ukama/ukama-nodes/products/units/amplifier/artworks/compliance_amplifier_node.pdf

# Scale 1: 1 Page 1/1:CMF Details

Antenna : Label F | Page size:A4 | Version:1.0

# 27-May-2021

# Date

SERIAL : 32019-08-12-2023-0225016

MAC ID : 07-45-B0-DC-06-40

## Model : FEMA-GSM900M-2W-GPS-V1.0-xx

Ukama Inc.

This device complies with part 15 of the FCC rules. Operation is subject to the following two conditions
1) This device may not cause harmful interference and 2) this device must accept any interference received, including that may cause undesired operation

### Made with in California

# logo

SERIAL : 32019-08-12-2023-0225016

MAC ID : 07-45-B0-DC-06-40

## Model : FEMA-GSM900M-2W-GPS-V1.0-xx

Ukama Inc.

This device complies with part 15 of the FCC rules. Operation is subject to the following two conditions
1) This device may not cause harmful interference and 2) this device must accept any interference received, including that may cause undesired operation

### Made with in California

# logo

34.43

18.03

# Background colour - White

# Text colour - Pantone Black C

# Colour - XXXX

# Graphics
