ukama/ukama-nodes/products/nodes/tower/artworks/compliance_tower_node.pdf

# Scale 1: 1 Page 1/1:CMF Details

Antenna : Label TN | Page size:A4 | Version:1.0

# 27-May-2021

# Date

# Background colour - White

# Text colour - Pantone Black C

# Colour - XXXX

80.00

11.00

This device complies with part 15 of the FCC rules. Operation is subject to the following two conditions 1) This device may not cause harmful interference and 2) this device must accept any interference received, including that may cause undesired operation

## Model : TowerNode-V1.0-xx

Ukama Inc.

### Made with in California

# logo

SERIAL : 12019-08-12-2023-0335007 | MAC ID : 07-45-B0-DC-06-41

This device complies with part 15 of the FCC rules. Operation is subject to the following two conditions 1) This device may not cause harmful interference and 2) this device must accept any interference received, including that may cause undesired operation

## Model : TowerNode-V1.0-xx

Ukama Inc.

### Made with in California

# logo

SERIAL : 12019-08-12-2023-0335007 | MAC ID : 07-45-B0-DC-06-41

# Graphics
