ukama/ukama-nodes/electronics/ctrl/bom/bom_controller.xlsx

Revised: Tuesday, September 01, 2020
FEMA-MP BOARD_V1_REV-B
Bill Of Materials September 18,2020 14:52:14
Item | Quantity | Reference | Part Number | Description | Manufacturer
1 | 2 | A9,A10 | SNT-100-BK-T-H | Open Top, Grip, Female Sockets, Shunts/Jumpers 2 POS | Samtec
2 | 1 | BT1 | CR-1220/HFN | BATTERY LITHIUM COIN 3V PC PINS | Panasonic - BSG
3 | 1 | CN1 | 112A-TAAR-R03 | MICROSD Connector | Attend Technology Inc
4 | 2 | C1,C2 | 101X43W474MV4E | CAP CER 0.47UF 100V X7R 1812 | Johanson Dielectrics Inc
6 | 17 | C4,C5,C15,C16,C17,C19,C39,C40,C44,C48,C49,C51,C53,C54,C55,C56,C3 | CC0402KRX7R8BB104 | CAP CER 0.1UF 25V 10% X7R 0402 | Yageo
7 | 2 | C6,C23 | NFM18PC225B1A3D | 2.2µF Feed Through Capacitor 10V 4A 10 mOhm 0603 (1608 Metric), 3 PC Pad | Murata Electronics North America
8 | 3 | C7,C22,C24 | 202R18W102KV4E | CAP CER 1000PF 2KV X7R 1206 | Johanson Dielectrics Inc.
9 | 1 | C8 | GRM155R72A102KA01D | CAP CER 1000PF 100V X7R 0402 | Murata Electronics
10 | 2 | C9,C31 | CL21B104KCFNNNE | CAP CER 0.1UF 100V X7R 0805 | Samsung Electro-Mechanics
11 | 2 | C10,C41 | CC1210KKX7R0BB105 | CAP CER 1UF 100V X7R 1210 | Yageo
12 | 1 | C11 | C0603C470K5RACAUTO | CAP CER 47PF 50V X7R 0603 | KEMET
13 | 1 | C12 | CC0603JRNPO9BN100 | CAP CER 10PF 50V C0G/NPO 0603 | Yageo
14 | 1 | C13 | C1206C224K4RAC7800 | CAP CER 0.22UF 16V X7R 1206 | KEMET
15 | 1 | C14 | UWX1C101MCL1GB | CAP ALUM 100UF 20% 16V SMD | Nichicon
16 | 4 | C18,C50,C52,C57 | GRM188R71A225KE15D | CAP CER 2.2UF 10V X7R 0603 | MURATA
17 | 14 | C20,C58,C59,C61,C62,C63,C64,C65,C66,C67,C68,C69,C70,C71 | GRM033C71C104KE14D | CAP CER 0.1UF 16V X7S 0201 | Murata Electronics North America
18 | 2 | C21,C60 | CL10B105MO8NNWC | CAP CER 1UF 16V X7R 0603 | Samsung Electro-Mechanics
19 | 1 | C25 | 885012206118 | CAP CER 0.047UF 100V X7R 0603 | Wurth Electronics Inc
20 | 4 | C26,C27,C28,C30 | CC0805KKX7RABB103 | CAP CER 10000PF 200V X7R 0805 | Yageo
21 | 2 | C29,C33 | EEE-2AA220UP | CAP ALUM 22UF 20% 100V SMD | Panasonic Electronic Components
22 | 1 | C32 | GCM188R72A103KA37D | CAP CER 10000PF 100V X7R 0603 | Murata Electronics North America
23 | 2 | C34,C45 | CL21B105KAFNNNE | CAP CER 1UF 25V X7R 0805 | Samsung Electro-Mechanics
24 | 2 | C35,C37 | CL10B104KB8NNNC | CAP CER 0.1UF 50V X7R 0603 | Samsung Electro-Mechanics
25 | 1 | C36 | EEE-FK1E220R | CAP ALUM 22UF 20% 25V SMD | Panasonic Electronic Components
26 | 1 | C38 | C0603C223K5RACTU | CAP CER 0.022UF 50V X7R 0603 | KEMET
27 | 1 | C42 | GCJ31CR72E473KXJ3L | CAP CER 0.047UF 250V X7R 1206 | Murata Electronics North America
28 | 1 | C43 | C4532X7R3D222K130KA | CAP CER 2200PF 2KV X7R 1812 | TDK Corporation
29 | 1 | C46 | CL10B153KB8NNNC | CAP CER 0.015UF 50V X7R 0603 | Samsung Electro-Mechanics
30 | 1 | C47 | 06035C101KAT2A | CAP CER 100PF 50V X7R 0603 | AVX Corporation
31 | 5 | D1,D2,D3,D4,D5 | PESD3V3X1BL,315 | TVS DIODE 3.3V SOD882 | Nexperia USA Inc.
32 | 3 | D6,D9,D23 | RB751S40T5G | DIODE SCHOTTKY 40V 30MA SOD523 | ON Semiconductor
33 | 2 | D7,D13 | SMAJ58A | TVS DIODE 58V 93.6V DO214AC | Littelfuse Inc.
34 | 5 | D8,D14,D15,D18,D20 | BAS16LT1G | DIODE GEN PURP 75V 200MA SOT23-3 | ON Semiconductor
35 | 1 | D10 | D5V0L2B3T-7 | TVS DIODE 5VWM 14VC SOT523 | Diodes Inc
36 | 1 | D11 | MMSZ5252BS-7-F | DIODE ZENER 24V 200MW SOD323 | Diodes Inc
37 | 1 | D12 | CD214A-B1100LF | DIODE SCHOTTKY 100V 1A SMA | Bourns Inc.
38 | 1 | D17 | TL431ACDBVR | IC VREF SHUNT ADJ SOT23-5 | Texas Instruments
39 | 1 | D19 | BAV99-TP | DIODE ARRAY GP 70V 200MA SOT23 | Micro Commercial Co
40 | 2 | D21,D22 | BZX84C12LT1G | DIODE ZENER 12V 250MW SOT23-3 | ON Semiconductor
41 | 2 | D10118,D10119 | RB751S40 | DIODE SCHOTTKY 40V 30MA SOD523F | ON Semiconductor
42 | 4 | FB1,FB2,FB3,FB4 | MI1206L501R-10 | FERRITE BEAD 500 OHM 1206 1LN | Laird-Signal Integrity Products
43 | 8 | F1,F2,F3,F4,F5,F6,F7,F8 | 1812L050/60MR | PTC RESETTBLE 60V 1.0A 2920 | Littelfuse Inc.
44 | 1 | JP1 | TSW-102-07-T-S | Header 1X2; TH | Samtec
45 | 1 | JP2 | 77315-118-02LF | CONN HEADER R/A 2POS 2.54MM | Amphenol ICC (FCI)
46 | 1 | J1 | FX23L-40-P-0.5SV10 | Connector | Hirose
47 | 1 | J2 | DX4R205JJAR1800 | USB - micro AB USB 2.0 Receptacle Connector 5 Position Surface Mount, Right Angle; Through Hole | JAE Electronics
48 | 1 | J3 | MRJ5384M1 | Jack Modular Connector 8p8c (RJ45, Ethernet) 90° Angle (Right) Unshielded | AMPHENOL
49 | 1 | J4 | 61300411121 | CONN HEADER 4 POS 2.54 | Wurth Electronics Inc.
50 | 1 | J5 | 67996-420HLF | CONN HEADER VERT 20POS 2.54MM | Amphenol FCI
51 | 4 | LED1 | 5977717507F | LED RGB DIFFUSED 0404 SMD | Dialight
52 | 2 | LED2,LED3 | LTST-C193TBKT-5A | LED BLUE CLEAR CHIP SMD | Lite-On Inc
53 | 1 | L1 | 744770122 | FIXED IND 22UH 4.1A 43 MOHM SMD | Wurth Electronics Inc.
54 | 1 | L2 | SRR0603-102KL | FIXED IND 1MH 100MA 14 OHM SMD | Bourns Inc.
55 | 1 | L3 | 744043003 | FIXED IND 3.3UH 2.15A 35 MOHM | Wurth Electronics Inc.
57 | 1 | M1 | SI4848ADY-T1-GE3 | MOSFET N-CH 150V 5.5A 8SOIC | Vishay Siliconix
58 | 1 | M2 | SI7852DP-T1-E3 | MOSFET N-CH 80V 7.6A PPAK SO-8 | Vishay Siliconix
59 | 1 | M3 | SI4850EY-T1-E3 | MOSFET N-CH 60V 6A 8-SOIC | Vishay Siliconix
60 | 2 | NR1,NR2 | EXB-28V104JX | RES ARRAY 4 RES 100K OHM 0804 | Panasonic Electronic Components
61 | 14 | Q1,Q2,Q3,Q4,Q7,Q10,Q12,Q13,Q14,Q16,Q18,Q21,Q54,Q55 | BSS138 | MOSFET N-CH 50V 220MA SOT-23 | ON Semiconductor
62 | 8 | Q5,Q6,Q8,Q9,Q15,Q17,Q19,Q20 | CSD18540Q5BT | MOSFET N-CH 60V 100A 8VSON | Texas Instruments
63 | 1 | Q11 | SI2325DS-T1-E3 | MOSFET P-CH 150V 0.53A SOT23-3 | Vishay Siliconix
64 | 2 | Q22,Q23 | MMBTA06LT1G | TRANS NPN 80V 0.5A SOT23 | ON Semiconductor
65 | 45 | R1,R6,R10,R12,R15,R16,R17,R18,R20,R24,R41,R42,R43,R44,R47,R54,R58,R59,R61,R62,R66,R68,R71,R75,R79,R85,R86,R87,R88,R92,R93,R94,R96,R98,R100,R102,R103,R105,R109,R124,R125,R133,R138,R139,R141 | RC0402JR-070RL | RES SMD 0 OHM JUMPER 1/16W 0402 | Yageo
66 | 4 | R2,R4,R5,R7 | RC1206FR-07487RL | RES SMD 487 OHM 1% 1/4W 1206 | Yageo
67 | 14 | R3,R8,R14,R19,R21,R26,R95,R97,R99,R101,R104,R107,R144,R145 | CRCW040210K0FKED | RES 10K OHM 1% 1/16W 0402 | VISHAY
68 | 2 | R9,R13 | RMCF0805JT120R | RES 120 OHM 1/8W 5% 0805 | Stackpole Electronics Inc
70 | 8 | R22,R25,R28,R30,R106,R108,R110,R111 | ERJ-P08J105V | RES SMD 1M OHM 5% 2/3W 1206 | Panasonic Electronic Components
71 | 1 | R23 | ERJ-2GEJ104X | RES 100K OHM 1/10W 5% 0402 SMD | Panasonic Electronic Components
72 | 4 | R27,R29,R31,R32 | RMCF0603JT75R0 | RES 75 OHM 5% 1/10W 0603 | Stackpole Electronics Inc
73 | 3 | R33,R114,R118 | RMCF0603ZT0R00 | RES 0 OHM JUMPER 1/10W 0603 | Stackpole Electronics Inc
74 | 1 | R34 | RMCF0805FT6K49 | RES 6.49K OHM 1% 1/8W 0805 | Stackpole Electronics Inc
75 | 1 | R35 | ESR03EZPF1001 | RES SMD 1K OHM 1% 1/4W 0603 | Rohm Semiconductor
76 | 1 | R36 | KRL1632E-M-R120-F-T5 | RES 0.12 OHM 1% 3/4W 1206 | Susumu
77 | 3 | R37,R38,R122 | RNCP0603FTD10K0 | RES 10K OHM 1% 1/8W 0603 | Stackpole Electronics Inc
78 | 1 | R39 | RMCF0603FT41K2 | RES 41.2K OHM 1% 1/10W 0603 | Stackpole Electronics Inc
79 | 1 | R40 | RC0603FR-0749R9L | RES SMD 49.9 OHM 1% 1/10W 0603 | Yageo
80 | 29 | R45,R46,R48,R50,R53,R55,R56,R57,R63,R64,R65,R73,R76,R77,R80,R82,R83,R84,R89,R130,R131,R134,R135,R136,R137,R10791,R10792,R10795,R11 | RC0402JR-0710KL | RES SMD 10K OHM 5% 1/16W 0402 | Yageo
81 | 4 | R49,R51,R52,R60 | CRCW0402100KFKED | RES SMD 100K OHM 1% 1/16W 0402 | Vishay Dale
82 | 1 | R67 | RC0402FR-0710KL | RES SMD 10K OHM 1% 1/16W 0402 | Yageo
83 | 2 | R69,R140 | RC0402FR-0722RL | RES SMD 22 OHM 1% 1/16W 0402 | Yageo
84 | 9 | R70,R72,R74,R78,R81,R90,R91,R10793,R10794 | RC0201FR-0710KL | RES SMD 10K OHM 1% 1/20W 0201 | Yageo
85 | 1 | R112 | RC0603FR-0769K8L | RES SMD 69.8K OHM 1% 1/10W 0603 | Yageo
86 | 1 | R113 | RC0603FR-0780K6L | RES SMD 80.6K OHM 1% 1/10W 0603 | Yageo
87 | 1 | R115 | RMCF0603FT63K4 | RES 63.4K OHM 1% 1/10W 0603 | Stackpole Electronics Inc
88 | 1 | R116 | RC0805FR-0763R4L | RES SMD 63.4 OHM 1% 1/8W 0805 | Yageo
89 | 1 | R117 | ERJ-3EKF2492V | RES SMD 24.9K OHM 1% 1/10W 0603 | Panasonic Electronic Components
90 | 1 | R119 | ESR03EZPF10R0 | RES SMD 10 OHM 1% 1/4W 0603 | Rohm Semiconductor
91 | 1 | R120 | RC0603FR-071K5L | RES SMD 1.5K OHM 1% 1/10W 0603 | Yageo
92 | 1 | R121 | RC0603FR-07348RL | RES SMD 348 OHM 1% 1/10W 0603 | Yageo
93 | 1 | R126 | ERJ-3EKF2491V | RES SMD 2.49K OHM 1% 1/10W 0603 | Panasonic Electronic Components
94 | 1 | R127 | MCT06030C1102FP500 | RES SMD 11K OHM 1% 1/8W 0603 | Vishay Beyschlag
95 | 2 | R128,R129 | ERJ-14YJ202U | RES SMD 2K OHM 5% 1/2W 1210 | Panasonic Electronic Components
96 | 1 | R132 | RC0805FR-072K87L | RES SMD 2.87K OHM 1% 1/8W 0805 | Yageo
97 | 2 | R142,R143 | RC0201JR-074K7L | RES SMD 4.7K OHM 5% 1/20W 0201 | Yageo
98 | 1 | S1 | TL1105JAF160Q | SWITCH TACTILE SPST-NO 0.05A 12V | E-Switch
99 | 1 | S2 | FSM4JSMATR | Tactile Switch SPST-NO Top Actuated Surface Mount | TE Connectivity ALCOSWITCH Switches
101 | 1 | T1 | ETH1-460LD | Transformers Audio & Signal ETH1 60W 4pairs PoE+ Magnetic Module | Coilcraft
102 | 1 | T2 | 750311320 | POWER OVER ETHERNET TRANSFORMER | Wurth Electronics Midcom
103 | 4 | U1,U2,U9,U10 | SEP0640Q38CB | SIDACTOR ETHERNET POE 64V 100A | Littelfuse Inc.
104 | 1 | U3 | SN74LVC1G97DBVR | IC CONFIG MULT-FUNC GATE SOT23-6 | Texas Instruments
105 | 1 | U4 | CAT24C256WI-GT3 | IC EEPROM 256KBIT 400KHZ 8SOIC | ON Semiconductor
106 | 1 | U5 | PRTR5V0U2X,215 | TVS DIODE 5.5VWM SOT143B | NXP Semiconductors
107 | 1 | U6 | PUSB3FR6Z | TVS DIODE 3.3V 3V 7XSON | Nexperia USA Inc
108 | 1 | U7 | EMMC08G-M325B53 | 8GB eMMC NAND Flash, 153 pin FBGA | Kingston
109 | 1 | U8 | LT4321IUF#PBF | IC OR CTRLR BRIDGE RECT 16QFN | Linear Technology
110 | 1 | U11 | TPS23754PWP | IC CTRLR POE PD IEEE 20-HTSSOP | Texas Instruments
111 | 2 | U12,U13 | TCLAMP2502N.TCT | TVS DIODE 2.5VWM 25VC 10SLP | Semtech Corporation
112 | 1 | U14 | FOD817AS | OPTOISOLATOR 5KV TRANSISTOR 4SMD | ON Semiconductor
113 | 1 | U15 | ATECC608A-SSHDA-T | IC AUTHENTICATION CHIP 8SOIC | ATMEL
114 | 1 | U16 | ADM6316DZ26ARJZ-R7 | IC SUPERVISOR WATCHDOG SOT23-5 | Analog Devices Inc
115 | 1 | U17 | ATSAMA5D27-SOM1 | SOM system on a module | MICROCHIP
116 | 1 | U18 | SE98ATP,547 | IC TEMP SENSOR DDR 8-HWSON | NXP Semiconductors
