ukama/ukama-nodes/electronics/trx/bom/trx_bom.xlsx

Item | Quantity | Reference | Part Number | Manufacturer | Description | Value
1 | 1 | CON1 | RECE.20279.001E.01 | Taoglas Limited | CONN UMC RCPT STR 50 OHM SMD | RECE.20279.001E.01
2 | 4 | C1,C2,C5,C19 | 202R18W102KV4E | Johanson Dielectrics Inc. | CAP CER 1000PF 2KV X7R 1206 | 1000PF
3 | 2 | C3,C4 | 101X43W474MV4E | Johanson Dielectrics Inc | CAP CER 0.47UF 100V X7R 1812 | 0.47UF
4 | 250 | C6,C8,C9,C21,C23,C25,C31,C32,C33,C34,C41,C57,C58,C59,C60,C61,C63,C64,C65,C66,C67,C68,C69,C70,C71,C72,C73,C74,C75,C81,C82,C83,C84,C85,C86,C87,C88,C89,C90,C92,C97,C98,C99,C100,C101,C102,C103,C104,C105,C107,C108,C109,C110,C112,C113,C114,C115,C116,C117,C118,C119,C120,C121,C122,C123,C124,C125,C126,C127,C128,C129,C130,C135,C136,C137,C138,C139,C142,C143,C148,C151,C153,C154,C157,C158,C163,C164,C165,C176,C181,C182,C183,C193,C194,C195,C196,C202,C204,C210,C214,C237,C240,C243,C244,C247,C248,C251,C254,C255,C256,C258,C259,C263,C264,C269,C271,C272,C274,C275,C277,C278,C279,C280,C281,C282,C283,C286,C287,C288,C289,C290,C291,C292,C294,C296,C297,C298,C299,C302,C303,C304,C305,C306,C307,C308,C309,C310,C311,C312,C313,C314,C315,C316,C317,C318,C324,C325,C326,C327,C328,C329,C330,C332,C333,C334,C335,C336,C337,C338,C339,C340,C341,C342,C343,C344,C346,C347,C348,C349,C350,C351,C352,C353,C354,C355,C356,C357,C358,C359,C360,C361,C362,C363,C364,C365,C366,C369,C373,C378,C388,C389,C390,C391,C392,C401,C402,C403,C404,C405,C406,C407,C408,C413,C415,C418,C420,C423,C424,C428,C429,C431,C432,C433,C434,C435,C438,C439,C441,C459,C462,C604,C605,C606,C619,C621,C622,C623,C625,C626,C627,C629,C631,C632,C633,C634,C638,C640,C641,C643,C644 | C1005X7R1E104K050BB | TDK Corporation | CAP CER 0.1UF 25V 10% X7R 0402 | 0.1uF
5 | 1 | C7 | 12065C105JAZ2A | AVX Corporation | CAP CER 1UF 50V X7R 1206 | 1uF
6 | 2 | C11,C190 | C1608X7S2A473K080AB | TDK Corporation | CAP CER 0.047UF 100V X7S 0603 | 0.047uF
7 | 2 | C12,C191 | CGA6N3X7R2A225K230AB | TDK Corporation | CAP CER 2.2UF 100V X7R 1210 | 2.2uF
8 | 4 | C13,C15,C16,C18 | CC0805KKX7RABB103 | Yageo | CAP CER 10000PF 200V X7R 0805 | 0.01uF
9 | 4 | C14,C51,C197,C198 | GRM1555C1H101JA01D | Murata Electronics North America | CAP CER 100PF 50V C0G/NP0 0402 | 100pf
10 | 2 | C17,C20 | 1812N222K202NX080T | Knowles Novacap | CAP CER 2200PF 2KV C0G/NP0 1812 | 2.2nF
11 | 5 | C2B1,C56,C186,C236,C242 | C3216X7R1E106K160AB | TDK | CAP CER 10UF 25V X7R 1206 | 10UF
12 | 1 | C22 | GRM1885C1H682JA01D | Murata Electronics | CAP CER 6800PF 50V C0G/NP0 0603 | 6.8nF
13 | 1 | C24 | 06033A681KAT2A | AVX | Multilayer Ceramic Capacitors MLCC - SMD/SMT 25V 330pF X7R 0603 10% | 330pF
14 | 71 | C26,C43,C76,C95,C96,C106,C111,C134,C141,C156,C159,C160,C166,C167,C168,C170,C177,C178,C179,C200,C238,C239,C241,C249,C252,C257,C260,C261,C262,C268,C270,C273,C293,C319,C320,C321,C322,C323,C331,C345,C367,C371,C380,C383,C393,C394,C396,C398,C410,C412,C414,C421,C430,C437,C440,C445,C446,C448,C449,C450,C461,C464,C601,C602,C603,C620,C624,C630,C635,C636,C639 | GRM188C81C106MA73D | Murata | CAP CER 10UF 16V X6S 0603 | 10uF
15 | 6 | C28,C52,C53,C54,C55,C400 | GRM31CR60J107ME39L | Murata Electronics | CAP CER 100UF 6.3V 20% X5R 1206 | 100uF/6.3V
16 | 7 | C29,C77,C203,C225,C226,C411,C417 | GRM188R61A226ME15D | Murata Electronics | CAP CER 22UF 10V 20% X5R 0603 | 22uF/10V
17 | 4 | C30,C94,C188,C436 | CC0402KRX7R7BB103 | Yageo | CAP CER 10000PF 16V 10% X7R 0402 | 10nF
18 | 12 | C35,C131,C132,C140,C144,C145,C171,C399,C409,C416,C456,C654 | CC0402KRX7R8BB102 | Yageo | CAP CER 1000PF 25V X7R 0402 | 1000pF
19 | 15 | C37,C152,C169,C172,C211,C276,C395,C397,C607,C618,C628,C642,C645,C646,C647 | CC0402KRX5R8BB105 | Yageo | CAP CER 1UF 25V X5R 0402 | 1uF
20 | 1 | C38 | EMLE160ADA101MF90G | United Chemi-Con | CAP ALUM 100UF 20% 16V SMD | 100uF
21 | 2 | C40,C222 | GRT155R61E474ME01D | Murata Electronics | CAP CER 0.47UF 25V X5R 0402 | 0.47uF
22 | 1 | C48 | TMK325ABJ476MM-P | Taiyo Yuden | CAP CER 47UF 25V X5R 1210 | 47uF/25V
23 | 1 | C49 | TPSE687K006R0045 | AVX Corporation | CAP TANT 680UF 10% 6.3V 2917 | 680uF
24 | 1 | C50 | GRM1555C1H821JA01J | Murata Electronics | CAP CER 820PF 50V C0G/NP0 0402 | 820pF
25 | 2 | C62,C79 | C0402C220J3GACTU | KEMET | CAP CER 22PF 25V C0G/NP0 0402 | 22pF
26 | 6 | C80,C91,C284,C455,C600,C637 | GRM1555C1H200JA01D | MURATA | CAP CER 20PF 50V 5% NPO 0402 | 20pF
27 | 1 | C93 | C0402C102K3RAC7867 | KEMET | CAP 1000PF 25V CERAMIC 0402 SMD | 1000pF
28 | 14 | C146,C147,C149,C150,C161,C162,C173,C174,C422,C425,C426,C427,C465,C466 | C0402C330J4RACAUTO | KEMET | CAP CER 0402 33PF 16V X7R 5% AUT | 33pF
29 | 1 | C155 | GRM0335C1H180JA01D | Murata Electronics North America | CAP CER 18PF 50V C0G/NP0 0201 | 18pF
30 | 1 | C175 | GRM0335C1H470JA01D | Yageo | CAP CER 47PF 50V C0G/NP0 0201 | 47pF
31 | 1 | C180 | GRM0335C1H220JA01D | Murata Electronics North America | CAP CER 22PF 50V NP0 0201 | 22pF
32 | 1 | C184 | CC0805KKX7R0BB224 | Yageo | CAP CER 0.22UF 100V X7R 0805 | 0.22uF
33 | 1 | C185 | 12061A332JAT2A | Yageo | CAP CER 3300PF 100V NPO 1206 | 33nF
34 | 1 | C189 | UUX2A220MNL6GS | Nichicon | CAP ALUM 22UF 20% 100V SMD | 22uF
35 | 1 | C201 | C0402C182J3GAC7867 | KEMET | CAP CER 1800PF 25V NP0 0402 | 1.8nF
36 | 3 | C206,C295,C652 | GRM033R61C104KE84D | Murata Electronics | CAP CER 0.1UF 16V X5R 0201 | 0.1uF
37 | 2 | C212,C213 | GRM32ER71E226ME15L | Murata Electronics | CAP CER 22UF 25V X7R 1210 | 22uF
38 | 1 | C215 | CC0402KRX7R7BB222 | Yageo | CAP CER 2200PF 16V X7R 0402 | 2.2nF
39 | 1 | C220 | GRM155R61E225ME15D | Murata Electronics | CAP CER 2.2UF 25V X5R 0402 | 2.2uF
40 | 1 | C231 | EEE-FK1A221XP | Panasonic | CAP TANT 680UF 4V 10% LOESR SMD | 220uF/10V
41 | 4 | C245,C246,C250,C253 | ECJ-0EB1C103K | Panasonic | CAP 10000PF 16V CERAMIC 0402 SMD | 10nF
42 | 1 | C266 | CC0402KRX7R8BB332 | YAGEO | CAP CER 3300PF 25V X7R 0402 | 3.3nF
43 | 1 | C368 | GRM155C81E105KE11D | Murata | CAP CER 1UF 25V X6S 0402 | 1UFX_16V
44 | 15 | C370,C372,C374,C375,C376,C377,C379,C381,C382,C384,C385,C386,C387,C650,C651 | GRM033R61E104ME14D | Murata Electronics North America | CAP CER 0.1UF 25V X5R 0201 | 0.1uF
45 | 1 | C419 | 04023A3R3CAT2A | AVX Corporation | CAP CER 3.3PF 25V NP0 0402 | 3.3pF
46 | 4 | C442,C443,C458,C463 | C0402C101K3RAC7867 | KEMET | CAP CER 100PF 25V X7R 0402 | 100pF
47 | 2 | C453,C454 | C0402C330J4RACAUTO | KEMET | CAP CER 0402 33PF 16V X7R 5% AUT | 33pF
48 | 8 | C608,C609,C610,C611,C612,C613,C614,C615 | GRM033R61E104ME14D | Murata Electronics North America | CAP CER 0.1UF 25V X5R 0201 | 100nF
49 | 2 | C616,C617 | GRM1555C1H270JA01D | Murata Electronics | CAP CER 27PF 50V C0G/NP0 0402 | 27pF
50 | 1 | C648 | CC0201KRX5R8BB103 | Yageo | CAP CER 10000PF 25V X5R 0201 | 0.01uF
51 | 1 | C649 | EMVE250ADA470MF55G | United Chemi-Con | CAP ALUM 47UF 20% 25V SMD | 47uF
52 | 5 | D1,D2,D3,D4,D5 | PESD3V3X1BL,315 | Nexperia USA Inc. | TVS DIODE 3.3V SOD882 | PESD3V3X1BL,315
53 | 1 | D6 | RB751S40T5G | ON Semiconductor | DIODE SCHOTTKY 40V 30MA SOD523 | RB751S40T5G
54 | 2 | D7,D19 | PTVS58VS1UR,115 | Nexperia USA Inc. | TVS DIODE 58V 93.6V CFP3 | PTVS58VS1UR
55 | 1 | D8 | ZR431F01TA | Diodes Incorporated | IC VREF SHUNT 20V 1% SOT23 | ZR431F01TA
56 | 1 | D9 | CMHZ4700 TR | Central Semiconductor | Zener Diodes 500mW 5% Tolerance | CMHZ4700
57 | 1 | D12 | PMEG6010ER,115 | Nexperia USA Inc. | DIODE SCHOTTKY 60V 1A SOD123W | PMEG6010ER
58 | 2 | D13,D21 | CMMSH1-100G TR PBFREE | Central Semiconductor Corp | DIODE SCHOTTKY 100V 1A SOD123F | CMMSH1-100
59 | 1 | D14 | RB751S40 | ON Semiconductor | DIODE SCHOTTKY 40V 30MA SOD523F | RB751S40
60 | 1 | D15 | ESD101B102ELSE6327XTSA1 | Infineon Technologies | TVS DIODE 5.5VWM 30VC TSSLP2-4 | ESD101B102ELSE6327XTSA1
61 | 1 | D16 | CMMSH1-40L | Central Semiconductor Corp | DIODE SCHOTTKY 40V 1A SOD123F | CMMSH1-40L
62 | 1 | D17 | BAV19WS-7-F | Diodes Incorporated | DIODE GEN PURP 100V 200MA SOD323 | BAV19WS
63 | 1 | D18 | BAT54WS-7-F | Diodes Incorporated | DIODE SCHOTTKY 30V 100MA SOD323 | BAT54WS
64 | 1 | D20 | MMSZ5252BS-7-F | Diodes Inc | DIODE ZENER 24V 200MW SOD323 | MMSZ5252BS-7-F
65 | 2 | D22,D26 | CMHZ5236B TR PBFREE | Central Semiconductor Corp | DIODE ZENER 7.5V 500MW SOD123 | CMHZ5236B
66 | 2 | D27,D29 | B530C-13-F | Diodes Incorporated | DIODE SCHOTTKY 30V 5A SMC | B530C-13-F
67 | 1 | D28 | SMBJ16CA | Littelfuse Inc | TVS DIODE 16VWM 26VC SMB | SMBJ16CA
68 | 2 | FB1,FB4 | BLM18PG121SN1D | Murata Electronics North America | FERRITE CHIP 120 OHM 2000MA 0603 | 120E / 2A
69 | 3 | FB18,FB19,FB20 | BLM18PG330SN1D | Murata Electronics North America | FERRITE BEAD 33 OHM 0603 1LN | 33E
70 | 8 | F1,F2,F3,F4,F6,F7,F8,F9 | 0ZCF0100AF2A | Bel Fuse Inc | PTC RESETTBLE 60V 1.0A 2920 | 0ZCF0100AF2A
71 | 1 | F5 | 0ZCM0010FF2G | Bel Fuse Inc. | PTC RESTTBLE 0.10A 15V CHIP 0603 | 0ZCM0010FF2G
72 | 1 | J1 | 2078430004 | Molex | HDR ASSBY FOR L1NK 250 - 1X4 CKT | HEADER 4
73 | 1 | J4 | FX23-120P-0.5SV15 | Hirose | CONN HDR 120POS SMD GOLD | FX23-120P_COM
74 | 1 | J5 | 77313-818-14LF | Amphenol ICC (FCI) | CONN HEADER VERT 14POS 2.54MM | HEADER 7X2
75 | 1 | J6 | 68002-102HLF | Amphenol ICC (FCI) | CONN HEADER VERT 2POS 2.54MM | HEADER 2X1-2.54MM
76 | 1 | J7 | 5000751517 | Molex | CONN RCPT USB2.0 MINI B VERT | MINI-USB TYPE A/B CON
77 | 7 | J9,J10,J11,J17,J18,J19,J20 | U.FL-R-SMT-1(10) | Hirose Electric Co Ltd | CONN U.FL RCPT STR 50 OHM SMD | U.FL
78 | 1 | J12 | MRJ5384M1 | AMPHENOL | Jack Modular Connector 8p8c (RJ45, Ethernet) 90° Angle (Right) Unshielded | RJ45_CONN
79 | 1 | J13 | FX23-60P-0.5SV15 | Hirose | CONN HDR 60POS SMD GOLD | FX23-60P_DEBUG
80 | 1 | J16 | FX23-40P-0.5SV15 | Hirose Connector | Board to Board & Mezzanine Connectors 0.5mm Pitch Header Strt 40P 15mm Hght | FX23L-40-P-0.5SV10
81 | 1 | J21 | 395011002 | Molex | TERM BLOCK HDR 2POS VERT 3.5MM | 395011002
82 | 4 | LED3,LED7,LED8,LED9 | LTST-C190TBKT | LITEON | LED Blue Clear 0603 | Blue
83 | 1 | LED4 | LTST-C190KRKT | LITEON | LED Red Clear 0603 | Red
84 | 7 | LED5,LED6,LED10,LED19,LED20,LED21,LED22 | LTST-C190KGKT | LITEON | LED Green Clear 2.1V 0603 | GREEN
85 | 1 | LED11 | 5977717507F | Dialight | LED RGB DIFFUSED 0404 SMD | 5977717507F
86 | 1 | L1 | B82464G4472M000 | EPCOS (TDK) | FIXED IND 4.7UH 4.9A 15 MOHM SMD | 4.7uH
87 | 1 | L2 | ACM1211-102-2PL-TL01 | TDK Corporation | CHOKE COMM MODE 1000 OHM 6A SMD | ACM1211-102-2PL-TL01
88 | 1 | L3 | SRP5030TA-1R5M | Bourns Inc. | FIXED IND 1.5UH 6A 25 MOHM SMD | 1.5uH/5A
89 | 1 | L7 | SPM6550T-2R2M-HZ | TDK Corporation | FIX IND 2.2UH 14.2A 10.67MOHM SM | 2.2uH
90 | 1 | L8 | MLC1260-401MLC | Coilcraft | Fixed Inductors Power Inductor 0.4 uH 20 % | 0.44uH
91 | 11 | L9,L11,L12,L13,L20,L21,L22,L23,L24,L25,L26 | FBMH1608HM600-T | Taiyo Yuden | BEAD FERRITE 60 OHM 3A 1608 SMD | 60OHM@100MHZ
92 | 1 | L10 | MDMK4040T1R5MF | Taiyo Yuden | FIXED IND 1.5UH 3.3A 65 MOHM SMD | 1.5uH/3A
93 | 15 | L14,L15,L28,L29,L30,L31,L32,L33,L38,L39,L41,L42,L43,L44,L46 | MPZ1005S121CT000 | TDK Corporation | FERRITE BEAD 120 OHM 0402 1LN | MPZ1005S121C
94 | 1 | L16 | LQW15AN8N7G00D | Murata Electronics North America | FIXED IND 8.7NH 540MA 140 MOHM | 8.7nH
95 | 1 | L17 | DO1608C-104MLB | Coilcraft | Fixed Inductors DO1608C Pwr Inductor 100 uH 20 % 0.5 A | 100uH
96 | 1 | L18 | XAL1010-822MED | Coilcraft | Fixed Inductors 8.2uH 20% 17.1A 12.9mOhms AEC-Q200 | 8.2uH
97 | 2 | L27,L40 | ECS-MPI2520R0-4R7-R | ECS Inc. | FIXED IND 4.7UH 1.4A 288MOHM SMD | 4.7uH/1.4A
98 | 4 | L34,L35,L36,L37 | MLK1005SR10JT000 | TDK | FIXED IND 100NH 100MA 2.2 OHM | 100nH
99 | 2 | L45,L47 | CZP2BFTTE800P | KOA Speer | Ferrite Beads 1206 80ohm 25% | 3.3nH
100 | 1 | L48 | LQH32PN100MN0L | Murata Electronics | FIXED IND 10UH 700MA 380 MOHM | 10uH/0.7A
101 | 1 | L50 | LQH2HPZ6R8MJRL | Murata Electronics | FIXED IND 6.8UH 1A 312 MOHM | 6.8uH/1A
102 | 2 | NR1,NR2 | EXB-38V104JV | Panasonic Electronic Components | RES ARRAY 4 RES 100K OHM 1206 | 100K
103 | 1 | Q1 | CSD17556Q5B | Texas Instruments | MOSFET N-CH 30V 8-VSON | CSD17556Q5B
104 | 1 | Q6 | TPN3300ANH,LQ | Toshiba Semiconductor and Storage | MOSFET N-CH 100V 9.4A 8TSON | TPN3300ANH,LQ
105 | 2 | Q11,Q30 | BSC123N08NS3GATMA1 | Infineon Technologies | MOSFET N-CH 80V 55A TDSON-8 | BSC123N08NS3 G
106 | 2 | Q12,Q29 | FMMT624TA | Diodes Incorporated | TRANS NPN 125V 1A SOT23-3 | FMMT624
107 | 1 | Q14 | FDMC2523P | ON Semiconductor | MOSFET P-CH 150V 3A MLP 3.3SQ | TPN3300ANH,LQ
108 | 1 | Q16 | BSC109N10NS3 G | Infineon Technologies | MOSFET N-CH 150V 50A TDSON-8 | BSC190N15NS3
109 | 8 | Q18,Q19,Q21,Q22,Q24,Q25,Q26,Q27 | CSD18540Q5BT | Texas Instruments | MOSFET N-CH 60V 100A 8VSON | CSD18540Q5BT
110 | 1 | Q23 | FMMT723TA | Diodes Incorporated | TRANS PNP 100V 1A SOT23-3 | FMMT723
111 | 3 | Q28,Q31,Q32 | MMBT3904LT1G | ON SEMICONDUCTOR | TRANS NPN 40V 0.2A SOT-23 | MMBT3904
112 | 1 | Q34 | CMPT3904 | Central Semiconductor | NPN, 0.2A, 40V | -
113 | 76 | R1,R11,R18,R43,R45,R51,R64,R76,R102,R110,R113,R115,R116,R127,R128,R129,R130,R134,R139,R141,R142,R145,R146,R147,R154,R159,R161,R162,R164,R167,R168,R170,R174,R178,R181,R182,R230,R245,R279,R292,R303,R316,R318,R319,R330,R340,R347,R350,R351,R367,R381,R382,R391,R426,R427,R433,R435,R437,R447,R450,R474,R475,R620,R624,R637,R652,R656,R658,R659,R679,R680,R681,R691,R692,R693,R707 | RC0402JR-0710KL | Yageo | RES SMD 10K OHM 5% 1/16W 0402 | 10K
114 | 18 | R2,R3,R205,R206,R207,R208,R209,R212,R304,R305,R306,R307,R308,R481,R483,R484,R485,R486 | RC0402JR-070RL | Yageo | RES SMD 0 OHM JUMPER 1/16W 0402 | 0Ohm
115 | 6 | R4,R22,R41,R632,R633,R683 | RC0402JR-070RL | Yageo | RES SMD 0 OHM JUMPER 1/16W 0402 | 0 OHM
116 | 75 | R7,R9,R10,R2N1,R2N2,R58,R108,R120,R121,R160,R166,R180,R184,R199,R201,R229,R233,R234,R239,R241,R250,R256,R259,R262,R263,R267,R288,R300,R370,R372,R378,R384,R385,R395,R396,R398,R399,R401,R409,R410,R413,R414,R439,R444,R445,R465,R466,R468,R469,R470,R471,R472,R473,R482,R616,R622,R623,R627,R628,R629,R630,R631,R638,R661,R675,R677,R682,R711,R712,R714,R715,R720,R721,R733,R735 | RC0402JR-070RL | Yageo | RES SMD 0 OHM JUMPER 1/16W 0402 | 0
117 | 1 | R27 | RC0805FR-0752R3L | Yageo | RES SMD 52.3 OHM 1% 1/8W 0805 | 52.3
118 | 1 | R29 | ERJ-2RKF1180X | Panasonic Electronic Components | RES SMD 118 OHM 1% 1/10W 0402 | 118
119 | 1 | R33 | ESR10EZPF20R0 | Rohm Semiconductor | RES SMD 20 OHM 1% 0.4W 0805 | 20
120 | 1 | R35 | ERJ-6GEYJ8R2V | Panasonic Electronic Components | RES SMD 8.2 OHM 5% 1/8W 0805 | 8.2
121 | 8 | R38,R42,R47,R49,R269,R272,R274,R276 | ERJ-P08J105V | Panasonic Electronic Components | RES SMD 1M OHM 5% 2/3W 1206 | 1M
122 | 2 | R40,R689 | CRCW0402100KFKED | Vishay Dale | RES SMD 100K OHM 1% 1/16W 0402 | 100K
123 | 1 | R44 | WK73R1JTTD7500F | KOA Speer Electronics, Inc. | RES 750 OHM 1% 1/2W 0603 | 750
124 | 1 | R52 | RC0402FR-07820RL | Yageo | RES SMD 820 OHM 1% 1/16W 0402 | 820
125 | 1 | R53 | WK73R2ATTD10R0F | KOA Speer Electronics, Inc. | RES 10 OHM 1% 1W 0805 | 10
126 | 1 | R54 | RC0402FR-0713KL | Yageo | RES SMD 13K OHM 1% 1/16W 0402 | 13K
127 | 1 | R55 | RC0402FR-0738K3L | Yageo | RES SMD 38.3K OHM 1% 1/16W 0402 | 38.3K
128 | 1 | R56 | RC0402JR-0710KL | Yageo | RES SMD 10K OHM 5% 1/16W 0402 | 10.0K
129 | 15 | R57,R60,R66,R169,R171,R173,R176,R283,R285,R357,R364,R688,R690,R722,R723 | RC0402JR-070RL | Yageo | RES SMD 0 OHM JUMPER 1/16W 0402 | 0E
130 | 1 | R61 | RC0402FR-0768KL | Yageo | RES 68K OHM 1/16W 1% 0402 SMD | 68K/1%
131 | 3 | R62,R293,R388 | PFR05S-153-FNH | Delta Electronics/Cyntec | RES SMD 15 KOHM 1% 1/16W 0402 | 15K/1%
132 | 2 | R63,R138 | CRGCQ0402F180K | TE Connectivity Passive Product | CRGCQ 0402 180K 1% | 180K/1%
133 | 1 | R65 | RCL12250000Z0EG | Yageo | RES SMD 0 OHM 2W 2512 WIDE | 0 E
134 | 5 | R67,R71,R112,R149,R231 | RC2512JK-070RL | Yageo | RES SMD 0 OHM JUMPER 1W 2512 | 0 E
135 | 1 | R68 | RMCF0402FT3K01 | Stackpole Electronics Inc | RES 3.01K OHM 1% 1/16W 0402 | 3.01K/1%
136 | 1 | R69 | RMCF0402FT8K45 | Stackpole Electronics Inc | RES 8.45K OHM 1% 1/16W 0402 | 8.45K/1%
137 | 6 | R70,R136,R232,R238,R375,R476 | RC0402FR-0710KL | Yageo | RES 10.0K OHM 1/16W 1% 0402 SMD | 10K/1%
138 | 1 | R72 | RCL12250000Z0EG | Vishay Dale | RES SMD 0 OHM 2W 2512 WIDE | 0 E
139 | 1 | R73 | RC0402FR-07187KL | Yageo | RES 187K OHM 1/16W 1% 0402 SMD | 187K/1%
140 | 1 | R74 | RC0402FR-0724K9L | Yageo | RES SMD 24.9K OHM 1% 1/16W 0402 | 24.9K/1%
141 | 1 | R75 | RC0402FR-07100KL | Yageo | RES SMD 100K OHM 1% 1/16W 0402 | 100K/1%
142 | 1 | R78 | RC0402JR-07100KL | Yageo | RES 100K OHM 1/16W 5% 0402 SMD | 100K
143 | 1 | R87 | RC0402JR-07200KL | Yageo | RES 200K OHM 1/16W 5% 0402 SMD | 200K
144 | 1 | R90 | ERJ-P6WF2201V | Panasonic Electronic Components | RES SMD 2.2K OHM 1% 1/2W 0805 | 2.2K
145 | 27 | R95,R97,R101,R106,R152,R153,R185,R194,R196,R197,R198,R236,R325,R329,R333,R335,R337,R346,R353,R355,R387,R389,R392,R393,R415,R724,R725 | RC0402JR-071KL | Yageo | RES 1.0K OHM 1/16W 5% 0402 SMD | 1K
146 | 2 | R99,R282 | ERJ-2RKF5101X | Panasonic Electronic Components | RES SMD 5.1K OHM 1% 1/10W 0402 | 5.1K
147 | 6 | R103,R107,R109,R111,R114,R203 | RC0402JR-07330RL | Yageo | RES 330 OHM 1/16W 5% 0402 SMD | 330
148 | 1 | R104 | ERJ-8BQF7R5V | Panasonic Electronic Components | RES SMD 7.5 OHM 1% 1/2W 1206 | 7.5
149 | 1 | R117 | RC0402FR-07475RL | Yageo | RES 475 OHM 1/16W 1% 0402 SMD | 475/1%
150 | 9 | R124,R175,R183,R296,R298,R328,R331,R336,R338 | RC0402JR-0733RL | Yageo | RES 33 OHM 1/16W 5% 0402 SMD | 33
151 | 7 | R126,R151,R163,R189,R190,R200,R214 | RC0402FR-07240RL | Yageo | RES SMD 240 OHM 1% 1/16W 0402SMD | 240/1%
152 | 1 | R135 | ERJ-2RKF6341X | Panasonic | RES 6.34K OHM 1/16W 1% 0402 SMD | 6.34K/1%
153 | 1 | R137 | ERJ-2RKF7681X | Panasonic | RES 7.68K OHM 1/16W 1% 0402 SMD | 7.68K/1%
154 | 6 | R172,R177,R422,R423,R451,R467 | ERJ-2GE0R00X | Panasonic Electronic Components | RES SMD 0 OHM JUMPER 1/10W 0402 | 0E
155 | 17 | R179,R188,R191,R192,R193,R195,R295,R380,R390,R431,R432,R436,R464,R700,R702,R703,R706 | RC0402JR-074K7L | Yageo | RES 4.7K OHM 1/16W 5% 0402 SMD | 4.7K
156 | 1 | R211 | RC0402JR-07300RL | Yageo | RES SMD 300 OHM 5% 1/16W 0402 | 300
157 | 27 | R216,R217,R218,R219,R220,R221,R222,R223,R224,R225,R226,R227,R228,R441,R442,R452,R453,R454,R455,R456,R457,R458,R459,R460,R461,R462,R463 | RC0402FR-0736RL | Yageo | RES 36.0 OHM 1/16W 1% 0402 SMD | 36/1%
158 | 1 | R235 | RC0402FR-0714K3L | Yageo | RES SMD 14.3K OHM 1% 1/16W 0402 | 14.3K/1%
159 | 2 | R237,R438 | RC0402FR-071RL | Yageo | RES SMD 1 OHM 1% 1/16W 0402 | 1/1%
160 | 7 | R240,R327,R332,R334,R342,R344,R354 | RC0402FR-0749R9L | Yageo | RES 49.9 OHM 1/16W 1% 0402 SMD | 49.9/1%
161 | 1 | R248 | WFMA2010R0150FEA | Vishay Dale | RES 0.015 OHM 2.0 W 1% 2010 SMD | 15m
162 | 1 | R251 | RC0402FR-0729K4L | Yageo | RES SMD 29.4K OHM 1% 1/16W 0402 | 29.4K
163 | 1 | R252 | RC0402FR-07107KL | Yageo | RES SMD 107K OHM 1% 1/16W 0402 | 107K
164 | 1 | R255 | RC0402FR-07100RL | Yageo | RES SMD 100 OHM 1% 1/16W 0402 | 100
165 | 1 | R258 | AC0603FR-073K3L | Yageo | RES SMD 3.3K OHM 1% 1/10W 0603 | 3.3K
166 | 4 | R268,R273,R275,R277 | CRCW060375R0JNEA | Vishay Dale | RES SMD 75 OHM 5% 1/10W 0603 | 75E
167 | 1 | R271 | ERJ-3EKF4701V | Panasonic Electronic Components | RES SMD 4.7K OHM 1% 1/10W 0603 | 4.7k
168 | 1 | R278 | ERJ-2GE0R00X | Panasonic Electronic Components | RES 0.0 OHM 1/10W JUMP 0402 SMD | 0
169 | 2 | R280,R729 | RC0402FR-0720KL | Yageo | RES SMD 20K OHM 1% 1/16W 0402 | 20K
170 | 1 | R284 | RC0402FR-071KP | Yageo | RES SMD 1K OHM 5% 1/16W 0402 | 1K
171 | 1 | R286 | RC0402FR-0714KL | Yageo | RES 14.0K OHM 1/16W 1% 0402 SMD | 14K/1%
172 | 2 | R289,R291 | RC0805FR-072R05L | Yageo | RES 2.05 OHM 1/8W 1% 0805 SMD | 2.05/1%
173 | 1 | R294 | RC0402FR-0717K4L | Yageo | RES SMD 17.4K OHM 1% 1/16W 0402 | 17.4K/1%
174 | 2 | R313,R424 | RC0402FR-07100RL | Yageo | RES 100 OHM 1/16W 1% 0402 SMD | 100/1%
175 | 12 | R317,R324,R356,R366,R405,R408,R417,R418,R421,R440,R443,R660 | RC0402JR-0722RL | Yageo | RES 22 OHM 1/16W 5% 0402 SMD | 22
176 | 2 | R339,R343 | RC0402FR-072K37L | Yageo | RES 2.37K OHM 1/16W 1% 0402 SMD | 2.37K/1%
177 | 1 | R345 | RC0402FR-0737R4L | Yageo | RES 37.4 OHM 1/16W 1% 0402 SMD | 37.4/1%
178 | 2 | R406,R407 | RC0402FR-071KL | Yageo | RES 1.00K OHM 1/16W 1% 0402 SMD | 1K/1%
179 | 2 | R419,R420 | RC0201JR-074K7L | Yageo | RES SMD 4.7K OHM 5% 1/20W 0201 | 4.7K
180 | 1 | R446 | ERJ-2GE0R00X | Panasonic Electronic Components | RES 0.0 OHM 1/10W JUMP 0402 SMD | 0Ohm
181 | 1 | R448 | RC0402FR-0743KL | Yageo | RES SMD 43K OHM 1% 1/16W 0402 | 43K/1%
182 | 1 | R449 | AC0402FR-0727KL | Yageo | RES SMD 27K OHM 1% 1/16W 0402 | 27K/1%
183 | 1 | R477 | RC0402FR-0720KL | Yageo | RES 20K OHM 1/16W 1% 0402 SMD | 20K/1%
184 | 1 | R545 | ERA-2AEB4532X | Panasonic Electronic Components | RES SMD 45.3KOHM 0.1% 1/16W 0402 | 45K/1%
185 | 1 | R546 | CRT0402-FZ-3002GLF | Bourns | Thin Film Resistors ResThinFilm 0402 30k 1% 63mW TC50 | 30K/1%
186 | 2 | R621,R716 | RC0402JR-0710KL | Yageo | RES SMD 10K OHM 5% 1/16W 0402 | 1K
187 | 4 | R634,R635,R636,R655 | ERJ-2GE0R00X | Panasonic Electronic Components | RES SMD 0 OHM JUMPER 1/10W 0402 | 0ohm
188 | 1 | R639 | RC0402FR-074K99L | Yageo | RES SMD 4.99K OHM 1% 1/16W 0402 | 4.99K 1%
189 | 1 | R640 | RT0402FRE0736KL | YAGEO | RES SMD 36K OHM 1% 1/16W 0402 | 36K/1%
190 | 1 | R641 | RC0402FR-0739K2L | Yageo | RES 39.2K OHM 1% 1/16W 0402 | 39.2K/1%
191 | 1 | R642 | AC0201FR-0747KL | Yageo | RES SMD 47K OHM 1% 1/20W 0201 | 47K
192 | 2 | R643,R645 | ERJ-1GNF4322C | Panasonic Electronic Components | RES SMD 43.2K OHM 1% 1/20W 0201 | 43.2K
193 | 1 | R644 | ERJ-1GNF6491C | Panasonic Electronic Components | RES SMD 6.49K OHM 1% 1/20W 0201 | 6.49K
194 | 1 | R646 | ERJ-1GNF3651C | Panasonic Electronic Components | RES SMD 3.65K OHM 1% 1/20W 0201 | 3.65K
195 | 2 | R647,R648 | RMCF0201FT10K0 | Stackpole Electronics Inc | RES 10K OHM 1% 1/20W 0201 | 10K
196 | 1 | R649 | ERJ-1GNF1501C | Panasonic Electronic Components | RES SMD 1.5K OHM 1% 1/20W 0201 | 1.5K
197 | 1 | R650 | WSL12064L000FEA | Vishay Dale | RES 0.004 OHM 1% 1/4W 1206 | 0.004
198 | 3 | R651,R653,R654 | RC0402JR-070RL | Yageo | RES SMD 0.0OHM JUMPER 1/16W 0402 | 0E
199 | 8 | R662,R663,R665,R667,R668,R670,R671,R672 | ERA-2AEB361X | Panasonic Electronic Components | RES SMD 360 OHM 0.1% 1/16W 0402 | 360E
200 | 4 | R664,R666,R669,R673 | RC0402JR-07560RL | Yageo | RES SMD 560 OHM 5% 1/16W 0402 | 560E
201 | 2 | R708,R709 | RK73H1ETTP1500F | KOA Speer Electronics, Inc. | RES 150 OHM 1% 1/10W 0402 | 150E
202 | 1 | R730 | RC0402FR-075KL | Yageo | RES SMD 5K OHM 1% 1/10W 0603 | 5K
203 | 1 | R731 | RC0402FR-0718KL | Yageo | RES 18K OHM 1% 1/16W 0402 | 18K
204 | 1 | SW1 | TL3305BF160QG | TE Connectivity ALCOSWITCH Switches | SWITCH TACTILE SPST-NO 0.05A 24V | Tact Switch
205 | 1 | SW10 | CL-SB-12A-01T | Copal Electronics Inc. | Slide Switch SPDT Surface Mount | CL-SB-12A-01
206 | 1 | S1 | TL1105JAF160Q | E-Switch | SWITCH TACTILE SPST-NO 0.05A 12V | TL1105JAF160Q
207 | 1 | T1 | EPC3577G-LF | PCA Electronics | Transformer | EPC3577G-LF
208 | 1 | T2 | ETH1-460LD | Coilcraft | Transformers Audio & Signal ETH1 60W 4pairs PoE+ Magnetic Module | ETH1-460LD
209 | 1 | U1 | CNF7130-1000BG772-G | Cavium | Cavium OCTEON Fusion CNF7130 | CNF7130-1000BG772-G
210 | 1 | U3 | AD9363BBCZ | Analog Device | RF Transceiver | AD9363ABCZ
211 | 1 | U4 | TPS54519RTET | Texas Instruments | IC REG BUCK ADJUSTABLE 5A 16WQFN | TPS54519
212 | 1 | U5 | SN74LVC1G08DCKR | Texas Instruments | IC GATE AND 1CH 2-INP SC-70-5 | SN74LVC1G08DCKR
213 | 5 | U6,U18,U32,U33,U57 | SN74LVC1G17QDCKRQ1 | Texas Instruments | IC BUF NON-INVERT 5.5V SC70-5 | 74LVC1G17SE-7
214 | 1 | U7 | TPS53353DQPT | Texas Instruments | IC REG BUCK ADJUSTABLE 20A 22SON | TPS53353DQPT
215 | 1 | U8 | LM73606RNPR | Texas Instruments | IC REG BUCK ADJUSTABLE 6A 30WQFN | LM73606RNPR
216 | 4 | U9,U36,U47,U48 | SEP0640Q38CB | Littelfuse Inc. | SIDACTOR ETHERNET POE 64V 100A | SEP0640Q38CB
217 | 1 | U10 | MCP1316MT-29KE/OT | Microchip Technology | IC SUPERVISOR 2.9V SOT23-5 | MCP1316
218 | 5 | U11,U15,U23,U30,U35 | IS43TR16256AL-15HBLI | ISSI | DRAM 4G, 1.35V, 1333Mhz DDR3L SDAM | DDR3_128/256Mb*16
219 | 1 | U12 | 625L3C050M00000 | CTS-Frequency Controls | XTAL OSC XO 50.0000MHZ CMOS SMD | Oscillator 50Mhz
220 | 1 | U13 | PI6C557-03BLE | Diodes Incorporated | IC CLOCK GENERATOR 16TSSOP | PI6C557-03BLE/5V41235PGGI8
221 | 1 | U14 | TPS54319RTET | Texas Instruments | IC REG BUCK ADJUSTABLE 3A 16WQFN | TPS54319
222 | 3 | U16,U17,U34 | 74LVC1G08SE-7 | Diodes Incorporated | IC GATE AND 1CH 2-INP SOT353 | 74LVC1G08SE-7
223 | 1 | U19 | AT24C64D-XHM-B | Microchip Technology | IC EEPROM 64KBIT 1MHZ 8TSSOP | AT24C64D-XHM-B
224 | 1 | U21 | SX1509BIULTRT | Semtech | IC GPIO EXPANDER I2C 16CH 28QFN | SX1509B
225 | 1 | U22 | 74ALVT16373DGG,118 | Nexperia USA Inc. | IC TRANSP LATCH 16BIT D 48TSSOP | 74ALVT16373DGG
226 | 1 | U24 | DMC2038LVT-7 | Diodes Incorporated | MOSFET N/P-CH 20V TSOT26 | DMC2038LVT-7
227 | 1 | U25 | TXB0101DBVR | TI | 1 bit bidirectional voltage level translator,SOT23-6 | TXB0101DBVR
228 | 1 | U26 | FT230XQ-R | FTDI, Future Technology Devices International Ltd | IC USB SERIAL BASIC UART 16QFN | FT230XQ
229 | 1 | U27 | SN74CBTD3861PWR | TI | IC 10-BIT FET BUS SW 24-TSSOP | SN74CBTD3861PWR
230 | 1 | U28 | TMP464AIRGTR | Texas Instruments | Temperature Sensor | TMP464AIRGTR
231 | 1 | U29 | EMMC16G-M525-B53 | Kingston | 16GB eMMC NAND with JEDEC/MMC standard version 4.51-compliant | EMMC16G-M525-B53
232 | 1 | U31 | ADUM1201ARZ-RL7 | Analog Devices Inc. | DGTL ISO 2.5KV GEN PURP 8SOIC | ADUM1201ARZ/ISO7221
233 | 1 | U37 | NEO-M8N | uBLOX | GPS Module | NEO-M8
234 | 1 | U38 | U7769LF | Rakon | IC OCXO mercury ultra low noise 30.72MHZ | OCXO-30.72Mhz/U7769LF
235 | 5 | U39,U40,U43,U66,U67 | TCM1-63AX+ | Mini Circuits | Surface mount RF Transdormer 50ohm 10~6 GHZ | TCM1-63AX+
236 | 1 | U41 | NJG1143UA2-TE1 | NJR | RF Amplifier Low Noise Amp GaAs MMIC 1.5V to 3.6V | NJG1143UA2
237 | 1 | U42 | TPS51200DRCR | Texas Instruments | IC REG CONV DDR 1OUT 10VSON | TPS51200DRCT
238 | 1 | U44 | DAC8571IDGKR | TI | IC DAC 16BIT I2C V-OUT LP 8VSSOP | DAC8571IDGKR
239 | 1 | U45 | LT4295IUFD#PBF | Linear Technology | IEEE 802.3bt PD Interface with Forward/Flyback Controller | LT4295IUFD
240 | 1 | U46 | LT4321IUF | Linear Technology | IC OR CTRLR BRIDGE RECT 16QFN | LT4321IUF
241 | 3 | U49,U50,U51 | MOC207M | ON Semiconductor | OPTOISO 2.5KV TRANS W/BASE 8SOIC | MOC207M
242 | 4 | U52,U53,U54,U55 | TCLAMP2502N.TCT | Semtech Corporation | TVS DIODE 2.5VWM 25VC 10SLP | TCLAMP2502NTCT
243 | 2 | U58,U59 | NVT2002DP,118 | NXP Semiconductors | IC TRANSLATOR DUAL 8TSSOP | NVT2002DP
244 | 1 | U62 | CAT24C256WI-GT3 | ON Semiconductor | IC EEPROM 256KBIT 400KHZ 8SOIC | CAT24C256WI-GT3
245 | 4 | U63,U69,U83,U245 | AP3418KTR-G1 | Diodes Incorporated | IC REG BUCK ADJ 1.5A SOT23-5 | AP3418KTR-G1
246 | 1 | U64 | MT28EW01GABA1HJS-0SIT TR | Micron Technology Inc. | IC FLASH 1G PARALLEL 56TSOP | JS28F512M29EWH
247 | 1 | U65 | ADP1755ACPZ-R7 | Analog Device | IC REG LIN POS ADJ 1.2A 16LFCSP | ADP1755ACPZ-R7
248 | 1 | U68 | 74FST3257DTR2G | ON Semiconductor | IC MUX/DEMUX QUAD 2:1 16TSSOP | 74FST3257DTR2G
249 | 2 | U70,U71 | PGA102 | MINI CIRCUITS | SMT Low Noise Amplifier, 50 - 6000 MHz, 50? | PGA102
250 | 1 | U87 | TCA9543APWR | Texas Instruments | IC I2C SW 2CH W/RESET 14TSSOP | TCA9543A
251 | 1 | U90 | IP4252CZ8-4-TTL,13 | NXP Semiconductors | FILTER RC(PI) 40 OHM/12PF SMD | IP4252CZ8-4-TTL,13
252 | 1 | U242 | LP3943ISQ/NOPB | Texas Instruments | IC LED DRIVER PS DIM 25MA 24WQFN | LP3943
253 | 1 | U243 | 88E6341_QFN88 | Marvell | ETHERNET SWITCH | 88E6341_QFN88
254 | 1 | U246 | LM25066APSQE/NOPB | Texas Instruments | IC CTLR PM HOTSWAP 24WQFN | LM25066
255 | 1 | U248 | SN74AVC1T45DRLR | Texas Instruments | IC TRNSLTR BIDIRECTIONAL 6SOT | SN74AVC1T45DRLR
256 | 1 | U250 | CAT24C64WI-GT3 | ON Semiconductor | IC EEPROM 64KBIT 400KHZ 8SOIC | CAT24C64WI-GT3
257 | 1 | Y2 | 8Z-12.000MAHQ-T | TXC CORPORATION | CRYSTAL 12.0000MHZ 10PF SMD | 12MHZ
258 | 2 | Y3,Y4 | ABM10AIG-25.000MHZ-4Z-T3 | Abracon LLC | CRYSTAL 25MHZ 10PF SMD | 25MHz
259 | 1 | Z1 | 5.0SMDJ15A | Littelfuse Inc. | TVS DIODE 15V 24.4V DO214AB | 5.0SMDJ15A
