ukama/ukama-nodes/electronics/fe/30dBm/B40/bom/FEMA_B40_BOM.xlsm

Item | Manufacturer | Part Number | Description | Reference | Quantity | Value
1 | Taoglas Limited | RECE.20279.001E.01 | CONN UMC RCPT STR 50 OHM SMD | CON2,CON4 | 2 | RECE.20279.001E.01
2 | Taoglas Limited | RECE.20279.001E.01 | CONN UMC RCPT STR 50 OHM SMD | CON3 | 1 | RECE.20279.001E.01
3 | Samsung Electro-Mechanics | CL31X226KAHN3NE | CAP CER 22UF 25V X6S 1206 | C11,C15,C16,C23,C26 | 5 | 22uF
4 | Murata Electronics | GRM188R71H104KA93D | CAP CER 0.1UF 50V X7R 0603 | C13,C21,C22,C27 | 4 | 0.1uF
5 | Murata Electronics | GRM155R71C104KA88D | CAP CER 0.1UF 16V X7R 0402 | C14,C17,C53,C60,C68,C128,C151 | 7 | 0.1uF
6 | Murata Electronics | GRM188C81E475KE11D | CAP CER 4.7UF 25V X6S 0603 | C18,C41,C42 | 3 | 4.7uF
7 | Murata Electronics | GRM188R71H153KA01D | CAP CER 0.015UF 50V X7R 0603 | C19,C52 | 2 | 15000pF
8 | Murata Electronics | GRM1555C1H101GA01D | CAP CER 100PF 50V C0G/NP0 0402 | C20,C54,C55,C63,C64,C122,C123 | 7 | 100pF
9 | Murata Electronics | GRM155R71H152KA01D | CAP CER 1500PF 50V X7R 0402 | C28 | 1 | 1500pF
10 | Murata Electronics | GRM32ER71H106KA12L | CAP CER 10UF 50V X7R 1210 | C29,C30,C31,C32,C33,C34,C35,C36,C37,C38,C39,C40,C45,C46,C47,C48,C160,C161,C162 | 19 | 10UF
11 | Murata | CGA3E3X7R1H224K080AE | CAP CER 0.22UF 50V X7R 0603 | C43 | 1 | 0.22uF
12 | Murata Electronics | GRM155R71C104KA88D | CAP CER 0.1UF 16V X7R 0402 | C44,C49,C89,C91,C166,C167,C168,C169,C178,C179,C249,C250,C257 | 13 | 0.1uF
13 | Murata Electronics | GRM1555C1H221GA01D | CAP CER 220PF 50V C0G/NP0 0402 | C50 | 1 | 220pF
14 | Murata Electronics | GRM155R71E473KA88D | CAP CER 0.047UF 25V X7R 0402 | C51 | 1 | 47000pF
15 | Murata | GRM155C81E105KE11 | Multilayer Ceramic Capacitors MLCC - SMD/SMT 25V 100pF X7R 0402 5% Tol | C56,C62,C90,C101,C121,C131 | 6 | 1uF
16 | Murata Electronics | GCM1885C2A101FA16D | Multilayer Ceramic Capacitors MLCC - SMD/SMT 0603 100pF 100volts X8G 1% | C57,C58,C59,C61,C65,C66,C67,C69,C77,C78,C80,C81,C104,C109,C124,C125,C126,C127,C278 | 19 | 100pF
17 | TDK Corporation | C2012X5R1V106K085AC | CAP CER 10UF 35V X5R 0805 | C70,C72,C86,C87 | 4 | 10UF
18 | Murata Electronics | GQM1875C2E9R1CB12D | CAP CER 9.1PF 250V NP0 0603 | C71,C88 | 2 | 9.1pF
19 | AVX Corporation | 06033D105KAT2A | CAP CER 1UF 25V X5R 0603 | C73,C74,C83,C85 | 4 | 1UF
20 | Murata Electronics | GQM1875C2E1R8CB12D | CAP CER 1.8PF 250V NP0 0603 | C75,C84 | 2 | 1.8pF
21 | Murata Electronics | GQM1875C2E1R6BB12D | CAP CER 1.6PF 250V C0G/NP0 0603 | C76 | 1 | 1.6pF
22 | KEMET | CBR06C508B5GAC | Multilayer Ceramic Capacitors MLCC - SMD/SMT 50V 0.5pF C0G 0603 0.1pF | C82 | 1 | 0.5pF
23 | Murata Electronics | GRM155R71H102KA01D | CAP CER 1000PF 50V X7R 0402 | C129,C130,C132,C135,C145,C146,C147,C149,C150,C152,C153,C154,C156,C158,C159 | 15 | 1000pF
24 | Murata Electronics | GJM1555C1HR50BB01D | CAP CER 0.5PF 50V C0G/NP0 0402 | C133 | 1 | 0.5pF
25 | Murata Electronics | GJM1555C1HR50BB01D | CAP CER 0.5PF 50V C0G/NP0 0402 | C134,C136,C142 | 3 | 0.5pF
26 | Murata Electronics | GJM1555C1HR20BB01D | CAP CER 0.2PF 50V C0G/NP0 0402 | C137 | 1 | 0.2pF
27 | Murata Electronics | GJM1555C1H150GB01D | CAP CER 15PF 50V C0G/NP0 0402 | C138,C139,C143 | 3 | 15pF
28 | Murata Electronics | GJM1555C1H8R2BB01D | CAP CER 8.2PF 50V C0G/NP0 0402 | C140 | 1
29 | Murata Electronics | GJM1555C1HR90BB01D | CAP CER 0.9PF 50V C0G/NP0 0402 | C141 | 1 | 0.9pF
30 | Murata Electronics | GJM1555C1H8R2BB01D | CAP CER 8.2PF 50V C0G/NP0 0402 | C144 | 1 | 8.2pF
31 | Murata Electronics | GRM188C81E475KE11D | CAP CER 4.7UF 25V X6S 0603 | C148,C155,C157 | 3 | 4..7uF
32 | American Technical Ceramics | 600S2R2BT250XT | CAP CER 2.2PF 250V C0G/NP0 0603 | C180 | 1 | 2.2pF
33 | Murata Electronics | GRM31CR71E475KA88L | Multilayer Ceramic Capacitors MLCC - SMD/SMT 4.7UF 25V 10% 1206 | C222,C223 | 2 | 4.7uF
34 | KEMET | C0603C104Z3VACTU | Multilayer Ceramic Capacitors MLCC - SMD/SMT 25V 0.1uF 0603 Y5V -20/+80% | C224,C225,C226 | 3 | 0.1uF
35 | Murata Electronics | GRM32ER61C476KE15L | Multilayer Ceramic Capacitors MLCC - SMD/SMT SUGGESTD REPLACEMENT 81-GRM31CR61C476ME4L | C227 | 1 | 47uF
36 | Murata | GRM155R71C822KA01D | 8200pF ±10% 16V Ceramic Capacitor X7R 0402 (1005 Metric) | C228 | 1 | 8.2nF
37 | Samsung Electro-Mechanics | CL21C180JBANNNC | Multilayer Ceramic Capacitors MLCC - SMD/SMT SAMSUNG | C229 | 1 | 18pF
38 | TDK Corporation | CGA4J2C0G1H333J125AA | 0.033µF ±5% 50V Ceramic Capacitor C0G, NP0 0805 (2012 Metric) | C230 | 1 | 33nF
39 | Murata Electronics North America | GRM188C81C106MA73D | 10uF 16V Ceramic Capacitor X6S 0603 (1608 Metric) 0.063" L x 0.031" W (1.60mm x 0.80mm) | C231 | 1 | 10uF
40 | Yageo | CC0402KRX7R8BB104 | CAP CER 0.1UF 25V X7R 0402 | C232,C233,C234,C236,C237,C238 | 6 | 0.1uF
41 | Taiyo Yuden | EMK107SD103KA-T | CAP CER 10000PF 16V 0603 | C235,C240 | 2 | 10000pF
42 | Samsung Electro-Mechanics America, Inc | C3216X6S1C226M160AC | CAP CER 22UF 16V X6S 1206 | C239 | 1 | 22uF
43 | Murata Electronics North America | GRM188C81C106MA73D | 10uF 16V Ceramic Capacitor X6S 0603 (1608 Metric) 0.063" L x 0.031" W (1.60mm x 0.80mm) | C241 | 1 | 10uF
44 | Yageo | CC0402KRX7R8BB104 | CAP CER 0.1UF 25V X7R 0402 | C242,C248 | 2 | 0.1uF
45 | Taiyo Yuden | EMK212BB7106MG-T | CAP CER 10UF 16V X7R 0805 | C243,C247 | 2 | 10uF
46 | KEMET | C0603C225K4PACTU | CAP CER 2.2UF 16V X5R 0603 | C244 | 1 | 2.2uF
47 | KEMET | CBR04C100J1GAC | CAP CER 10PF 100V C0G/NP0 0402 | C245 | 1 | 10pF
48 | Murata Electronics North America | GCM155R71H103KA55D | CAP CER 10000PF 50V X7R 0402 | C246 | 1 | 10nF
49 | Kemet | T521X107M025ATE030 | CAP TANT POLY 100UF 25V 2917 | C255,C256 | 2 | 100uF
50 | AVX | 0402YC104KAT2A | CAP CER 0.1UF 16V X7R 0402 | C258,C260,C262 | 3 | 0.1uF
51 | AVX | 0402YC104KAT2A | CAP CER 0.1UF 16V X7R 0402 | C259 | 1 | 0.1uF
52 | AVX | 04023C101JAT2A | CAP CER 100PF 25V X7R 0402 | C261 | 1 | 100pF
53 | KEMET | C0402C561J5GACAUTO | CAP CER 560pF 5% 50V X7R 0402 | C277 | 1 | 560pF
54 | STMicroelectronics | STPS1045B | Schottky Diodes & Rectifiers 10 Amp 45 Volt | D1 | 1 | STPS1045B
55 | Infineon Technologies | BAS140WE6327HTSA1 | DIODE SCHOTTKY 40V 120MA SOD323 | D2,D3 | 2 | BAS140WE6327
56 | Littelfuse Inc. | PGB1010603MR | TVS DIODE 24V 150V 0603 | D4 | 1 | PGB1010603MR
57 | Skyworks | CLA4606-085LF | Surface-Mount Limiter Diode | D5 | 1 | CLA4606-085LF
58 | Diodes Incorporated | B530C-13-F | DIODE SCHOTTKY 30V 5A SMC | D6 | 1 | B530C-13-F
59 | Littelfuse Inc. | SMDJ16CA | TVS DIODE 16VWM 26VC SMD | D11 | 1 | SMDJ16CA
60 | Nexperia USA Inc. | PESD3V3X1BL,315 | TVS DIODE 3.3V SOD882 | D12,D13,D14,D15 | 4 | PESD3V3X1BL,315
61 | MEC MARCOM | MFB-321611-0120PW | Ferrite Bead, 1206 [3216 Metric], 120 ohm, 6 A, MFB Series, 0.015 ohm, ± 25% | FB4,FB5 | 2 | 120E
62 | Murata Electronics | BLM15PX330SN1D | FERRITE BEAD 33 OHM 0402 1LN | FB6,FB7,FB8,FB9,FB10,FB14,FB15 | 7 | 33E
63 | Murata Electronics | BLM18PG121SN1B | FERRITE BEAD 120 OHM 0603 1LN | FB11,FB12 | 2 | 120E
64 | CTS Corp | USB040C | Band 40 USB Series TDD Bandpass Filter | FL1 | 1 | USB040C
65 | Littelfuse | MINISMDC260F/16-2 | Resettable Fuses - PPTC 16Vdc 100A MINI-SMD | F1,F2 | 2 | MINISMDC260F/16-2
66 | Hirose | FX23L-40-S-0.5SV10 | Connector | J1 | 1 | FX23L-40-S-0.5SV10
67 | Molex | 105309-1102 | Headers & Wire Housings NANOFIT HDR VT SGL KNK 2CKT TIN BLK | J2 | 1 | 1053091102
68 | Amphenol ICC (FCI) | 10056844-114LF | CONN HEADER VERT 14POS 2.54MM | J3 | 1 | 10056844-114LF
69 | TE Connectivity AMP Connectors | 87224-4 | CONN HEADER VERT 4POS 2.54MM | J4 | 1 | 87224-4
70 | Coilcraft | XAL5030-332MEC | Fixed Inductors 3.3uH 20% 8.1A 23.3mOhms AEC-Q200 | L2 | 1 | 3.3UH
71 | Coilcraft | XAL5050-562MEC | Fixed Inductors 5.6uH 20% 7.2A 25.8mOhms AEC-Q200 | L4 | 1 | 5.6UH
72 | Murata Electronics | LQG15HS18NJ02D | FIXED IND 18NH 400MA 360 MOHM | L5,L6,L11 | 3 | 18nH
73 | Murata Electronics | LQG15HS22NJ02D | FIXED IND 22NH 350MA 420 MOHM | L7 | 1 | 22nH
74 | Murata Electronics | LQG15HS2N2S02D | FIXED IND 2.2NH 900MA 120 MOHM | L8,L12 | 2 | 2.2nH
75 | Murata Electronics | LQG15HS5N6S02D | FIXED IND 5.6NH 650MA 200 MOHM | L9,L13 | 2 | 5.6nH
76 | Murata Electronics | LQG15HS8N2J02D | FIXED IND 8.2NH 550MA 240 MOHM | L10 | 1 | 8.2nH
77 | Murata Electronics | LQG15HS1N2S02D | FIXED IND 1.2NH 1A 90 MOHM | L14,L16 | 2 | 1.2nH
78 | Coilcraft | XAL5050-562MEB | Fixed Inductors 5.6uH Shld 20% 7.2A 25.8mOhms AECQ2 | L15 | 1 | 5.6UH
79 | TDK | ACM70V-701-2PL-TL00 | Common Mode Chokes / Filters 80V 4.0A 15mOhms AEC-Q200 | L22 | 1 | ACM70V-701-2PL-TL00
80 | Murata Electronics | LQG15HS3N3S02D | FIXED IND 3.3NH 800MA 170 MOHM | L30 | 1 | 3.3nH
81 | Fairchild Semiconductor | FDMC8030 | Dual N-Channel Power Trench MOSFET | Q1 | 1 | FDMC8030
82 | Rohm Semiconductor | RYM002N05T2CL | MOSFET N-CH 50V 0.2A VMT3 | Q2,Q3,Q5,Q6 | 4 | RYM002N05T2CL
83 | Vishay Siliconix | SI2333DS-T1-E3 | MOSFET P-CH 12V 4.1A SOT23-3 | Q4 | 1 | SI2333DS-T1-E3
84 | Rohm Semiconductor | MCR01MZPJ000 | RES SMD 0.0OHM JUMPER 1/16W 0402 | R10,R19,R25,R27,R133,R242,R255,R257,R258,R259,R260,R261,R262,R263,R302,R353,R357,R358,R359 | 19 | 0E
85 | Rohm Semiconductor | MCR01MZPJ000 | RES SMD 0.0OHM JUMPER 1/16W 0402 | R12,R16,R18,R24,R26,R39,R40,R74,R76,R77,R78,R79,R80,R96,R103,R110,R111,R112,R113,R114,R115,R120,R121,R122,R130,R156,R185,R186,R187,R188,R189,R190,R191,R238,R239,R240,R241,R246,R247,R248,R249,R254,R270,R275,R276,R277,R278,R304,R305,R354,R355,R356,R360,R361,R362,R363 | 56 | 0E
86 | Vishay Dale | CRCW0402115KFKED | RES SMD 115K OHM 1% 1/16W 0402 | R13 | 1 | 115K
87 | Vishay Dale | CRCW040256K0FKED | RES SMD 56K OHM 1% 1/16W 0402 | R14 | 1 | 56K
88 | Vishay Dale | CRCW0402634KFKED | RES SMD 634K OHM 1% 1/16W 0402 | R15 | 1 | 634K
89 | Rohm Semiconductor | MCR01MZPF5101 | RES SMD 5.1K OHM 1% 1/16W 0402 | R17,R42,R159 | 3 | 5.1K
90 | Rohm Semiconductor | MCR01MZPF1002 | RES SMD 10K OHM 1% 1/16W 0402 | R20,R41,R63,R65,R66,R67,R68,R69,R72,R73,R95,R104,R108,R131,R139,R264,R272,R274,R352 | 19 | 10K
91 | Rohm Semiconductor | MCR01MZPF1003 | RES SMD 100K OHM 1% 1/16W 0402 | R21,R22,R23,R123,R124 | 5 | 100K
92 | Rohm Semiconductor | MCR01MZPF8201 | RES SMD 8.2K OHM 1% 1/16W 0402 | R28,R30,R33 | 3 | 8.2K
93 | Rohm Semiconductor | MCR01MZPF1004 | RES SMD 1M OHM 1% 1/16W 0402 | R29 | 1 | 1M Ohm
94 | Vishay Dale | CRCW0402200KFKEDC | RES SMD 200K OHM 1% 1/16W 0402 | R31 | 1 | 200K
95 | Vishay / Dale | CRCW040212K7FKED | Thick Film Resistors - SMD 1/16watt 12.7Kohms 1% | R32 | 1 | 12.7K
96 | Vishay Dale | CRCW06030000Z0EB | RES SMD 0 OHM JUMPER 1/10W 0603 | R34,R46,R47,R48,R85,R99,R116 | 7 | 0E
97 | Rohm Semiconductor | MCR01MZPF49R9 | RES SMD 49.9 OHM 1% 1/16W 0402 | R35,R53 | 2 | 49.9E
98 | Vishay Dale | CRCW06030000Z0EB | RES SMD 0 OHM JUMPER 1/10W 0603 | R36,R37,R43,R44,R49,R50,R86,R88,R101,R102,R117,R118,R364,R365 | 14 | 0E
99 | Rohm Semiconductor | MCR01MZPF1101 | RES SMD 1.1K OHM 1% 1/16W 0402 | R38,R100,R119,R350,R351 | 5 | 1.1K
100 | Vishay Dale | CRCW0603120RFKEAC | Thick Film Resistors - SMD 1/10Watt 120ohms 1% | R45 | 1 | 120E
101 | Vishay Dale | CRCW060375R0FKEA | Thick Film Resistors - SMD 1/10watt 75ohms 1% | R51,R52 | 2 | 75E
102 | YAGEO | RC0603JR-070RL. | RES, THICK FILM, 0R, 0.1W, 0603, REEL | R54 | 1 | 0E
103 | YAGEO | RC0603JR-07820RL | SMD Chip Resistor, 820 ohm, ± 5%, 100 mW, 0603 [1608 Metric], Thick Film, General Purpose | R55 | 1 | 820E
104 | VISHAY | CRCW06035R10FKEA | SMD Chip Resistor, 5.1 ohm, ± 1%, 100 mW, 0603 [1608 Metric], Thick Film, General Purpose | R56,R57 | 2 | 5.1E
105 | Rohm Semiconductor | MCR03EZPFX1000 | RES SMD 100 OHM 1% 1/10W 0603 | R58,R59 | 2 | 100E
106 | Yageo Co.Ltd. | RC0402FR-070RL | RES SMD 0 OHM JUMPER 1/16W 0402 | R60,R279,R281 | 3 | 0E
107 | YAGEO | RC0603FR-0710RL | SMD Chip Resistor, 10 ohm, ± 1%, 100 mW, 0603 [1608 Metric], Thick Film, General Purpose | R62 | 1 | 10E
108 | Rohm Semiconductor | MCR01MZPF1002 | RES SMD 10K OHM 1% 1/16W 0402 | R64,R98,R256,R266,R267,R268,R269,R295,R297 | 9 | 10K
109 | Vishay Dale | CRCW04024K70FKEDC | RES 4.7K OHM 1% 1/16W 0402 | R70,R71 | 2 | 4.7K
110 | Yageo | RC0402JR-070RL | RES SMD 0.0OHM JUMPER 1/16W 0402 | R84,R284 | 2 | 0E
111 | Rohm Semiconductor | MCR01MZPF1003 | RES SMD 100K OHM 1% 1/16W 0402 | R97 | 1 | 100K
112 | Vishay Dale | CRCW0603200RFKEA | Thick Film Resistors - SMD 1/10watt 200ohms 1% | R105 | 1 | 200E
113 | Vishay Dale | CRCW060368R0FKEA | Thick Film Resistors - SMD 1/10watt 68ohms 1% | R106,R107 | 2 | 68E
114 | Rohm | MCR01MZPF1242 | RES SMD 12.4K OHM 1% 1/16W 0402 | R109 | 1 | 12.4K
115 | Ohmite | LVK12R050DER | RES 0.05 OHM 0.5% 1/2W 1206 | R125 | 1 | 50mE
116 | Rohm Semiconductor | MCR01MZPF30R1 | RES SMD 30.1 OHM 1% 1/16W 0402 | R126,R127 | 2 | 30.1E
117 | Rohm Semiconductor | MCR01MZPF2703 | RES SMD 270K OHM 1% 1/16W 0402 | R128 | 1 | 270K
118 | Rohm Semiconductor | MCR01MZPF4700 | RES SMD 470 OHM 1% 1/16W 0402 | R129 | 1 | 470E
119 | Vishay Dale | CRCW0402910RFKED | RES SMD 910 OHM 1% 1/16W 0402 | R132 | 1 | 910E
120 | Vishay Dale | CRCW040284K5FKED | 84.5 kOhms ±1% 0.063W, 1/16W Chip Resistor 0402 (1005 Metric) Automotive AEC-Q200 Thick Film | R208 | 1 | 84.5K
121 | Vishay Dale | CRCW040249K9FKEDC | 49.9 kOhms ±1% 0.063W, 1/16W Chip Resistor 0402 (1005 Metric) Thick Film | R209 | 1 | 49.9K
122 | Yageo | RC0402FR-07100KL | RES SMD 100K OHM 1% 1/16W 0402 | R210,R219 | 2 | 100K
123 | Vishay Dale | CRCW040211K0FKED | 11 kOhms ±1% 0.063W, 1/16W Chip Resistor 0402 (1005 Metric) Automotive AEC-Q200 Thick Film | R211 | 1 | 11K
124 | Vishay Dale | CRCW040290K9FKEDC | 90.9 kOhms ±1% 0.063W, 1/16W Chip Resistor 0402 (1005 Metric) Thick Film | R212 | 1 | 90.0K
125 | Vishay Dale | CRCW04026K04FKEDC | 6.04 kOhms ±1% 0.063W, 1/16W Chip Resistor 0402 (1005 Metric) Thick Film | R213 | 1 | 6.04K
126 | Vishay Dale | CRCW04022K67FKED | 2.67 kOhms ±1% 0.063W, 1/16W Chip Resistor 0402 (1005 Metric) Automotive AEC-Q200 Thick Film | R214 | 1 | 2.67K
127 | Stackpole Electronics Inc. | RMCF0402FT29K4 | RES SMD 29.4K OHM 1% 1/16W 0402 | R215 | 1 | 29.4K
128 | Stackpole Electronics Inc. | RMCF0402FT105K | RES SMD 105K OHM 1% 1/16W 0402 | R216 | 1 | 105K
129 | Panasonic Electronic Components | ERJ-2GEJ103X | RES 10K OHM 1/10W 5% 0402 SMD | R217 | 1 | 10K
130 | Panasonic Electronic Components | ERJ-2RKF2002X | RES SMD 20K OHM 1% 1/16W 0402 | R218 | 1 | 20K
131 | Panasonic Electronic Components | ERJ-2GE0R00X | RES SMD 0.0OHM JUMPER 1/10W 0402 | R220 | 1 | 0E
132 | Vishay Dale | CRCW04025K10FKEDC | RES 5.1K OHM 1% 1/16W 0402 | R271 | 1 | 5.1K
133 | Vishay Dale | CRCW04029K10FKED | RES SMD 10K OHM 1% 1/16W 0402 | R273 | 1 | 9.1K
134 | Panasonic Electronic Components | ERA-2AEB3571X | RES SMD 3.57KOHM 0.1% 1/16W 0402 | R280 | 1 | 3.57k
135 | Panasonic Electronic Components | ERA-2ARB1151X | RES SMD 1.15KOHM 0.1% 1/16W 0402 | R282 | 1 | 1.15k
136 | Samsung Electro-Mechanics | RC1005J203CS | RES SMD 20K OHM 5% 1/16W 0402 | R283 | 1 | 20K
137 | Rohm Semiconductor | MCR01MZPF10R0 | RES SMD 10 OHM 1% 1/16W 0402 | R296,R298 | 2 | 10E
138 | Yageo | RC0402FR-07100RL | RES SMD 100 OHM 1% 1/16W 0402 | R306 | 1 | 100E
139 | Yageo | RC0402FR-07100KL | RES SMD 100 KOHM 1% 1/16W 0402 | R307,R308 | 2 | 100K
140 | Yageo | RC0402JR-074R3L | RES SMD 4.3 OHM 5% 1/16W 0402 | R309 | 1 | 4000
141 | Anaren | BD2040J50100A00 | 'Anaren 2000 - 4000 MHz 50Ohm UnBal - 100 Dif Balun | T1,T2,T3 | 3 | BD2040J50100A00
142 | Analog Devices | LTC3786EUD#PBF | Low Iq Synchronous Boost Controller | U1 | 1 | LTC3786EUD#PBF
143 | SKYWORKS | SKYFR-001390 | 2300-2400 MHz Single Junction Robust Lead | U3 | 1 | SKYFR-001390
144 | Anaren | X3C19P2-30S | 30dB Directional Coupler | U4 | 1 | X3C19P2-30S
145 | Texas Instruments | TPS7A9101DSKR | IC REG LIN POS ADJ 1.05A 10SON | U10 | 1 | TPS7A9101DSKR
146 | Analog Devices | LTC3626IUDC#PBF | 20V, 2.5A Synchronous Monolithic Step-Down Regulator with Current and Temperature Monitoring | U13 | 1 | LTC3626IUDC#PBF
147 | Scintera | SC1894A-00C13 | Adaptive RF Power Amplifier Linearizer & Dual RMS Power Measurement Unit (PMU) | U19 | 1 | SC1894A-00C13
148 | Qorvo | TQL9092 | Ultra Low Noise and Flat Gain LNA | U21,U28,U60 | 3 | TQL9092
149 | Murata Power Solutions | PE42823 | RF Switch ICs SPDT, High Power, Absorptive, 50 RF Switc | U22 | 1 | PE42823
150 | NDK America, Inc. | NX3225SA-20.000M-STD-CRS-2 | CRYSTAL 20.0000MHZ 8PF SMD | U27 | 1 | NX3225SA-20.000M-STD-CRS-2
151 | Anaren | DC2337J5010AHF | 'Anaren 2300 - 3700 MHz 0805 10dB Coupler | U29 | 1 | DC2337J5010AHF
152 | Anaren | XDL15-3-030S | RF Delay Line 3ns | U30 | 1 | XDL15-3-030S
153 | Mini-Circuits | BDCN-7-25+ | High Power Bi-Directional Coupler | U32 | 1 | BDCN-7-25+
154 | Texas Instruments | TPS54424RNVR | Buck Switching Regulator IC Positive Adjustable 0.6V 1 Output 4A 18-VFQFN | U47 | 1 | TPS54424RNVR
155 | Texas Instruments | TPS7A8300RGWT | IC REG LDO ADJ/PROG 2A 20VQFN | U48 | 1 | TPS7A8300
156 | Ampleon USA Inc. | BLM9D2327-26B | RF Mosfet LDMOS 2.3GHz ~ 2.7GHz 25W 20-PQFN (8x8) | U70 | 1 | BLM9D2327-26B
157 | Fairchild | FPF2702MPX | AccuPower 0.4 ~ 2 A Adjustable Over-Current Protection Load Switch | U71 | 1 | FPF2702MPX
158 | Analog Devices | LTC6102IMS8#PBF | Precision Zero Drift Current Sense Amplifier | U72 | 1 | LTC6102IMS8PBF
159 | Texas Instruments | OPA320AIDBVT | IC OPAMP GP 1 CIRCUIT SOT23-5 | U73 | 1 | OPA320AIDBVT
160 | Analog Devices Inc. | AD5663RBRMZ-5 | IC DAC 16BIT V-OUT 10MSOP | U74 | 1 | AD5663RBRMZ-5
161 | Texas Instruments | ADS1015IDGST | IC ADC 12BIT SIGMA-DELTA 10VSSOP | U78 | 1 | ADS1015IDGST
162 | STMicroelectronics | M24128-DRMF3TG/K | IC EEPROM 128K I2C 1MHZ 8MLP | U79 | 1 | M24128-DRMF3TG/K
163 | Texas Instruments | SN74LVC1G11DCKR | Single 3-Input Positive-AND Gate | U80 | 1 | SN74LVC1G11DCK
164 | Texas Instruments | LM75AIMM/NOPB | SENSOR DIGITAL -55C-125C 8VSSOP | U82 | 1 | LM75AIMM/NOPB
165 | Maxim Integrated | MAX3379EEUD+ | IC TRNSLTR UNIDIR 14TSSOP | U84 | 1 | MAX3379EEUD+
166 | Texas Instruments | TS5A3166DBVR | IC SWITCH SPST SOT23-5 | U85,U86 | 2 | TS5A3166DBVR
167 | ON Semiconductor | NC7WZ04P6X | Inverter IC 2 Channel SC-88 (SC-70-6) | U87 | 1 | NC7WZ04P6X
168 | Analog devices | ADL5903ACPZN-R7 | 200 MHz to 6 GHz 35 dB TruPwr™ Detector | U88 | 1 | ADL5903
169 | Mini- CIrcuits | BFCN-2360+ | Bandpass Filter B40 50OHM | U89 | 1 | BFCN-2360+
170 | Littelfuse | SMBJ18A | ESD Suppressors / TVS Diodes 600W 18V 5% Uni-Directional | ZD1 | 1 | SMBJ18A
