ukama/ukama-nodes/electronics/mask/stencil/mask_stencil_pmt.dxf

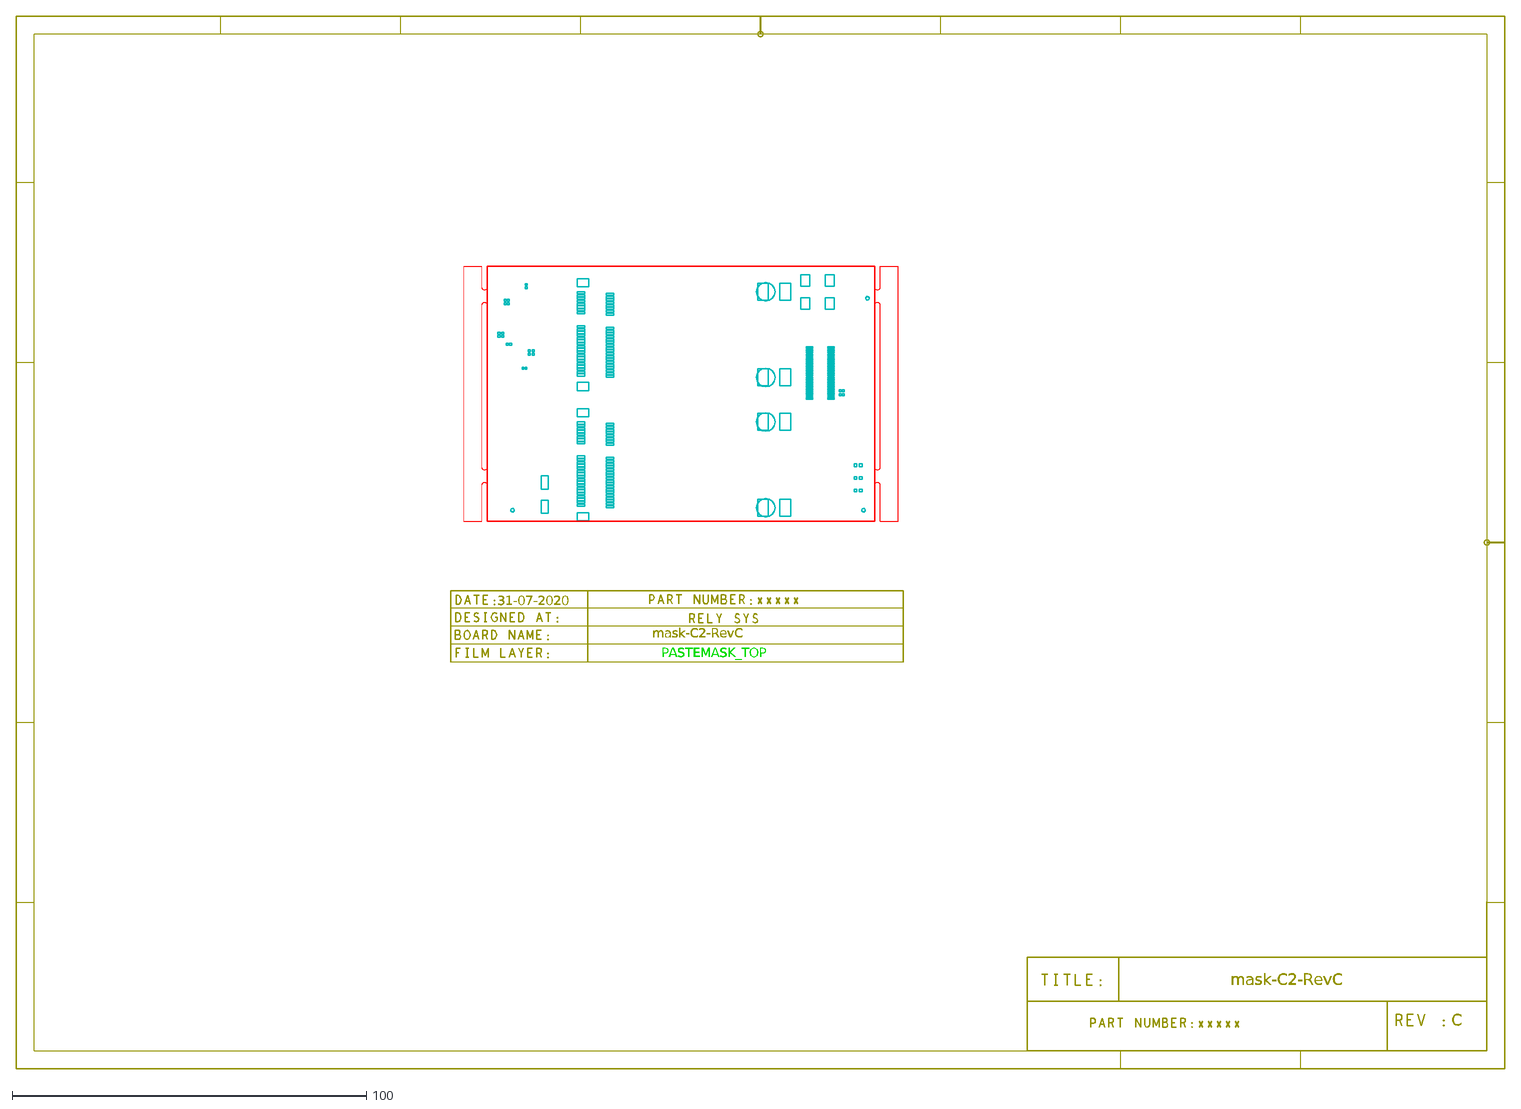
[picture p13: CAD file, 2022-07-07]
electronics/mask/stencil/mask_stencil_pmt.dxf
C
31-07-2020
mask-C2-RevC
PASTEMASK_TOP
