ukama/ukama-nodes/electronics/mini_trx/stencil/mini_trx_pmt.dxf

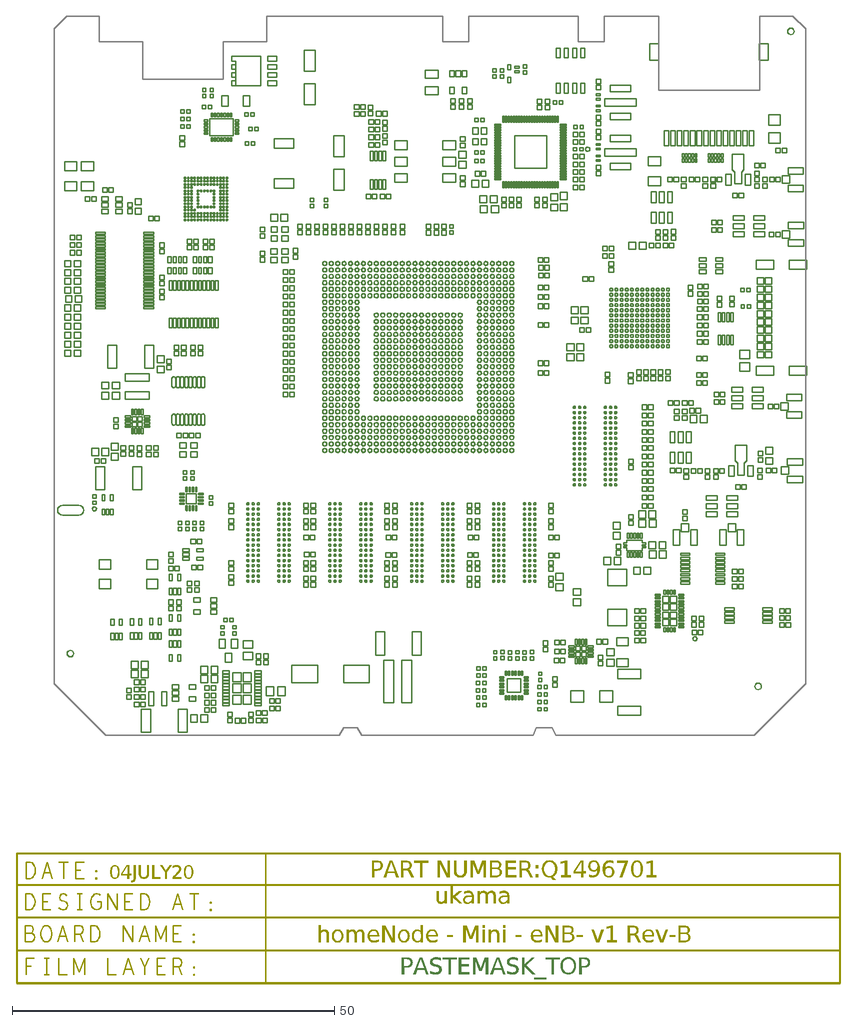
[picture p14: CAD file, 2022-10-14]
electronics/mini_trx/stencil/mini_trx_pmt.dxf
PART NUMBER:Q1496701
ukama
04JULY20
homeNode - Mini - eNB- v1 Rev-B
PASTEMASK_TOP
