ukama/ukama-nodes/electronics/trx/stencil/trx_pmb.dxf

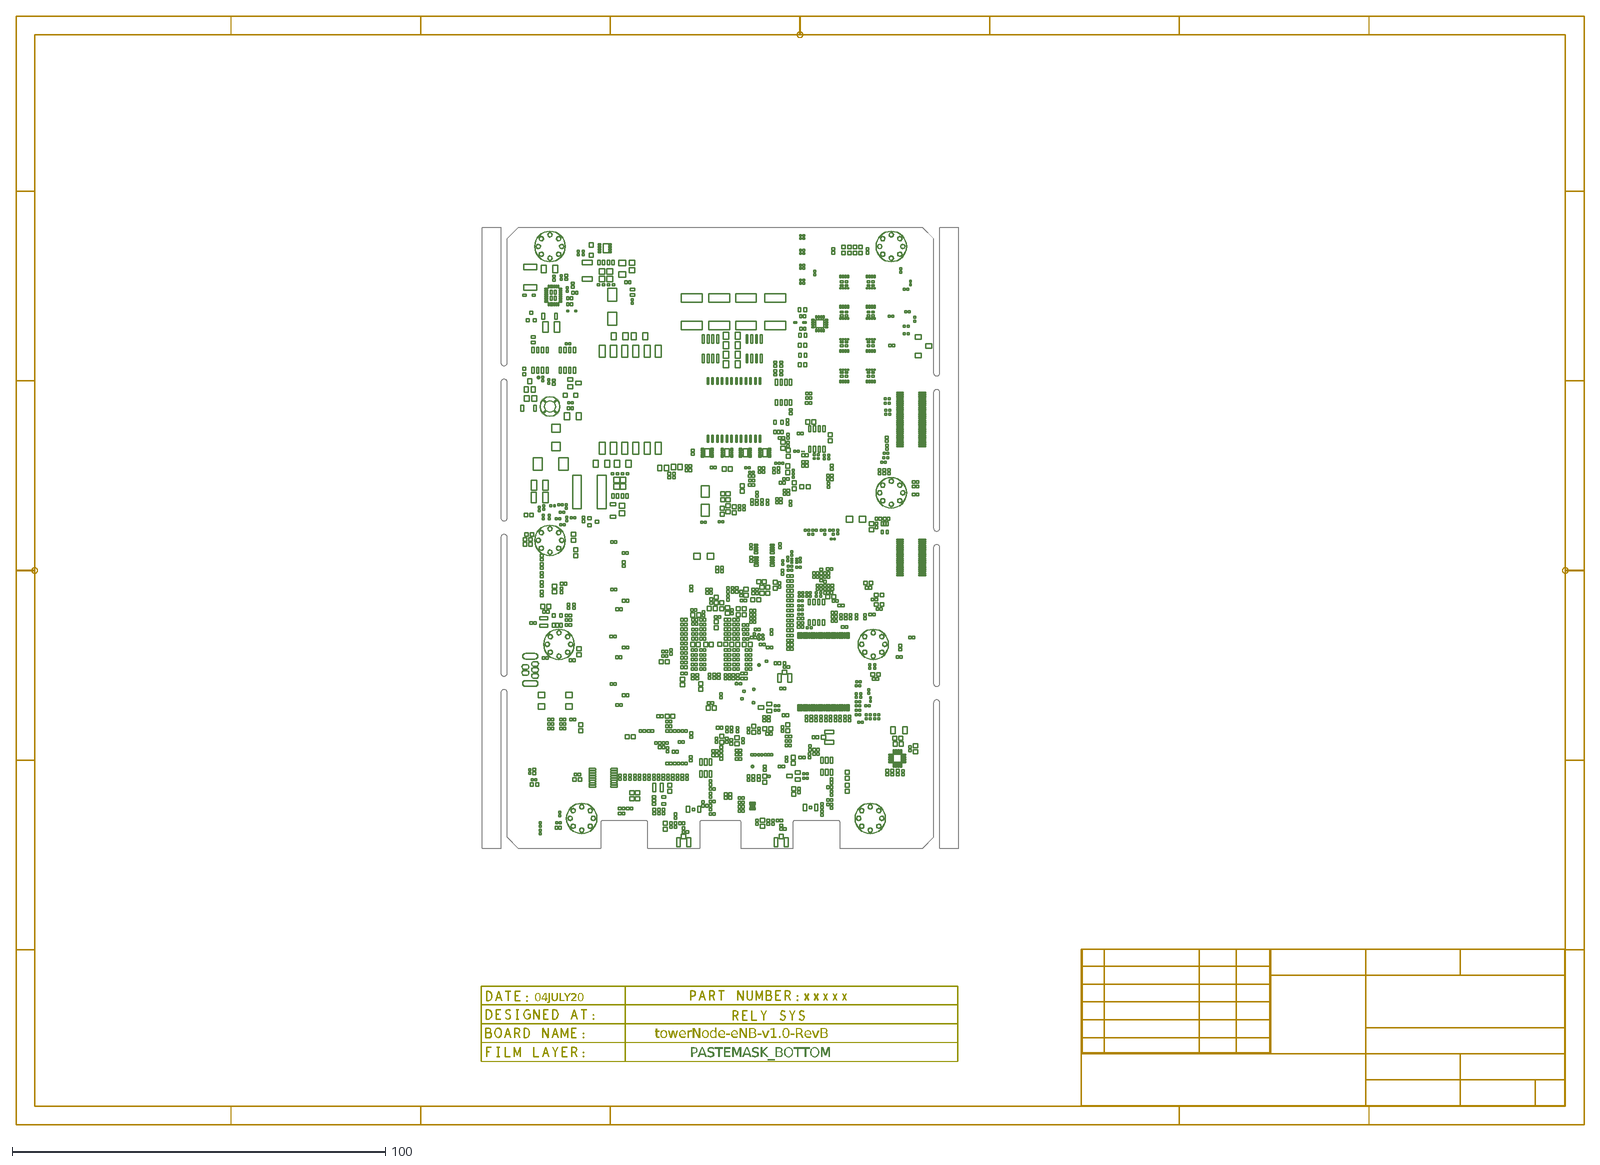
[picture p15: CAD file, 2022-07-07]
electronics/trx/stencil/trx_pmb.dxf
04JULY20
towerNode-eNB-v1.0-RevB
PASTEMASK_BOTTOM
