ukama/ukama-nodes/mechanics/nodes/tower/cad/cup_tower_node.stp

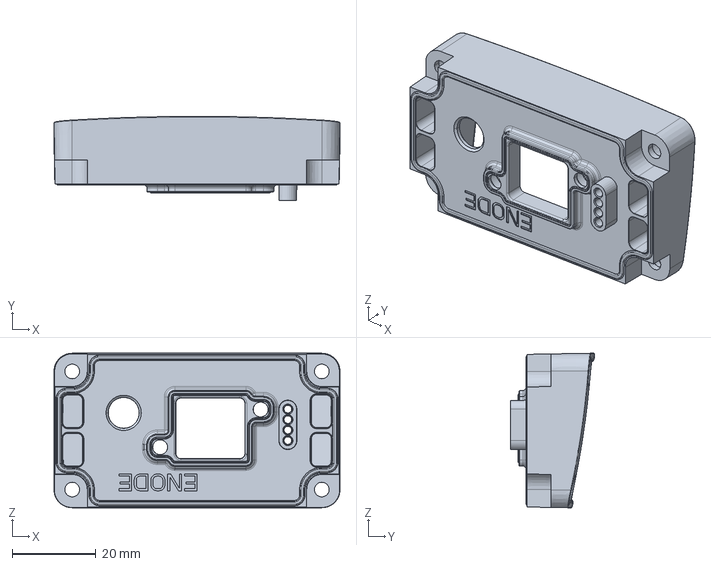
[picture p16: CAD file, 2022-07-19]
mechanics/nodes/tower/cad/cup_tower_node.stp
68.3 x 20.1 x 36.9 mm
