ukama/ukama-nodes/mechanics/nodes/tower/heatsinks/spreader_3.stp

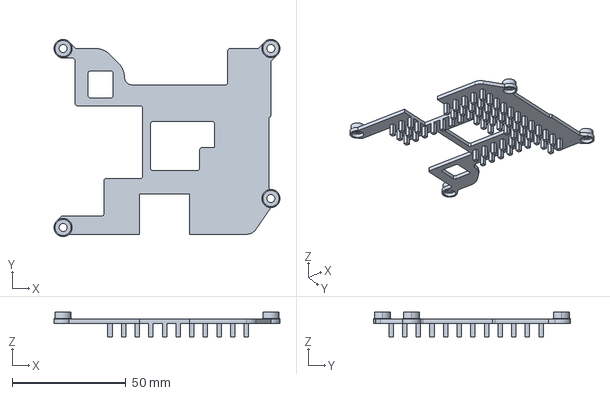
[picture p17: CAD file, 2022-07-19]
mechanics/nodes/tower/heatsinks/spreader_3.stp
99.4 x 86.7 x 10.9 mm
