ukama/ukama-nodes/mechanics/units/amplifier/cad/cup_amplifier_unit.stp

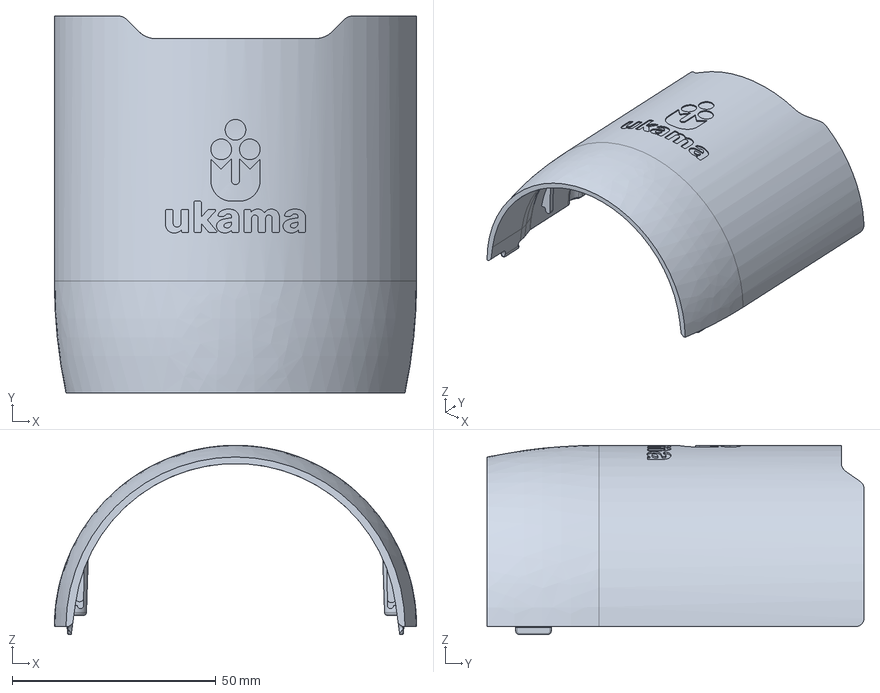
[picture p18: CAD file, 2022-07-20]
mechanics/units/amplifier/cad/cup_amplifier_unit.stp
88.9 x 92.5 x 46.5 mm
