ukama/ukama-nodes/mechanics/nodes/tower/heatsinks/spreader_2.stp

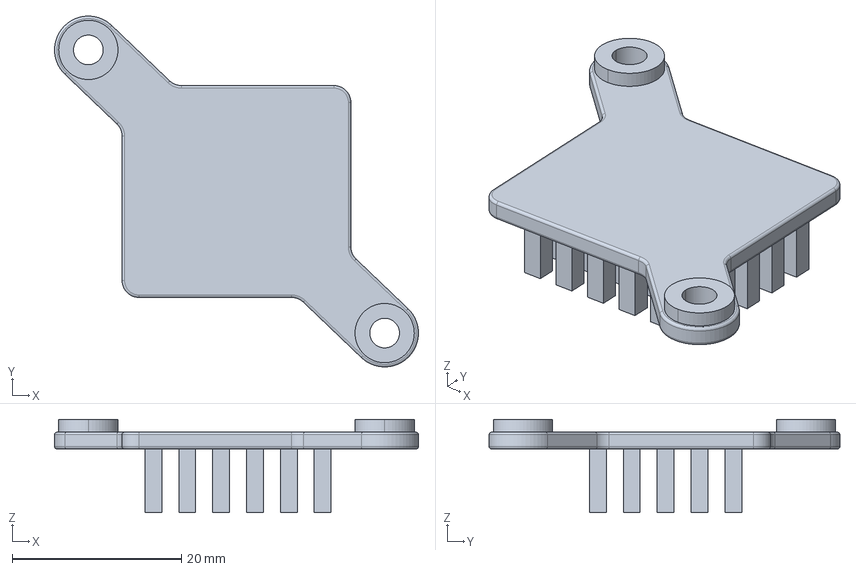
[picture p19: CAD file, 2022-07-19]
mechanics/nodes/tower/heatsinks/spreader_2.stp
43.0 x 41.4 x 11.0 mm
