ukama/ukama-nodes/mechanics/units/amplifier/cad/mounting_cap_amplifier_unit.stp

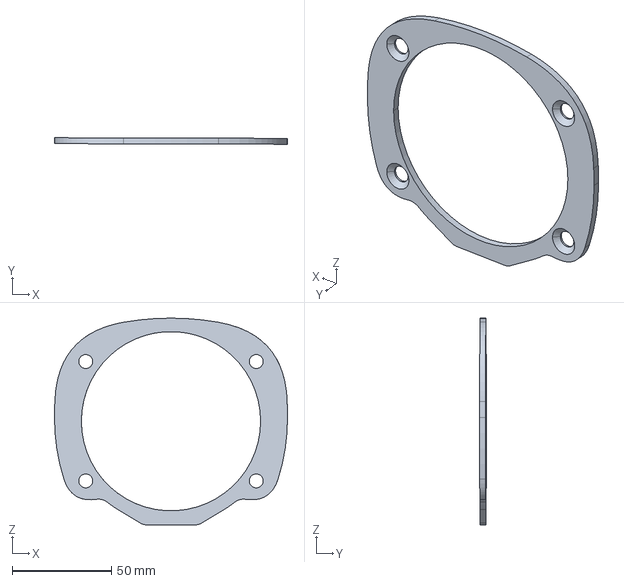
[picture p20: CAD file, 2022-07-20]
mechanics/units/amplifier/cad/mounting_cap_amplifier_unit.stp
117.5 x 3.32 x 104.3 mm
