ukama/ukama-nodes/mechanics/mounting/drawings/mounting_bracket_v2.pdf

E

F

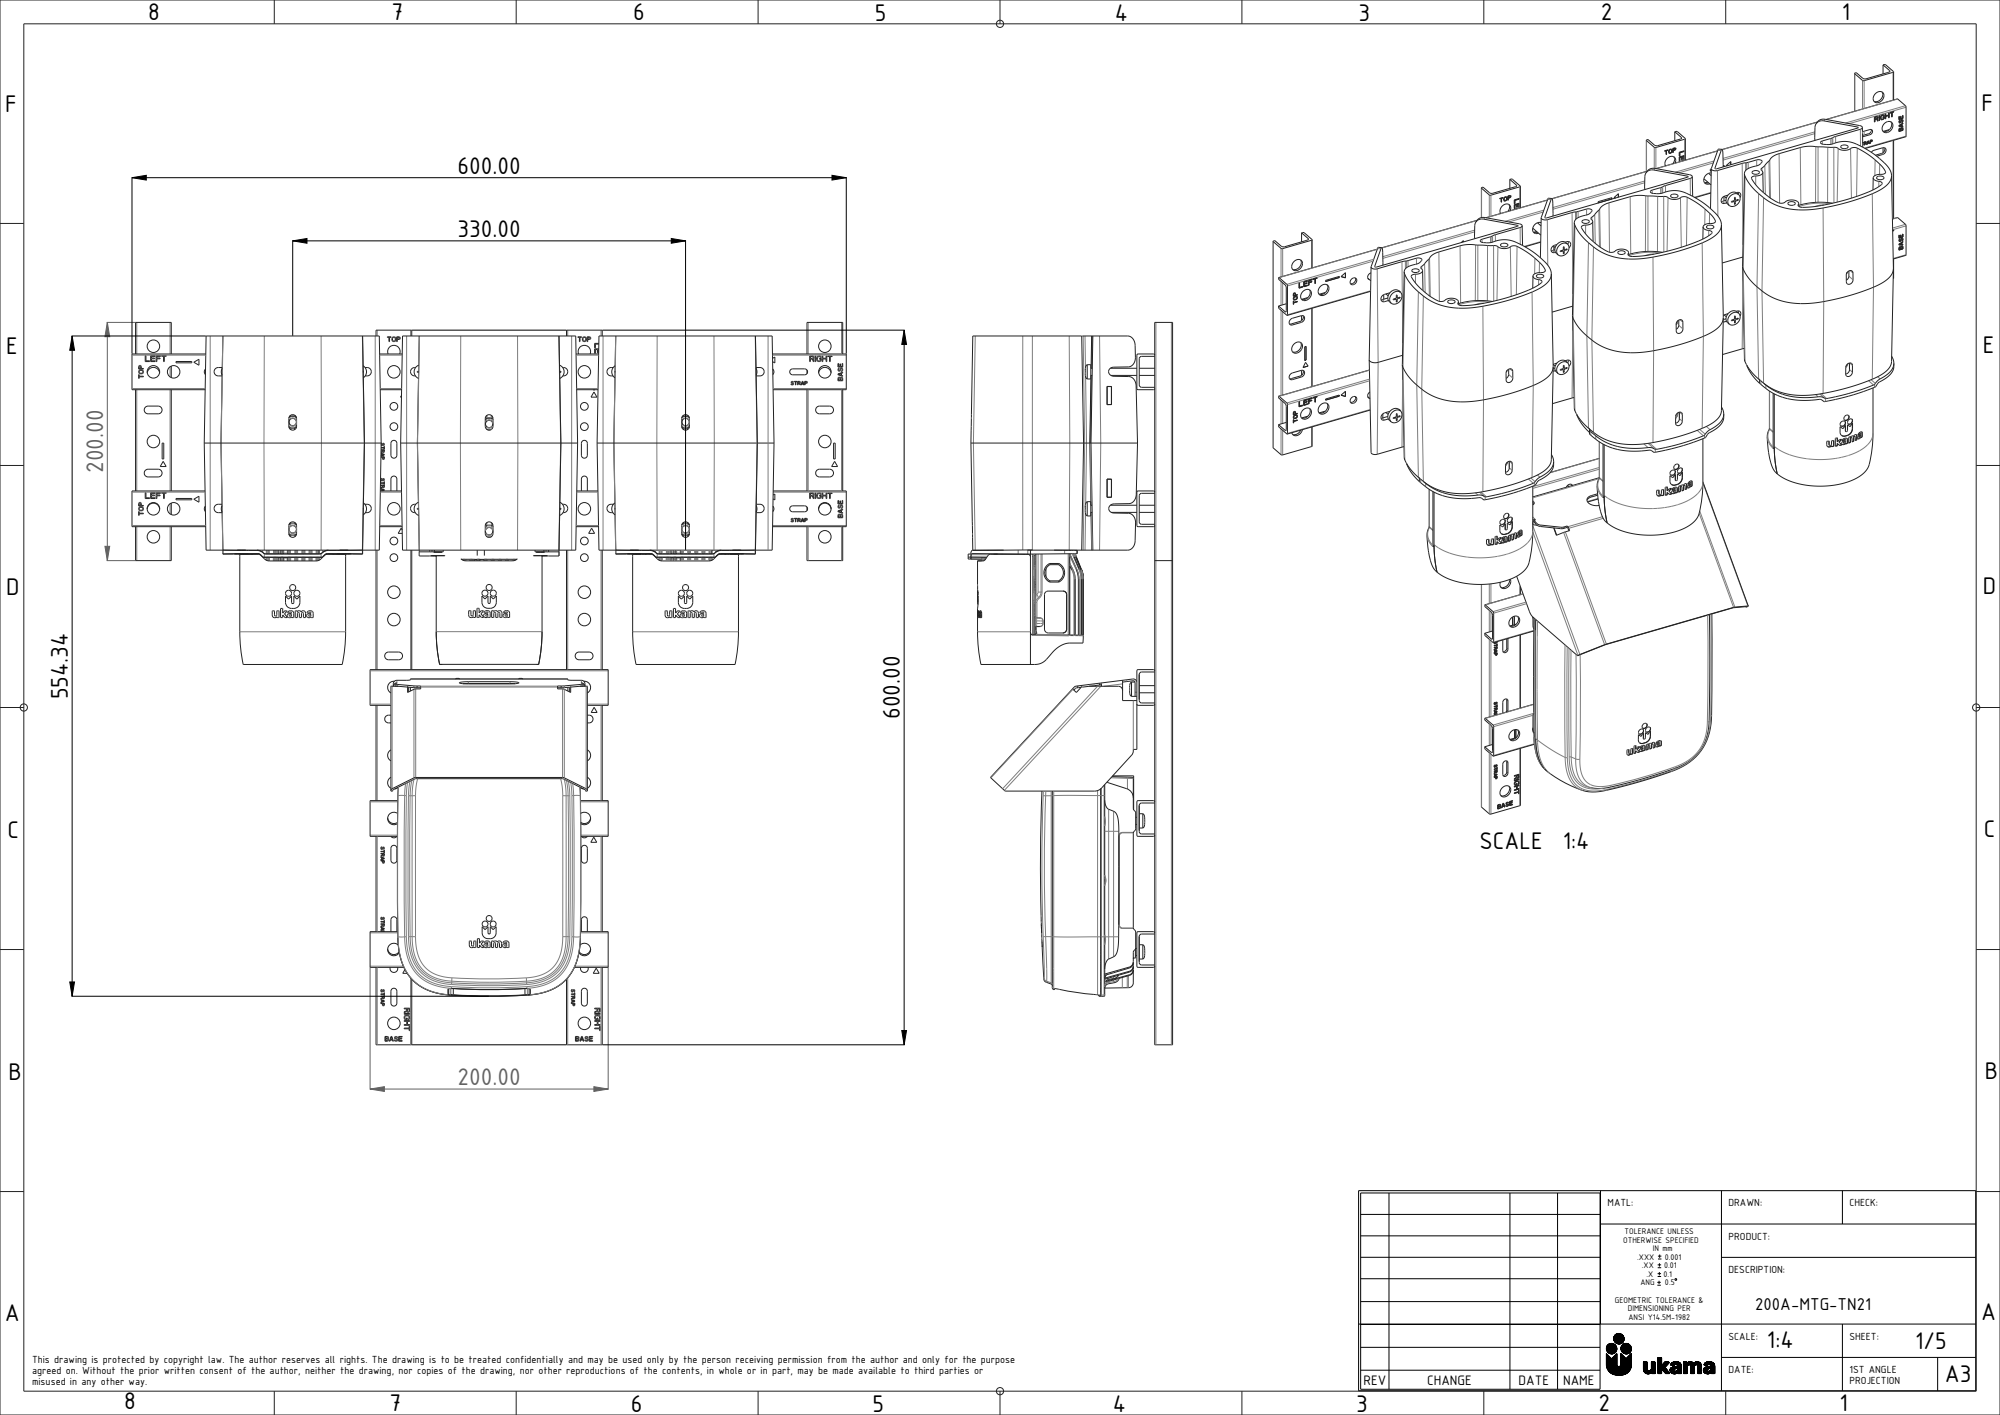
[picture p25: page 1]
200A-MTG-TN21; MATL:; DRAWN:; CHECK:; .XX 0.01 .X 0.1 ANG 0.5; GEOMETRIC TOLERANCE & DIMENSIONING PER; ANSI Y14.5M-1982; PRODUCT:; DESCRIPTION:; SCALE:; SHEET:; DATE:; 1ST ANGLE; REV; CHANGE; DATE NAME; PROJECTION; SCALE 1:4

TOLERANCE UNLESS
OTHERWISE SPECIFIED IN mm .XXX 0.001

This drawing is protected by copyright law. The author reserves all rights. The drawing is to be treated confidentially and may be used only by the person receiving permission from the author and only for the purpose
agreed on. Without the prior written consent of the author, neither the drawing, nor copies of the drawing, nor other reproductions of the contents, in whole or in part, may be made available to third parties or
misused in any other way.

E
E

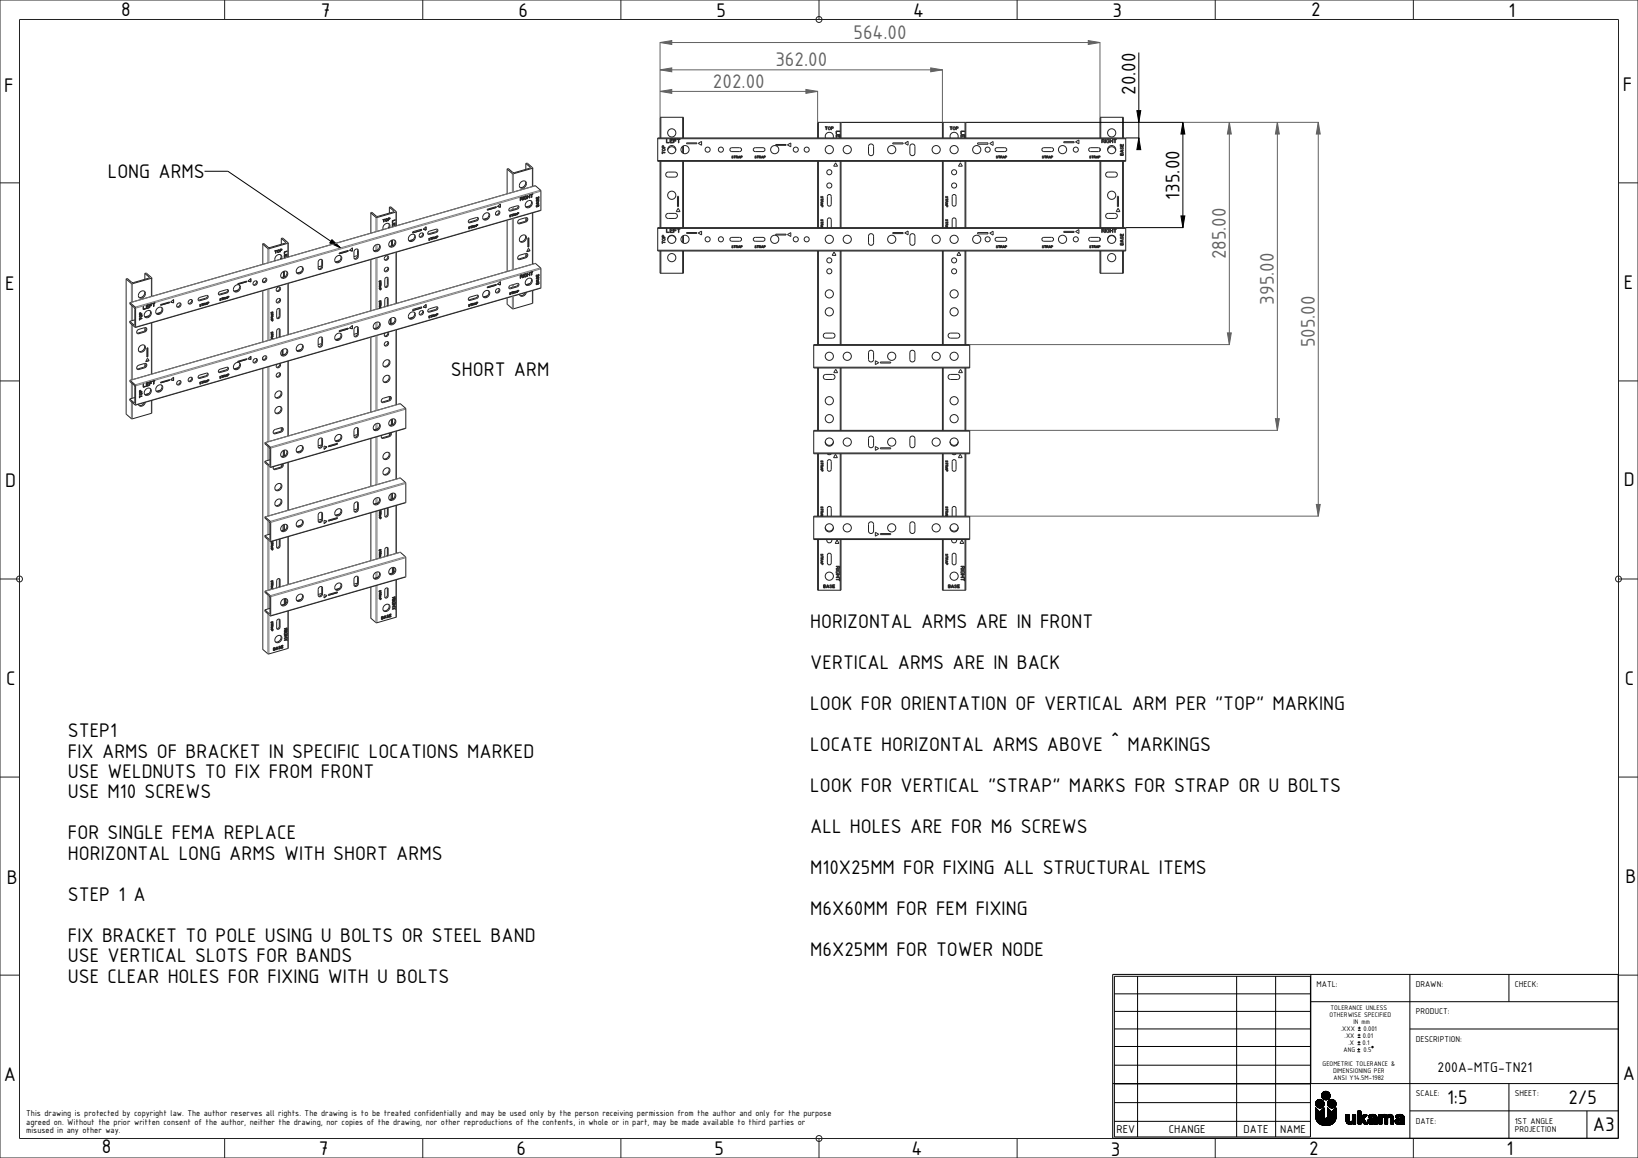
[picture p26: page 2]
MATL:; DRAWN:; CHECK:; .XX 0.01 .X 0.1 ANG 0.5; PRODUCT:; DESCRIPTION:; LONG ARMS; SHORT ARM

HORIZONTAL ARMS ARE IN FRONT
VERTICAL ARMS ARE IN BACK
LOOK FOR ORIENTATION OF VERTICAL ARM PER "TOP" MARKING
LOCATE HORIZONTAL ARMS ABOVE ^ MARKINGS
LOOK FOR VERTICAL "STRAP" MARKS FOR STRAP OR U BOLTS
ALL HOLES ARE FOR M6 SCREWS
M10X25MM FOR FIXING ALL STRUCTURAL ITEMS
M6X60MM FOR FEM FIXING
M6X25MM FOR TOWER NODE

STEP1
FIX ARMS OF BRACKET IN SPECIFIC LOCATIONS MARKED
USE WELDNUTS TO FIX FROM FRONT
USE M10 SCREWS
FOR SINGLE FEMA REPLACE
HORIZONTAL LONG ARMS WITH SHORT ARMS
STEP 1 A
FIX BRACKET TO POLE USING U BOLTS OR STEEL BAND
USE VERTICAL SLOTS FOR BANDS
USE CLEAR HOLES FOR FIXING WITH U BOLTS

TOLERANCE UNLESS
OTHERWISE SPECIFIED IN mm .XXX 0.001

E
E

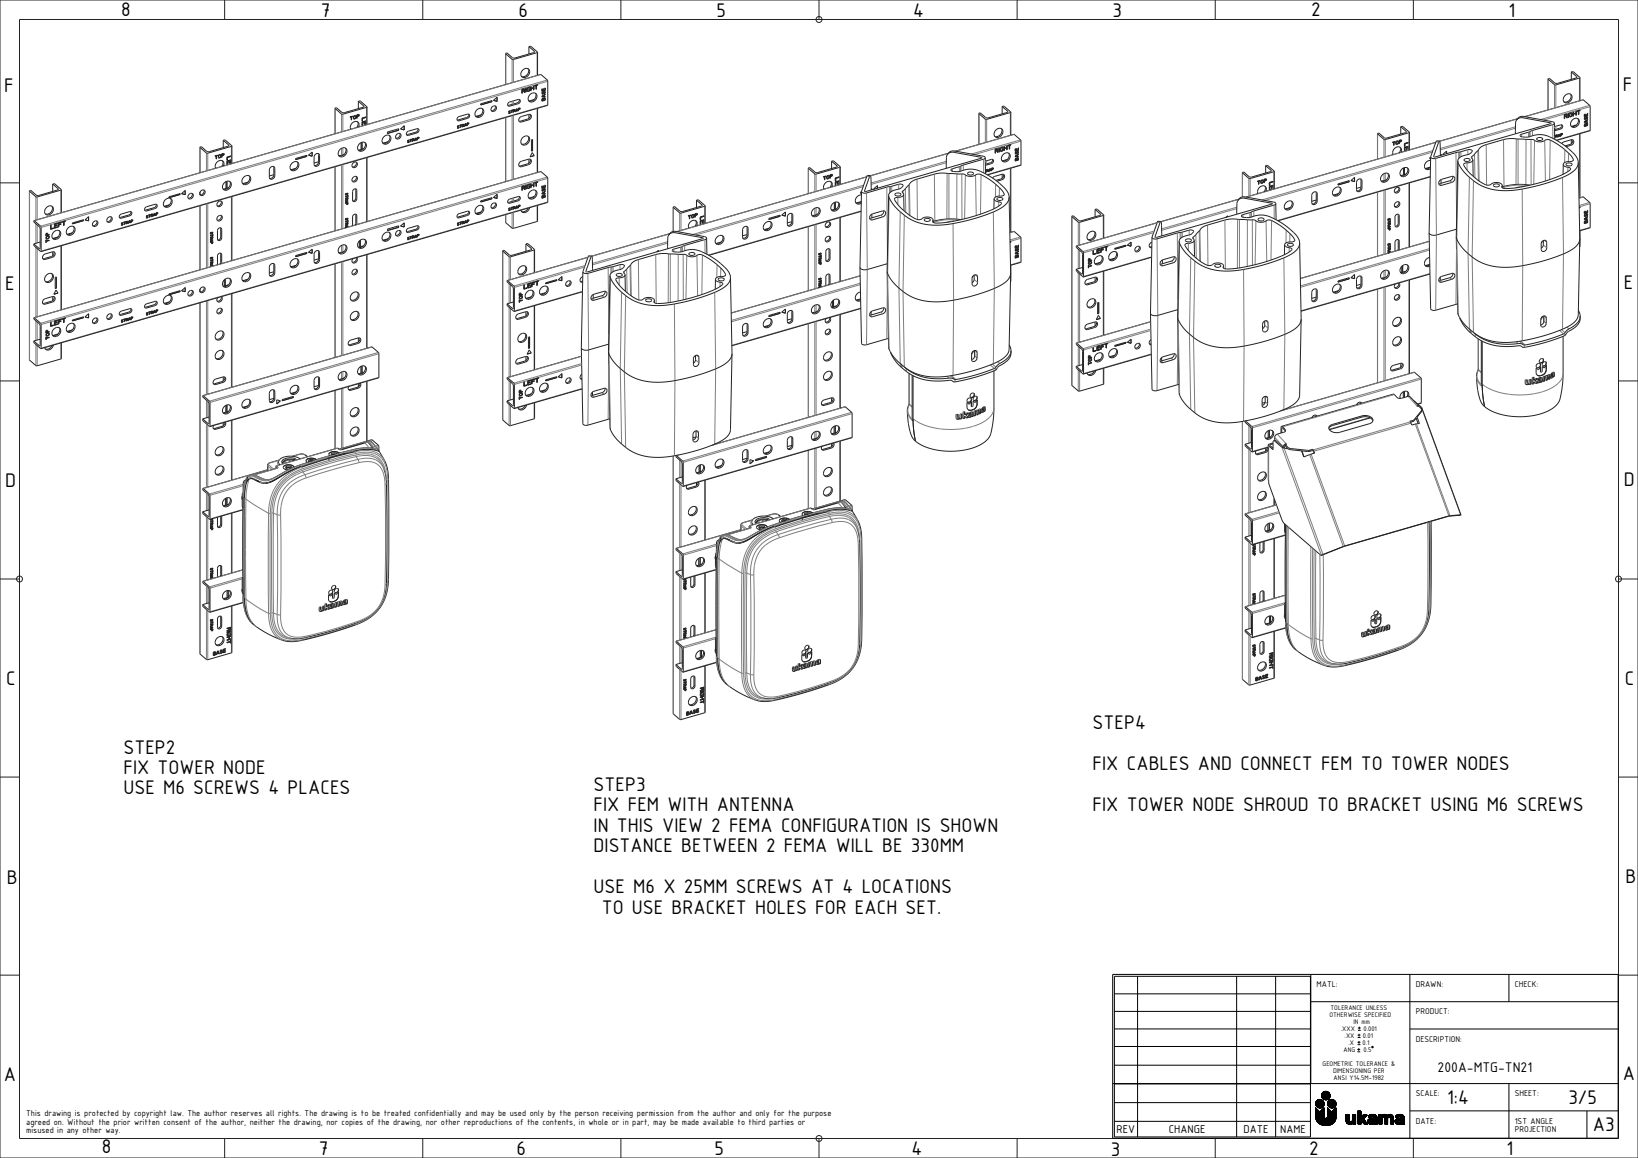
[picture p27: page 3]
MATL:; DRAWN:; CHECK:; .XX 0.01 .X 0.1 ANG 0.5; PRODUCT:; DESCRIPTION:; USE M6 SCREWS 4 PLACES; STEP3

STEP4
FIX CABLES AND CONNECT FEM TO TOWER NODES
FIX TOWER NODE SHROUD TO BRACKET USING M6 SCREWS

STEP2
FIX TOWER NODE

FIX FEM WITH ANTENNA
IN THIS VIEW 2 FEMA CONFIGURATION IS SHOWN
DISTANCE BETWEEN 2 FEMA WILL BE 330MM
USE M6 X 25MM SCREWS AT 4 LOCATIONS
TO USE BRACKET HOLES FOR EACH SET.

TOLERANCE UNLESS
OTHERWISE SPECIFIED IN mm .XXX 0.001

E
E

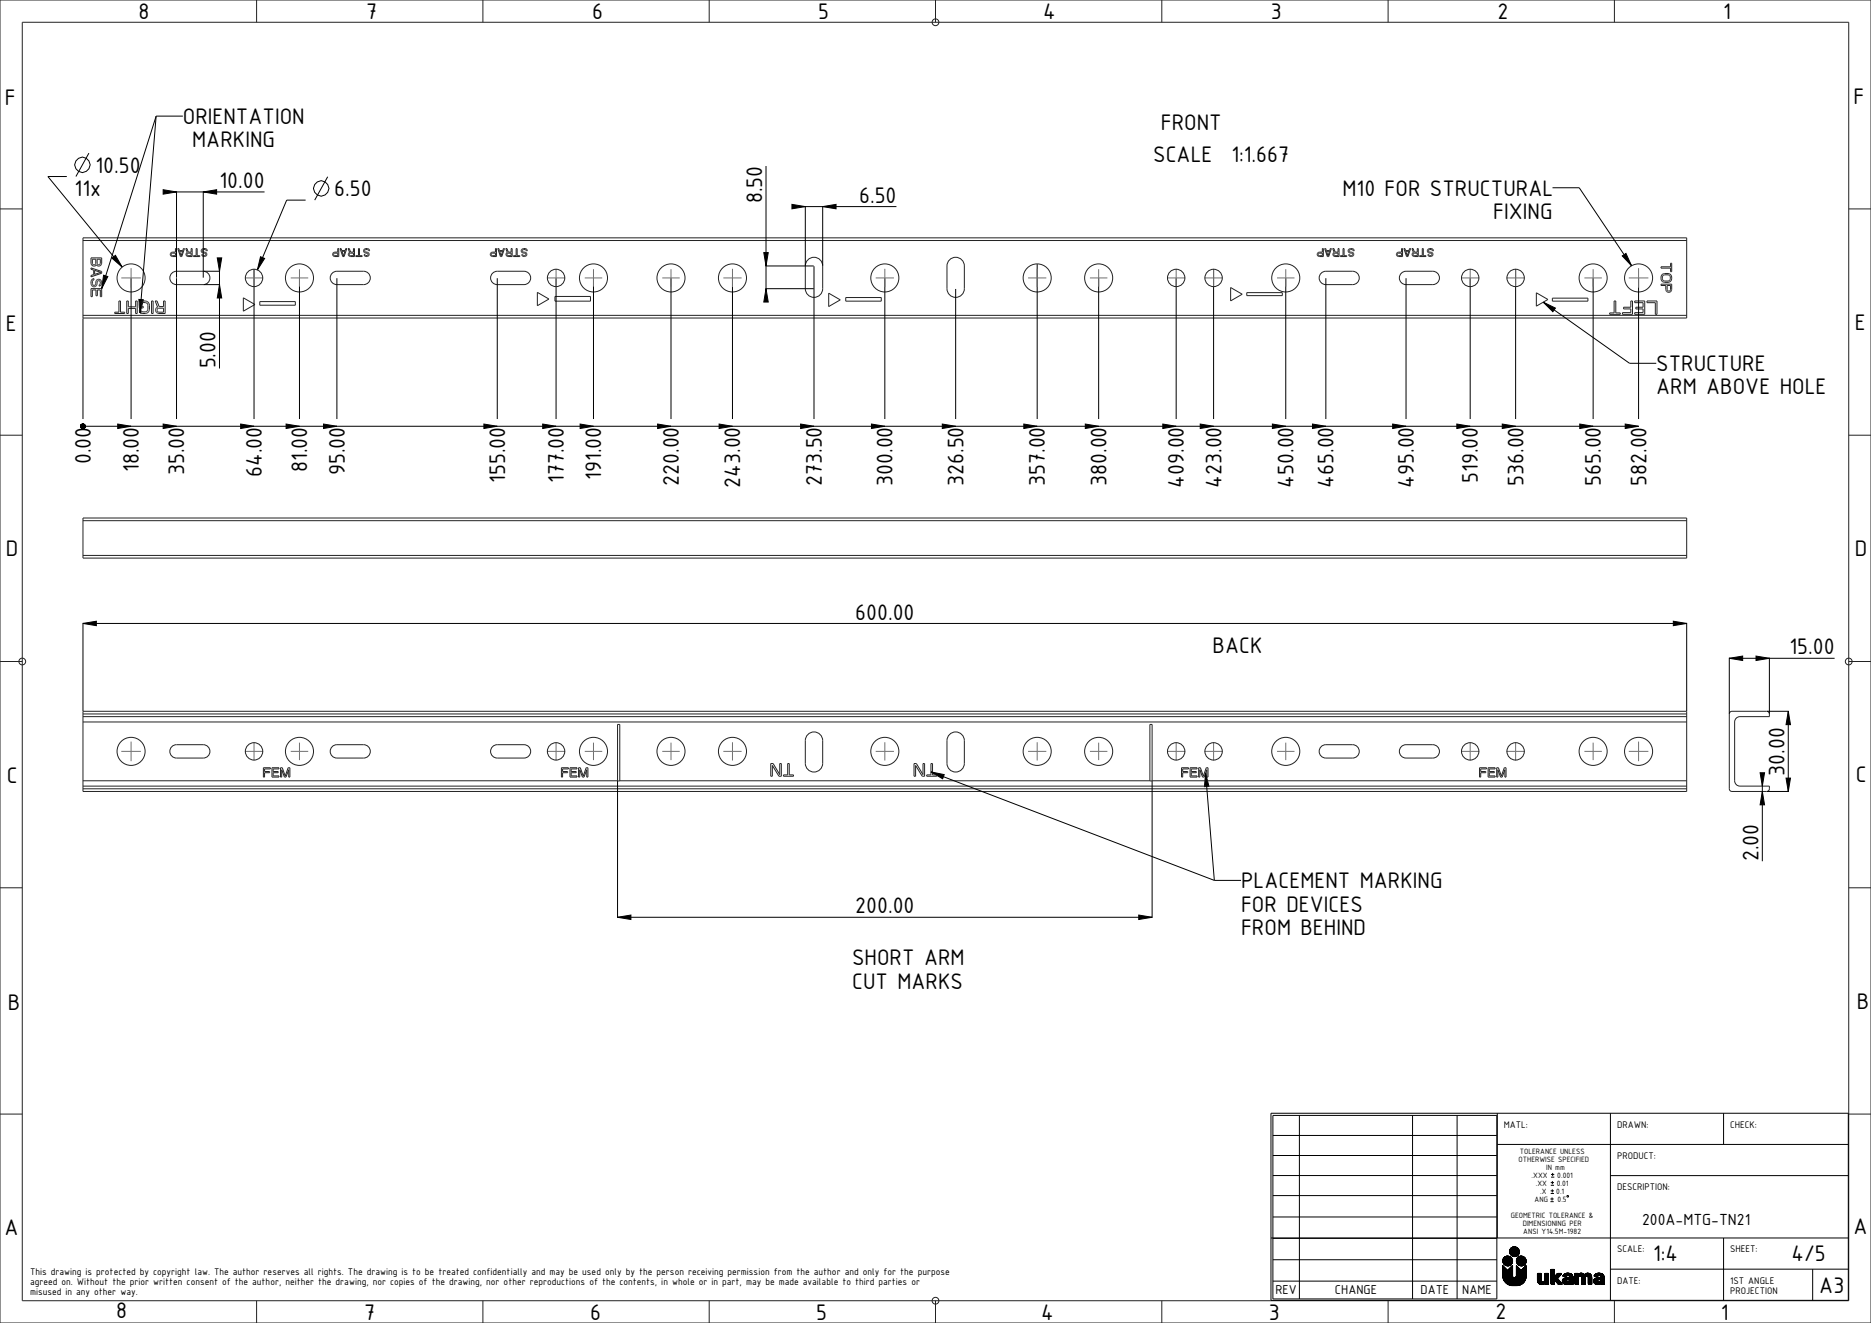
[picture p28: page 4]
MATL:; DRAWN:; CHECK:; .XX 0.01 .X 0.1 ANG 0.5; PRODUCT:; DESCRIPTION:; FRONT; BACK; SHORT ARM CUT MARKS; SCALE 1:1.667; ORIENTATION MARKING; M10 FOR STRUCTURAL FIXING; PLACEMENT MARKING FOR DEVICES FROM BEHIND

STRUCTURE
ARM ABOVE HOLE

TOLERANCE UNLESS
OTHERWISE SPECIFIED IN mm .XXX 0.001

E
E

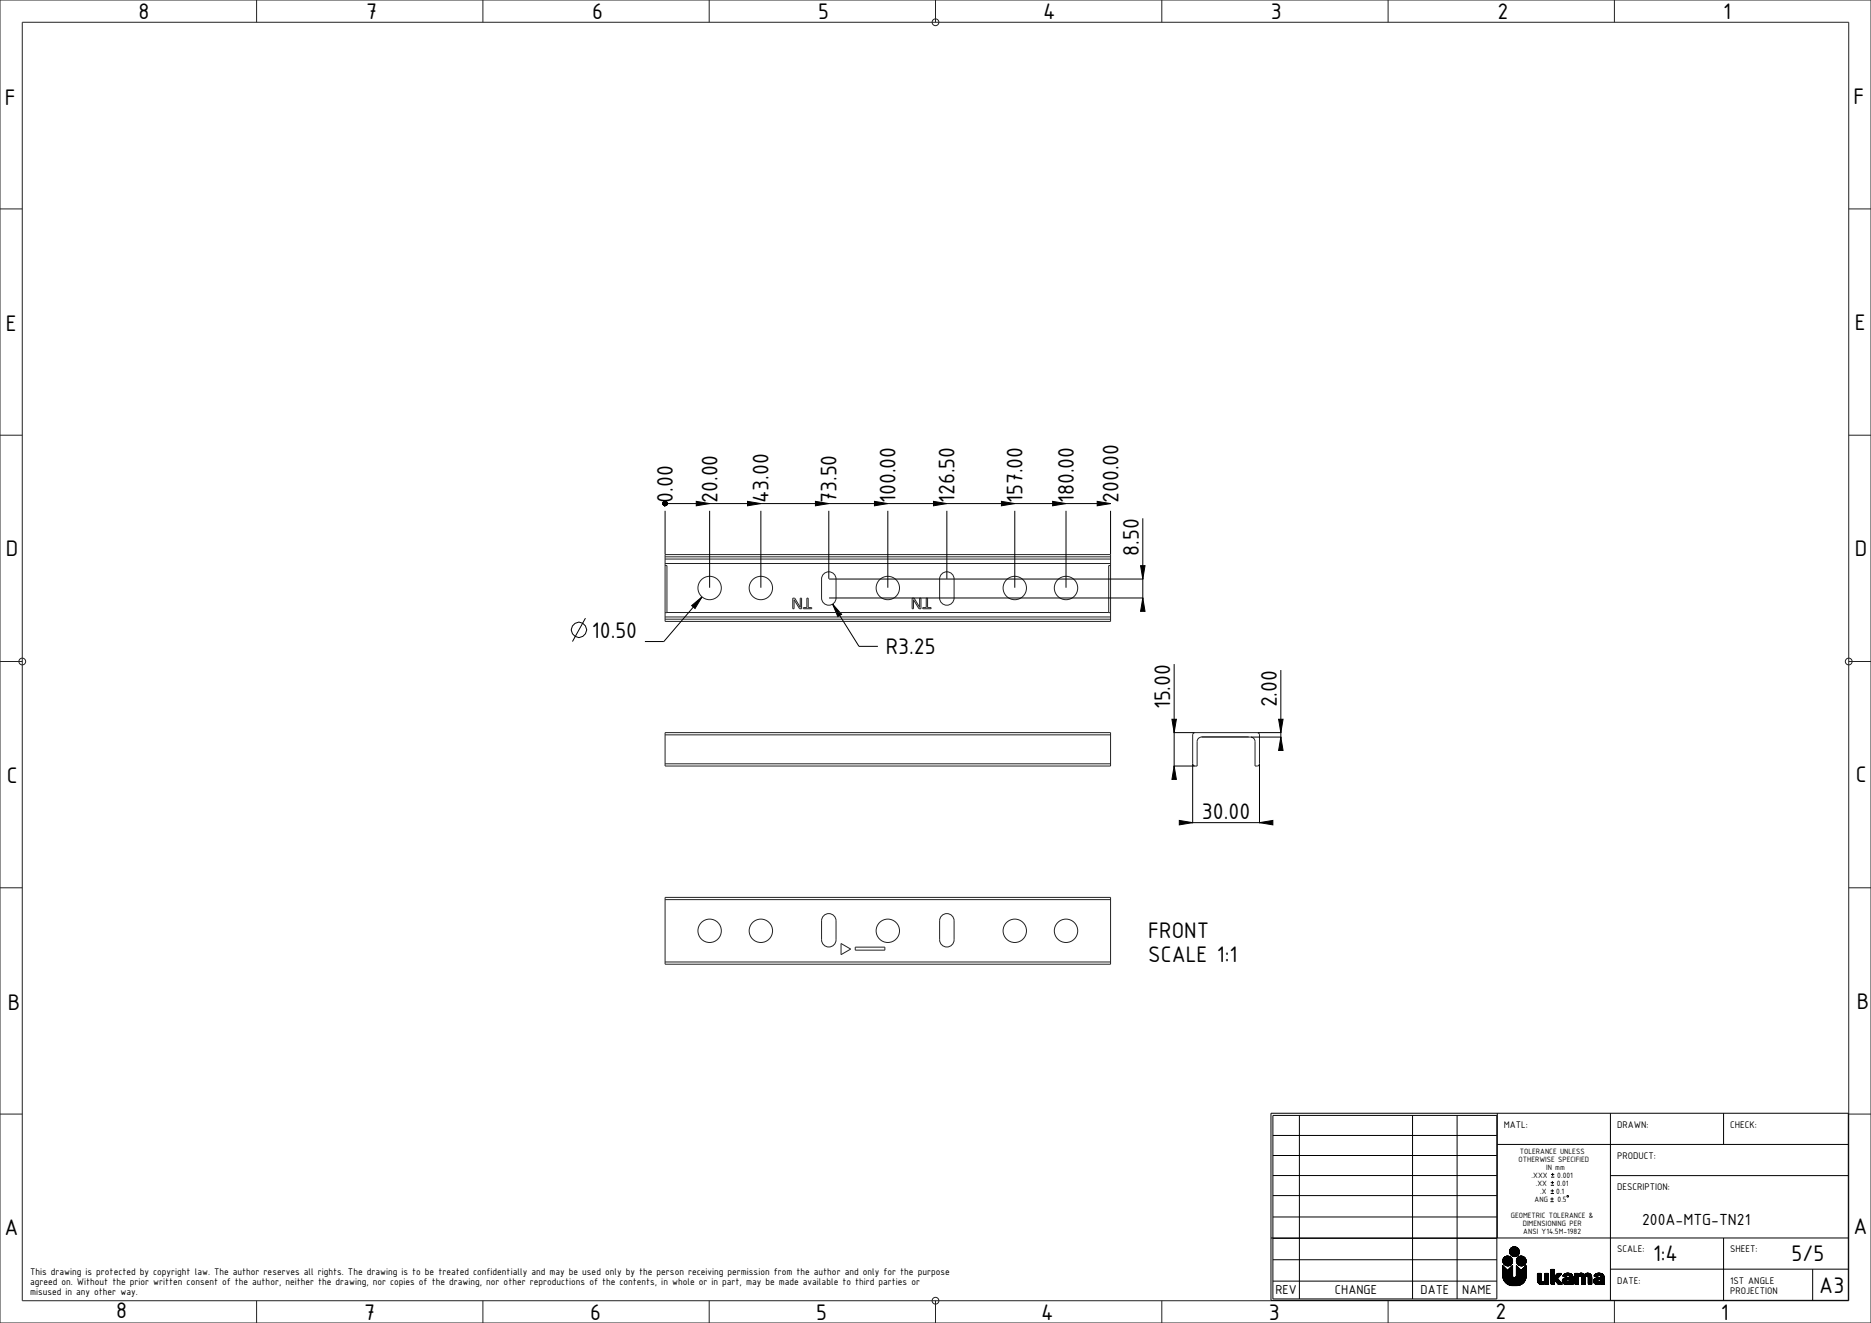
[picture p29: page 5]
MATL:; DRAWN:; CHECK:; .XX 0.01 .X 0.1 ANG 0.5; PRODUCT:; DESCRIPTION:; FRONT SCALE 1:1

TOLERANCE UNLESS
OTHERWISE SPECIFIED IN mm .XXX 0.001
