ukama/ukama-nodes/mechanics/solarcap/drawings/solar_cap.pdf

8 | 7 | 6 | 5 | 4 | 3 | 2 | 1

E

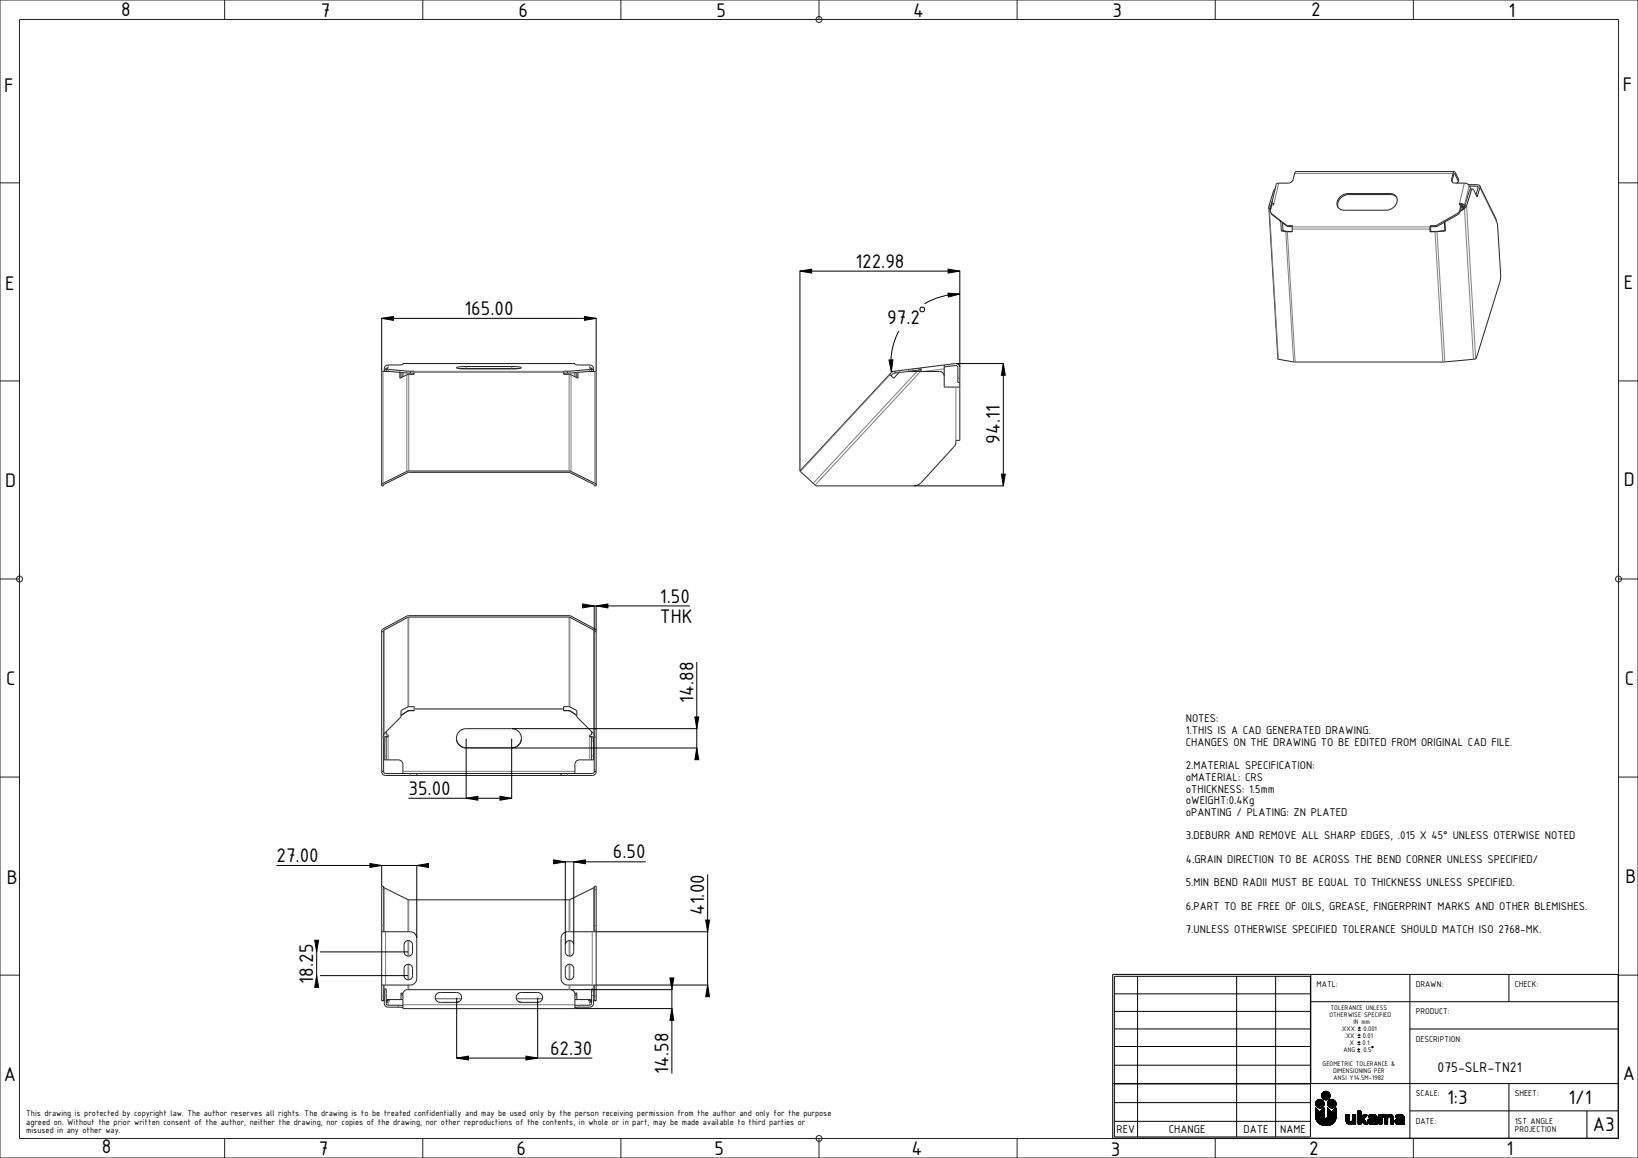
[picture p30: page 1]
075-SLR-TN21; 1.50 THK; MATL:; DRAWN:; CHECK:; .XX 0.01 .X 0.1 ANG 0.5; GEOMETRIC TOLERANCE & DIMENSIONING PER; ANSI Y14.5M-1982; PRODUCT:; DESCRIPTION:; SCALE:; SHEET:; DATE:; 1ST ANGLE; REV; CHANGE; DATE NAME; PROJECTION

NOTES:
1.THIS IS A CAD GENERATED DRAWING.
CHANGES ON THE DRAWING TO BE EDITED FROM ORIGINAL CAD FILE.
2.MATERIAL SPECIFICATION:
oMATERIAL: CRS
oTHICKNESS: 1.5mm
oWEIGHT:0.4Kg
oPANTING / PLATING: ZN PLATED
3.DEBURR AND REMOVE ALL SHARP EDGES, .015 X 45° UNLESS OTERWISE NOTED
4.GRAIN DIRECTION TO BE ACROSS THE BEND CORNER UNLESS SPECIFIED/
5.MIN BEND RADII MUST BE EQUAL TO THICKNESS UNLESS SPECIFIED.
6.PART TO BE FREE OF OILS, GREASE, FINGERPRINT MARKS AND OTHER BLEMISHES.
7.UNLESS OTHERWISE SPECIFIED TOLERANCE SHOULD MATCH ISO 2768-MK.

TOLERANCE UNLESS
OTHERWISE SPECIFIED IN mm .XXX 0.001

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
