ukama/ukama-nodes/electronics/mask/assembly/mask_ast.pdf

# JTB1

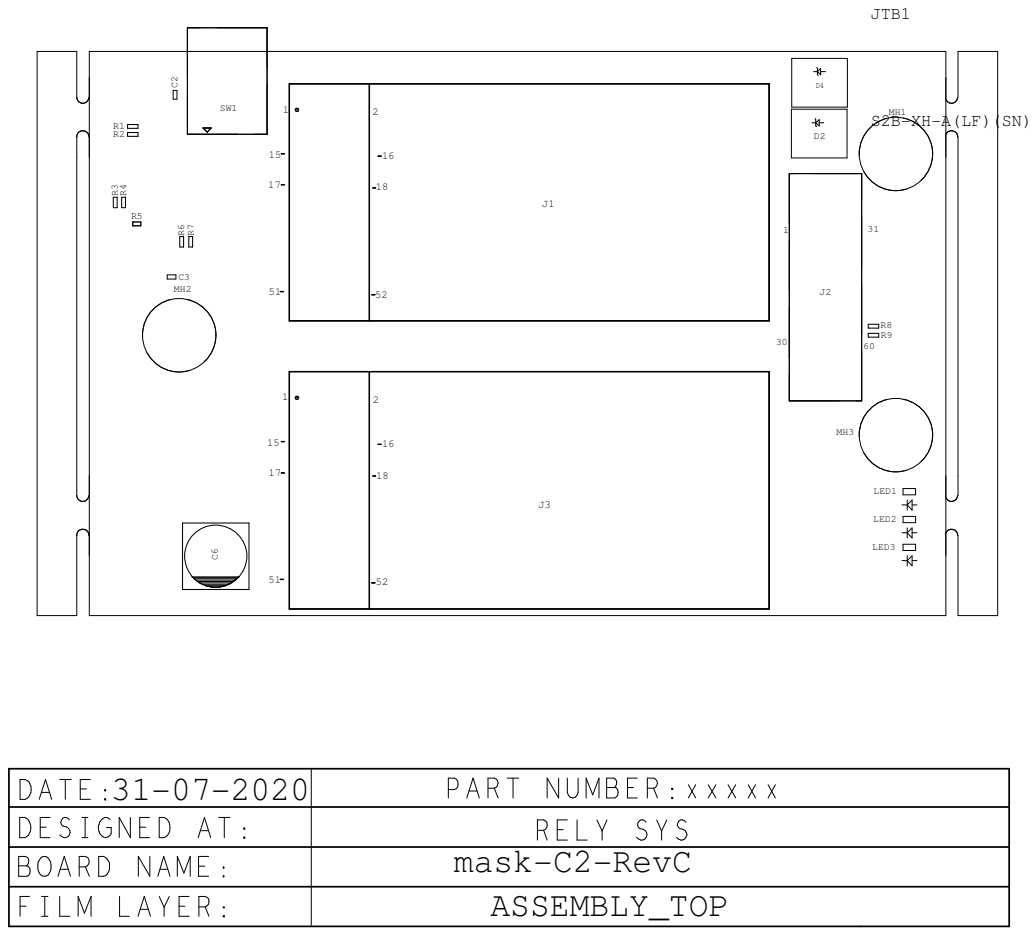
[picture p31: page 1]

mask-C2-RevC
ASSEMBLY_TOP
