ukama/ukama-nodes/electronics/mask/gerbers/mask-C2-RevC_FAB_NOTES.pdf

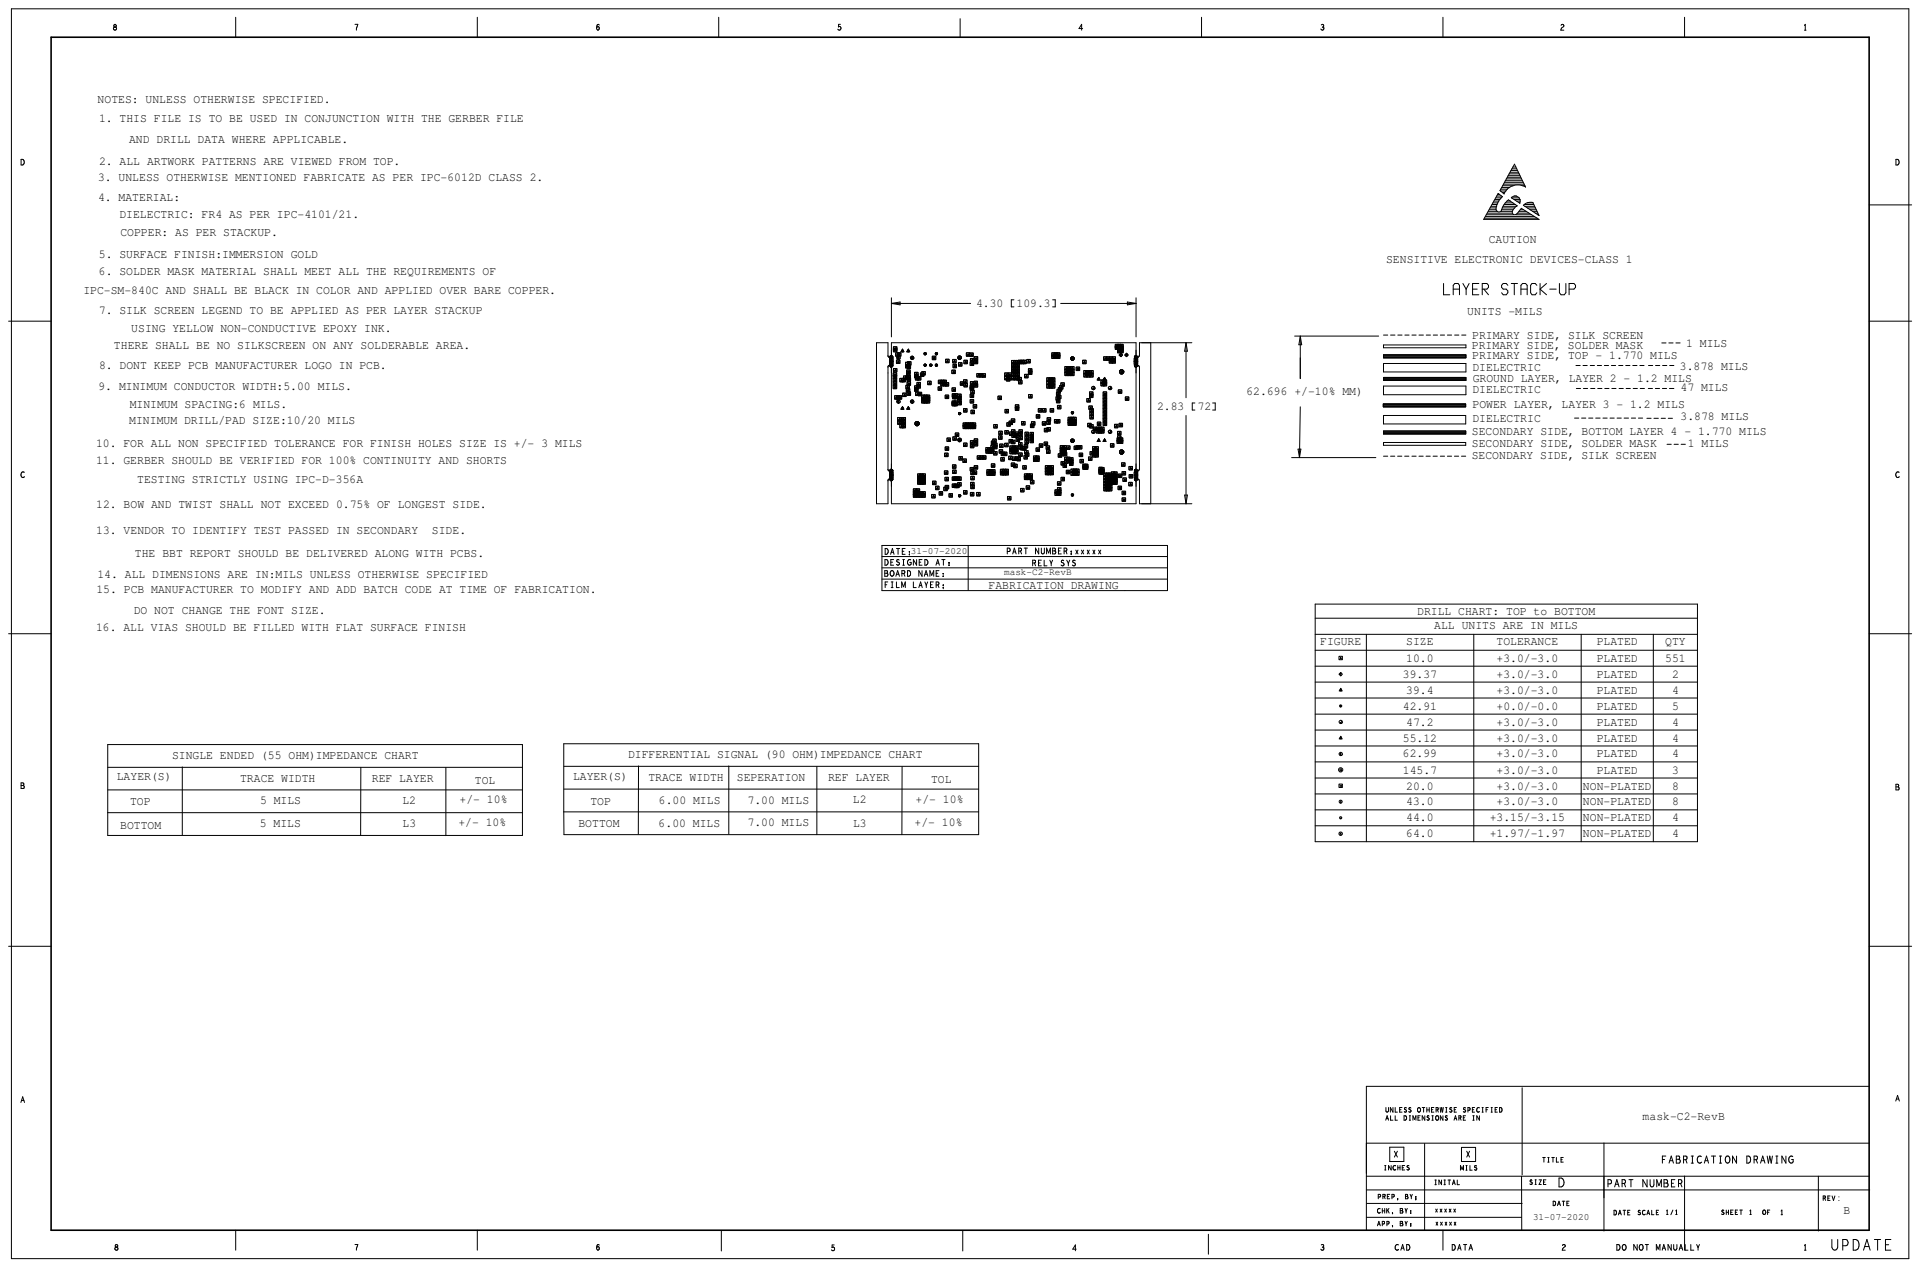
[picture p32: page 1]
mask-C2-RevB; BOTTOM; LAYER(S); TOP; TRACE WIDTH; 5 MILS; REF LAYER; TOL; 6.00 MILS; SEPERATION; 7.00 MILS; NON-PLATED; PLATED; 13. VENDOR TO IDENTIFY TEST PASSED IN SECONDARY; SIDE.; UNITS -MILS; CAUTION; 3.878 MILS; 47 MILS; 1 MILS

NOTES: UNLESS OTHERWISE SPECIFIED.
1. THIS FILE IS TO BE USED IN CONJUNCTION WITH THE GERBER FILE

AND DRILL DATA WHERE APPLICABLE.

2. ALL ARTWORK PATTERNS ARE VIEWED FROM TOP.
3. UNLESS OTHERWISE MENTIONED FABRICATE AS PER IPC-6012D CLASS 2.

4. MATERIAL:
DIELECTRIC: FR4 AS PER IPC-4101/21.
COPPER: AS PER STACKUP.

5. SURFACE FINISH:IMMERSION GOLD
6. SOLDER MASK MATERIAL SHALL MEET ALL THE REQUIREMENTS OF

SENSITIVE ELECTRONIC DEVICES-CLASS 1

IPC-SM-840C AND SHALL BE BLACK IN COLOR AND APPLIED OVER BARE COPPER.

7. SILK SCREEN LEGEND TO BE APPLIED AS PER LAYER STACKUP

USING YELLOW NON-CONDUCTIVE EPOXY INK.
THERE SHALL BE NO SILKSCREEN ON ANY SOLDERABLE AREA.

PRIMARY SIDE, SILK SCREEN
PRIMARY SIDE, SOLDER MASK
PRIMARY SIDE, TOP - 1.770 MILS
DIELECTRIC
GROUND LAYER, LAYER 2 - 1.2 MILS
POWER LAYER, LAYER 3 - 1.2 MILS
SECONDARY SIDE, BOTTOM LAYER 4 - 1.770 MILS
SECONDARY SIDE, SOLDER MASK
SECONDARY SIDE, SILK SCREEN

8. DONT KEEP PCB MANUFACTURER LOGO IN PCB.

9. MINIMUM CONDUCTOR WIDTH:5.00 MILS.

MINIMUM SPACING:6 MILS.
MINIMUM DRILL/PAD SIZE:10/20 MILS

10. FOR ALL NON SPECIFIED TOLERANCE FOR FINISH HOLES SIZE IS +/- 3 MILS
11. GERBER SHOULD BE VERIFIED FOR 100% CONTINUITY AND SHORTS

TESTING STRICTLY USING IPC-D-356A

12. BOW AND TWIST SHALL NOT EXCEED 0.75% OF LONGEST SIDE.

THE BBT REPORT SHOULD BE DELIVERED ALONG WITH PCBS.

14. ALL DIMENSIONS ARE IN:MILS UNLESS OTHERWISE SPECIFIED
15. PCB MANUFACTURER TO MODIFY AND ADD BATCH CODE AT TIME OF FABRICATION.

mask-C2-RevB
FABRICATION DRAWING

DO NOT CHANGE THE FONT SIZE.

DRILL CHART: TOP to BOTTOM
ALL UNITS ARE IN MILS

16. ALL VIAS SHOULD BE FILLED WITH FLAT SURFACE FINISH

FIGURE | SIZE | TOLERANCE | PLATED | QTY

10.0 | +3.0/-3.0 | PLATED | 551
39.37 | +3.0/-3.0 | PLATED | 2
39.4 | +3.0/-3.0 | PLATED | 4
42.91 | +0.0/-0.0 | PLATED | 5
47.2 | +3.0/-3.0 | PLATED | 4
55.12 | +3.0/-3.0 | PLATED | 4

SINGLE ENDED (55 OHM)IMPEDANCE CHART

DIFFERENTIAL SIGNAL (90 OHM)IMPEDANCE CHART

145.7 | +3.0/-3.0 | PLATED | 3
20.0 | +3.0/-3.0 | NON-PLATED | 8
