ukama/ukama-nodes/electronics/mask/placement/mask_placement_top.pdf

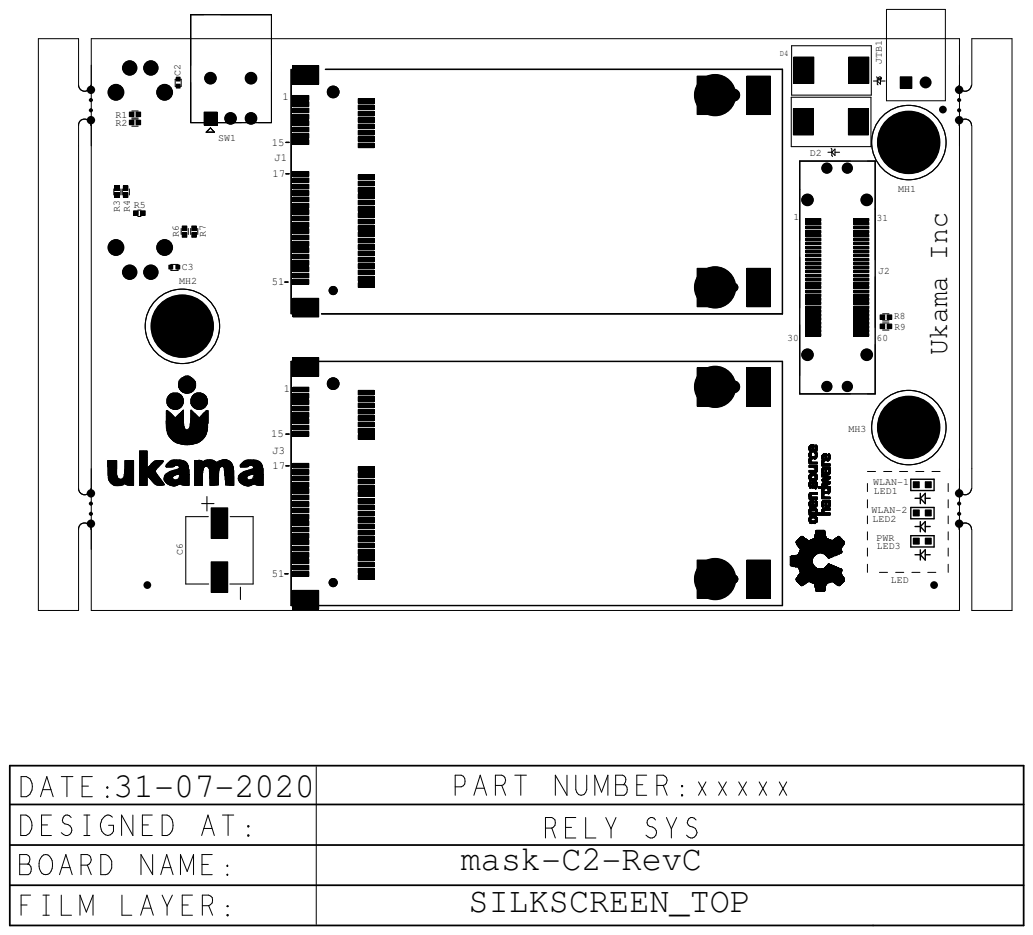
[picture p33: page 1]

mask-C2-RevC
SILKSCREEN_TOP
