ukama/ukama-nodes/electronics/mask/schematics/mask_schematic.pdf

# R E V I S I O N C

# Product name: TowerNode

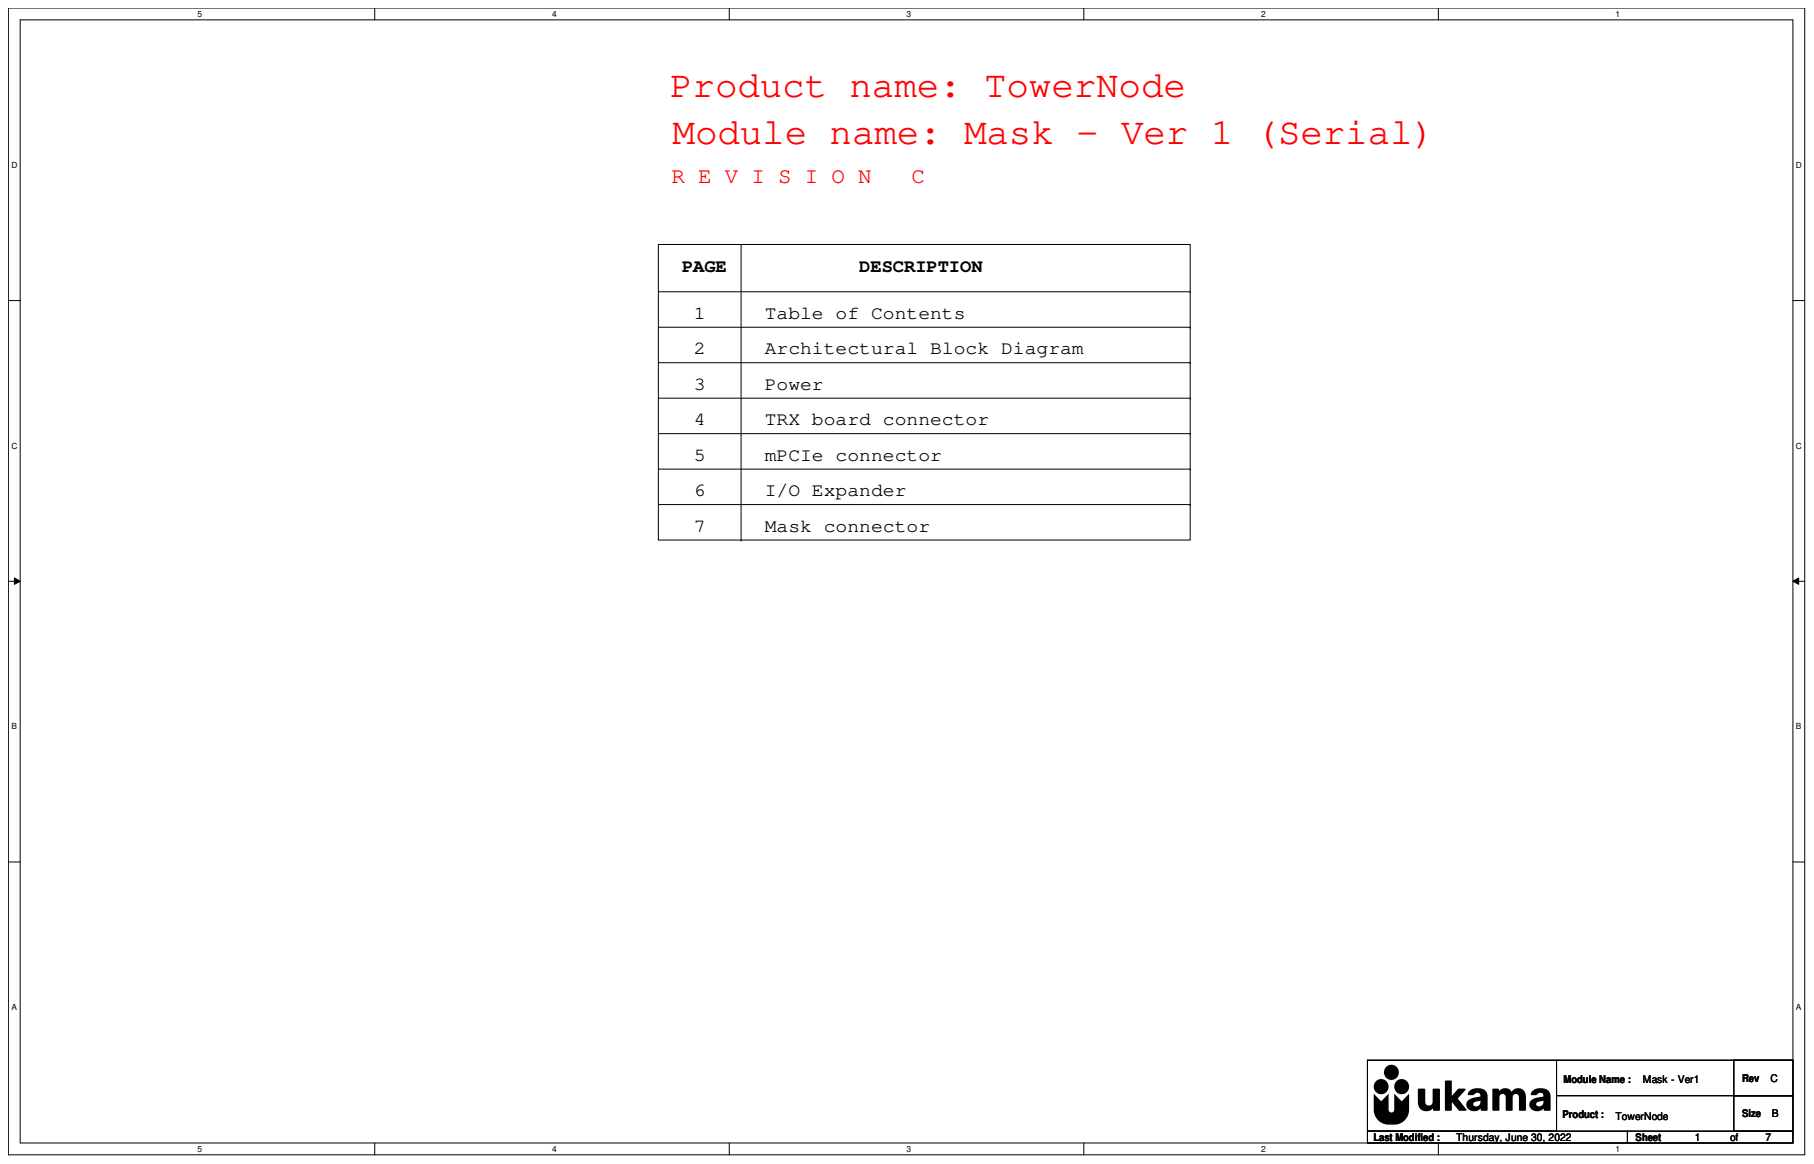
[picture p34: page 1]
PAGE; DESCRIPTION; Power; I/O Expander; Mask connector; mPCIe connector; Product :; Size; Rev; Last Modified :; Sheet; Module Name :; 1 7Thursday, June 30, 2022; TowerNode; Mask - Ver1

Module name: Mask - Ver 1 (Serial)

Table of Contents

Architectural Block Diagram

TRX board connector

# Architectural block diagram

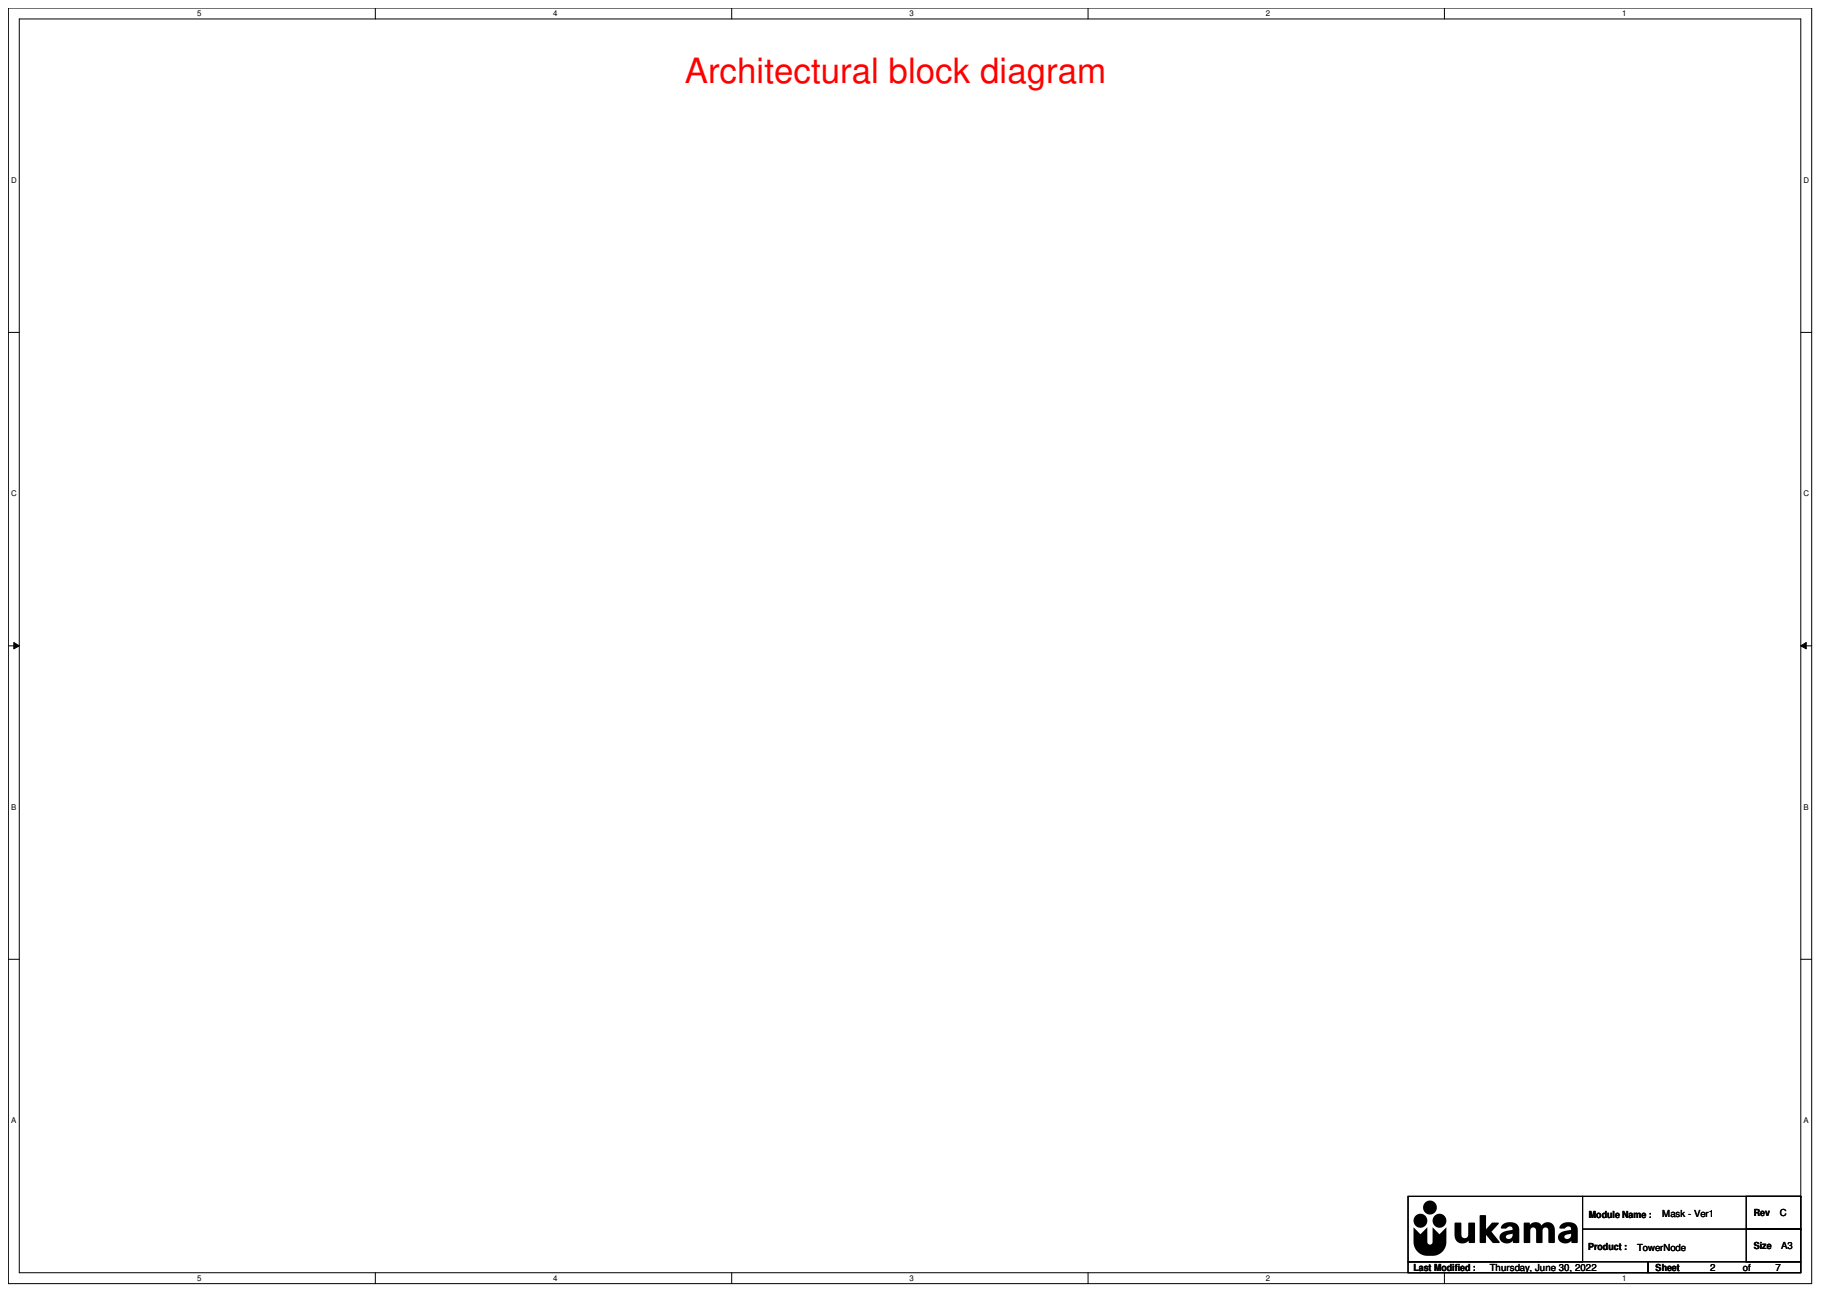
[picture p35: page 2]
Product :; Size; Rev; Last Modified :; Sheet; Module Name :; 2 7Thursday, June 30, 2022; TowerNode; Mask - Ver1

# 3V3 Converter

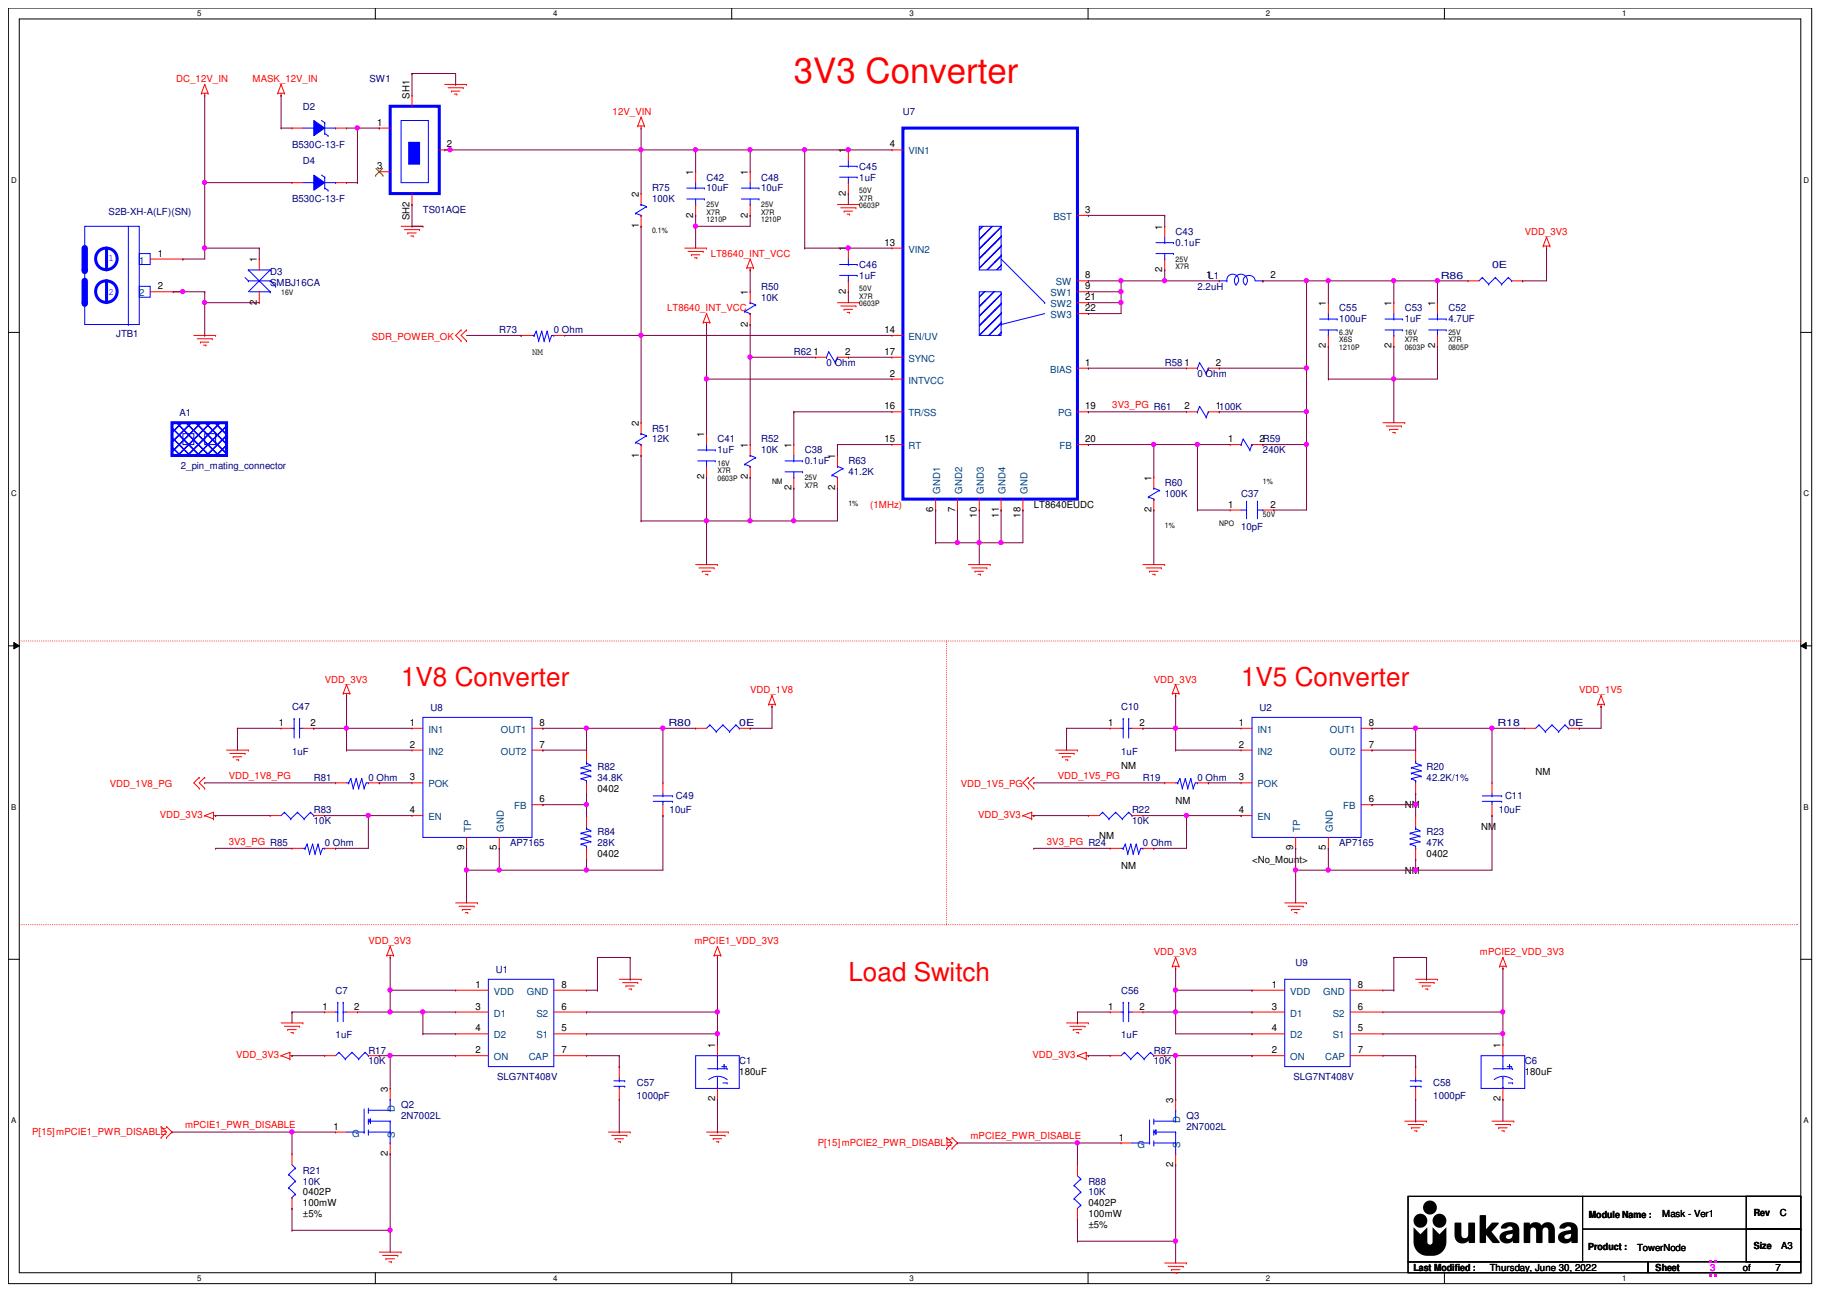
[picture p36: page 3]

TRX Board connector | Mounting holes

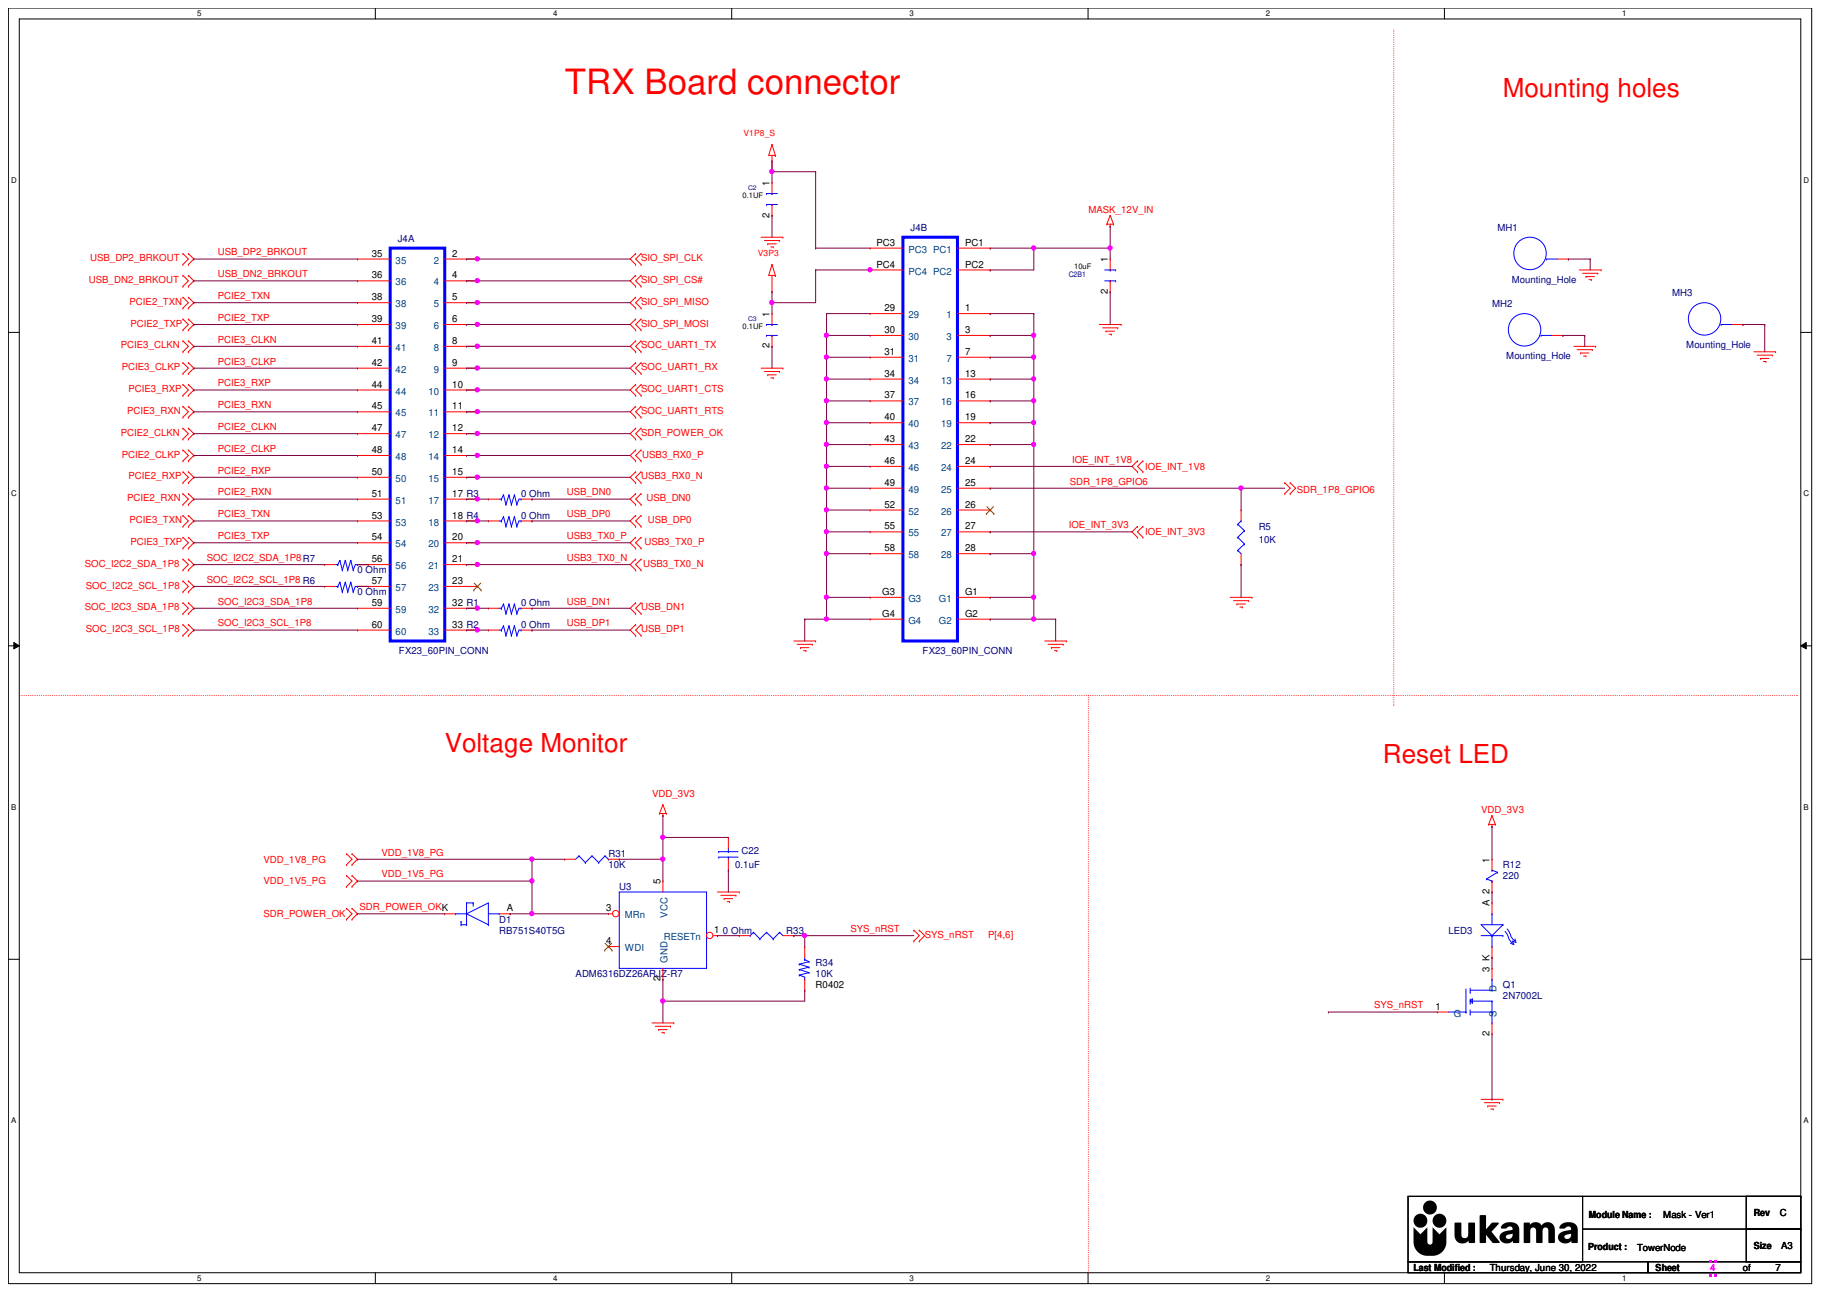
[picture p37: page 4]

# mPCIe connector - 1

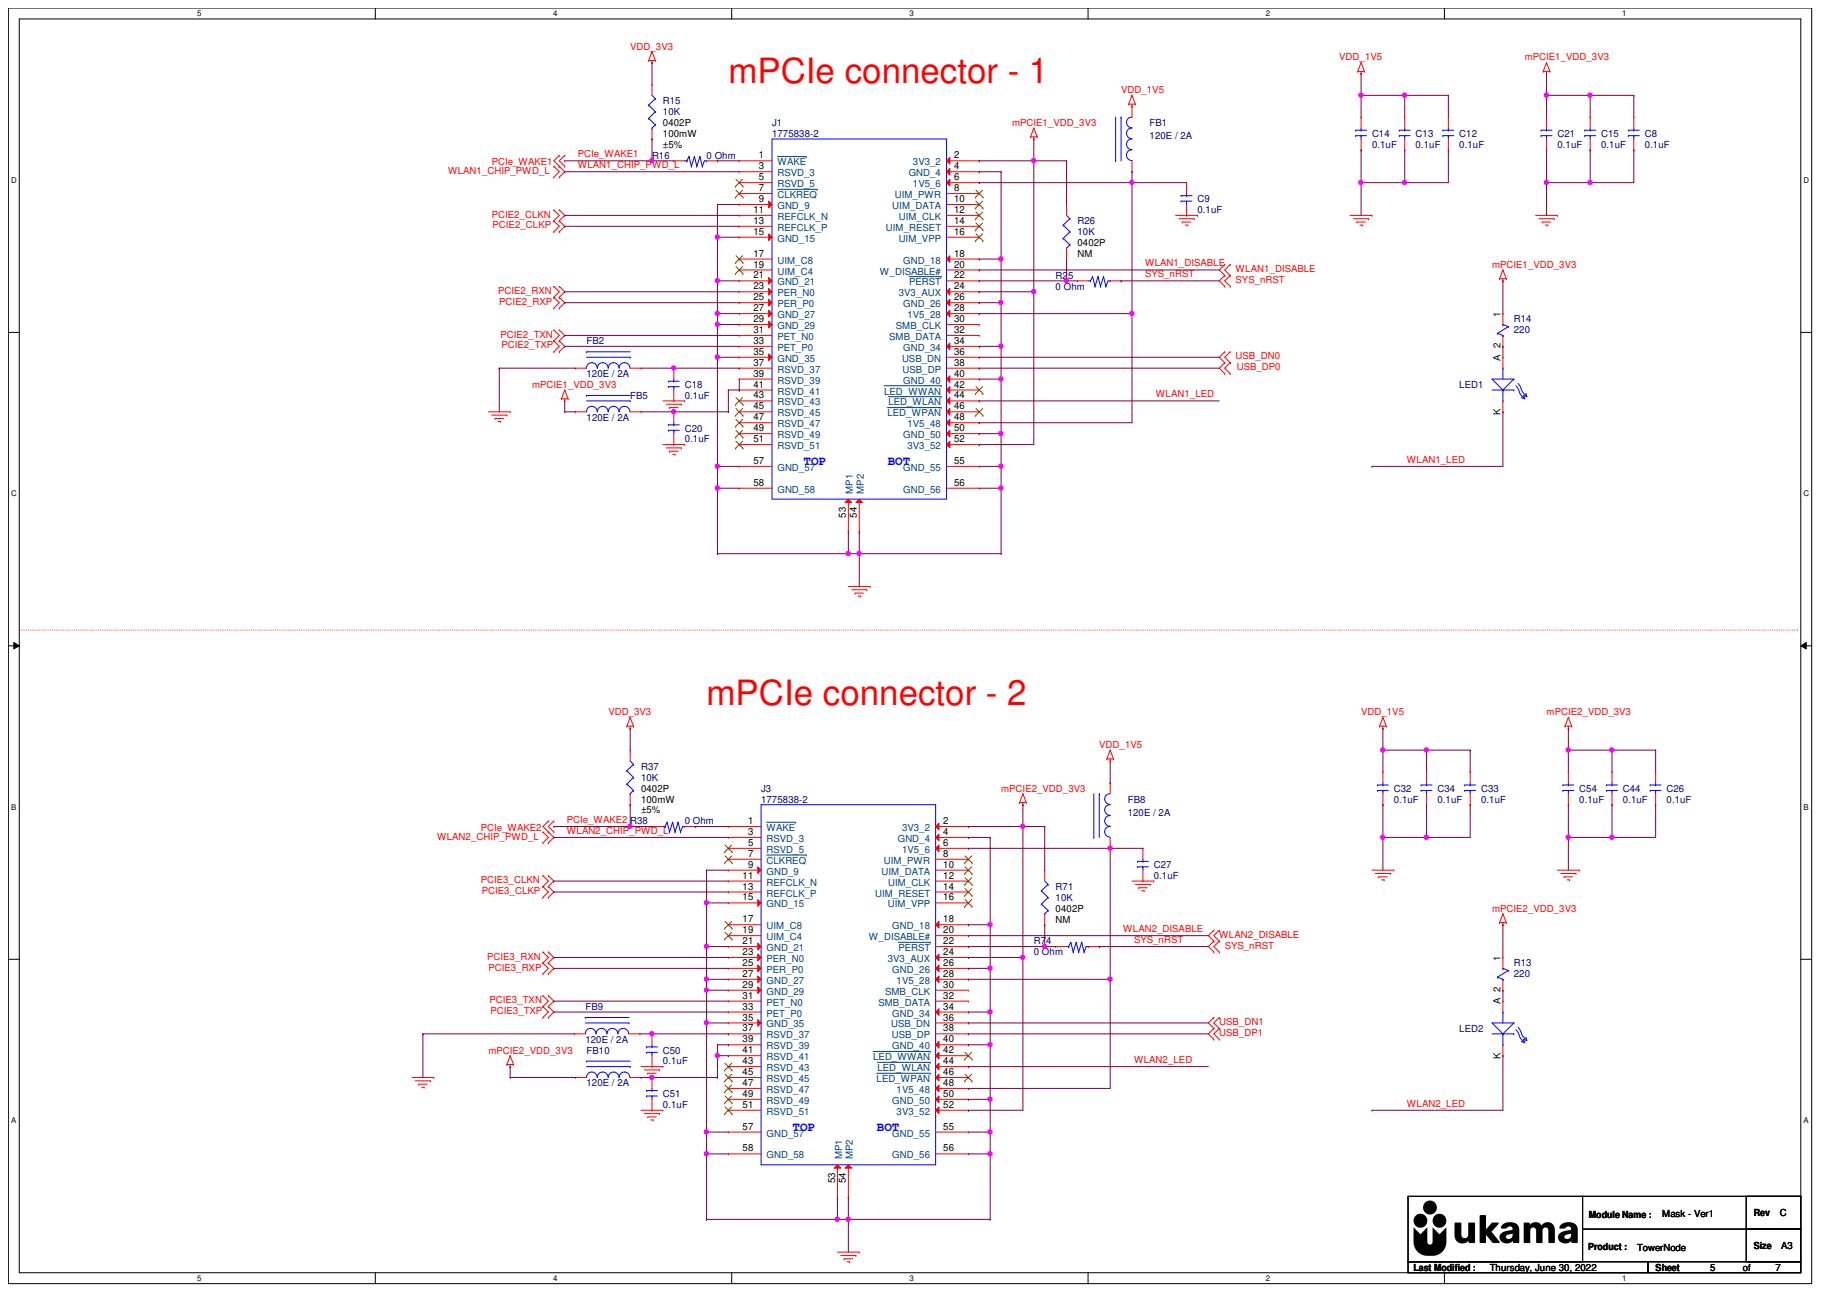
[picture p38: page 5]

# I/O Expander

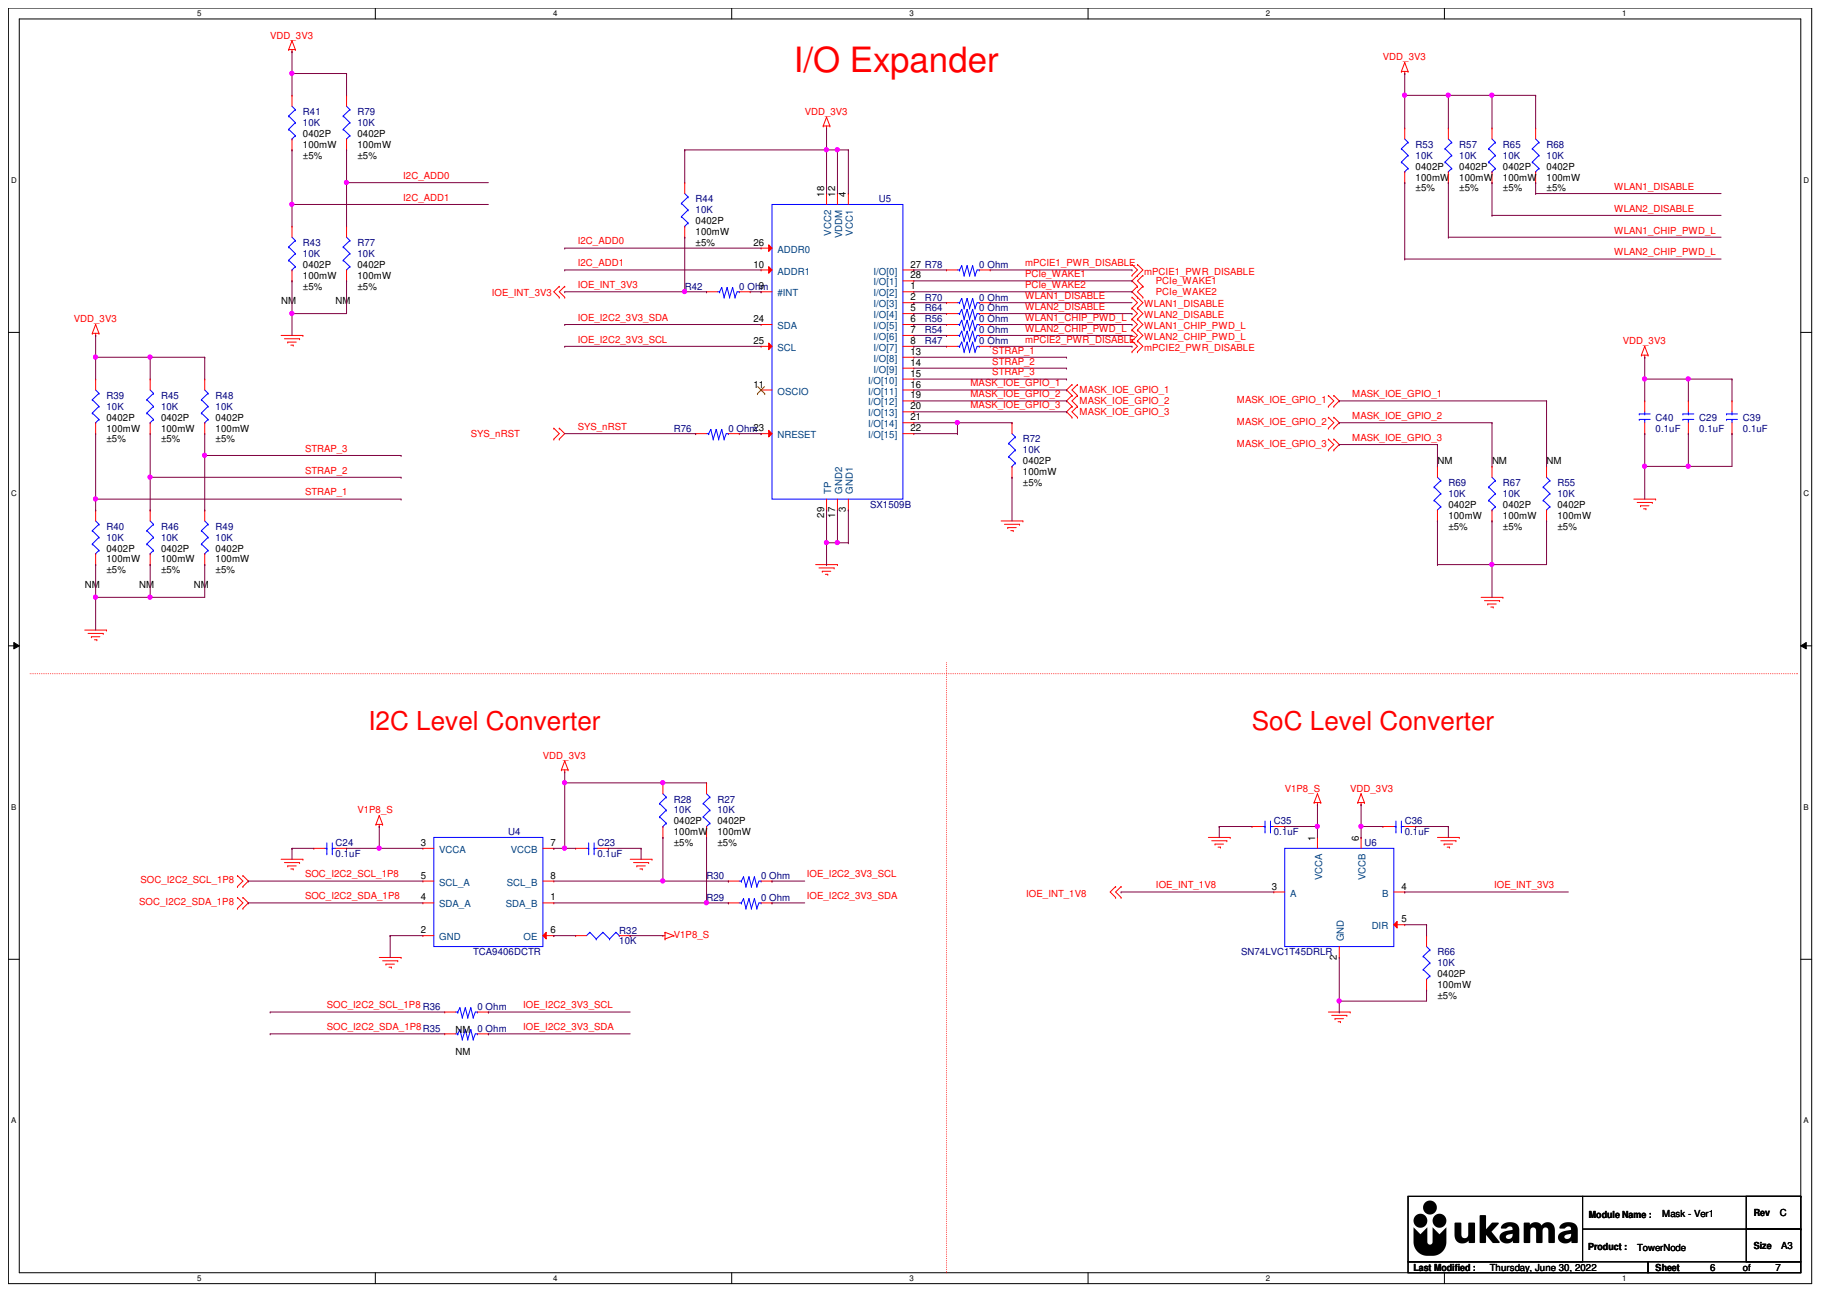
[picture p39: page 6]

# Mask connector

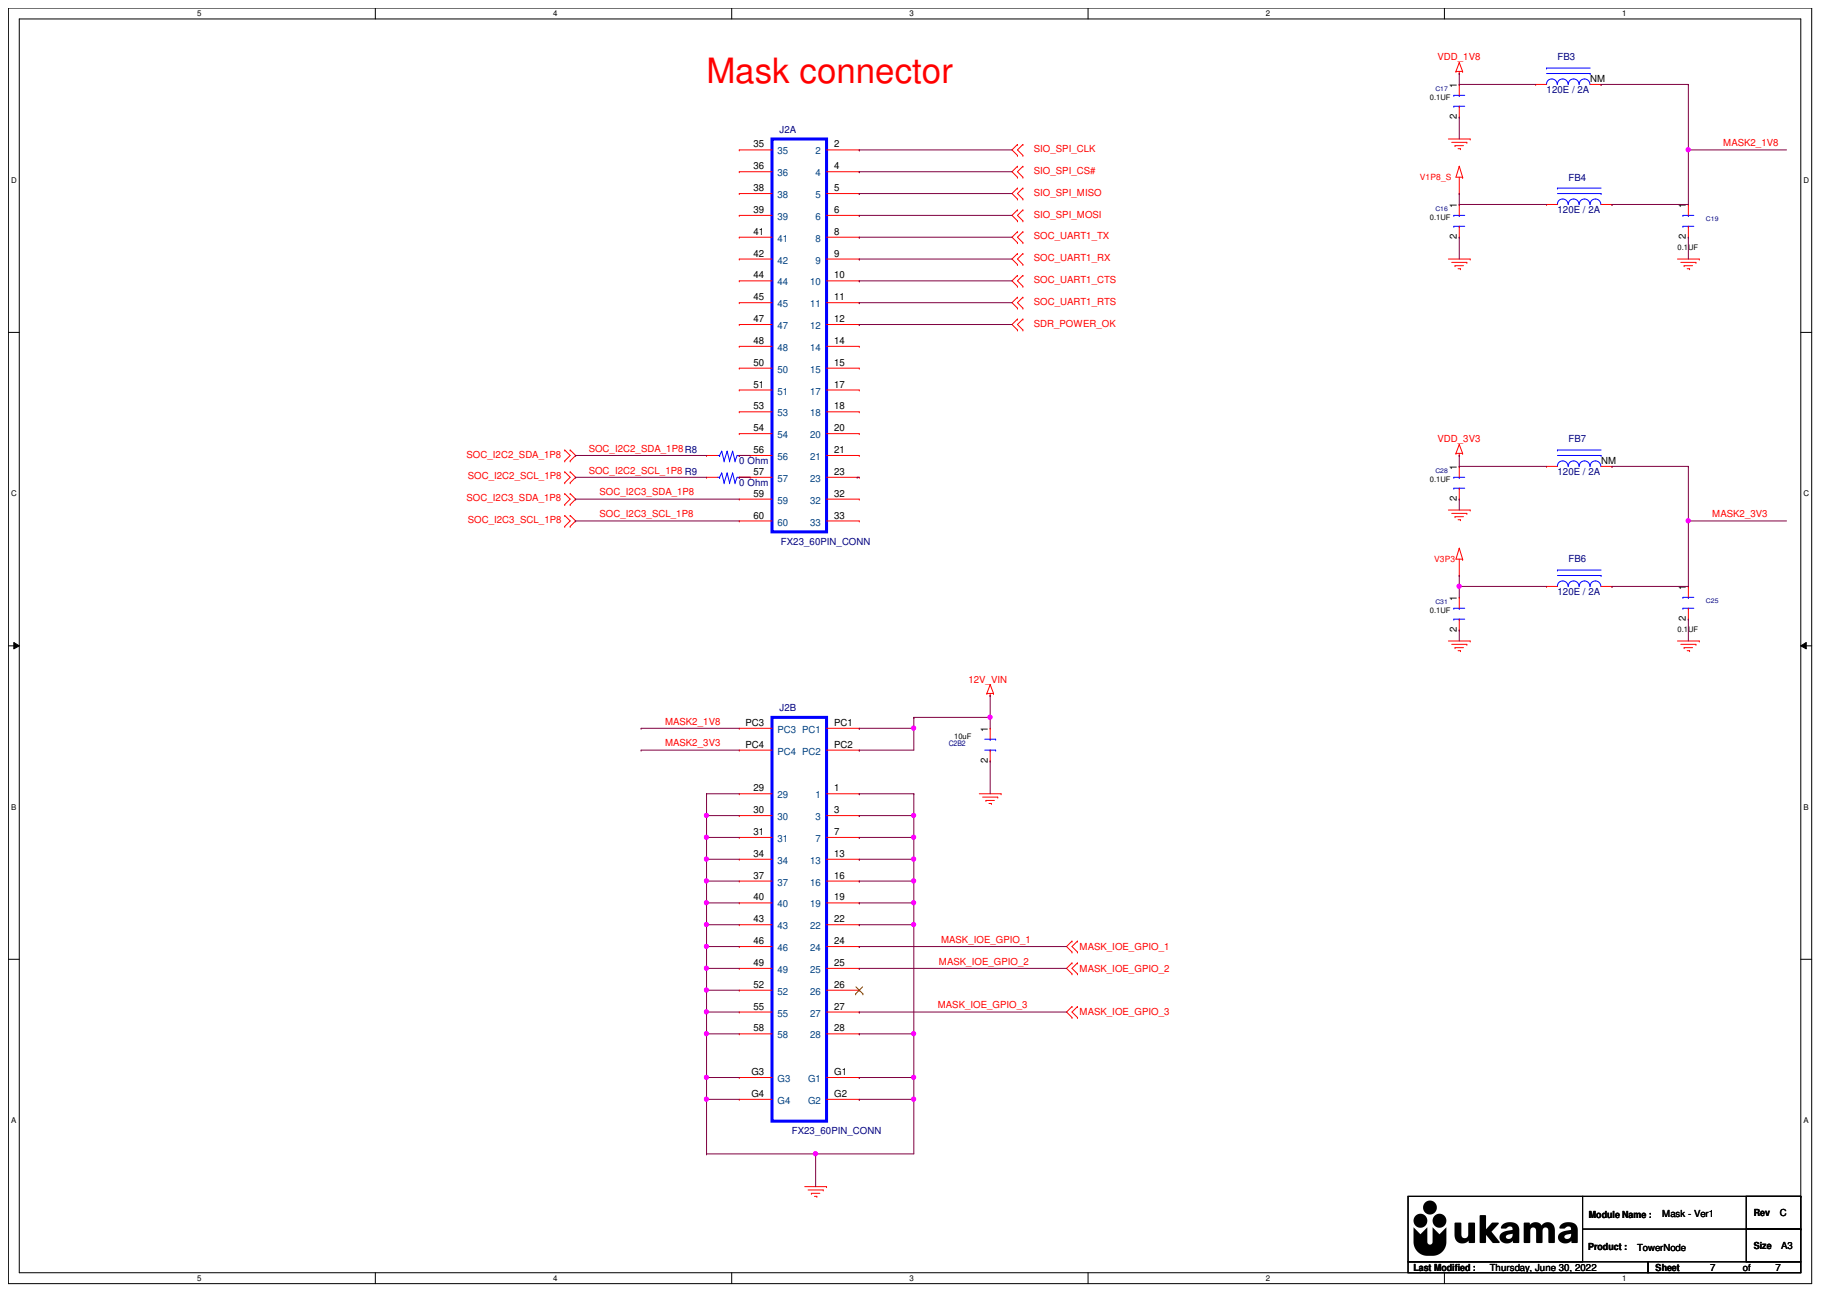
[picture p40: page 7]
