ukama/ukama-nodes/electronics/com/placement/com_placement_top.pdf

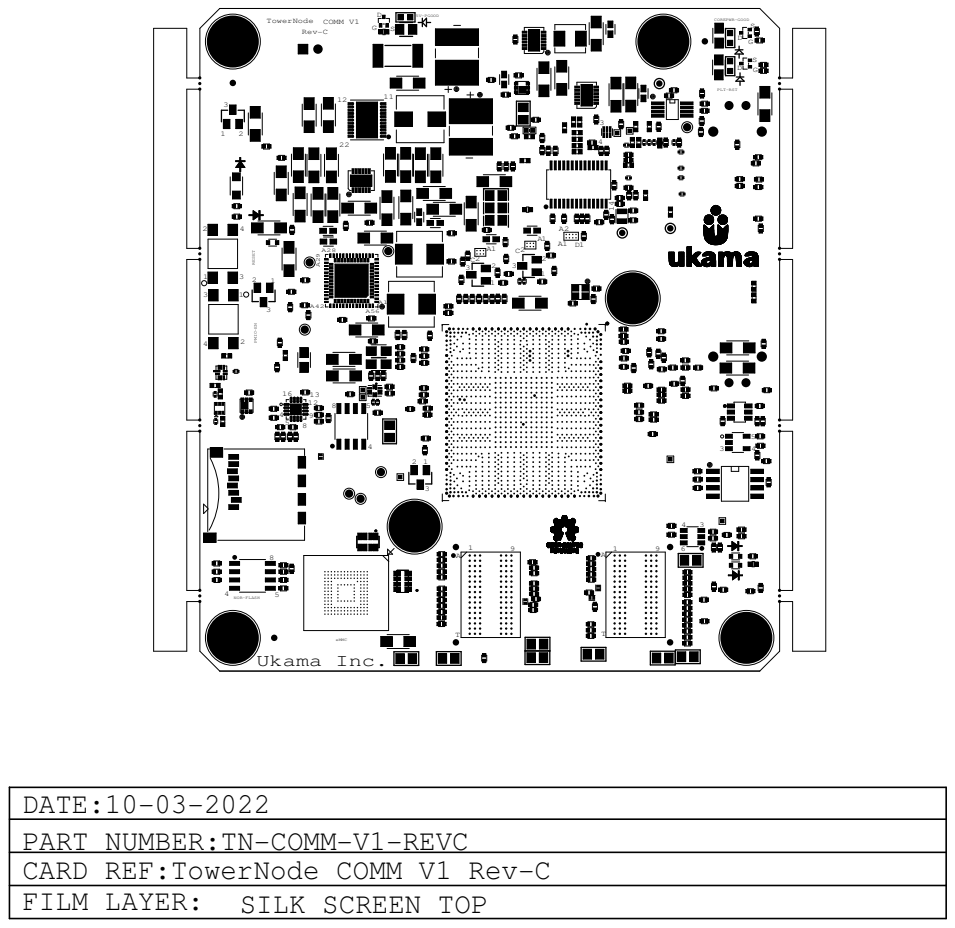
[picture p41: page 1]
DATE:10-03-2022; PLT-RST; COREPWR-GOOD; 5V-PGOOD; TowerNode; COMM V1; Rev-C; eMMC; Ukama Inc.; NOR-FLASH; PMIC-EN; RESET

PART NUMBER:TN-COMM-V1-REVC
CARD REF:TowerNode COMM V1 Rev-C
FILM LAYER:

SILK SCREEN TOP
