ukama/ukama-nodes/electronics/trx/assembly/trx_ast.pdf

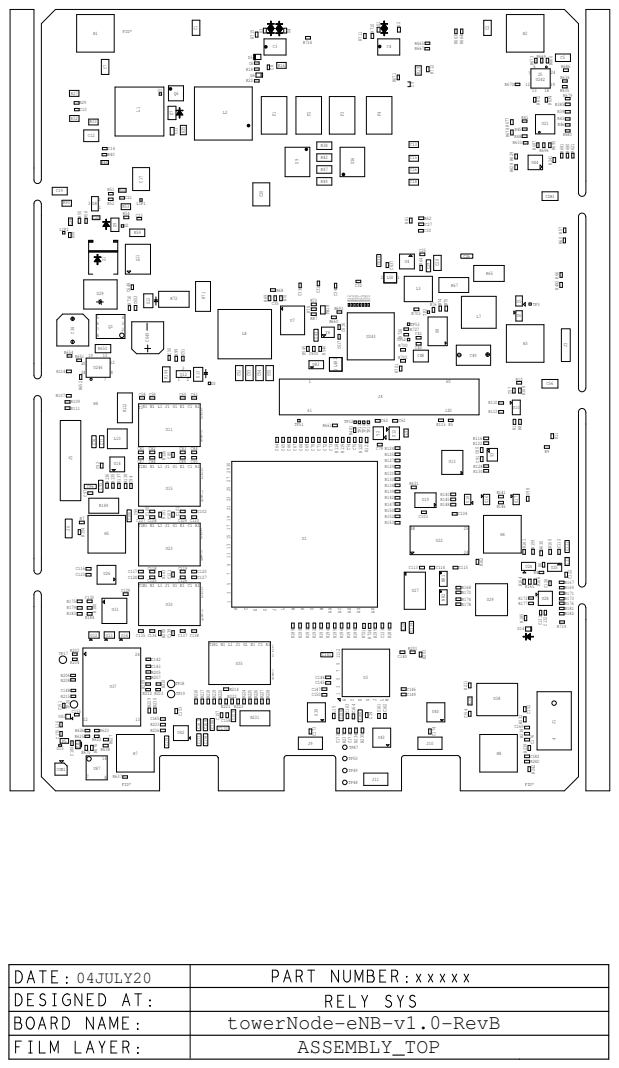
[picture p42: page 1]

towerNode-eNB-v1.0-RevB

ASSEMBLY_TOP
