ukama/ukama-nodes/electronics/trx/placement/trx_placement_bot.pdf

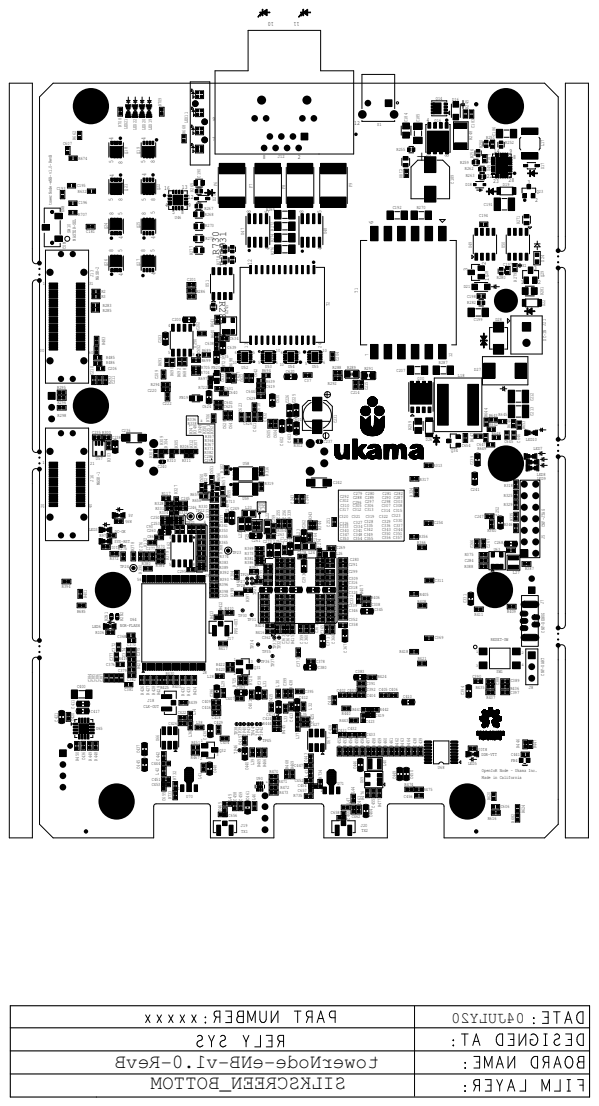
[picture p43: page 1]

DC-IN CNF-DEBUG

CNF-UART CNF-JTAG

OpenIoR Node - Ukama Inc.
Made in California
