ukama/ukama-nodes/electronics/trx/placement/trx_placement_top.pdf

2

3

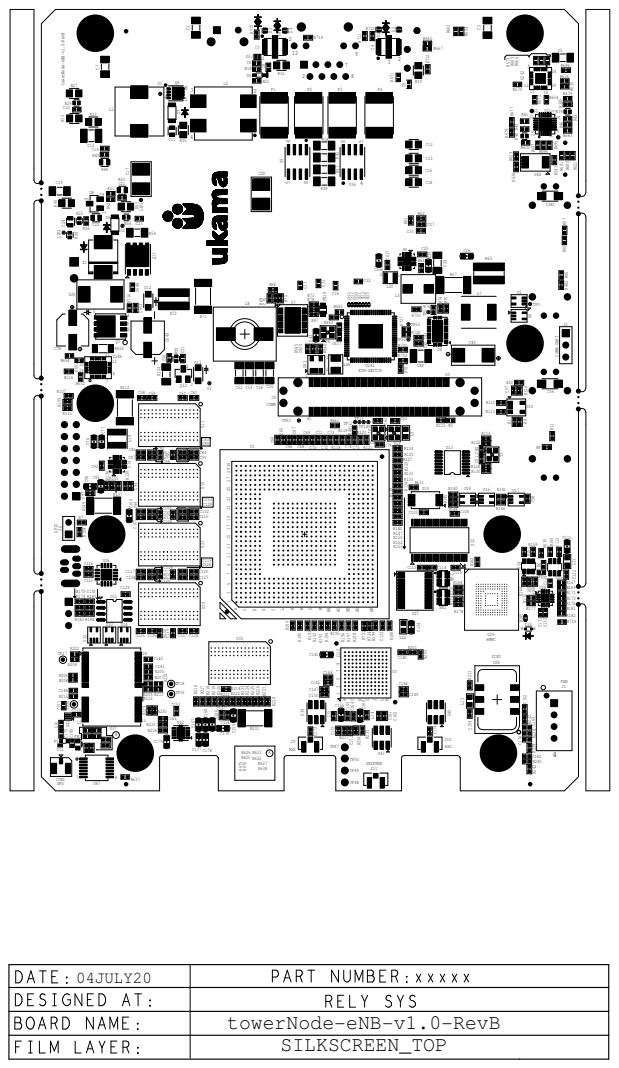
[picture p44: page 1]

towerNode-eNB-v1.0-RevB

SILKSCREEN_TOP
