ukama/ukama-nodes/electronics/ctrl/schematics/controller_schematic.pdf

# Module name: CTRL

# Product name: AmplifierNode

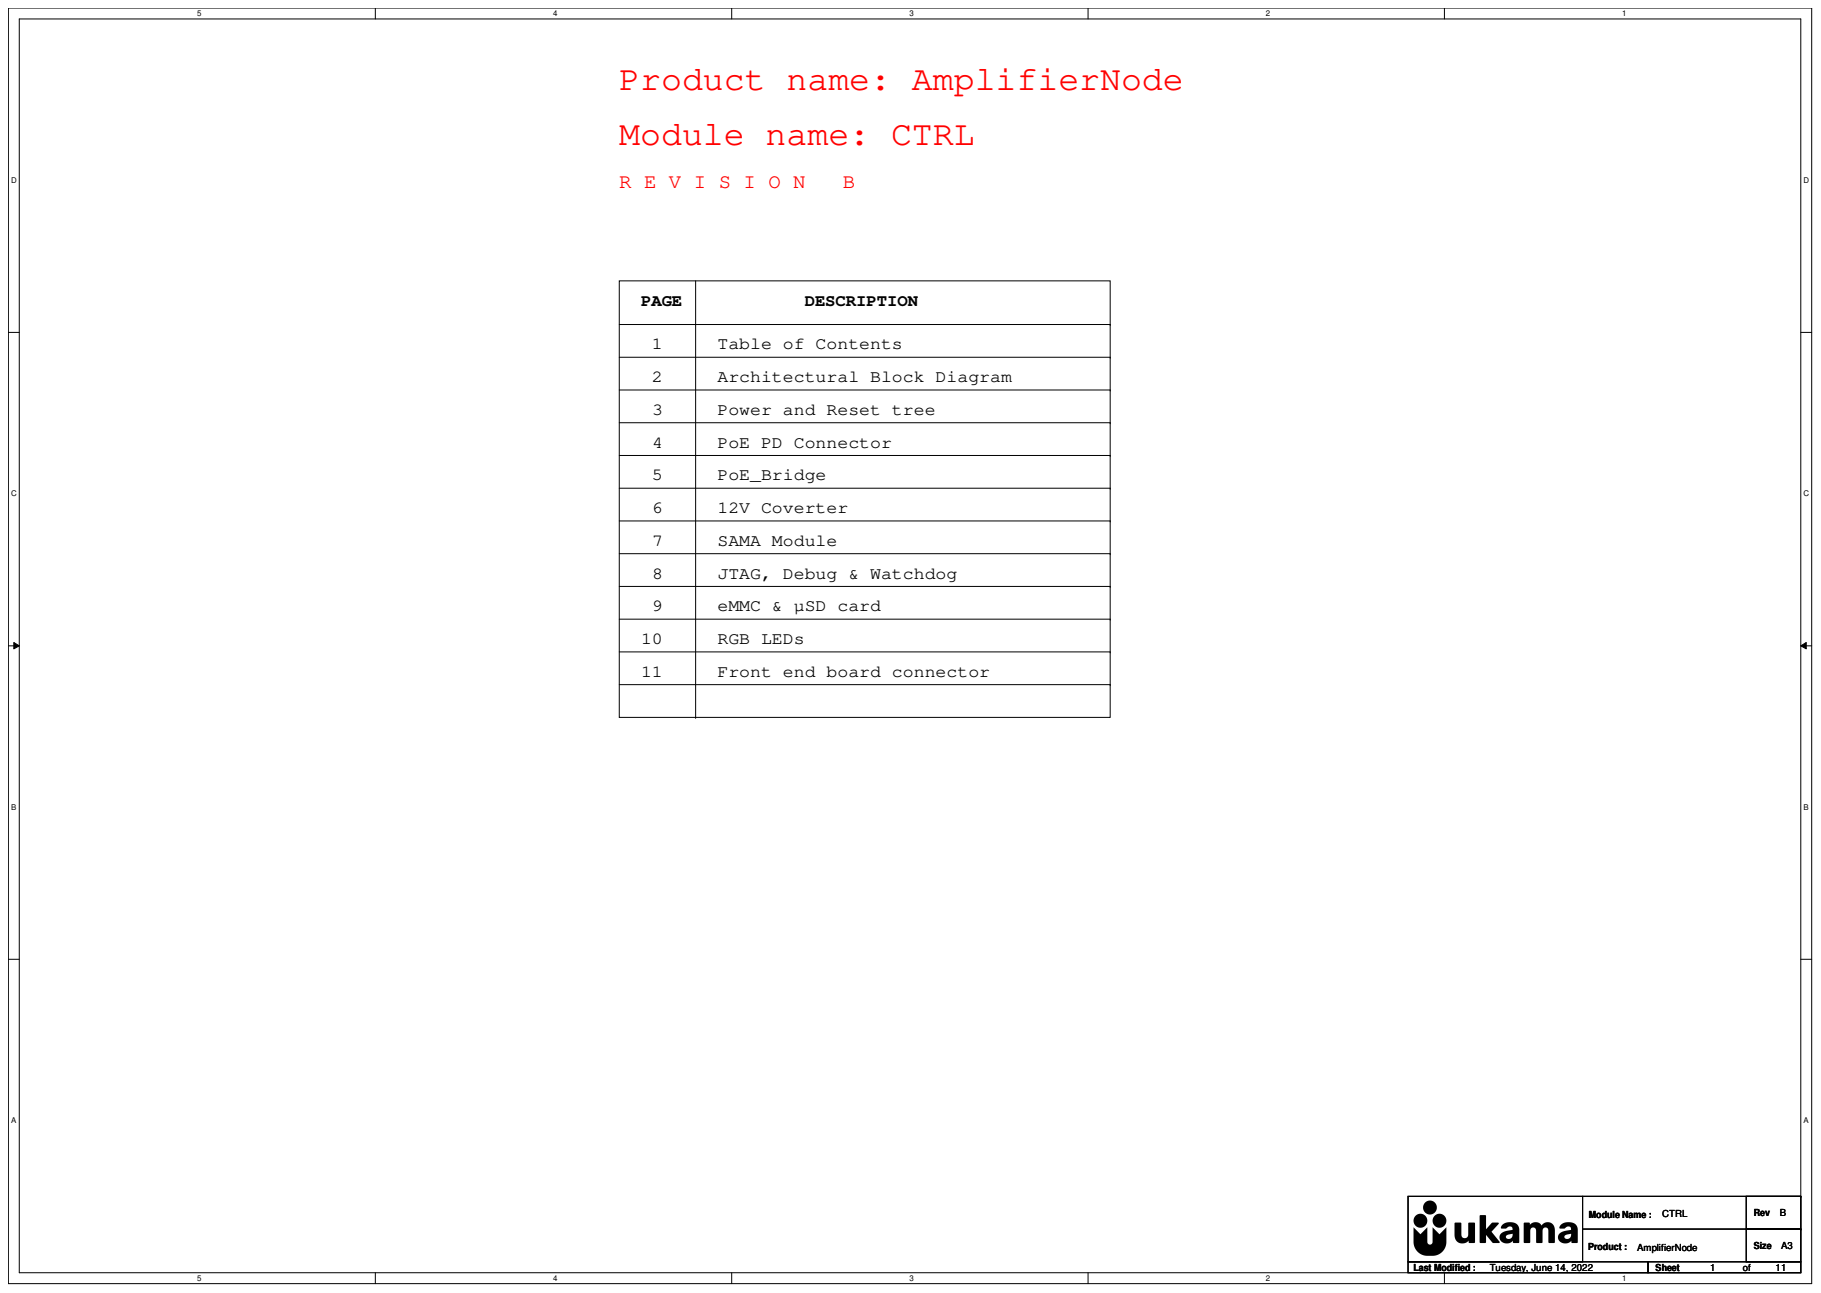
[picture p46: page 1]
PoE_Bridge; 12V Coverter; RGB LEDs; SAMA Module; PAGE; DESCRIPTION; Product :; Size; Rev; Last Modified :; Sheet; Module Name :; 1 11Tuesday, June 14, 2022; AmplifierNode; CTRL

Table of Contents

Architectural Block Diagram

Power and Reset tree

PoE PD Connector

JTAG, Debug & Watchdog

eMMC & µSD card

Front end board connector

# Architectural block diagram

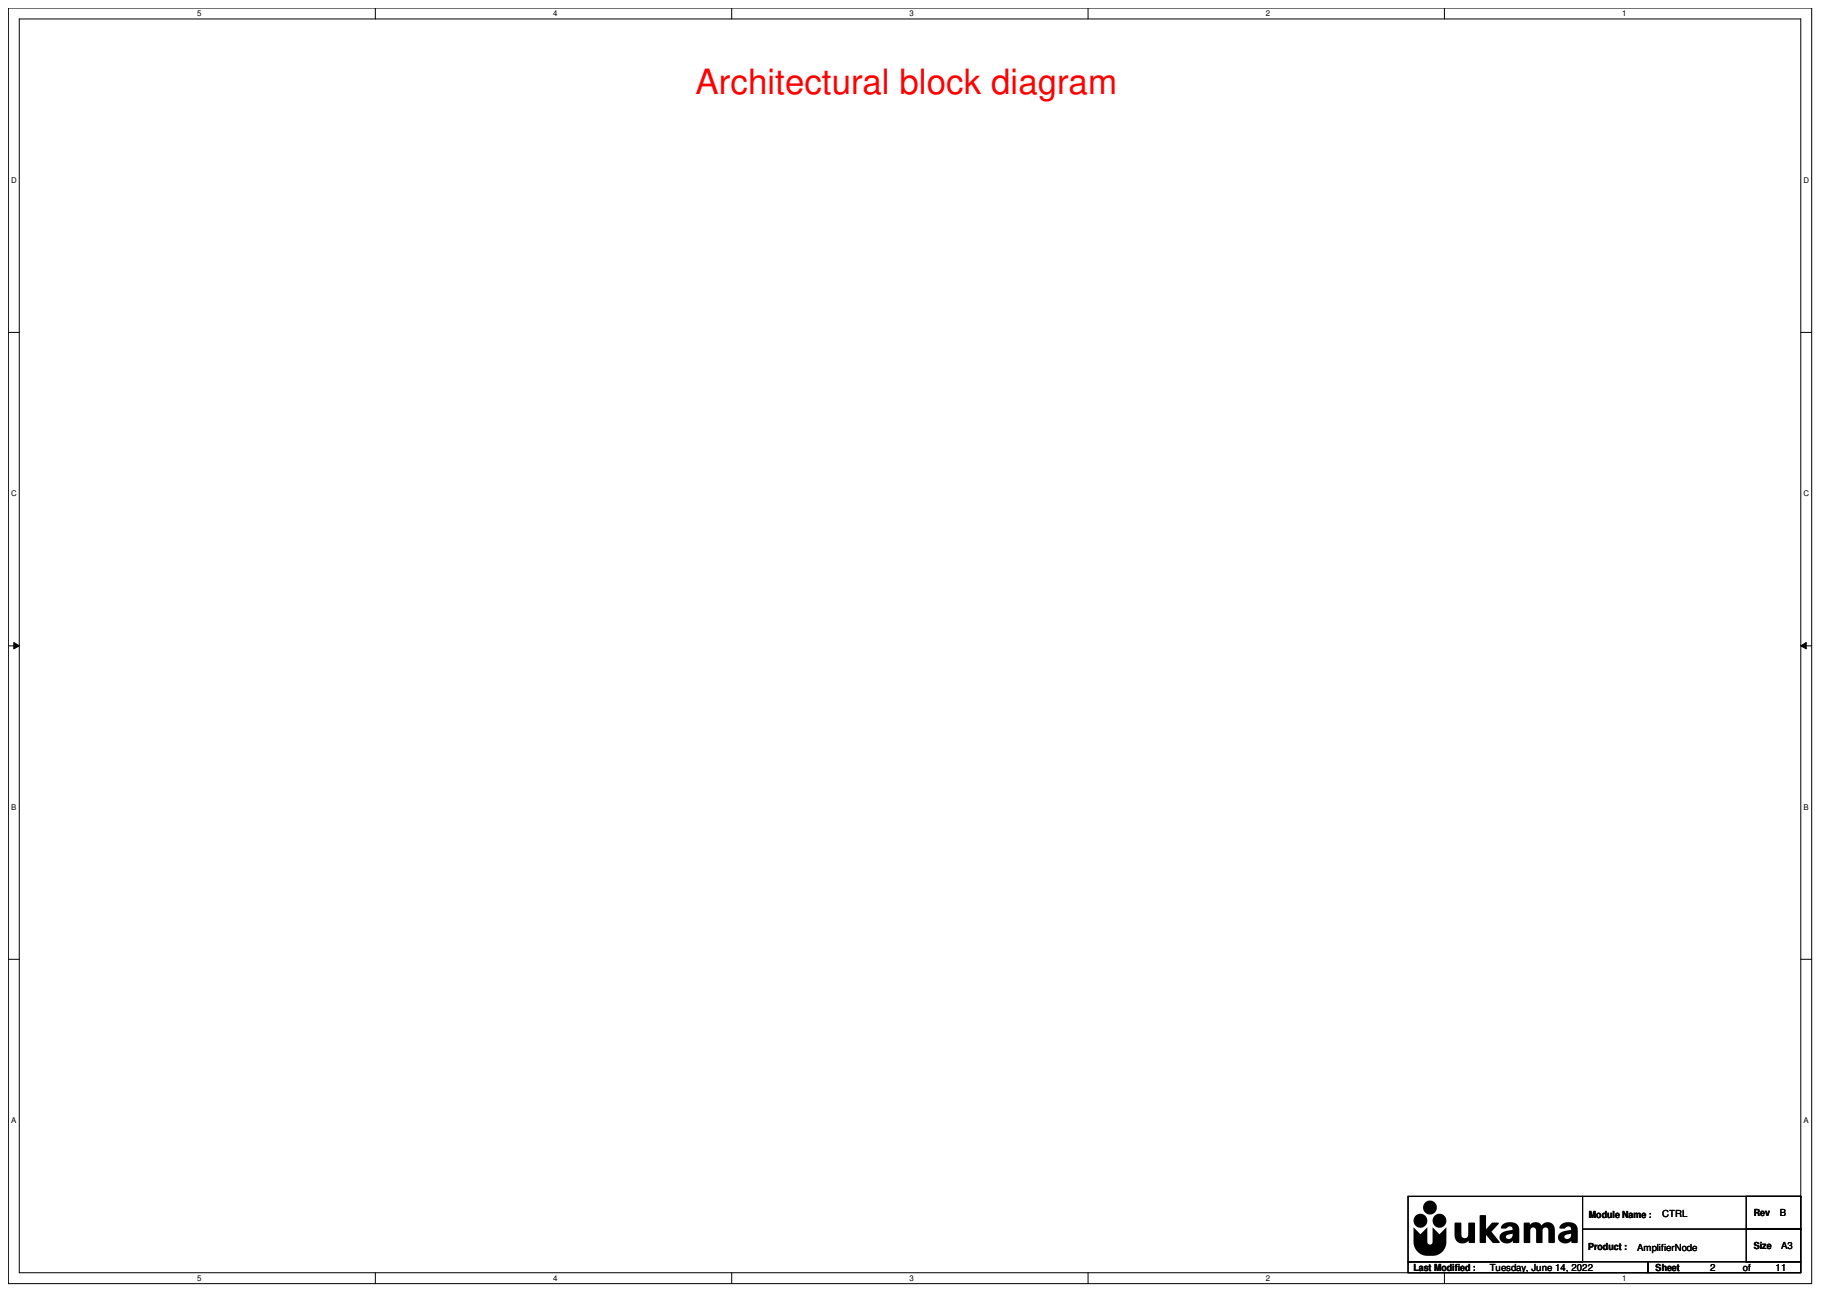
[picture p47: page 2]
Product :; Size; Rev; Last Modified :; Sheet; Module Name :; 2 11Tuesday, June 14, 2022; AmplifierNode; CTRL

# Power & Reset tree

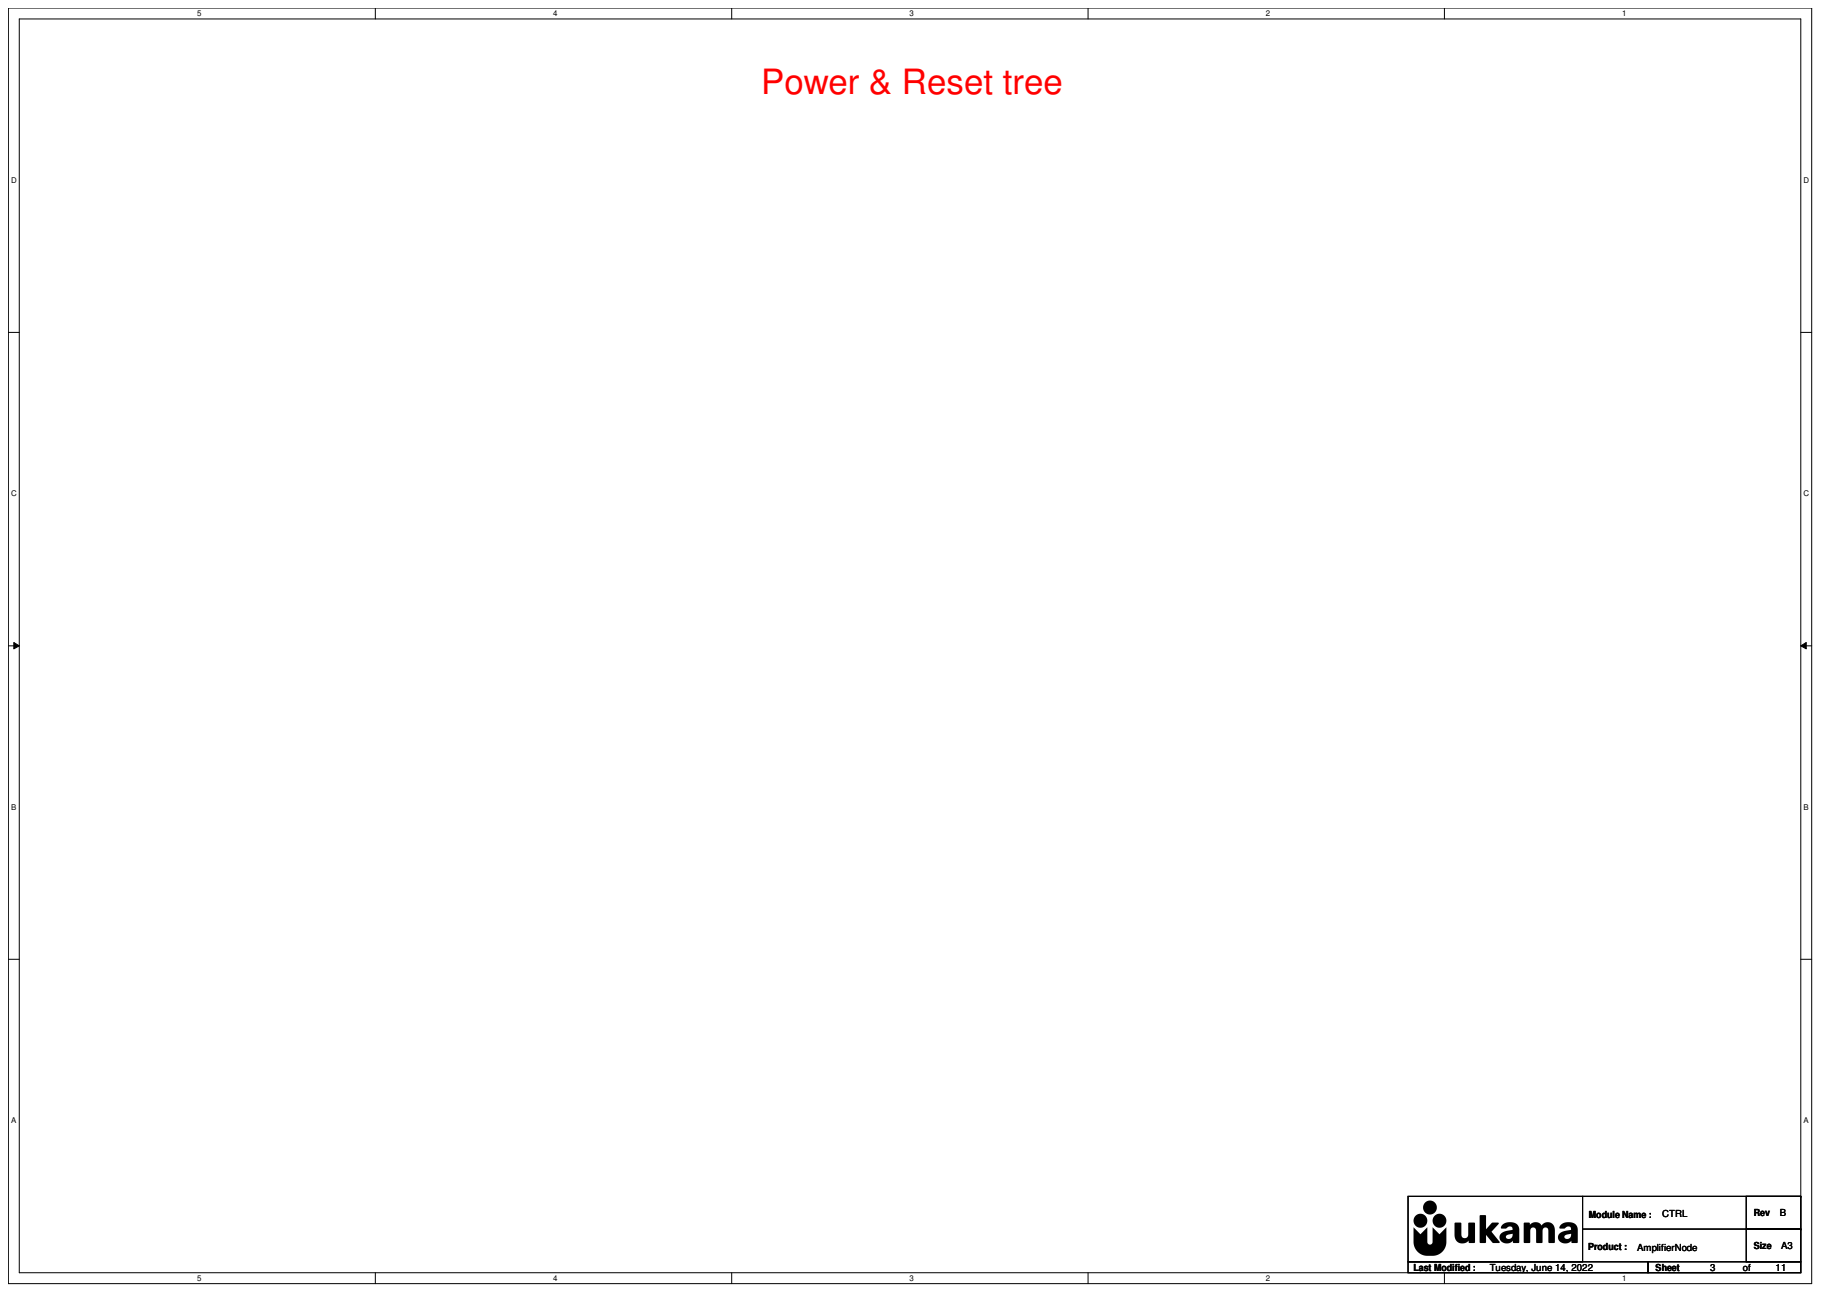
[picture p48: page 3]
Product :; Size; Rev; Last Modified :; Sheet; Module Name :; 3 11Tuesday, June 14, 2022; AmplifierNode; CTRL

# PoE PD Port Connector

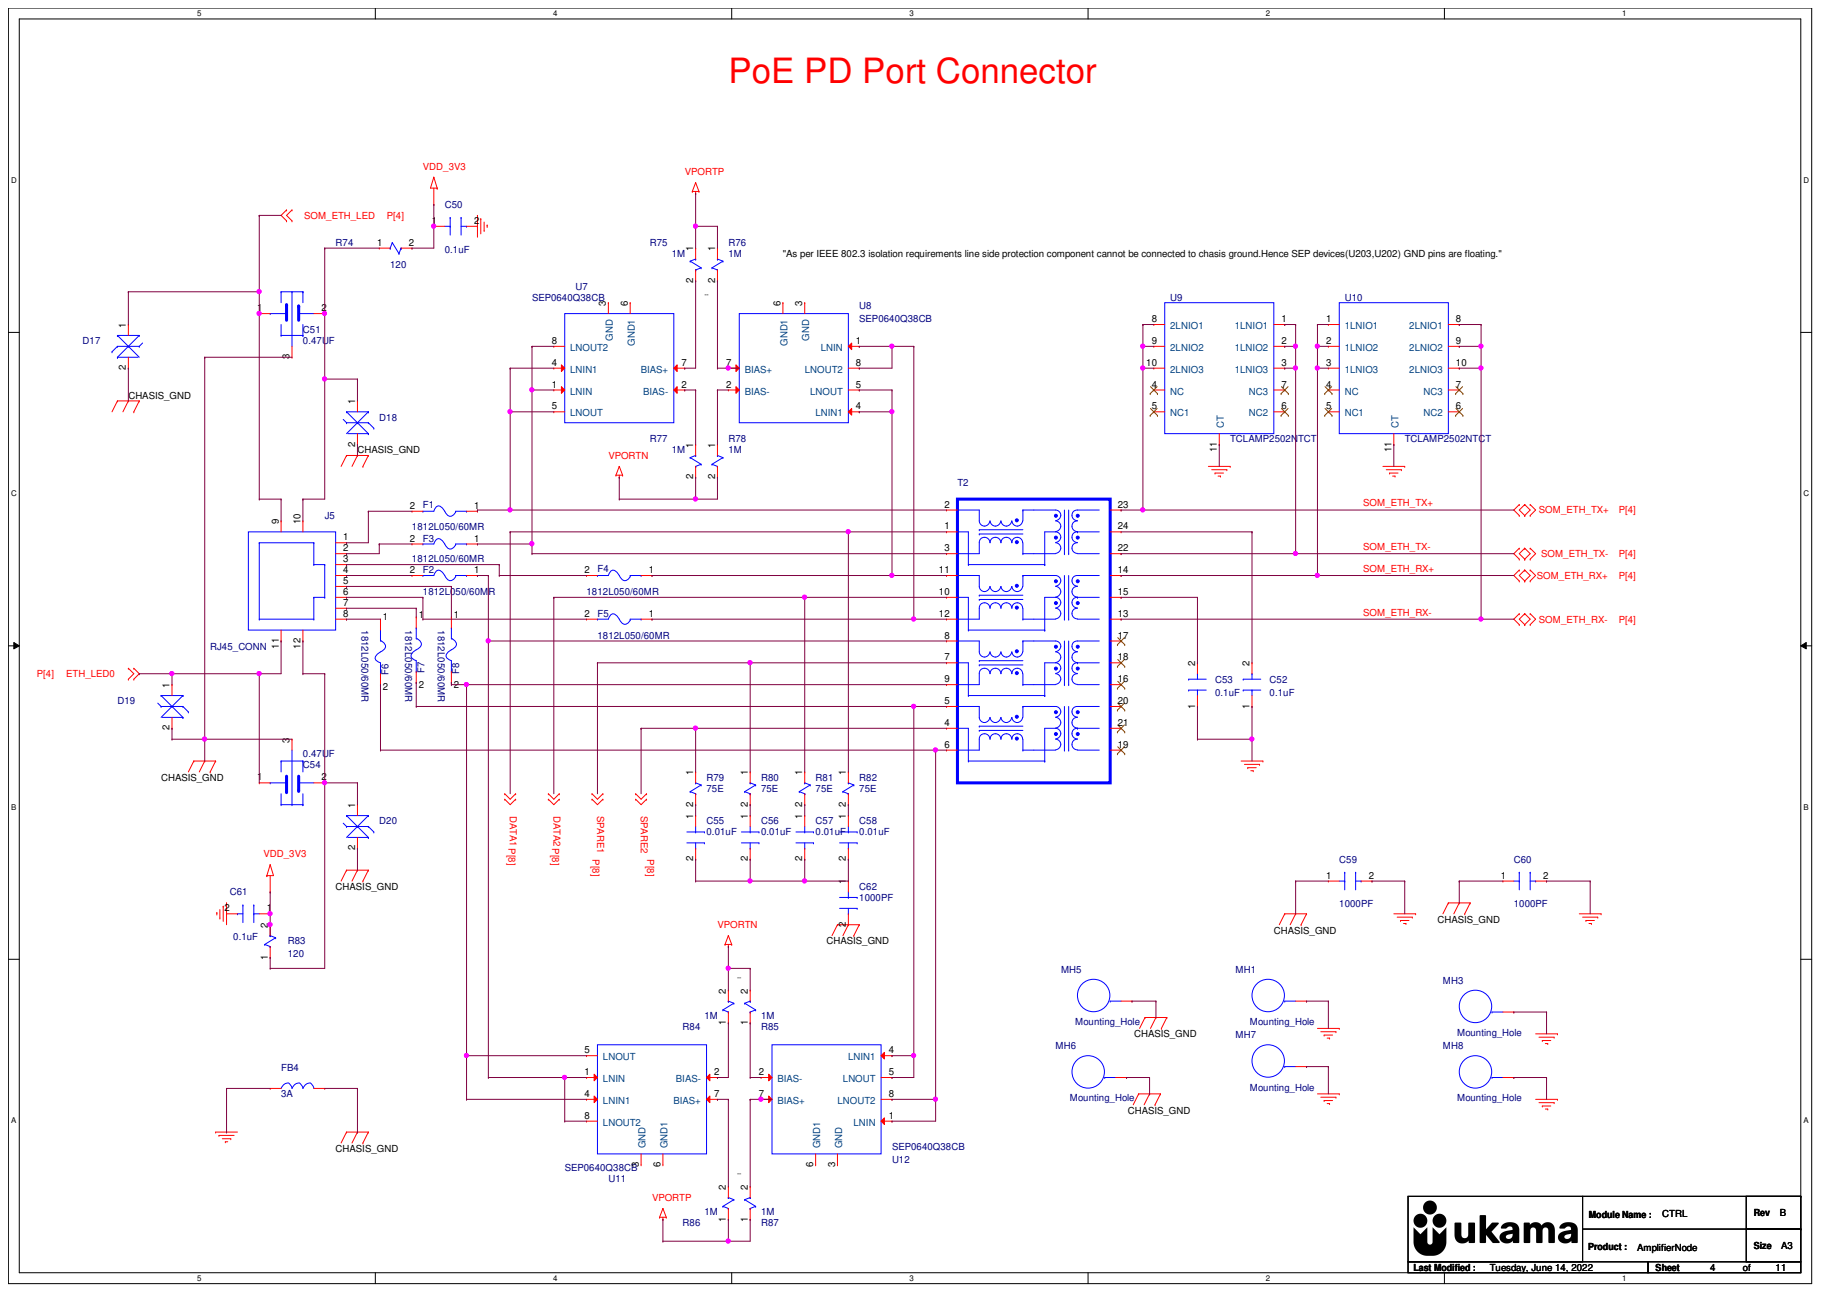
[picture p49: page 4]

"As per IEEE 802.3 isolation requirements line side protection component cannot be connected to chasis ground.Hence SEP devices(U203,U202) GND pins are floating."

# PoE Ideal diode Bridge controller

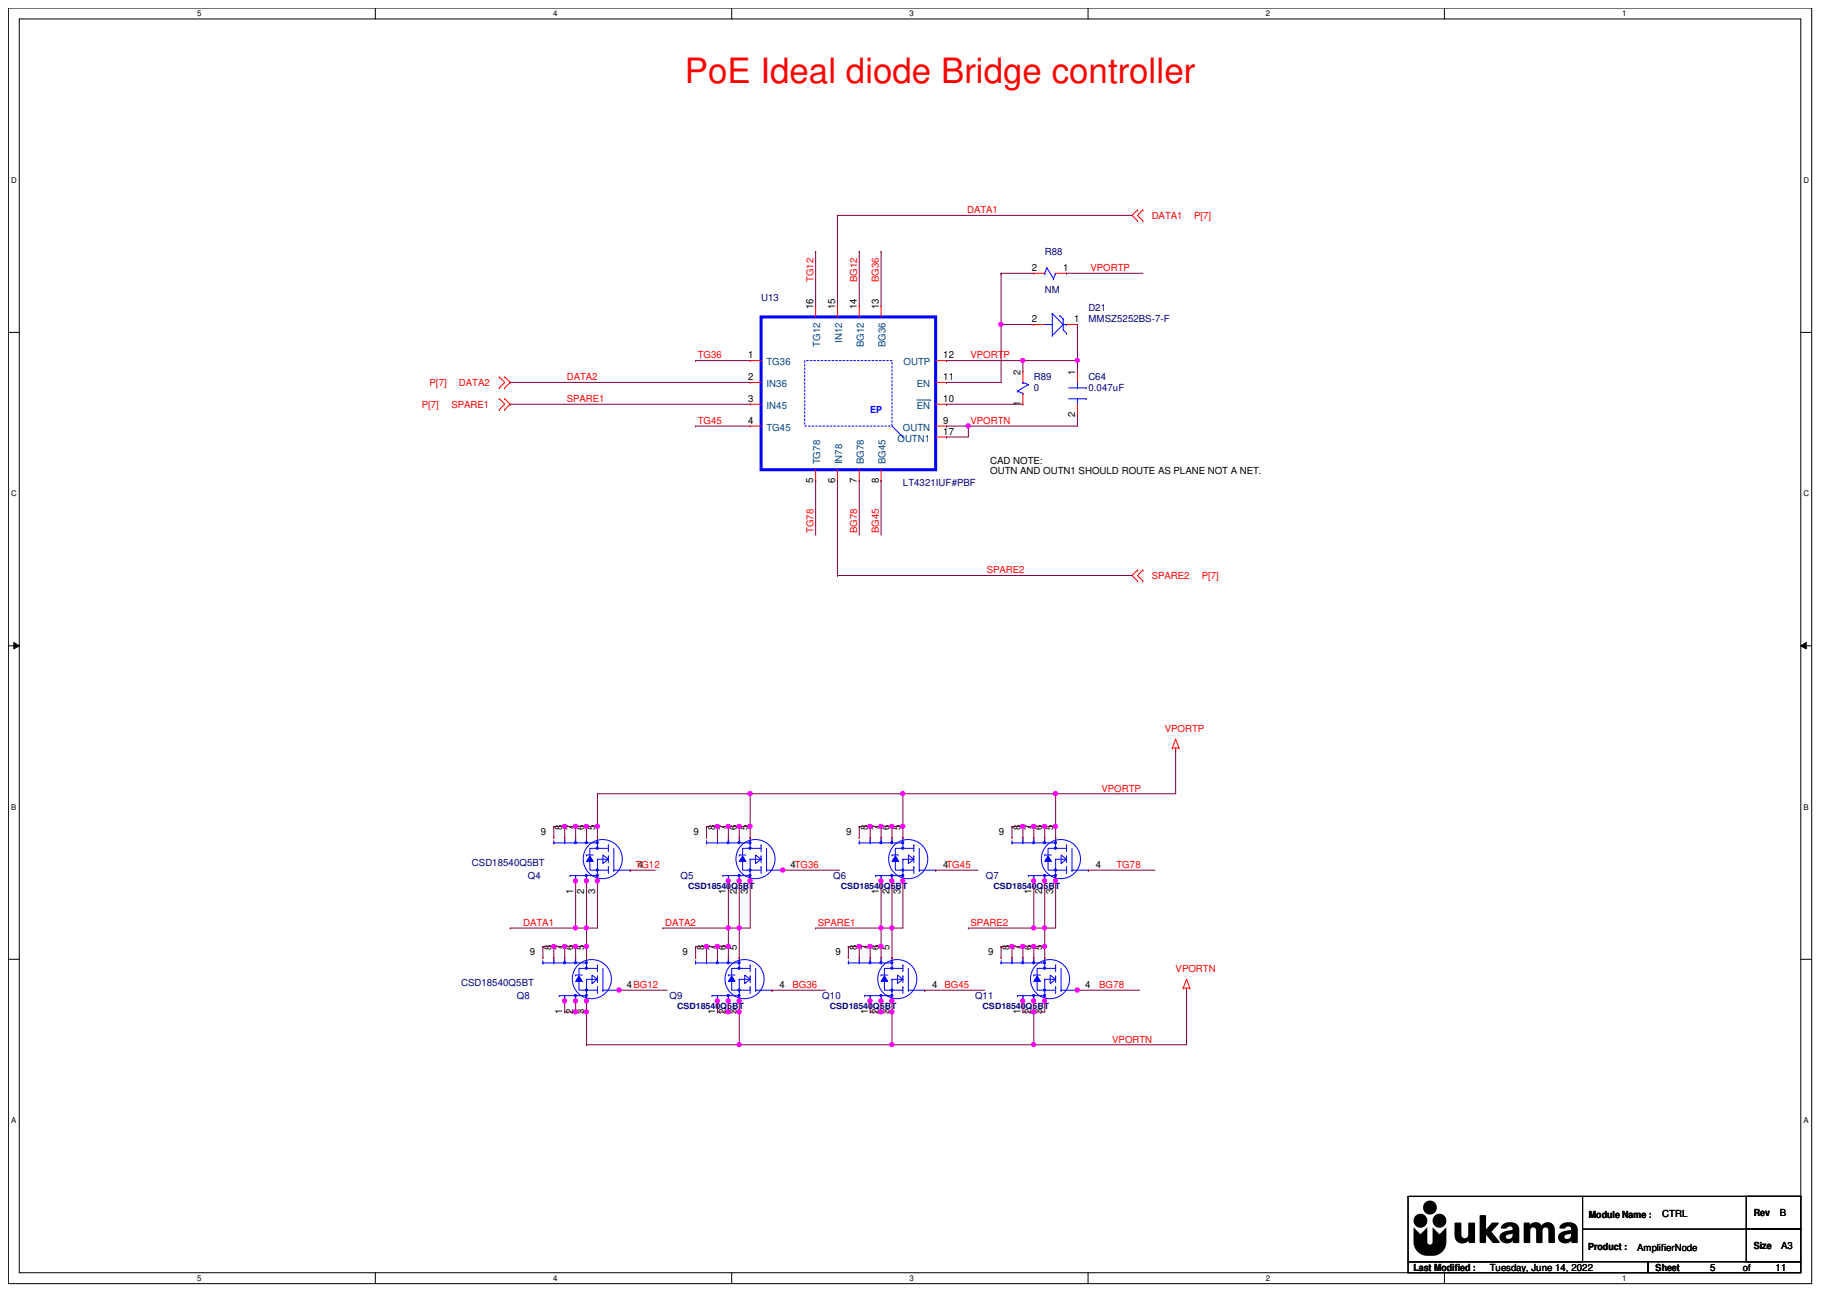
[picture p50: page 5]

CAD NOTE:
OUTN AND OUTN1 SHOULD ROUTE AS PLANE NOT A NET.

# 12V Converter

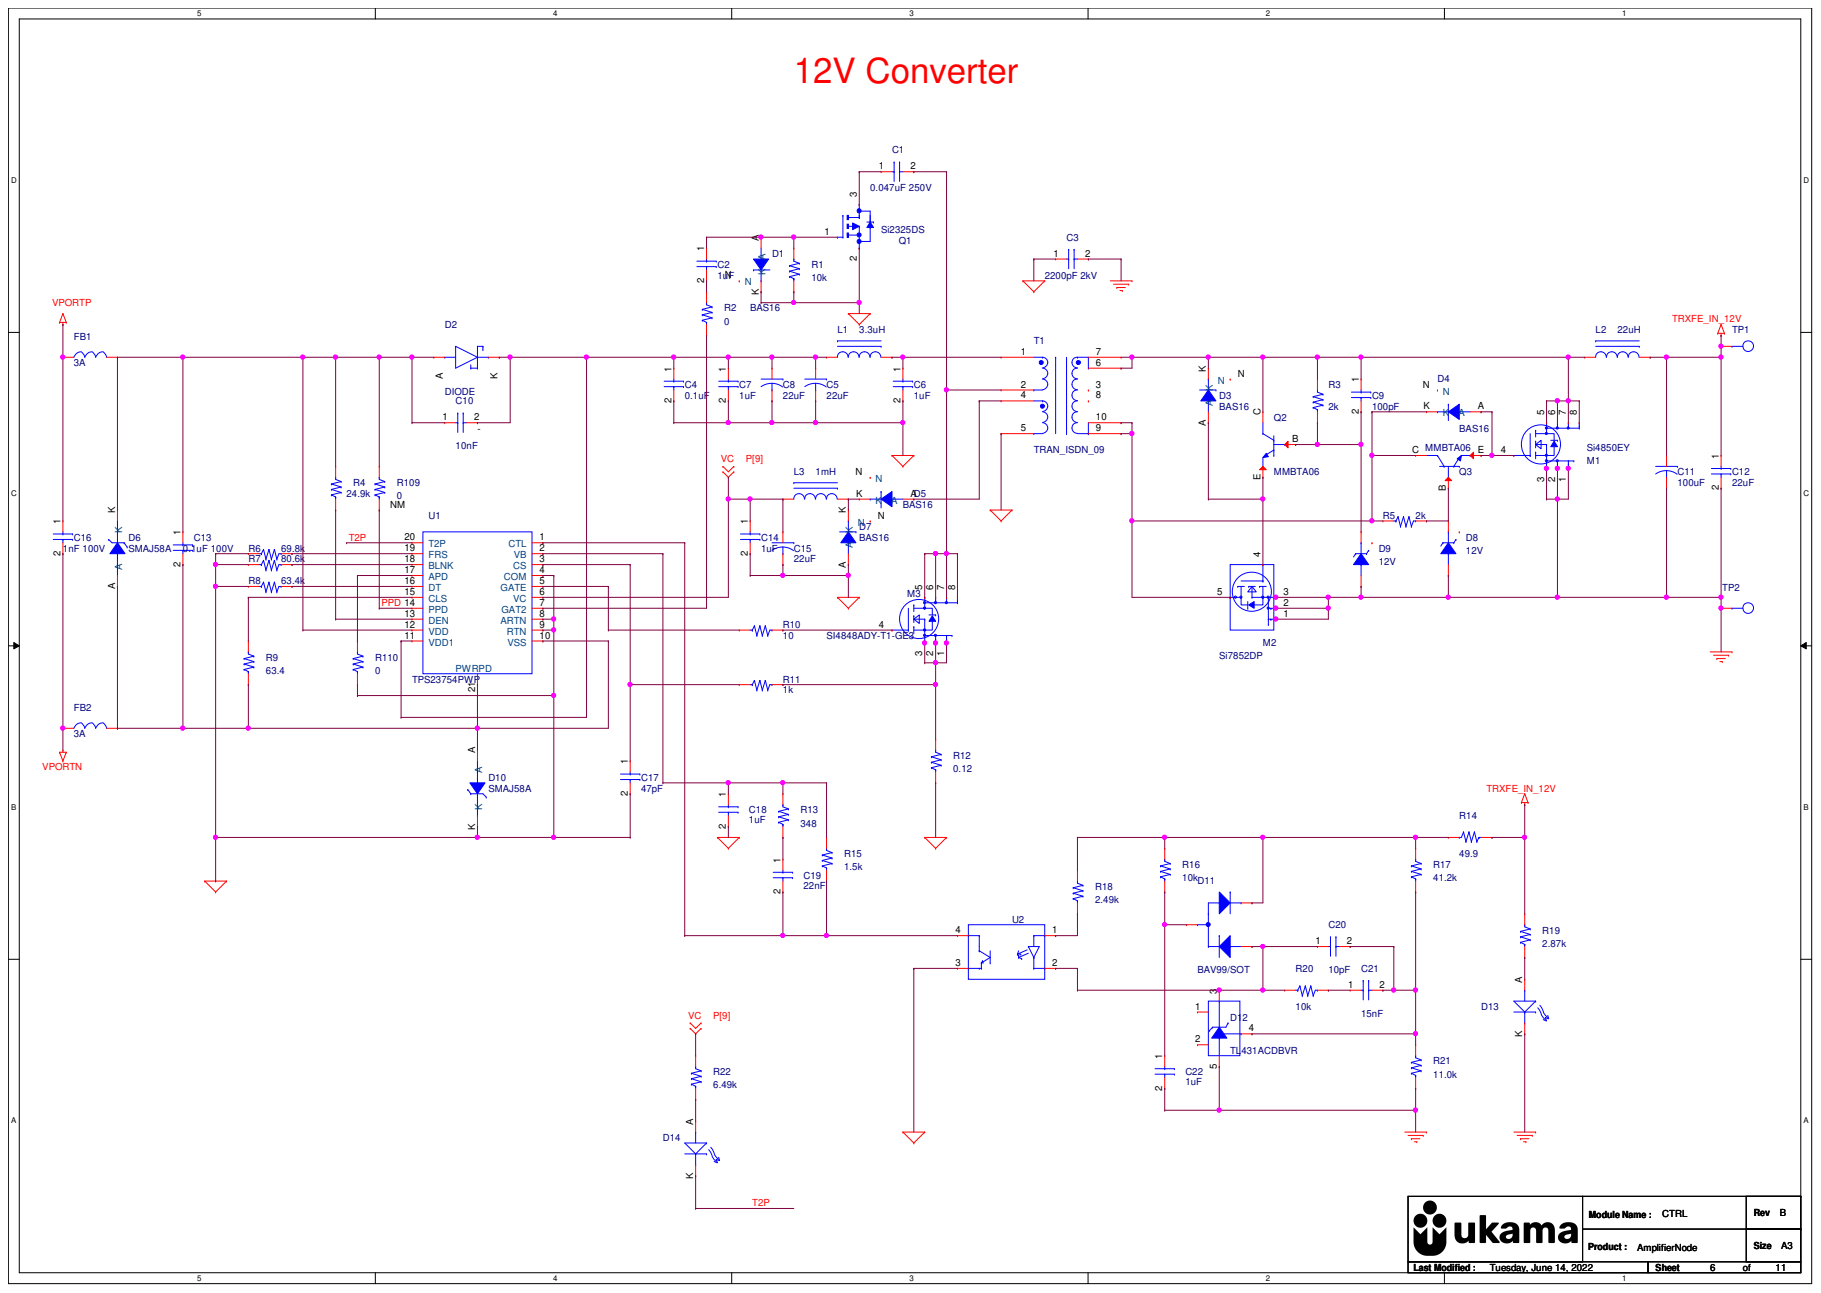
[picture p51: page 6]

# System On Module

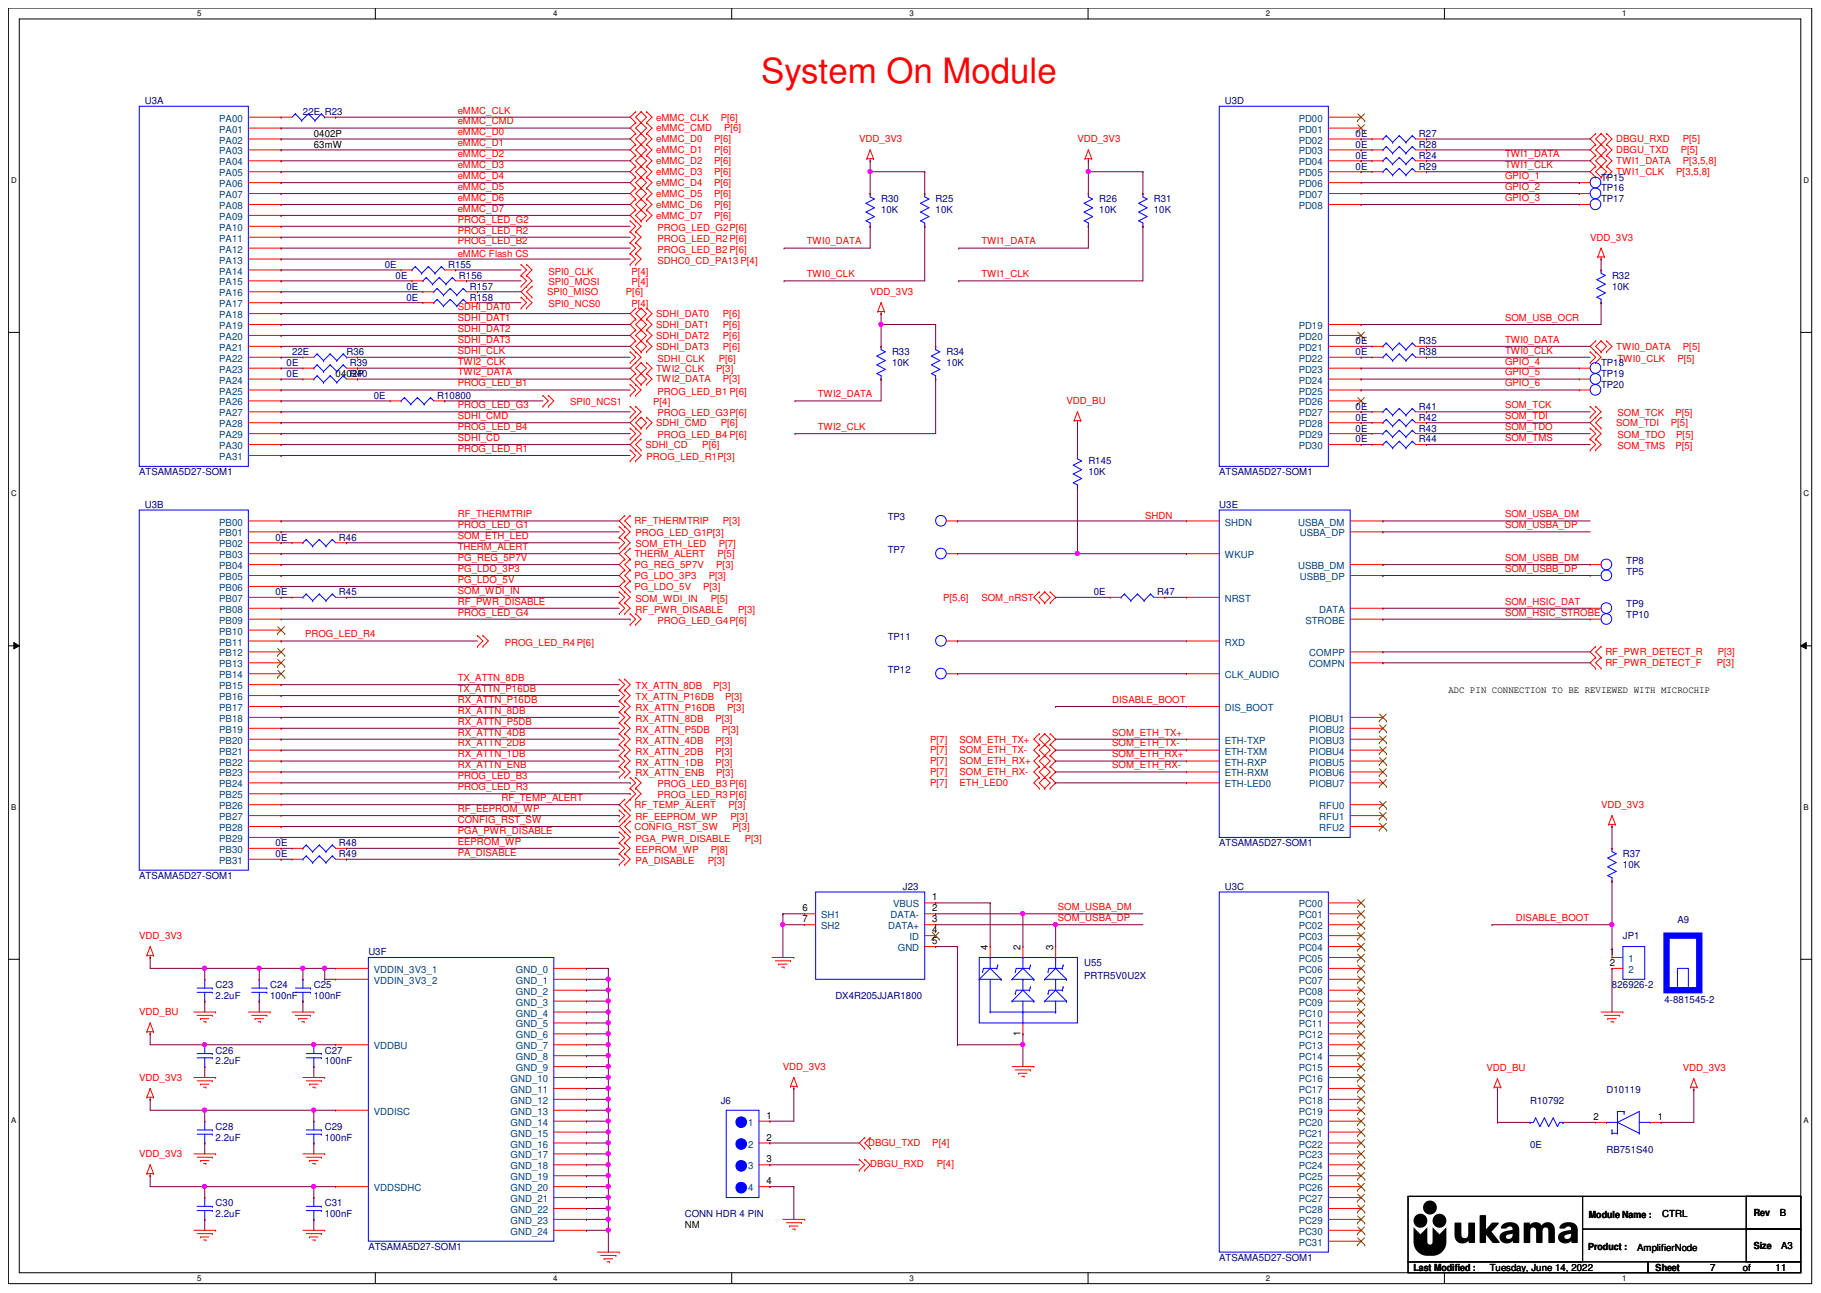
[picture p52: page 7]

ADC PIN CONNECTION TO BE REVIEWED WITH MICROCHIP

Temperature Sensor VDD_3V3 VDD_3V3 | JTAG Connector

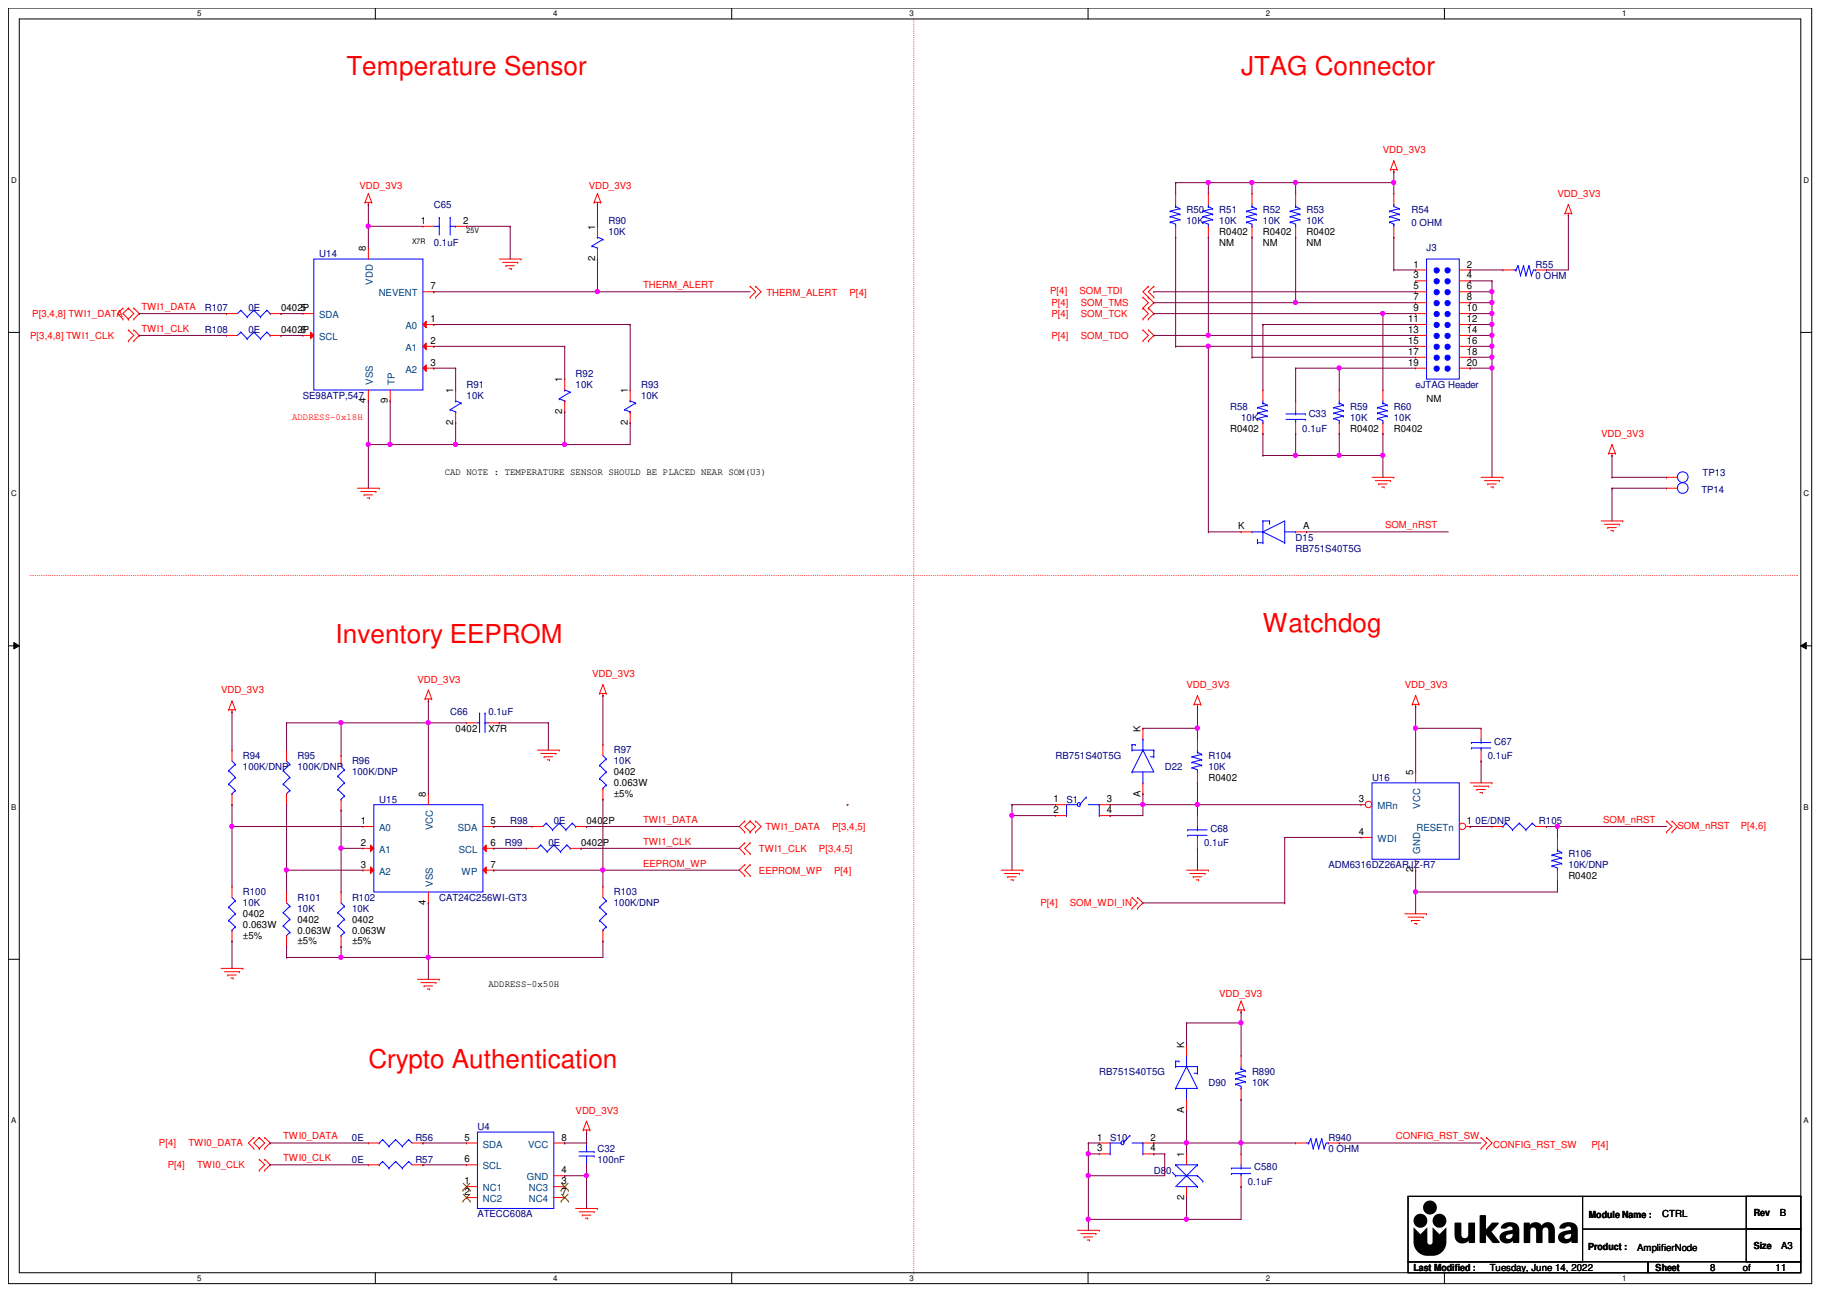
[picture p53: page 8]

CAD NOTE : TEMPERATURE SENSOR SHOULD BE PLACED NEAR SOM(U3)

# eMMC

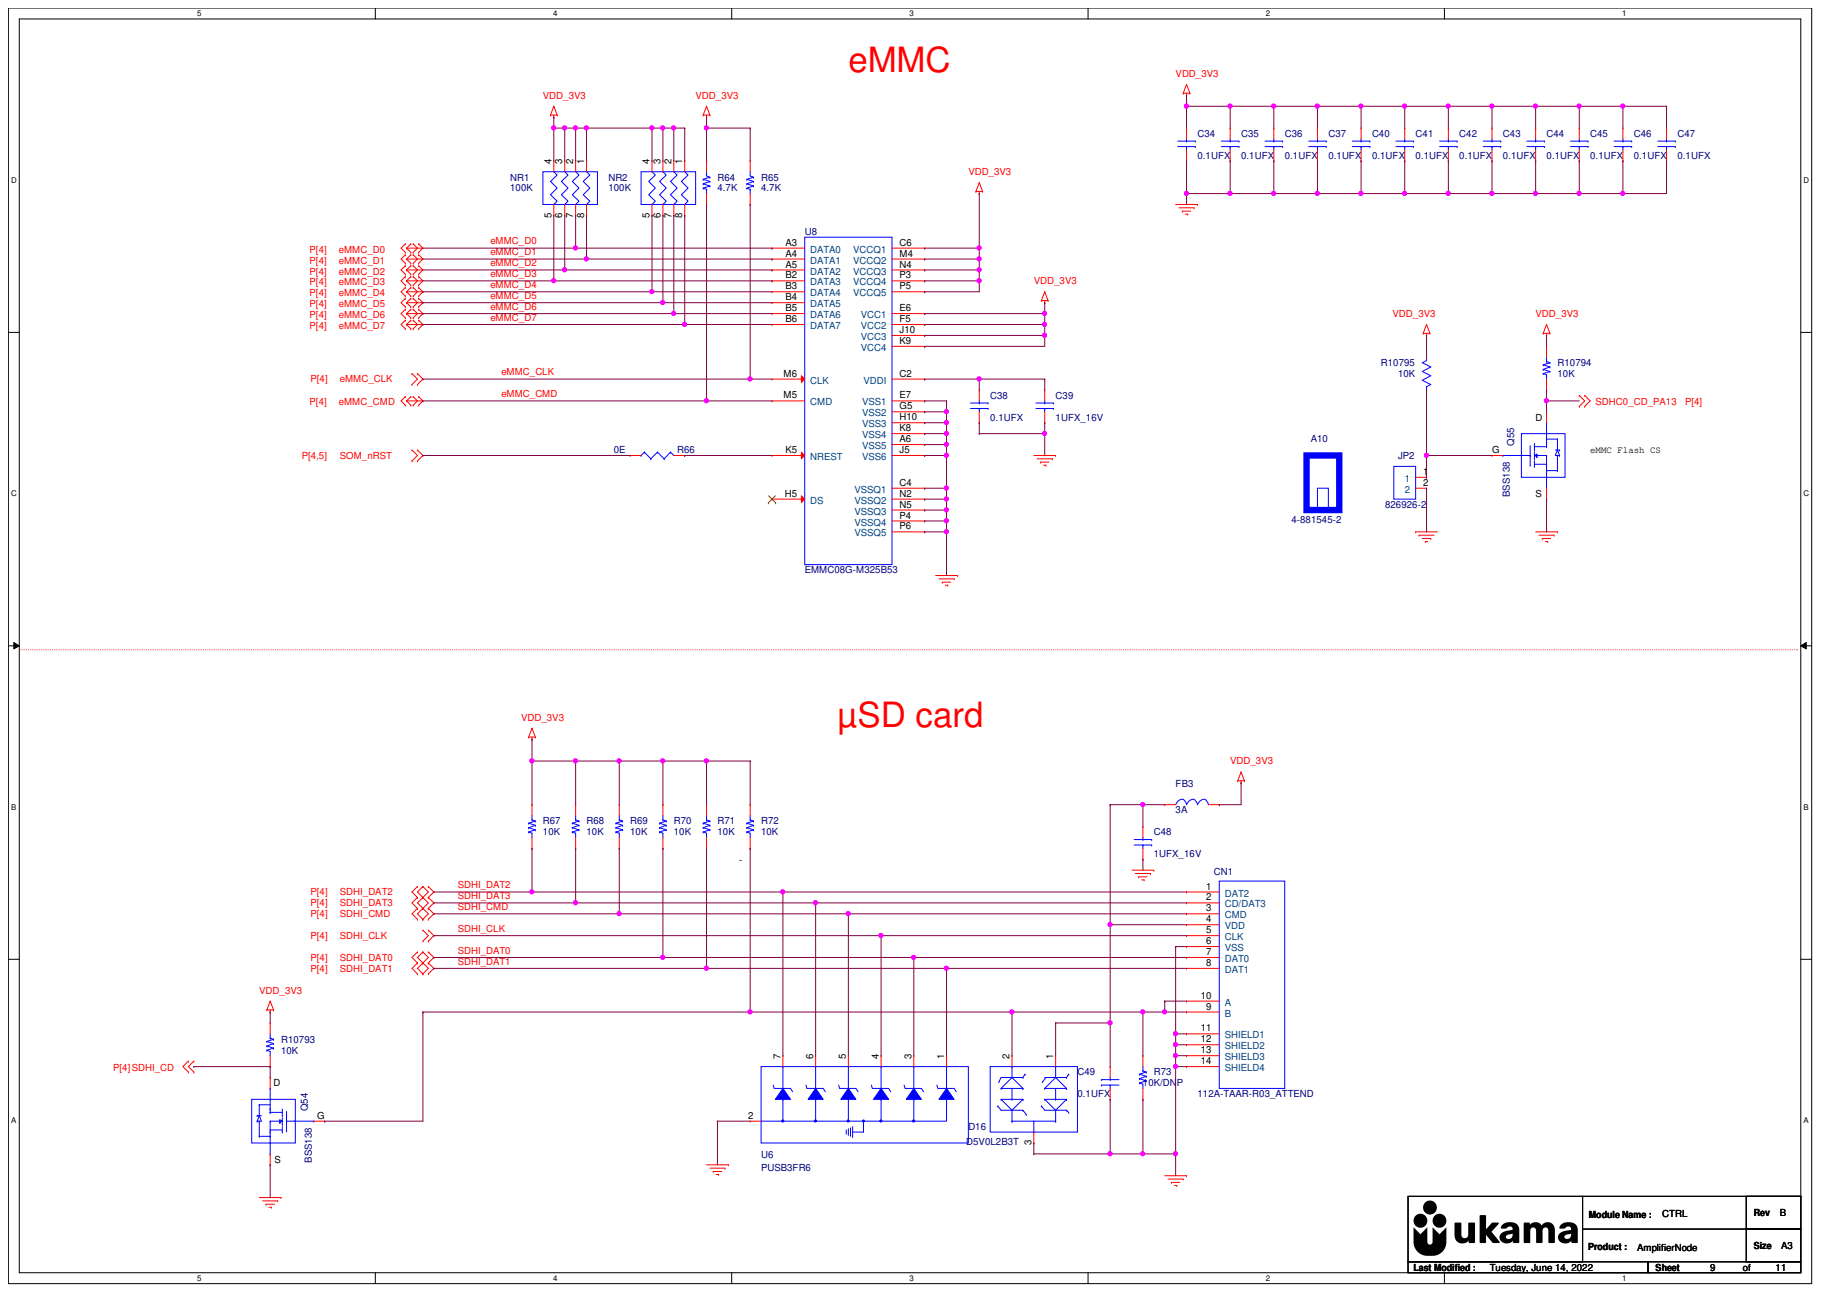
[picture p54: page 9]

# RGB LEDs

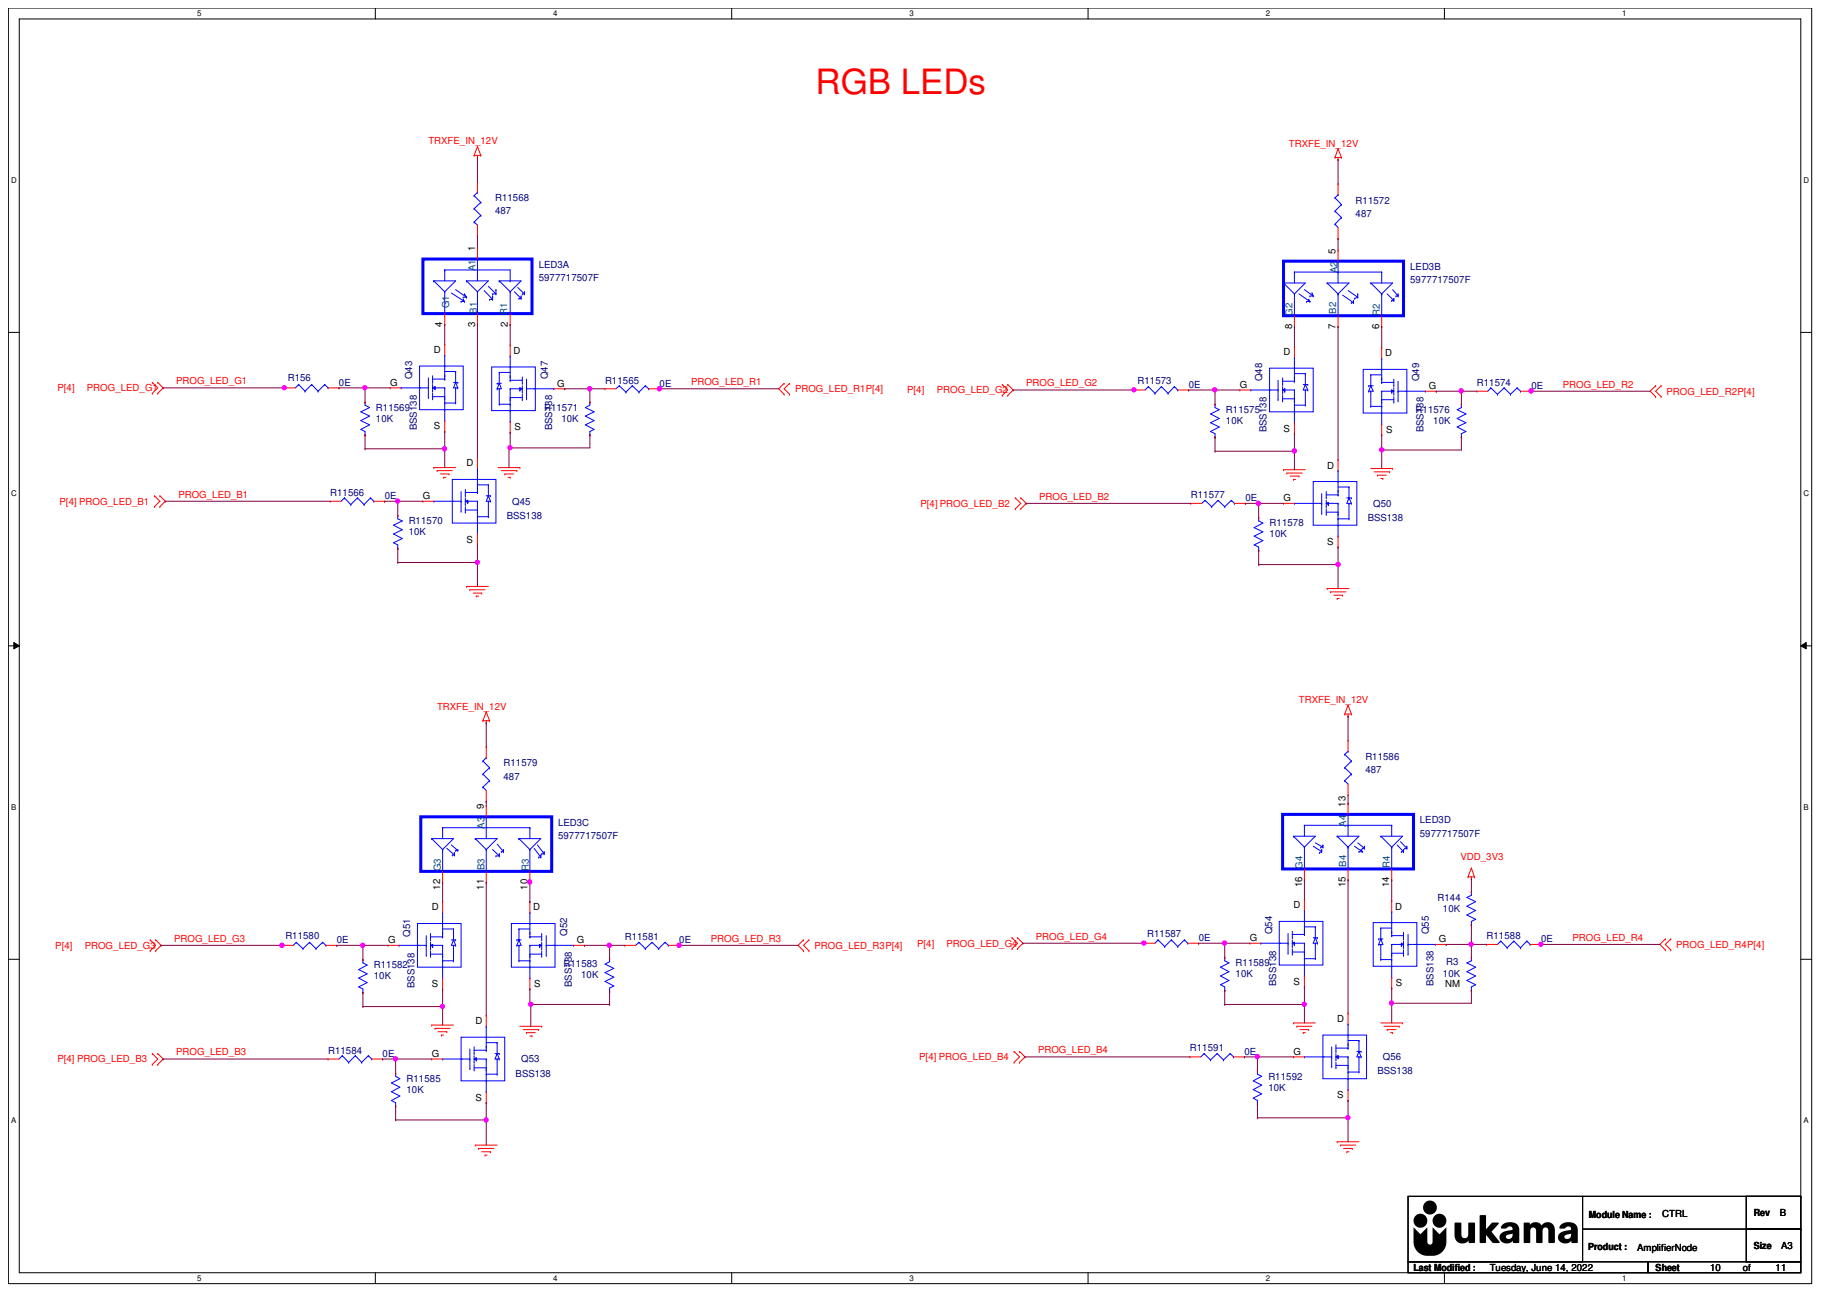
[picture p55: page 10]

# Front end connector

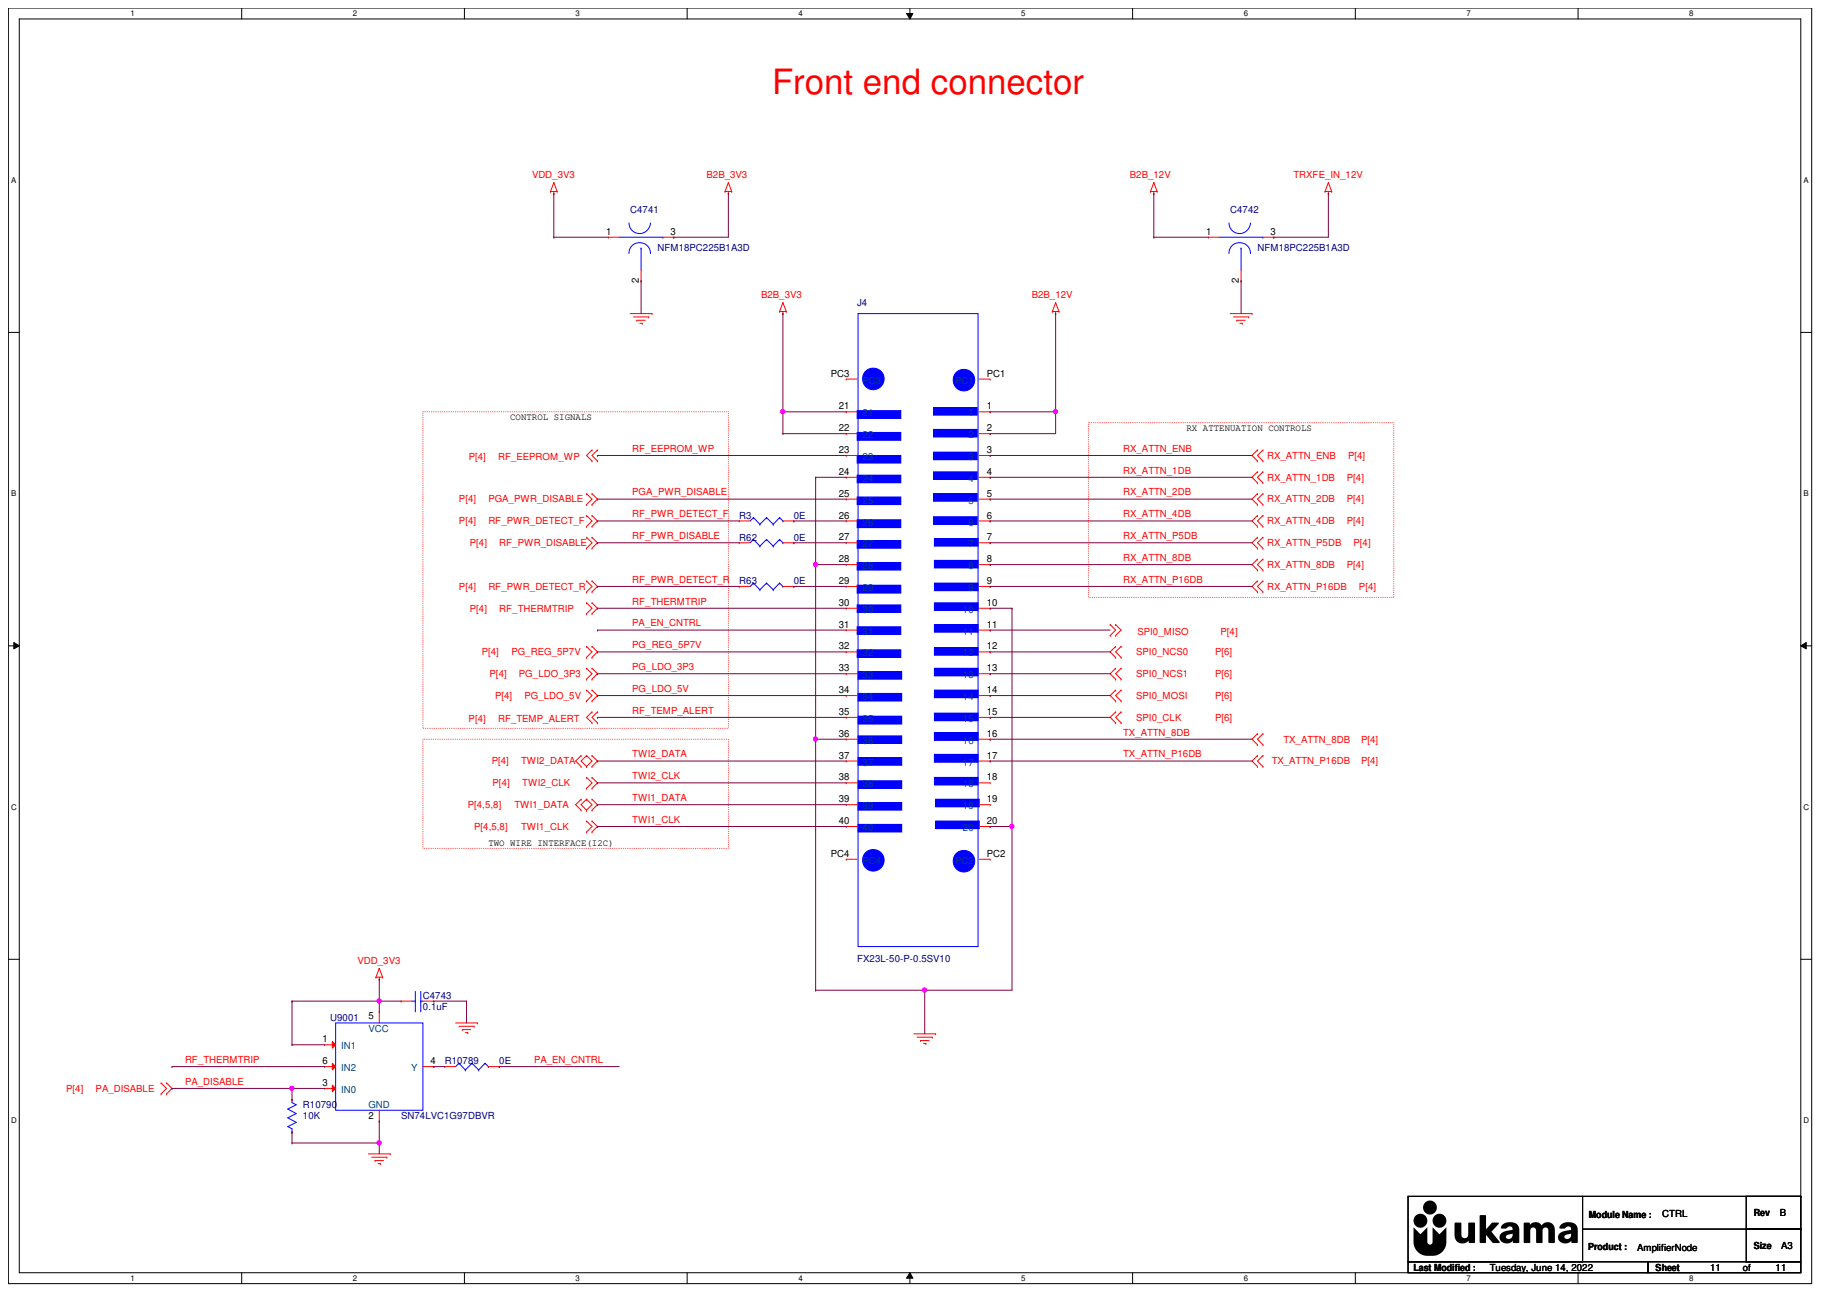
[picture p56: page 11]
