ukama/ukama-nodes/mechanics/units/amplifier/drawings/back_amplifier_unit.pdf

C

8 | 7 | 6 | 5 | 4 | 3 | 2 | 1

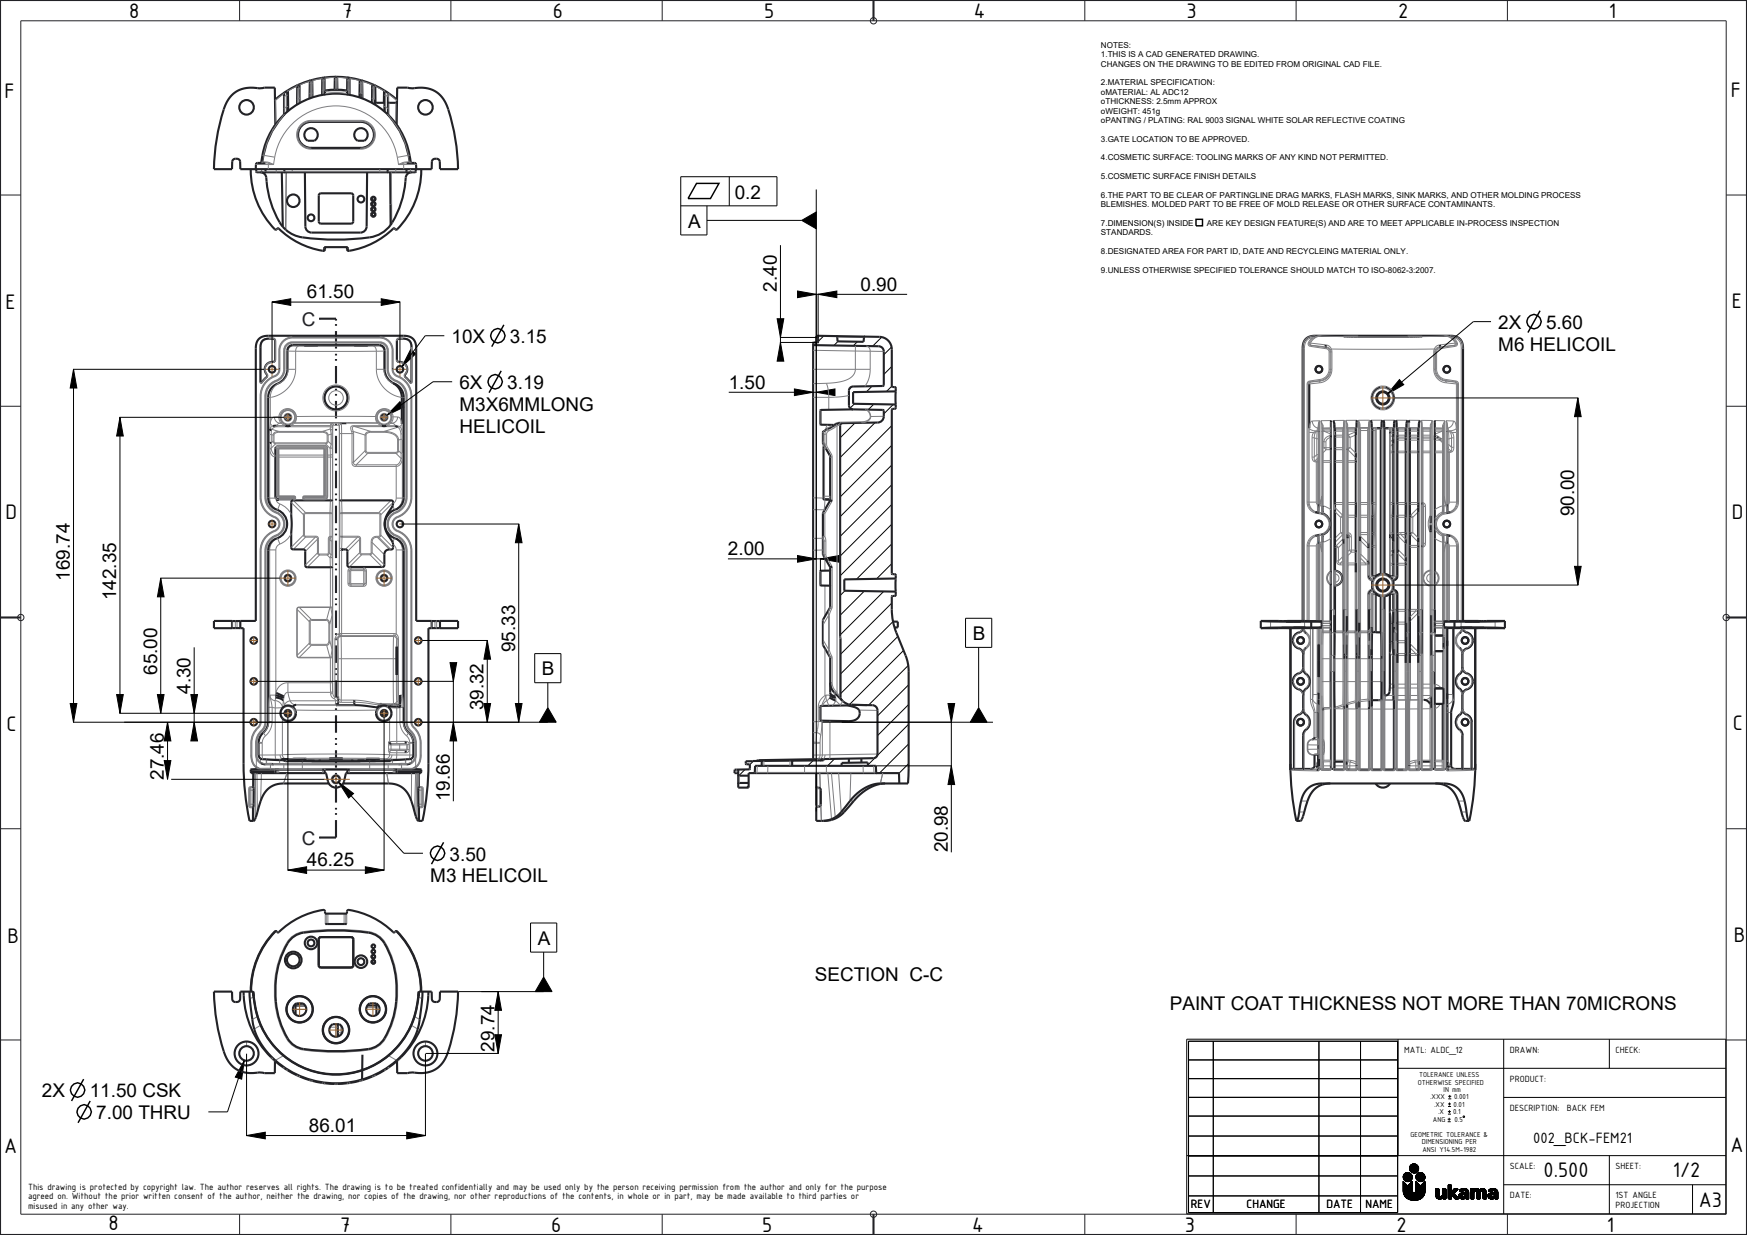
[picture p57: page 1]
002_BCK-FEM21 ⁹⁰.00; 2X 11.50 CSK; 7.00 THRU; 6X 3.19 M3X6MMLONG HELICOIL; 3.50 M3 HELICOIL; 2X 5.60 M6 HELICOIL; REV; CHANGE; DATE NAME; MATL: ALDC_12; DRAWN:; CHECK:; .XX 0.01 .X 0.1 ANG 0.5; GEOMETRIC TOLERANCE & DIMENSIONING PER; ANSI Y14.5M-1982; PRODUCT:; SCALE:; SHEET:; DATE:; 1ST ANGLE; PROJECTION; SECTION C-C

NOTES:
1.THIS IS A CAD GENERATED DRAWING.
CHANGES ON THE DRAWING TO BE EDITED FROM ORIGINAL CAD FILE.
2.MATERIAL SPECIFICATION:
oMATERIAL: AL ADC12
oTHICKNESS: 2.5mm APPROX
oWEIGHT: 451g
oPANTING / PLATING: RAL 9003 SIGNAL WHITE SOLAR REFLECTIVE COATING
3.GATE LOCATION TO BE APPROVED.
4.COSMETIC SURFACE: TOOLING MARKS OF ANY KIND NOT PERMITTED.
5.COSMETIC SURFACE FINISH DETAILS
6.THE PART TO BE CLEAR OF PARTINGLINE DRAG MARKS, FLASH MARKS, SINK MARKS, AND OTHER MOLDING PROCESS
BLEMISHES. MOLDED PART TO BE FREE OF MOLD RELEASE OR OTHER SURFACE CONTAMINANTS.
7.DIMENSION(S) INSIDE ARE KEY DESIGN FEATURE(S) AND ARE TO MEET APPLICABLE IN-PROCESS INSPECTION
STANDARDS.
8.DESIGNATED AREA FOR PART ID, DATE AND RECYCLEING MATERIAL ONLY.
9.UNLESS OTHERWISE SPECIFIED TOLERANCE SHOULD MATCH TO ISO-8062-3:2007.

PAINT COAT THICKNESS NOT MORE THAN 70MICRONS

TOLERANCE UNLESS
OTHERWISE SPECIFIED IN mm .XXX 0.001

DESCRIPTION: BACK FEM

This drawing is protected by copyright law. The author reserves all rights. The drawing is to be treated confidentially and may be used only by the person receiving permission from the author and only for the purpose
agreed on. Without the prior written consent of the author, neither the drawing, nor copies of the drawing, nor other reproductions of the contents, in whole or in part, may be made available to third parties or
misused in any other way.

8 | 7 | 6 | 5 | 4 | 3 | 2 | 1

E

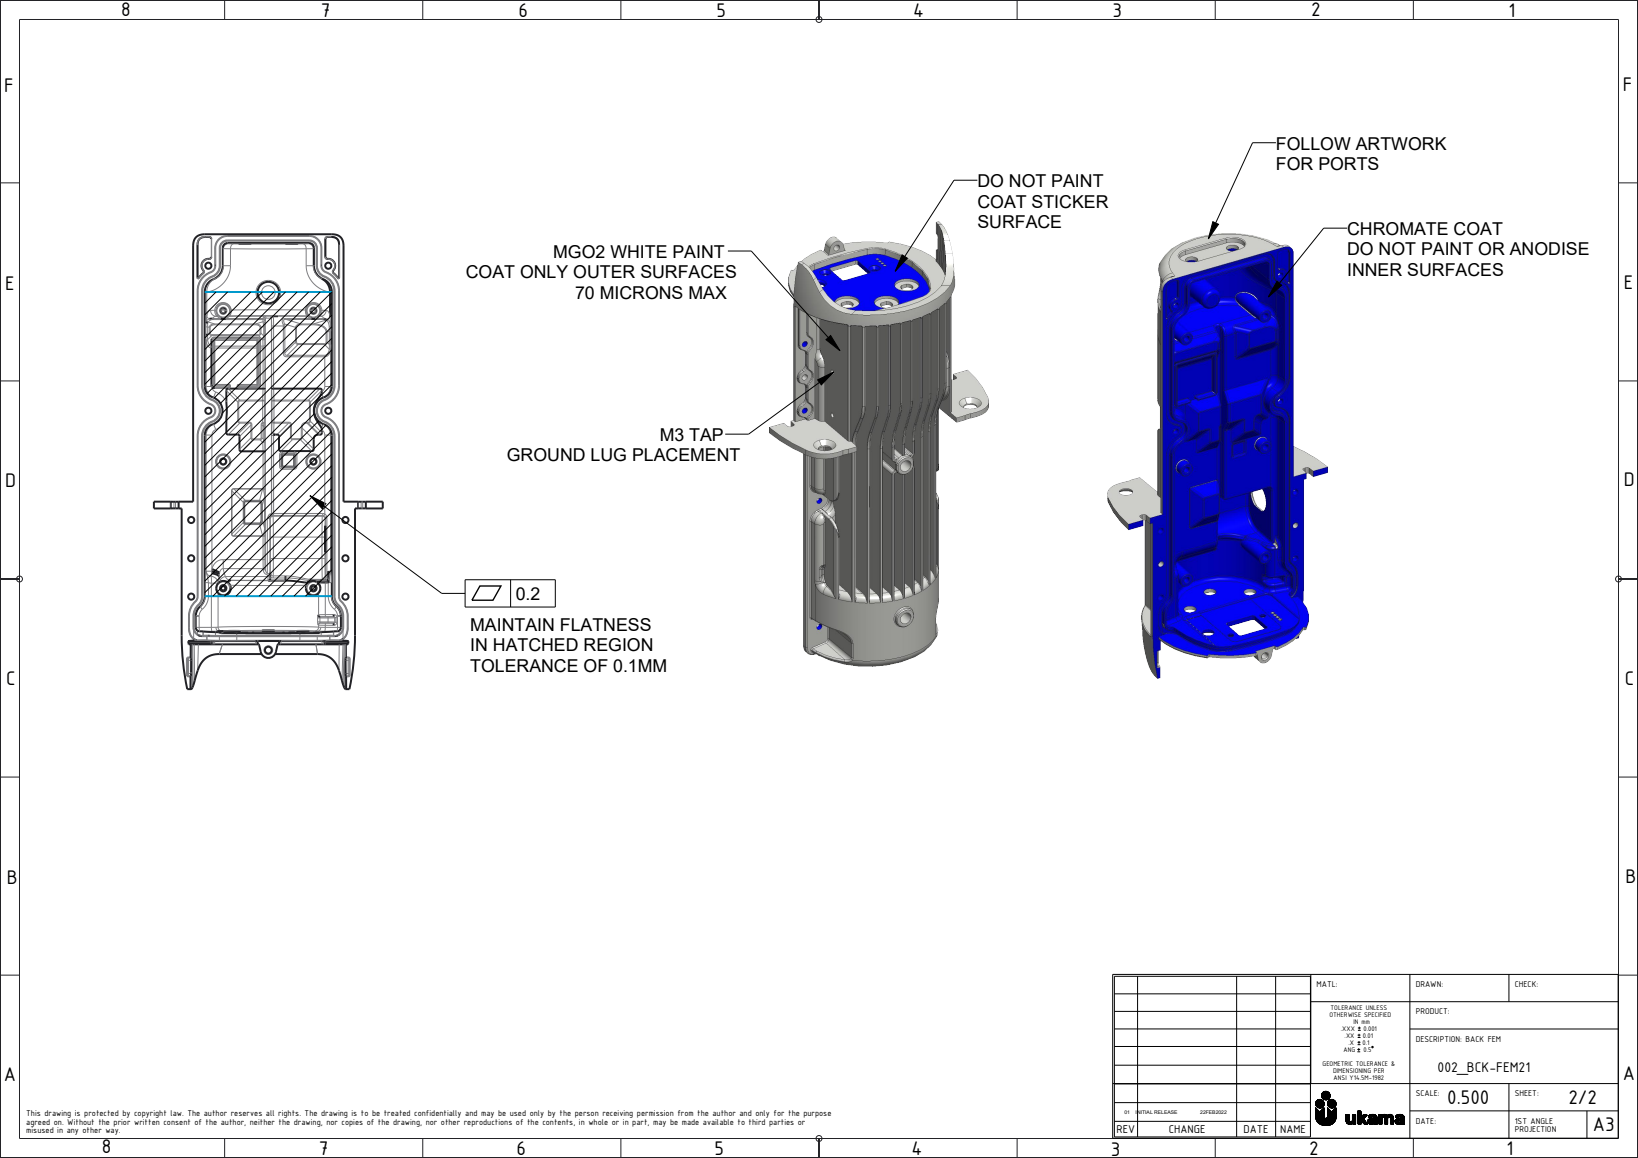
[picture p58: page 2]
MATL:; DRAWN:; CHECK:; .XX 0.01 .X 0.1 ANG 0.5; GEOMETRIC TOLERANCE & DIMENSIONING PER; ANSI Y14.5M-1982; PRODUCT:; SCALE:; SHEET:; DATE:; 1ST ANGLE; REV; CHANGE; DATE NAME; PROJECTION; 01 INITIAL RELEASE; 22FEB2022; FOLLOW ARTWORK FOR PORTS; MGO2 WHITE PAINT; 70 MICRONS MAX; M3 TAP

DO NOT PAINT
COAT STICKER
SURFACE

CHROMATE COAT
DO NOT PAINT OR ANODISE
INNER SURFACES

COAT ONLY OUTER SURFACES

GROUND LUG PLACEMENT

MAINTAIN FLATNESS
IN HATCHED REGION
TOLERANCE OF 0.1MM

TOLERANCE UNLESS
OTHERWISE SPECIFIED IN mm .XXX 0.001

DESCRIPTION: BACK FEM
002_BCK-FEM21

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
