ukama/ukama-nodes/mechanics/units/amplifier/drawings/cup_amplifier_unit.pdf

8 | 7 | 6 | 5 | 4 | 3 | 2 | 1

E

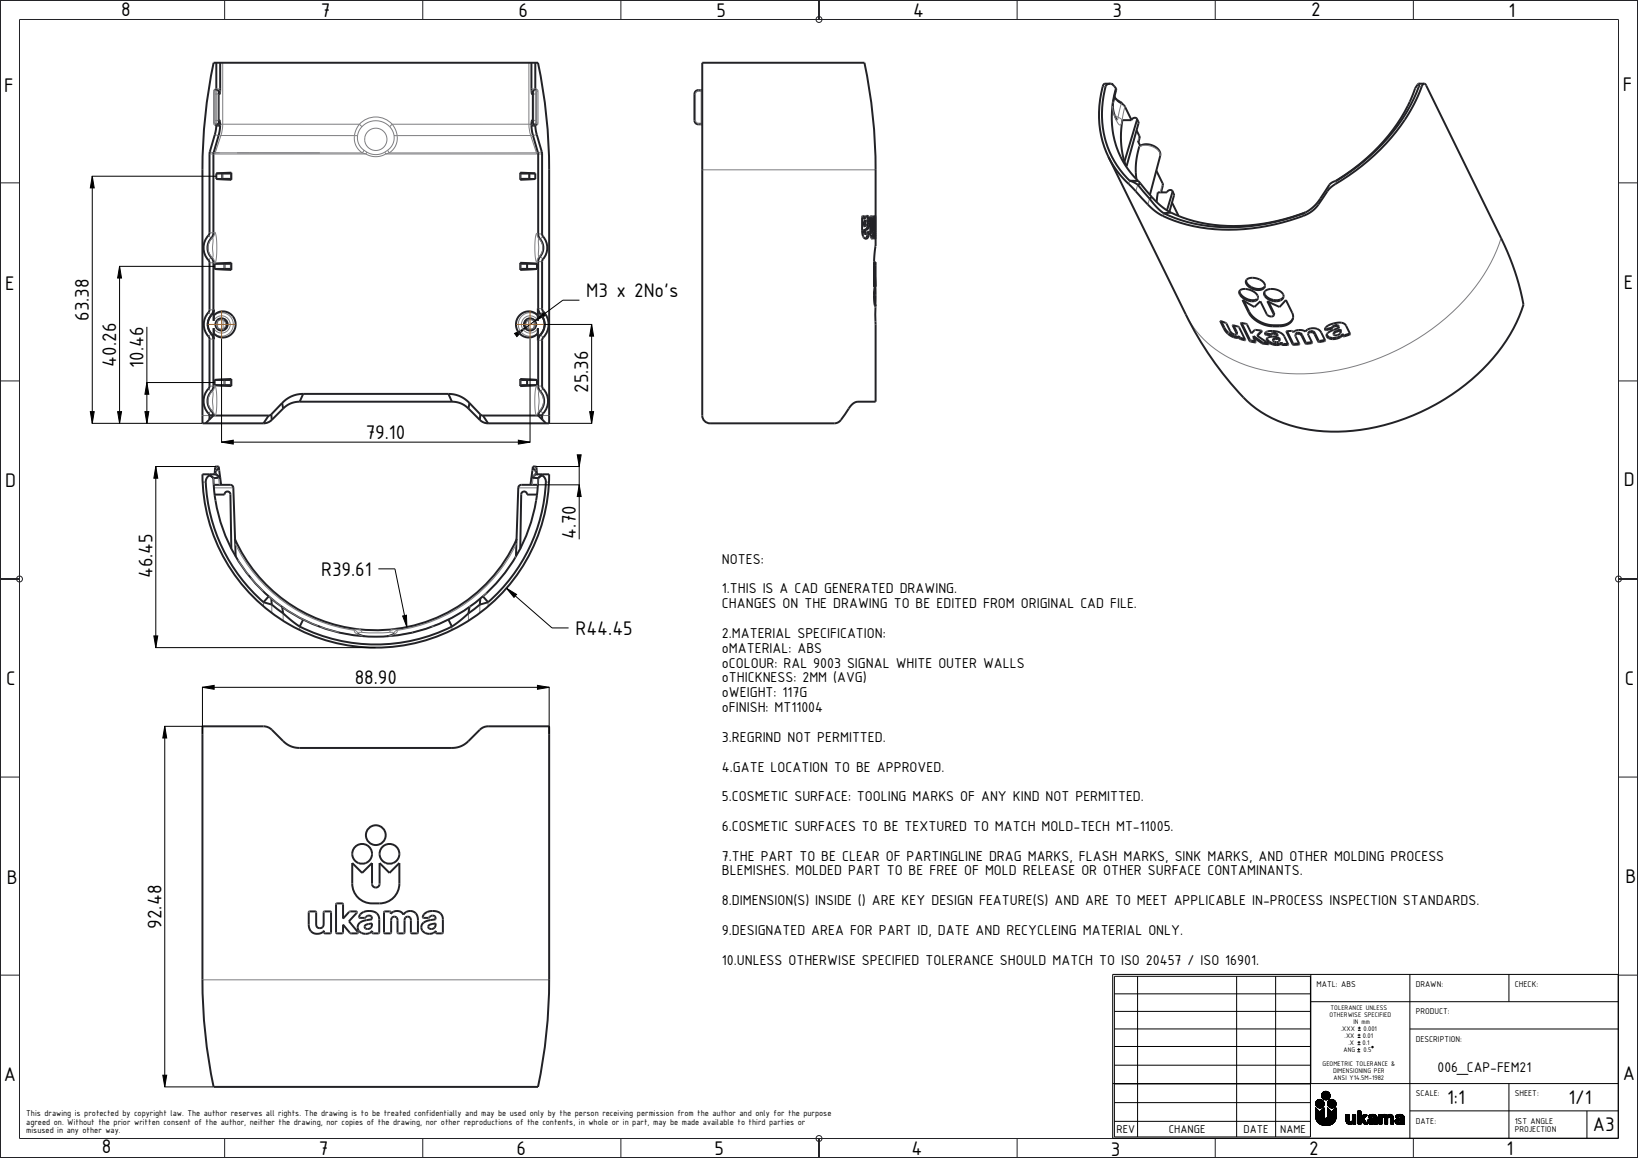
[picture p59: page 1]
006_CAP-FEM21; MATL: ABS; DRAWN:; CHECK:; .XX 0.01 .X 0.1 ANG 0.5; GEOMETRIC TOLERANCE & DIMENSIONING PER; ANSI Y14.5M-1982; PRODUCT:; DESCRIPTION:; SCALE:; SHEET:; DATE:; 1ST ANGLE; REV; CHANGE; DATE NAME; PROJECTION

NOTES:
1.THIS IS A CAD GENERATED DRAWING.
CHANGES ON THE DRAWING TO BE EDITED FROM ORIGINAL CAD FILE.
2.MATERIAL SPECIFICATION:
oMATERIAL: ABS
oCOLOUR: RAL 9003 SIGNAL WHITE OUTER WALLS
oTHICKNESS: 2MM (AVG)
oWEIGHT: 117G
oFINISH: MT11004
3.REGRIND NOT PERMITTED.
4.GATE LOCATION TO BE APPROVED.
5.COSMETIC SURFACE: TOOLING MARKS OF ANY KIND NOT PERMITTED.
6.COSMETIC SURFACES TO BE TEXTURED TO MATCH MOLD-TECH MT-11005.
7.THE PART TO BE CLEAR OF PARTINGLINE DRAG MARKS, FLASH MARKS, SINK MARKS, AND OTHER MOLDING PROCESS
BLEMISHES. MOLDED PART TO BE FREE OF MOLD RELEASE OR OTHER SURFACE CONTAMINANTS.
8.DIMENSION(S) INSIDE () ARE KEY DESIGN FEATURE(S) AND ARE TO MEET APPLICABLE IN-PROCESS INSPECTION STANDARDS.
9.DESIGNATED AREA FOR PART ID, DATE AND RECYCLEING MATERIAL ONLY.
10.UNLESS OTHERWISE SPECIFIED TOLERANCE SHOULD MATCH TO ISO 20457 / ISO 16901.

TOLERANCE UNLESS
OTHERWISE SPECIFIED IN mm .XXX 0.001

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
