ukama/ukama-nodes/mechanics/units/amplifier/drawings/mounting_cap_amplifier_unit.pdf

8 | 7 | 6 | 5 | 4 | 3 | 2 | 1

E

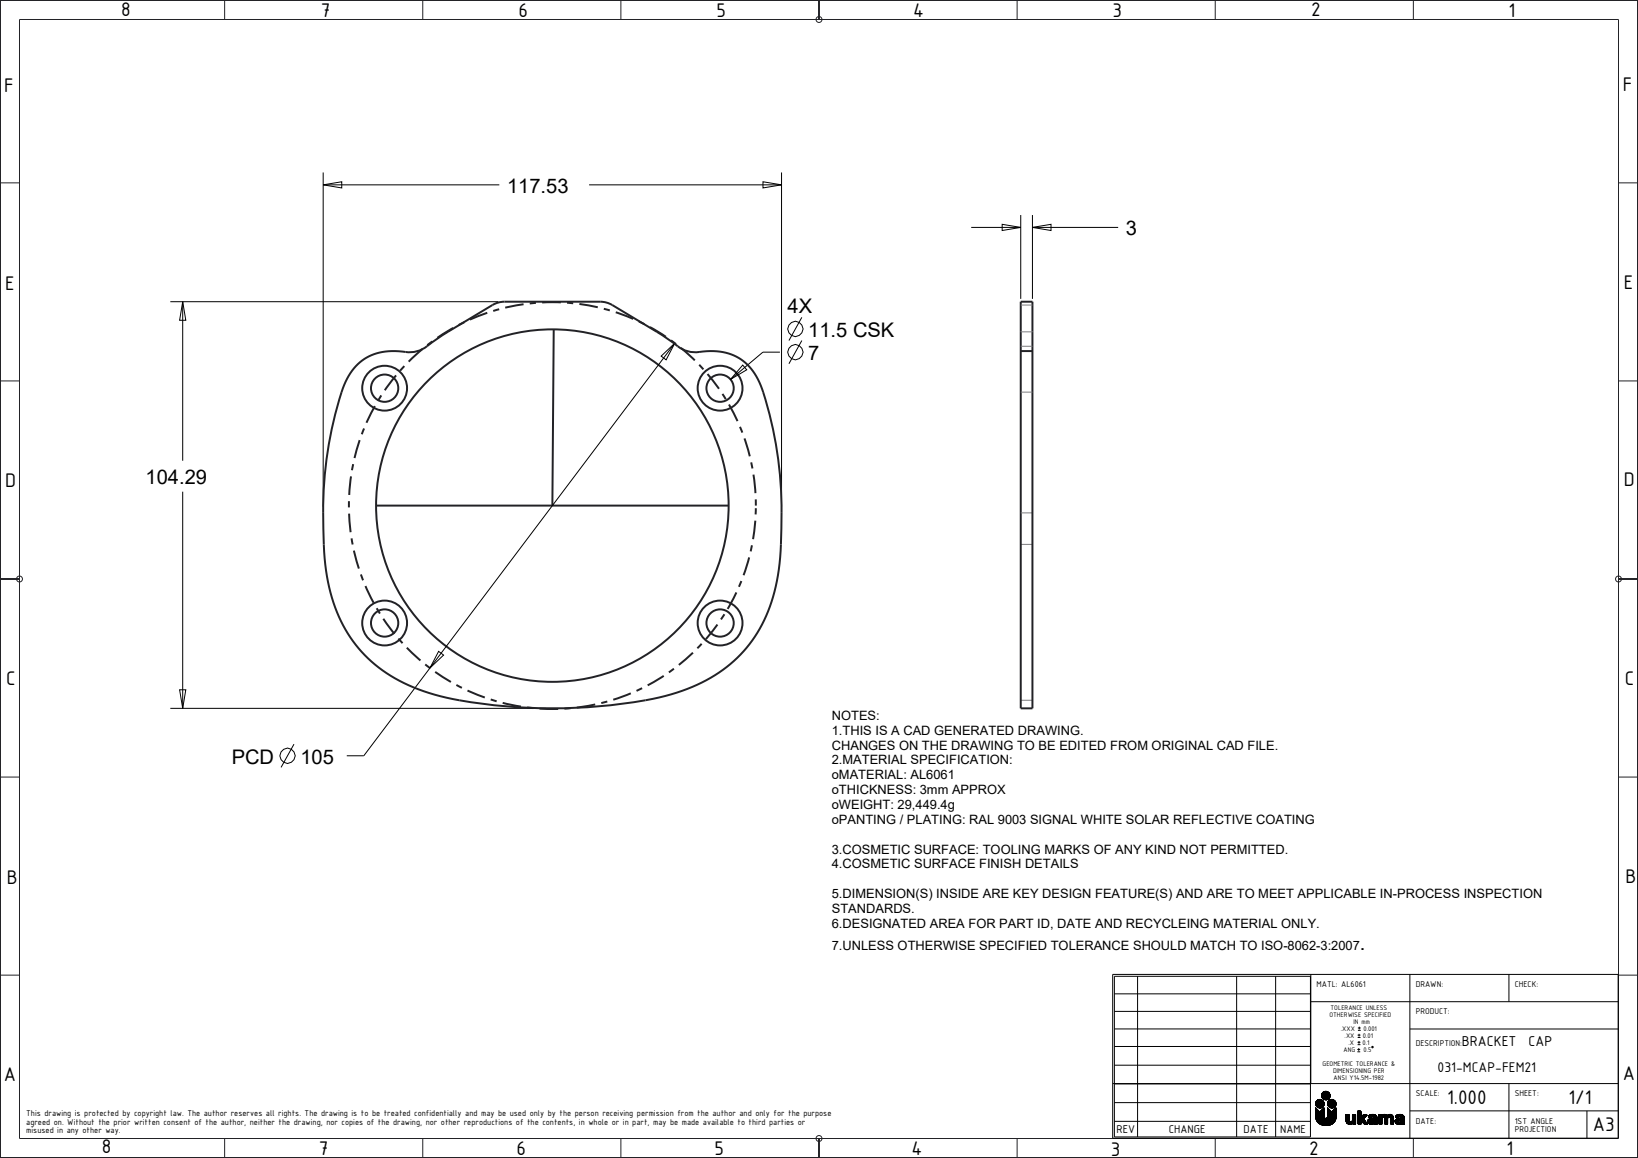
[picture p62: page 1]
PCD 105; 4X 11.5 CSK 7; MATL: AL6061; DRAWN:; CHECK:; .XX 0.01 .X 0.1 ANG 0.5; GEOMETRIC TOLERANCE & DIMENSIONING PER; ANSI Y14.5M-1982; PRODUCT:; SCALE:; SHEET:; DATE:; 1ST ANGLE; REV; CHANGE; DATE NAME; PROJECTION

NOTES:
1.THIS IS A CAD GENERATED DRAWING.
CHANGES ON THE DRAWING TO BE EDITED FROM ORIGINAL CAD FILE.
2.MATERIAL SPECIFICATION:
oMATERIAL: AL6061
oTHICKNESS: 3mm APPROX
oWEIGHT: 29,449.4g
oPANTING / PLATING: RAL 9003 SIGNAL WHITE SOLAR REFLECTIVE COATING
3.COSMETIC SURFACE: TOOLING MARKS OF ANY KIND NOT PERMITTED.
4.COSMETIC SURFACE FINISH DETAILS
5.DIMENSION(S) INSIDE ARE KEY DESIGN FEATURE(S) AND ARE TO MEET APPLICABLE IN-PROCESS INSPECTION
STANDARDS.
6.DESIGNATED AREA FOR PART ID, DATE AND RECYCLEING MATERIAL ONLY.
7.UNLESS OTHERWISE SPECIFIED TOLERANCE SHOULD MATCH TO ISO-8062-3:2007.

TOLERANCE UNLESS
OTHERWISE SPECIFIED IN mm .XXX 0.001

DESCRIPTION:BRACKET CAP
031-MCAP-FEM21

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
