ukama/ukama-nodes/mechanics/nodes/tower/drawings/bottom_tower_node.pdf

8 | 7 | 6 | 5 | 4 | 3 | 2 | 1

E

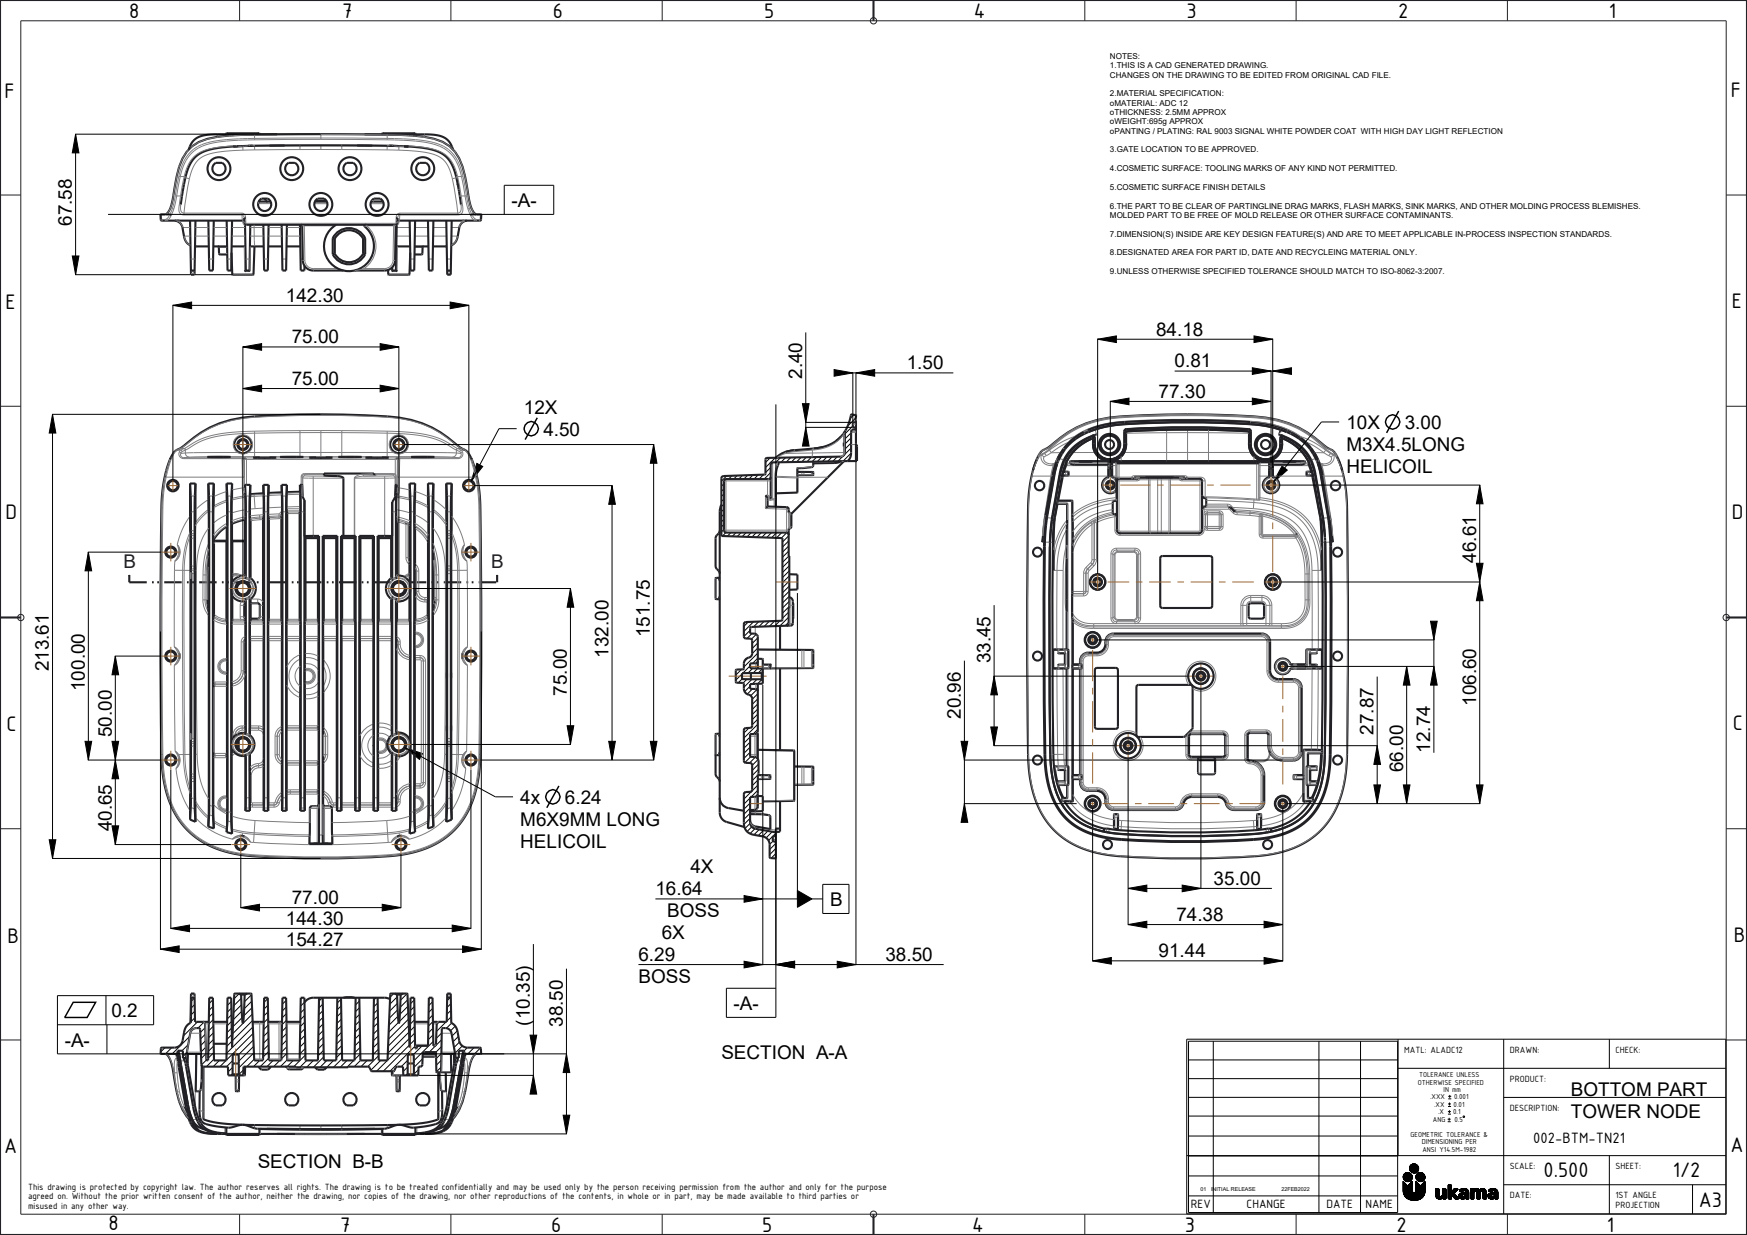
[picture p63: page 1]
002-BTM-TN21; 4X 16.64 BOSS 6X 6.29 BOSS; M3X4.5LONG HELICOIL; 4x 6.24 M6X9MM LONG HELICOIL; MATL: ALADC12; DRAWN:; CHECK:; .XX 0.01 .X 0.1 ANG 0.5; GEOMETRIC TOLERANCE & DIMENSIONING PER; ANSI Y14.5M-1982; PRODUCT:; DESCRIPTION:; SCALE:; SHEET:; DATE:; 1ST ANGLE; REV; CHANGE; DATE NAME; PROJECTION; BOTTOM PART TOWER NODE; 01 INITIAL RELEASE; 22FEB2022; SECTION A-A; SECTION B-B

NOTES:
1.THIS IS A CAD GENERATED DRAWING.
CHANGES ON THE DRAWING TO BE EDITED FROM ORIGINAL CAD FILE.
2.MATERIAL SPECIFICATION:
oMATERIAL: ADC 12
oTHICKNESS: 2.5MM APPROX
oWEIGHT:695g APPROX
oPANTING / PLATING: RAL 9003 SIGNAL WHITE POWDER COAT WITH HIGH DAY LIGHT REFLECTION
3.GATE LOCATION TO BE APPROVED.
4.COSMETIC SURFACE: TOOLING MARKS OF ANY KIND NOT PERMITTED.
5.COSMETIC SURFACE FINISH DETAILS
6.THE PART TO BE CLEAR OF PARTINGLINE DRAG MARKS, FLASH MARKS, SINK MARKS, AND OTHER MOLDING PROCESS BLEMISHES.
MOLDED PART TO BE FREE OF MOLD RELEASE OR OTHER SURFACE CONTAMINANTS.
7.DIMENSION(S) INSIDE ARE KEY DESIGN FEATURE(S) AND ARE TO MEET APPLICABLE IN-PROCESS INSPECTION STANDARDS.
8.DESIGNATED AREA FOR PART ID, DATE AND RECYCLEING MATERIAL ONLY.
9.UNLESS OTHERWISE SPECIFIED TOLERANCE SHOULD MATCH TO ISO-8062-3:2007.

TOLERANCE UNLESS
OTHERWISE SPECIFIED IN mm .XXX 0.001

This drawing is protected by copyright law. The author reserves all rights. The drawing is to be treated confidentially and may be used only by the person receiving permission from the author and only for the purpose
agreed on. Without the prior written consent of the author, neither the drawing, nor copies of the drawing, nor other reproductions of the contents, in whole or in part, may be made available to third parties or
misused in any other way.

8 | 7 | 6 | 5 | 4 | 3 | 2 | 1

E

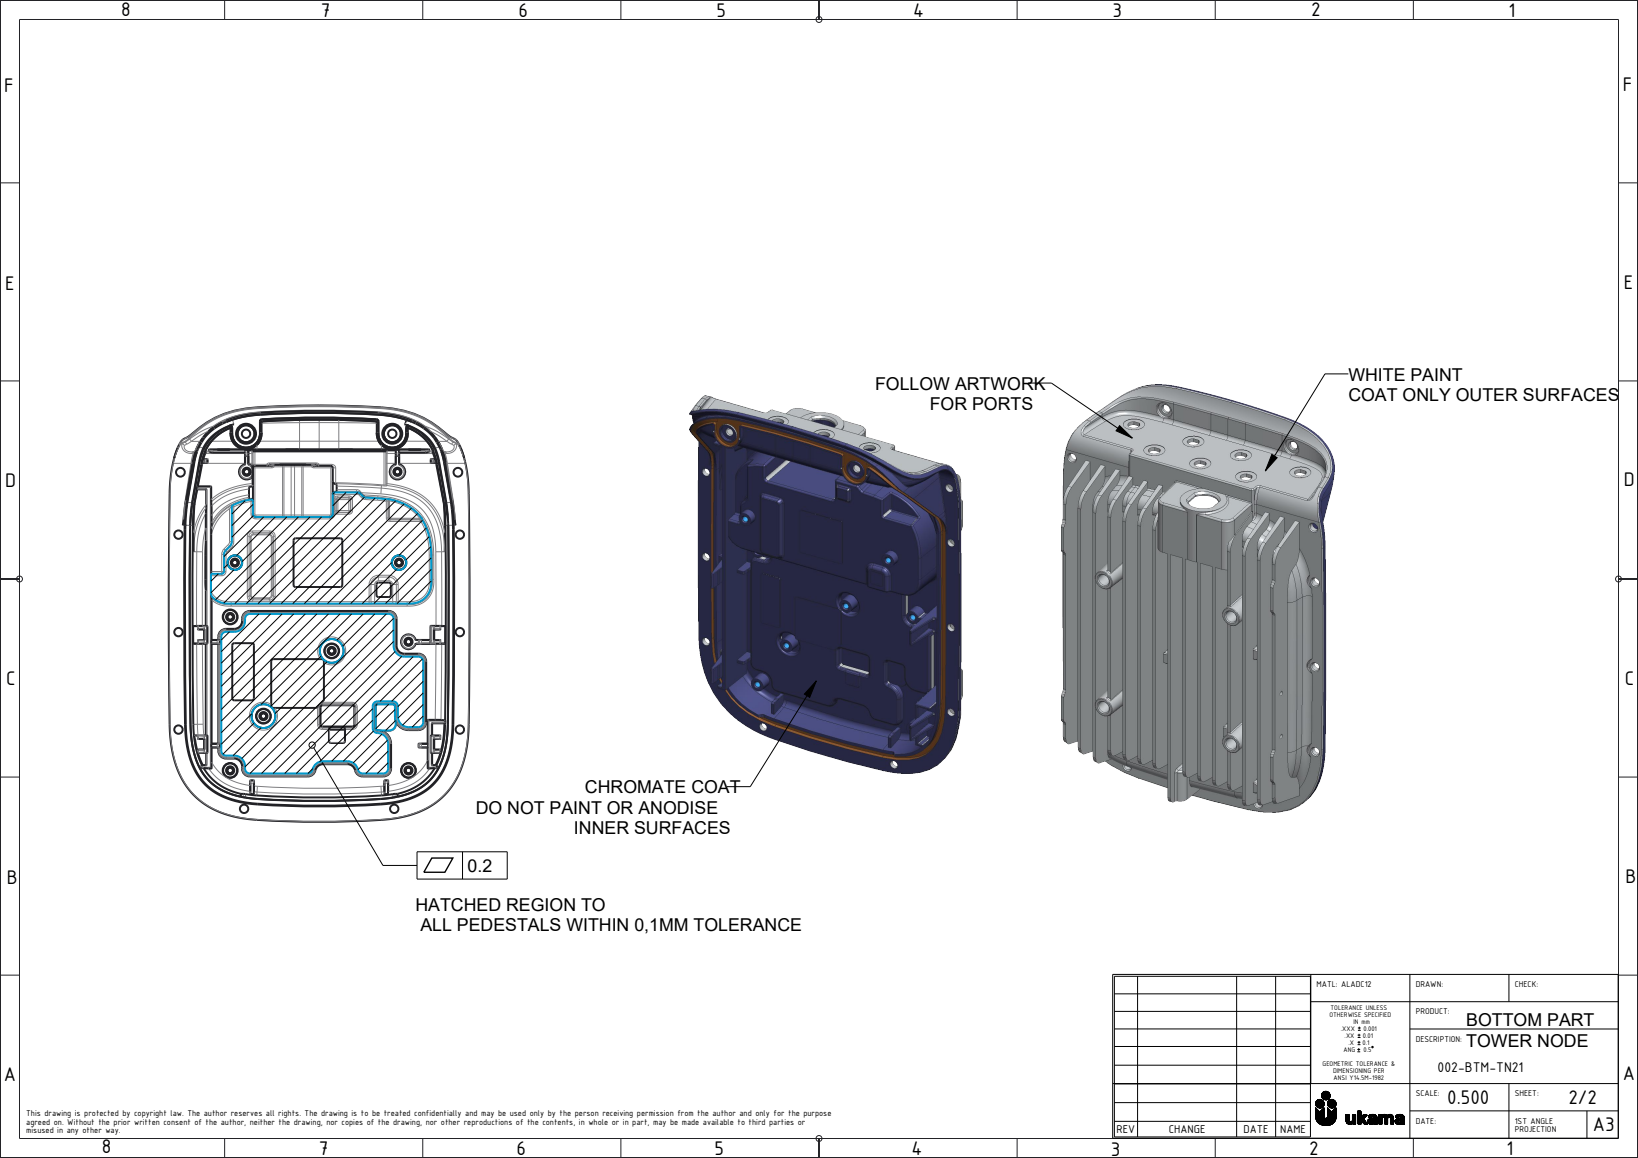
[picture p64: page 2]
002-BTM-TN21; MATL: ALADC12; DRAWN:; CHECK:; .XX 0.01 .X 0.1 ANG 0.5; GEOMETRIC TOLERANCE & DIMENSIONING PER; ANSI Y14.5M-1982; PRODUCT:; DESCRIPTION:; SCALE:; SHEET:; DATE:; 1ST ANGLE; REV; CHANGE; DATE NAME; PROJECTION; BOTTOM PART TOWER NODE; CHROMATE COAT; INNER SURFACES; WHITE PAINT

COAT ONLY OUTER SURFACES FOLLOW ARTWORK
FOR PORTS

DO NOT PAINT OR ANODISE

HATCHED REGION TO
ALL PEDESTALS WITHIN 0,1MM TOLERANCE

TOLERANCE UNLESS
OTHERWISE SPECIFIED IN mm .XXX 0.001

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
