ukama/ukama-nodes/mechanics/nodes/tower/drawings/top_tower_node.pdf

A

X | X

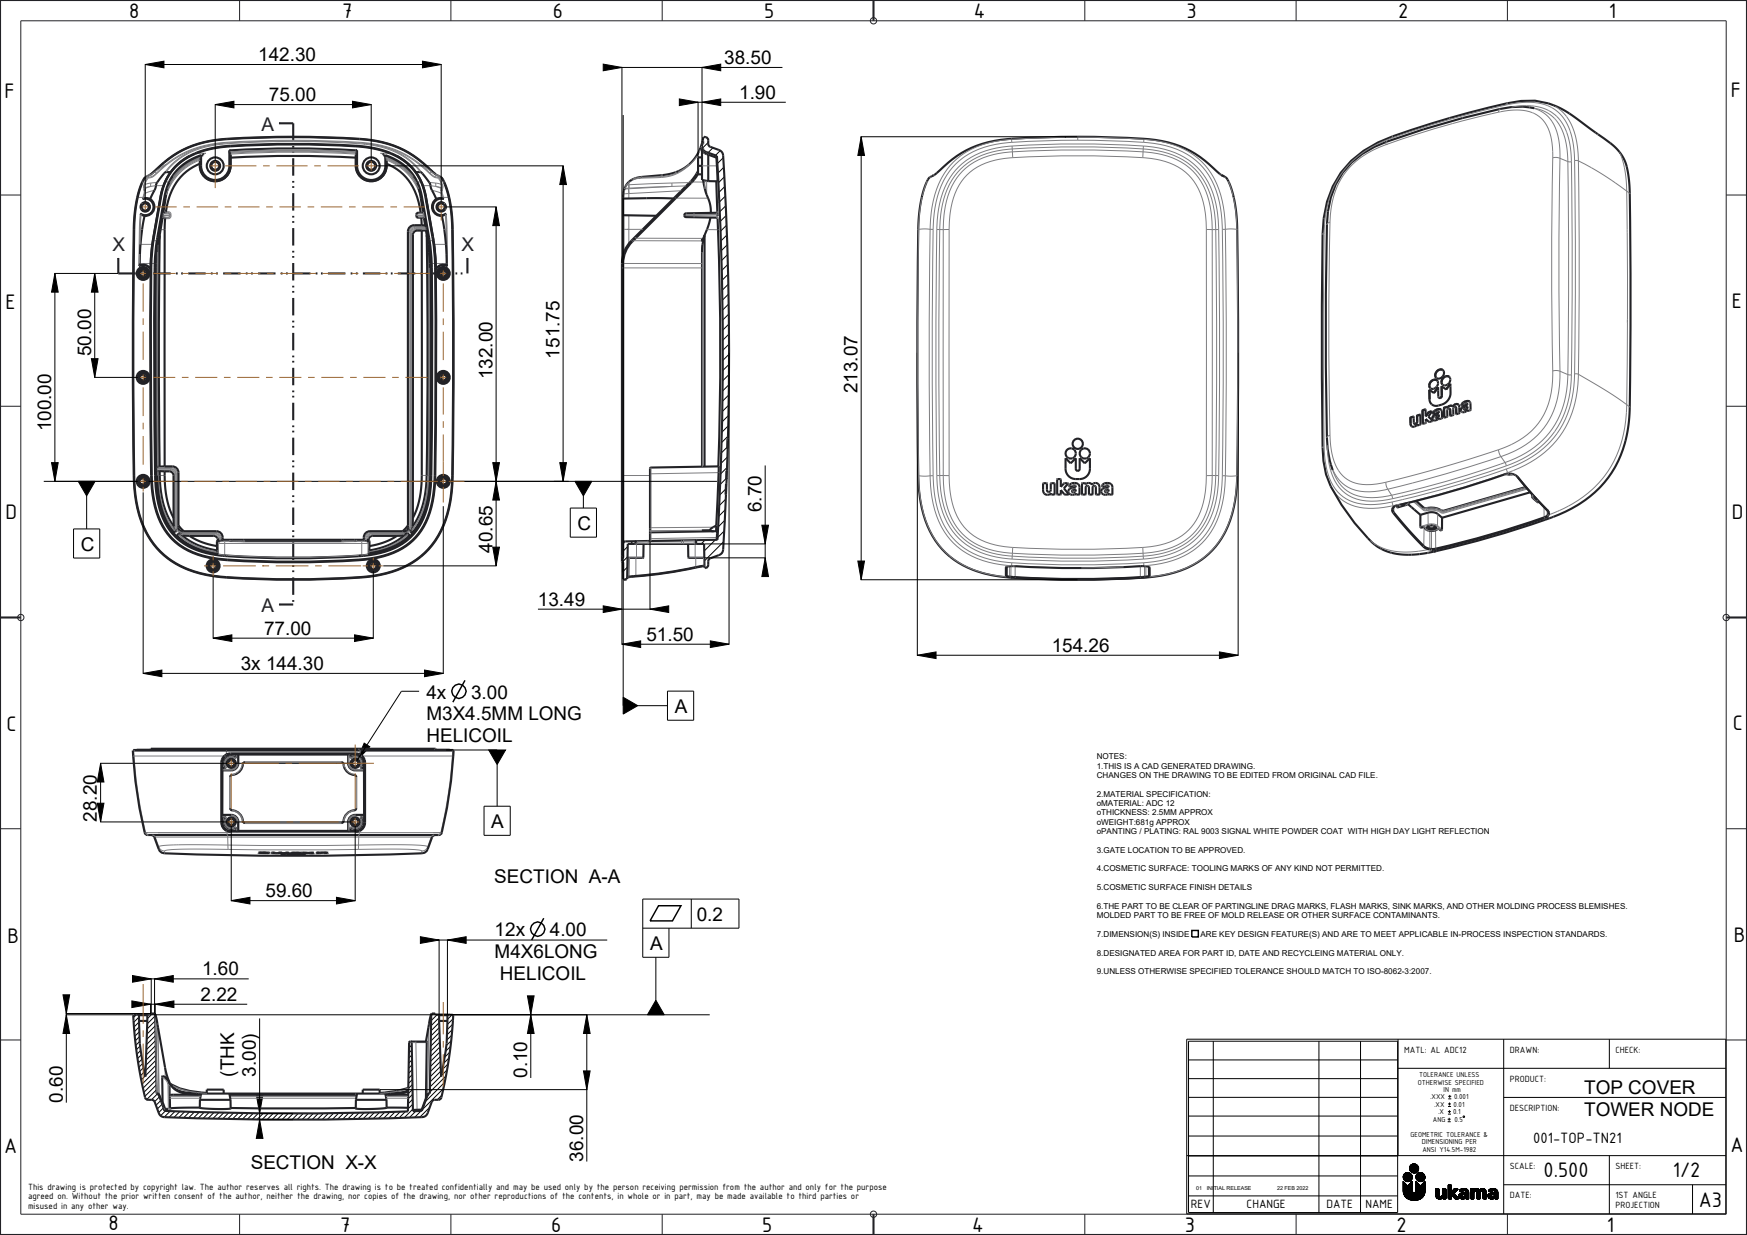
[picture p65: page 1]
001-TOP-TN21; 12x 4.00 M4X6LONG HELICOIL; 4x 3.00 M3X4.5MM LONG HELICOIL; 1.60(THK; MATL: AL ADC12; DRAWN:; CHECK:; .XX 0.01 .X 0.1 ANG 0.5; GEOMETRIC TOLERANCE & DIMENSIONING PER; ANSI Y14.5M-1982; PRODUCT:; DESCRIPTION:; SCALE:; SHEET:; DATE:; 1ST ANGLE; REV; CHANGE; DATE NAME; PROJECTION; 01 INITIAL RELEASE; 22 FEB 2022; TOP COVER TOWER NODE; SECTION A-A; SECTION X-X

NOTES:
1.THIS IS A CAD GENERATED DRAWING.
CHANGES ON THE DRAWING TO BE EDITED FROM ORIGINAL CAD FILE.
2.MATERIAL SPECIFICATION:
oMATERIAL: ADC 12
oTHICKNESS: 2.5MM APPROX
oWEIGHT:681g APPROX
oPANTING / PLATING: RAL 9003 SIGNAL WHITE POWDER COAT WITH HIGH DAY LIGHT REFLECTION
3.GATE LOCATION TO BE APPROVED.
4.COSMETIC SURFACE: TOOLING MARKS OF ANY KIND NOT PERMITTED.
5.COSMETIC SURFACE FINISH DETAILS
6.THE PART TO BE CLEAR OF PARTINGLINE DRAG MARKS, FLASH MARKS, SINK MARKS, AND OTHER MOLDING PROCESS BLEMISHES.
MOLDED PART TO BE FREE OF MOLD RELEASE OR OTHER SURFACE CONTAMINANTS.
7.DIMENSION(S) INSIDE ARE KEY DESIGN FEATURE(S) AND ARE TO MEET APPLICABLE IN-PROCESS INSPECTION STANDARDS.
8.DESIGNATED AREA FOR PART ID, DATE AND RECYCLEING MATERIAL ONLY.
9.UNLESS OTHERWISE SPECIFIED TOLERANCE SHOULD MATCH TO ISO-8062-3:2007.

TOLERANCE UNLESS
OTHERWISE SPECIFIED IN mm .XXX 0.001

This drawing is protected by copyright law. The author reserves all rights. The drawing is to be treated confidentially and may be used only by the person receiving permission from the author and only for the purpose
agreed on. Without the prior written consent of the author, neither the drawing, nor copies of the drawing, nor other reproductions of the contents, in whole or in part, may be made available to third parties or
misused in any other way.

8 | 7 | 6 | 5 | 4 | 3 | 2 | 1

E

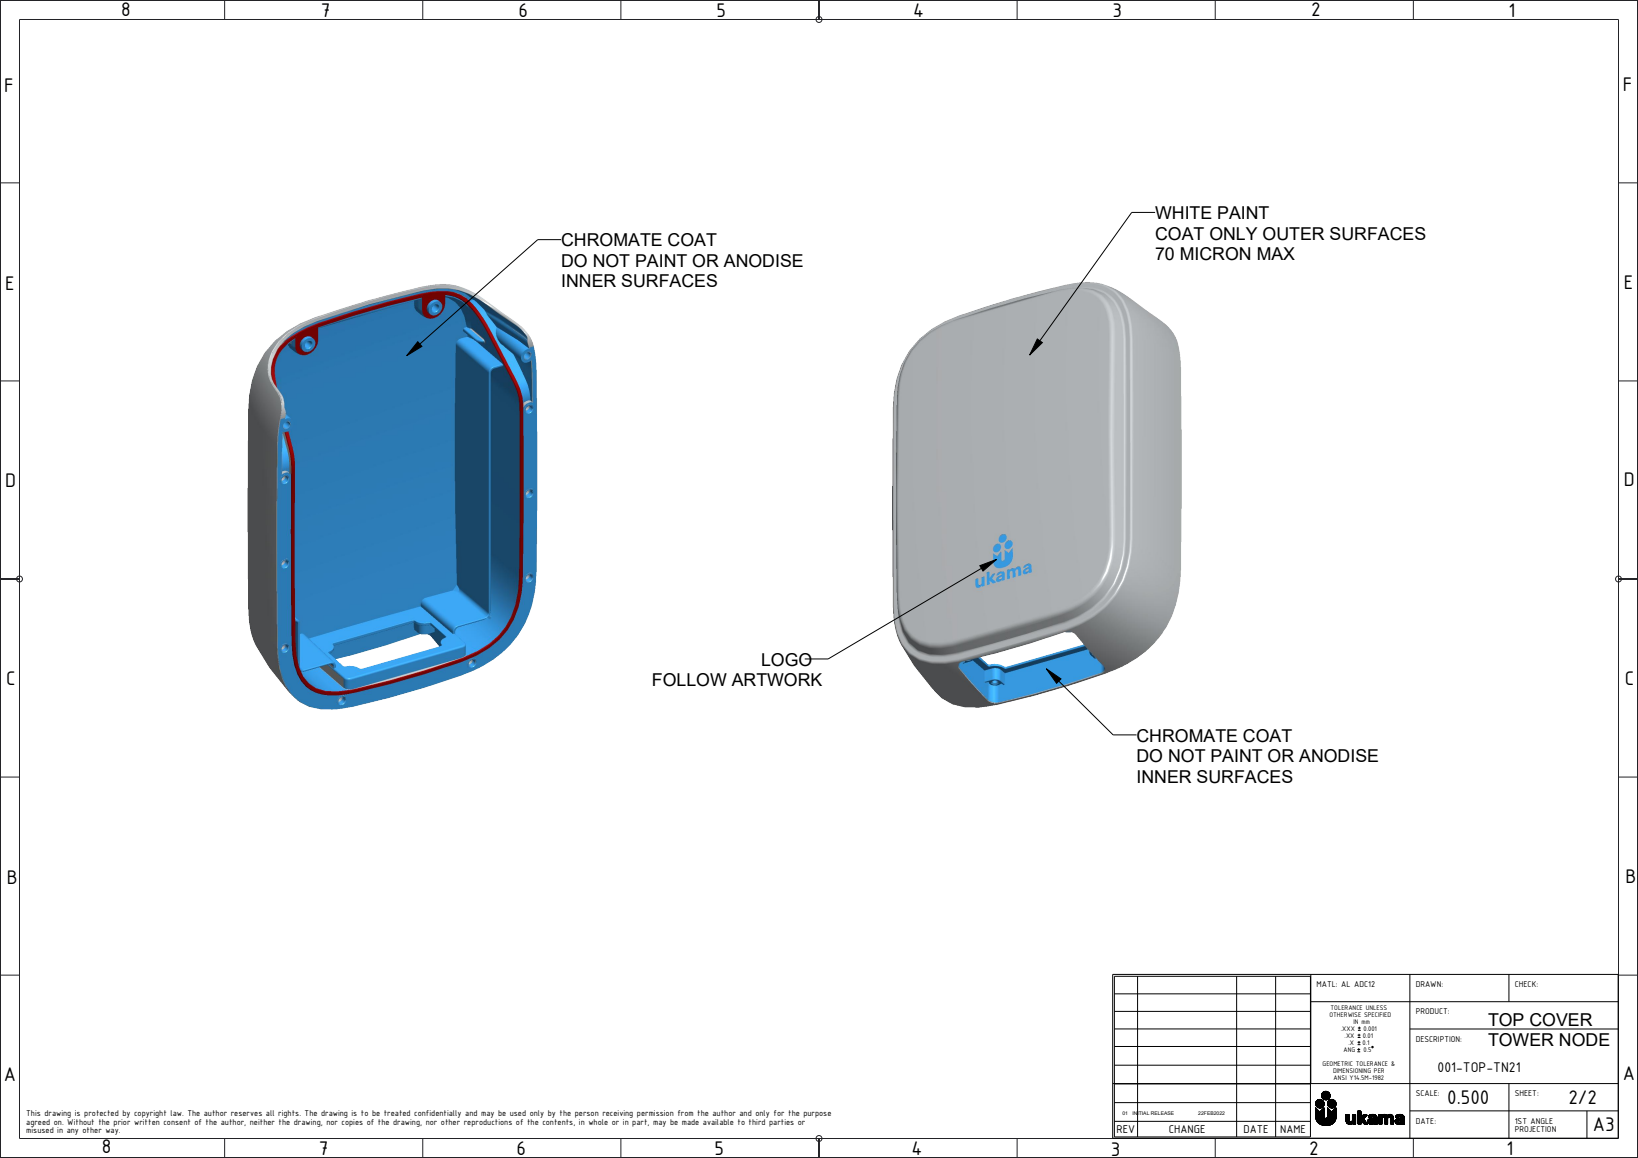
[picture p66: page 2]
001-TOP-TN21; MATL: AL ADC12; DRAWN:; CHECK:; .XX 0.01 .X 0.1 ANG 0.5; GEOMETRIC TOLERANCE & DIMENSIONING PER; ANSI Y14.5M-1982; PRODUCT:; DESCRIPTION:; SCALE:; SHEET:; DATE:; 1ST ANGLE; REV; CHANGE; DATE NAME; PROJECTION; TOP COVER TOWER NODE; 01 INITIAL RELEASE; 22FEB2022; LOGO FOLLOW ARTWORK

WHITE PAINT
COAT ONLY OUTER SURFACES
70 MICRON MAX

CHROMATE COAT
DO NOT PAINT OR ANODISE
INNER SURFACES

TOLERANCE UNLESS
OTHERWISE SPECIFIED IN mm .XXX 0.001

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
