ukama/ukama-nodes/electronics/fe/30dBm/B40/schematics/FEMA_B40_V0P18_31_11_20.pdf

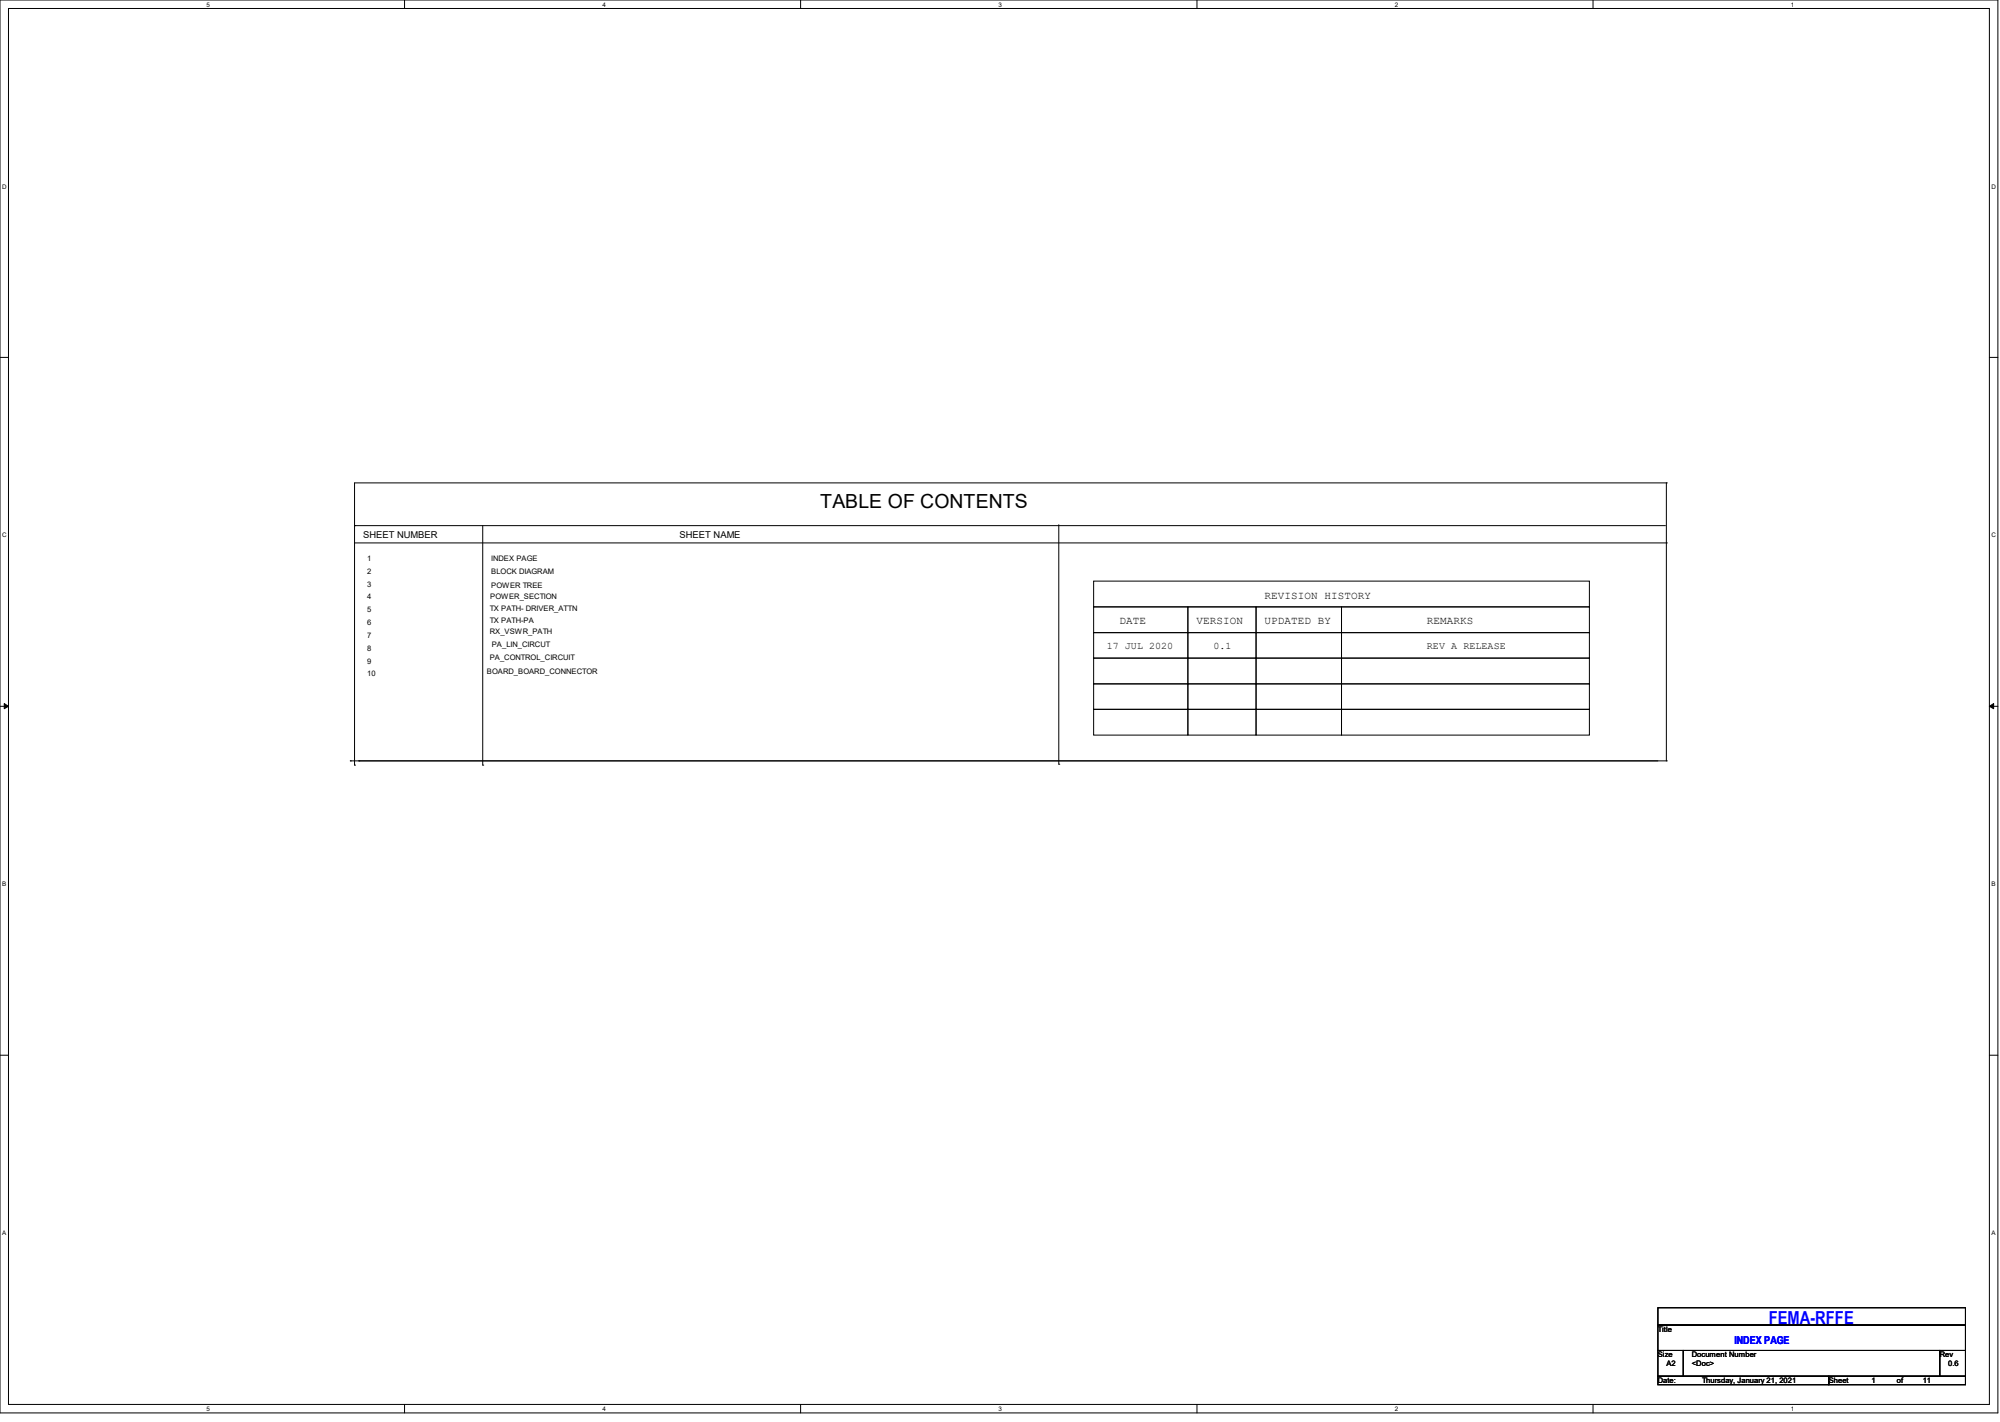
[picture p67: page 1]
17 JUL 2020; SHEET NUMBER; SHEET NAME; REV A RELEASE; PA_LIN_CIRCUT 8; BOARD_BOARD_CONNECTOR; PA_CONTROL_CIRCUIT; REVISION HISTORY; DATE; VERSION; UPDATED BY; REMARKS; FEMA-RFFE Title Size; Document Number; Rev Date:; Sheet; of <Doc>; INDEX PAGE A2; Thursday, January 21, 2021; 11 Title Size

TABLE OF CONTENTS

INDEX PAGE
BLOCK DIAGRAM
POWER TREE
POWER_SECTION
TX PATH- DRIVER_ATTN
TX PATH-PA
RX_VSWR_PATH

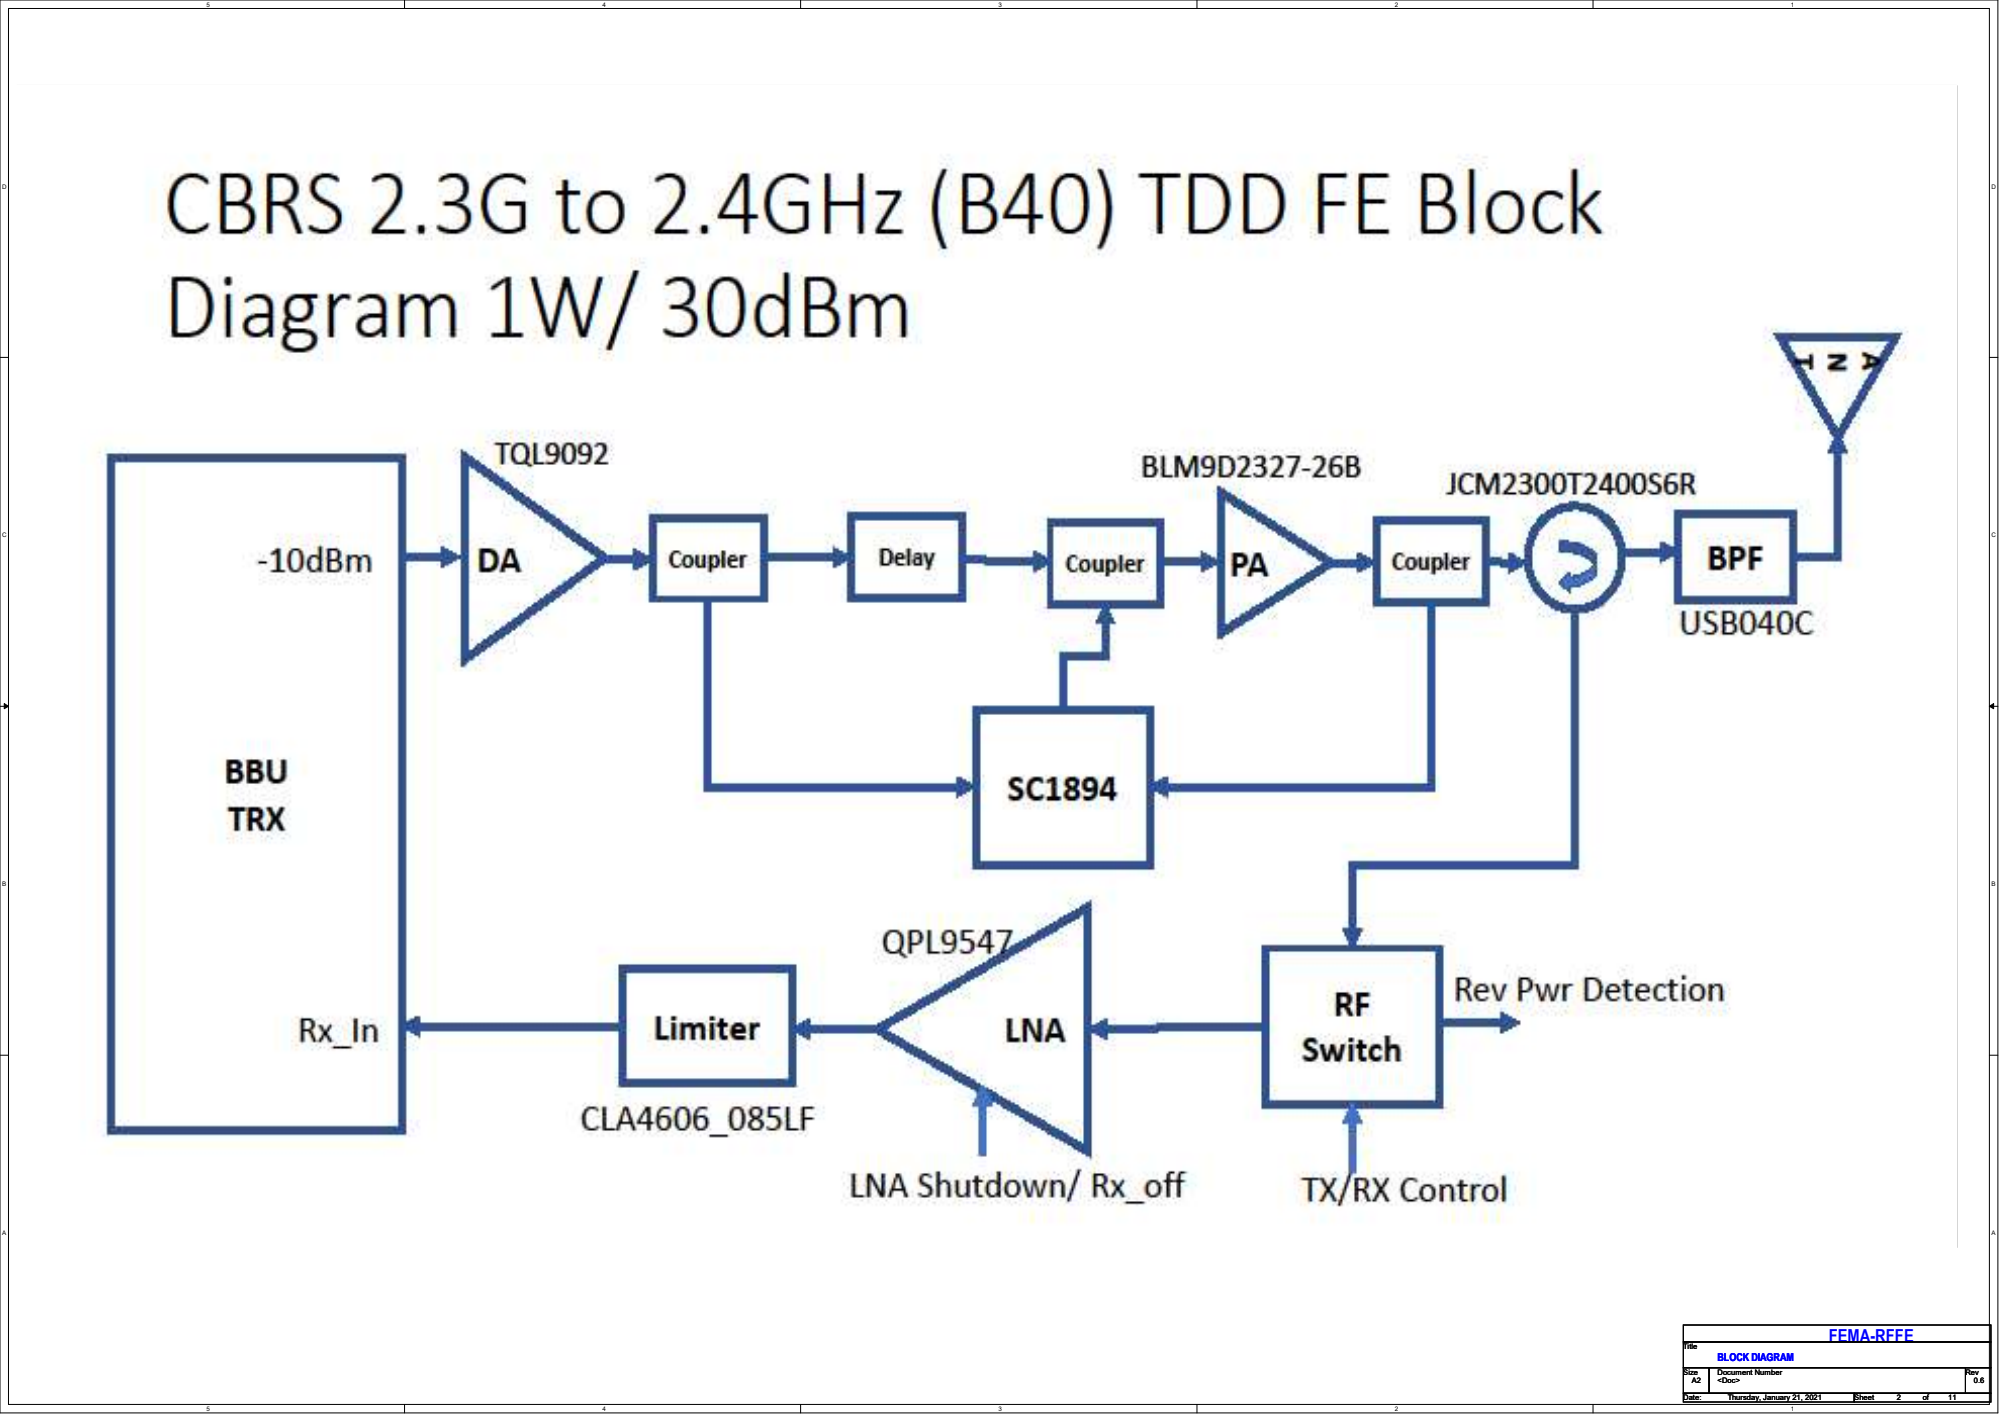
[picture p68: page 2]
BLOCK DIAGRAM A2; Thursday, January 21, 2021; 11 Title Size; Document Number; Rev Date:; Sheet; of <Doc>

Document Number FEMA-RFFE Title Size Sheet of <Doc> | Rev Date: 0.6

BLOCK DIAGRAM A2 Thursday, January 21, 2021 2 11

Power Connector | Common Mode Filter

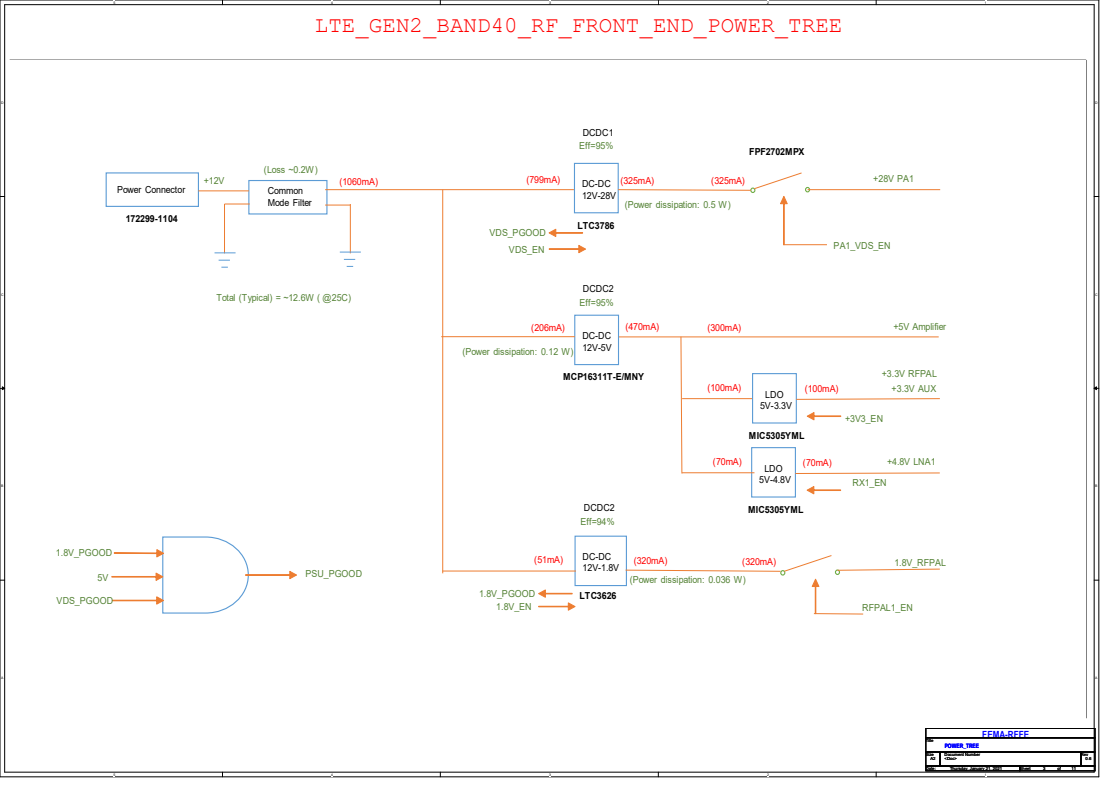
[picture p69: page 3]
Total (Typical) = ~12.6W ( @25C); (Loss ~0.2W); DCDC1 Eff=95%; FPF2702MPX; LTC3786; PA1_VDS_EN; VDS_PGOOD VDS_EN; DCDC2 Eff=95%; MCP16311T-E/MNY; +5V Amplifier; LDO 5V-3.3V; MIC5305YML; LDO 5V-4.8V; +3.3V RFPAL +3.3V AUX; +4.8V LNA1; DCDC2 Eff=94%; LTC3626; 1.8V_PGOOD 1.8V_EN; 1.8V_RFPAL; RFPAL1_EN; 1.8V_PGOOD; VDS_PGOOD; PSU_PGOOD; (Power dissipation: 0.5 W); (Power dissipation: 0.12 W); (Power dissipation: 0.036 W); LTE_GEN2_BAND40_RF_FRONT_END_POWER_TREE; FEMA-RFFE Title Size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

# 12V_5p5V_DCDC 5V5_3V3_LDO

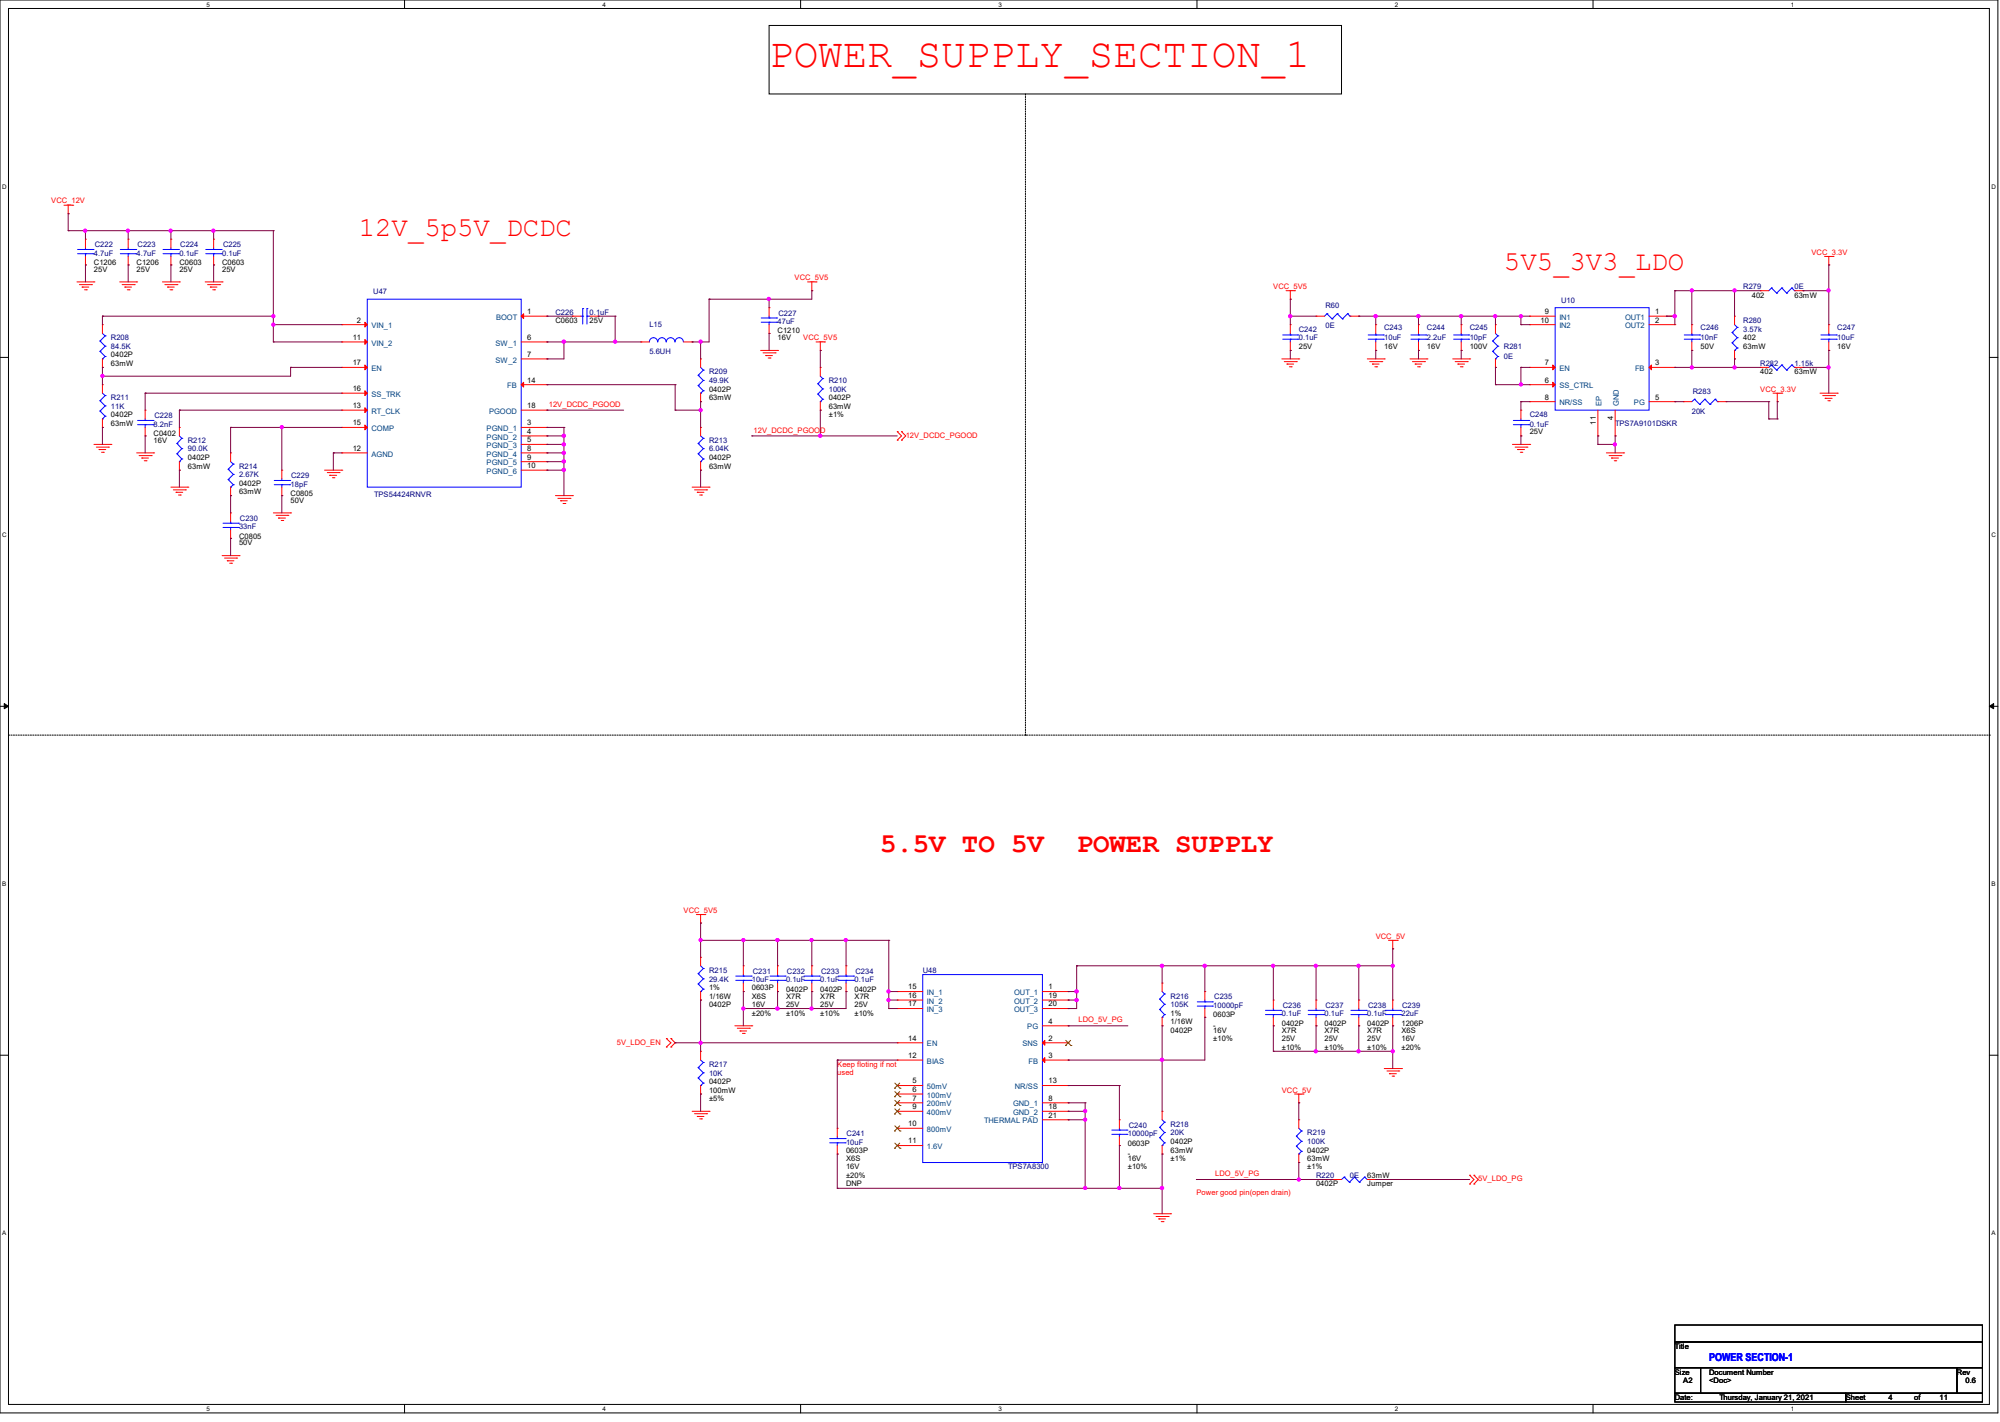
[picture p70: page 4]

Keep floting if not
used

Power good pin(open drain)

# 12V_1V8_DCDC

# POWER_SUPPLY_SECTION_2

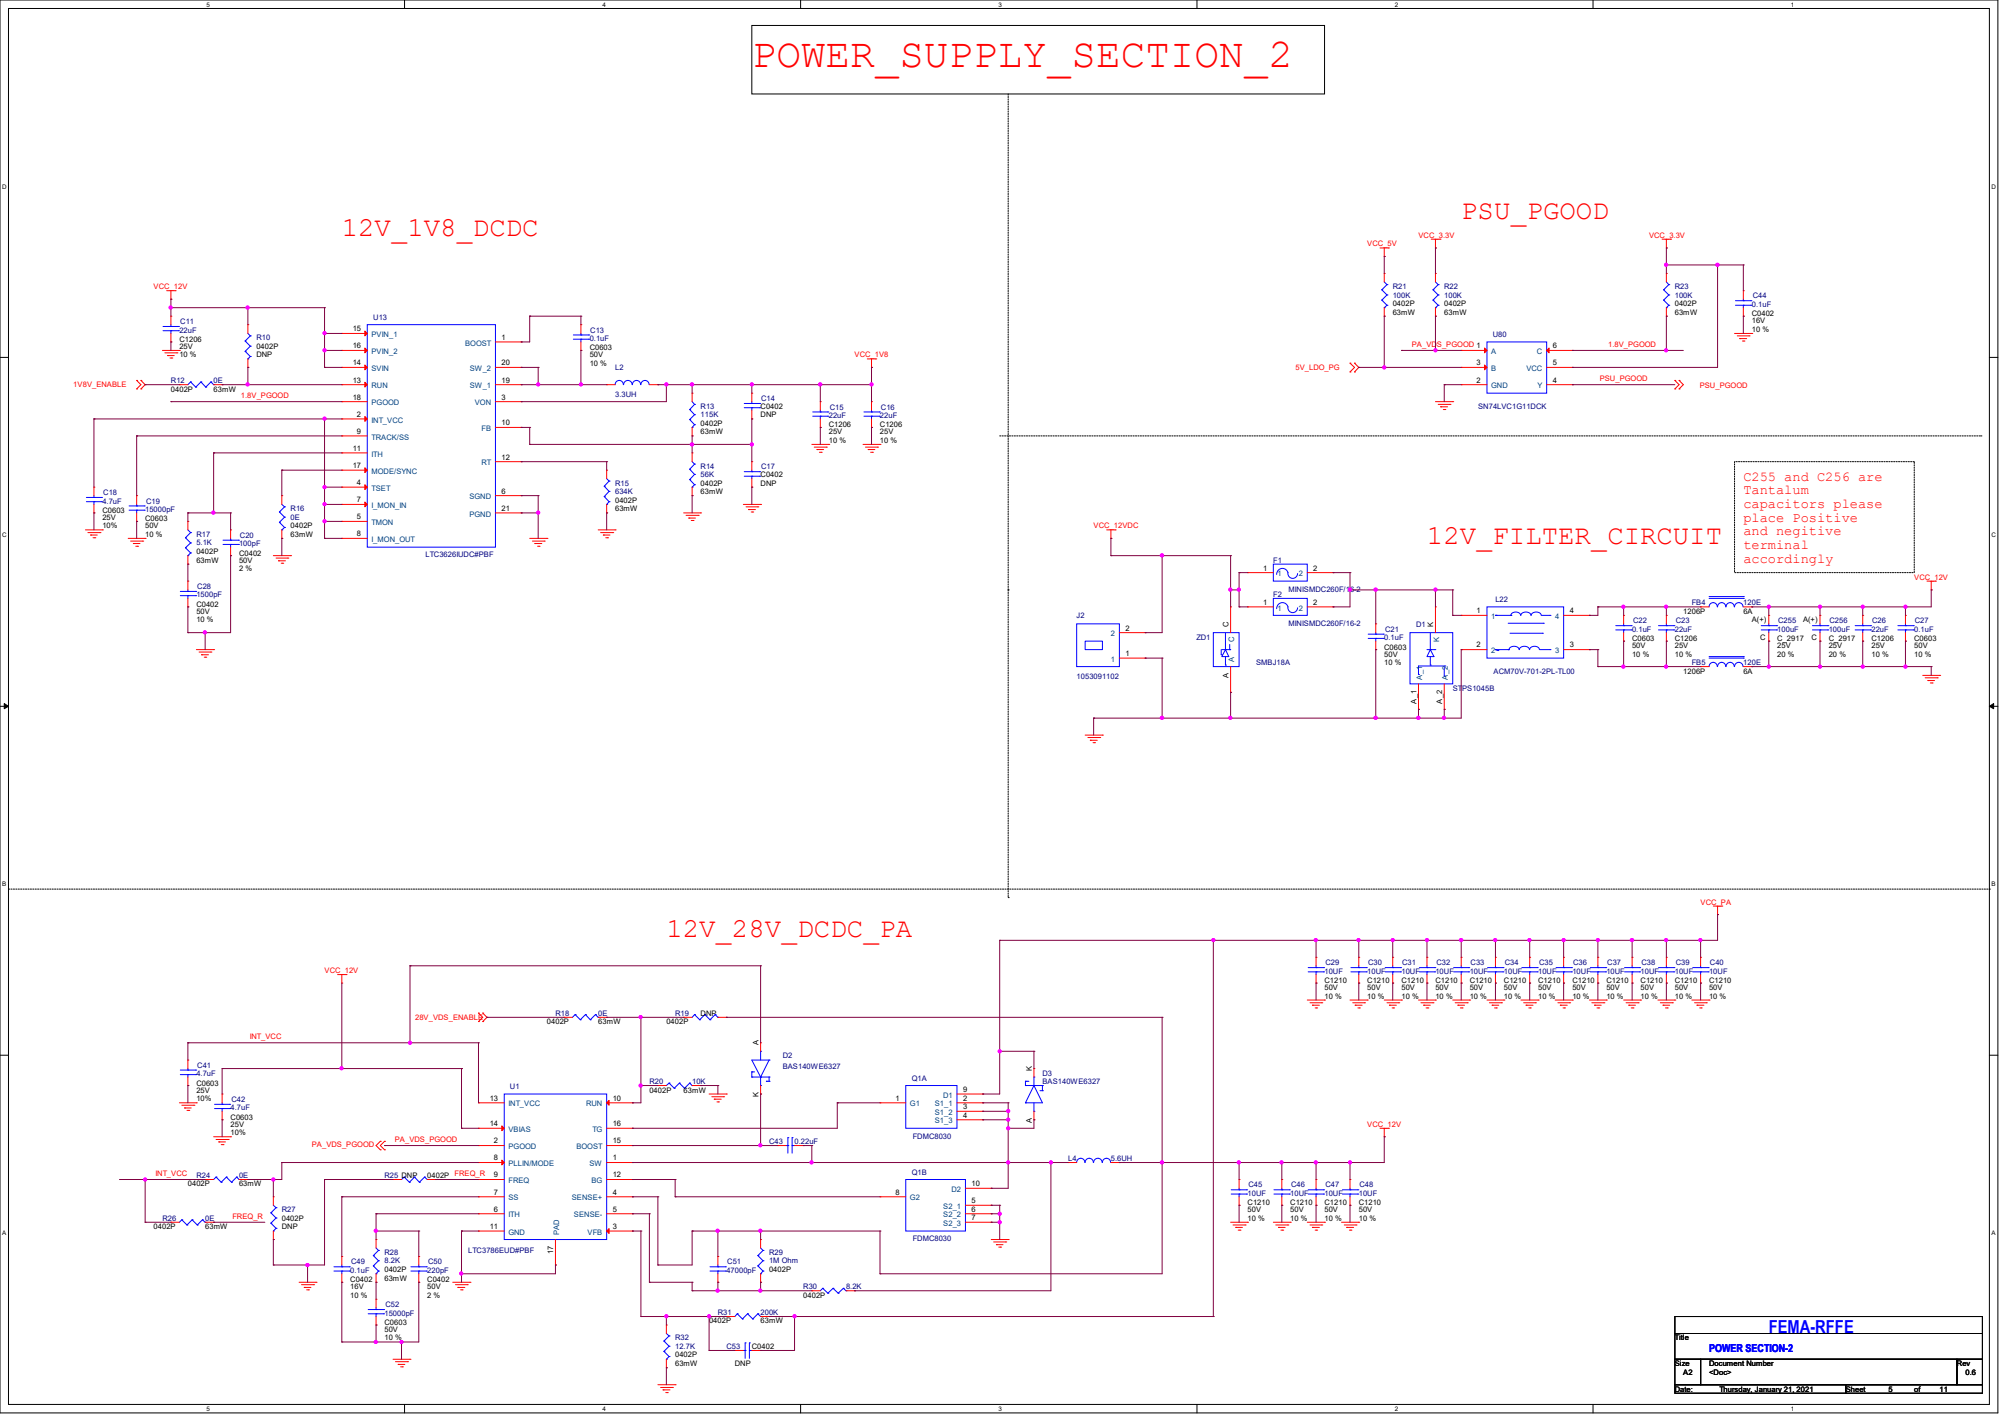
[picture p71: page 5]

# TX_INPUT

# TX PATH- DRIVER_ATTN

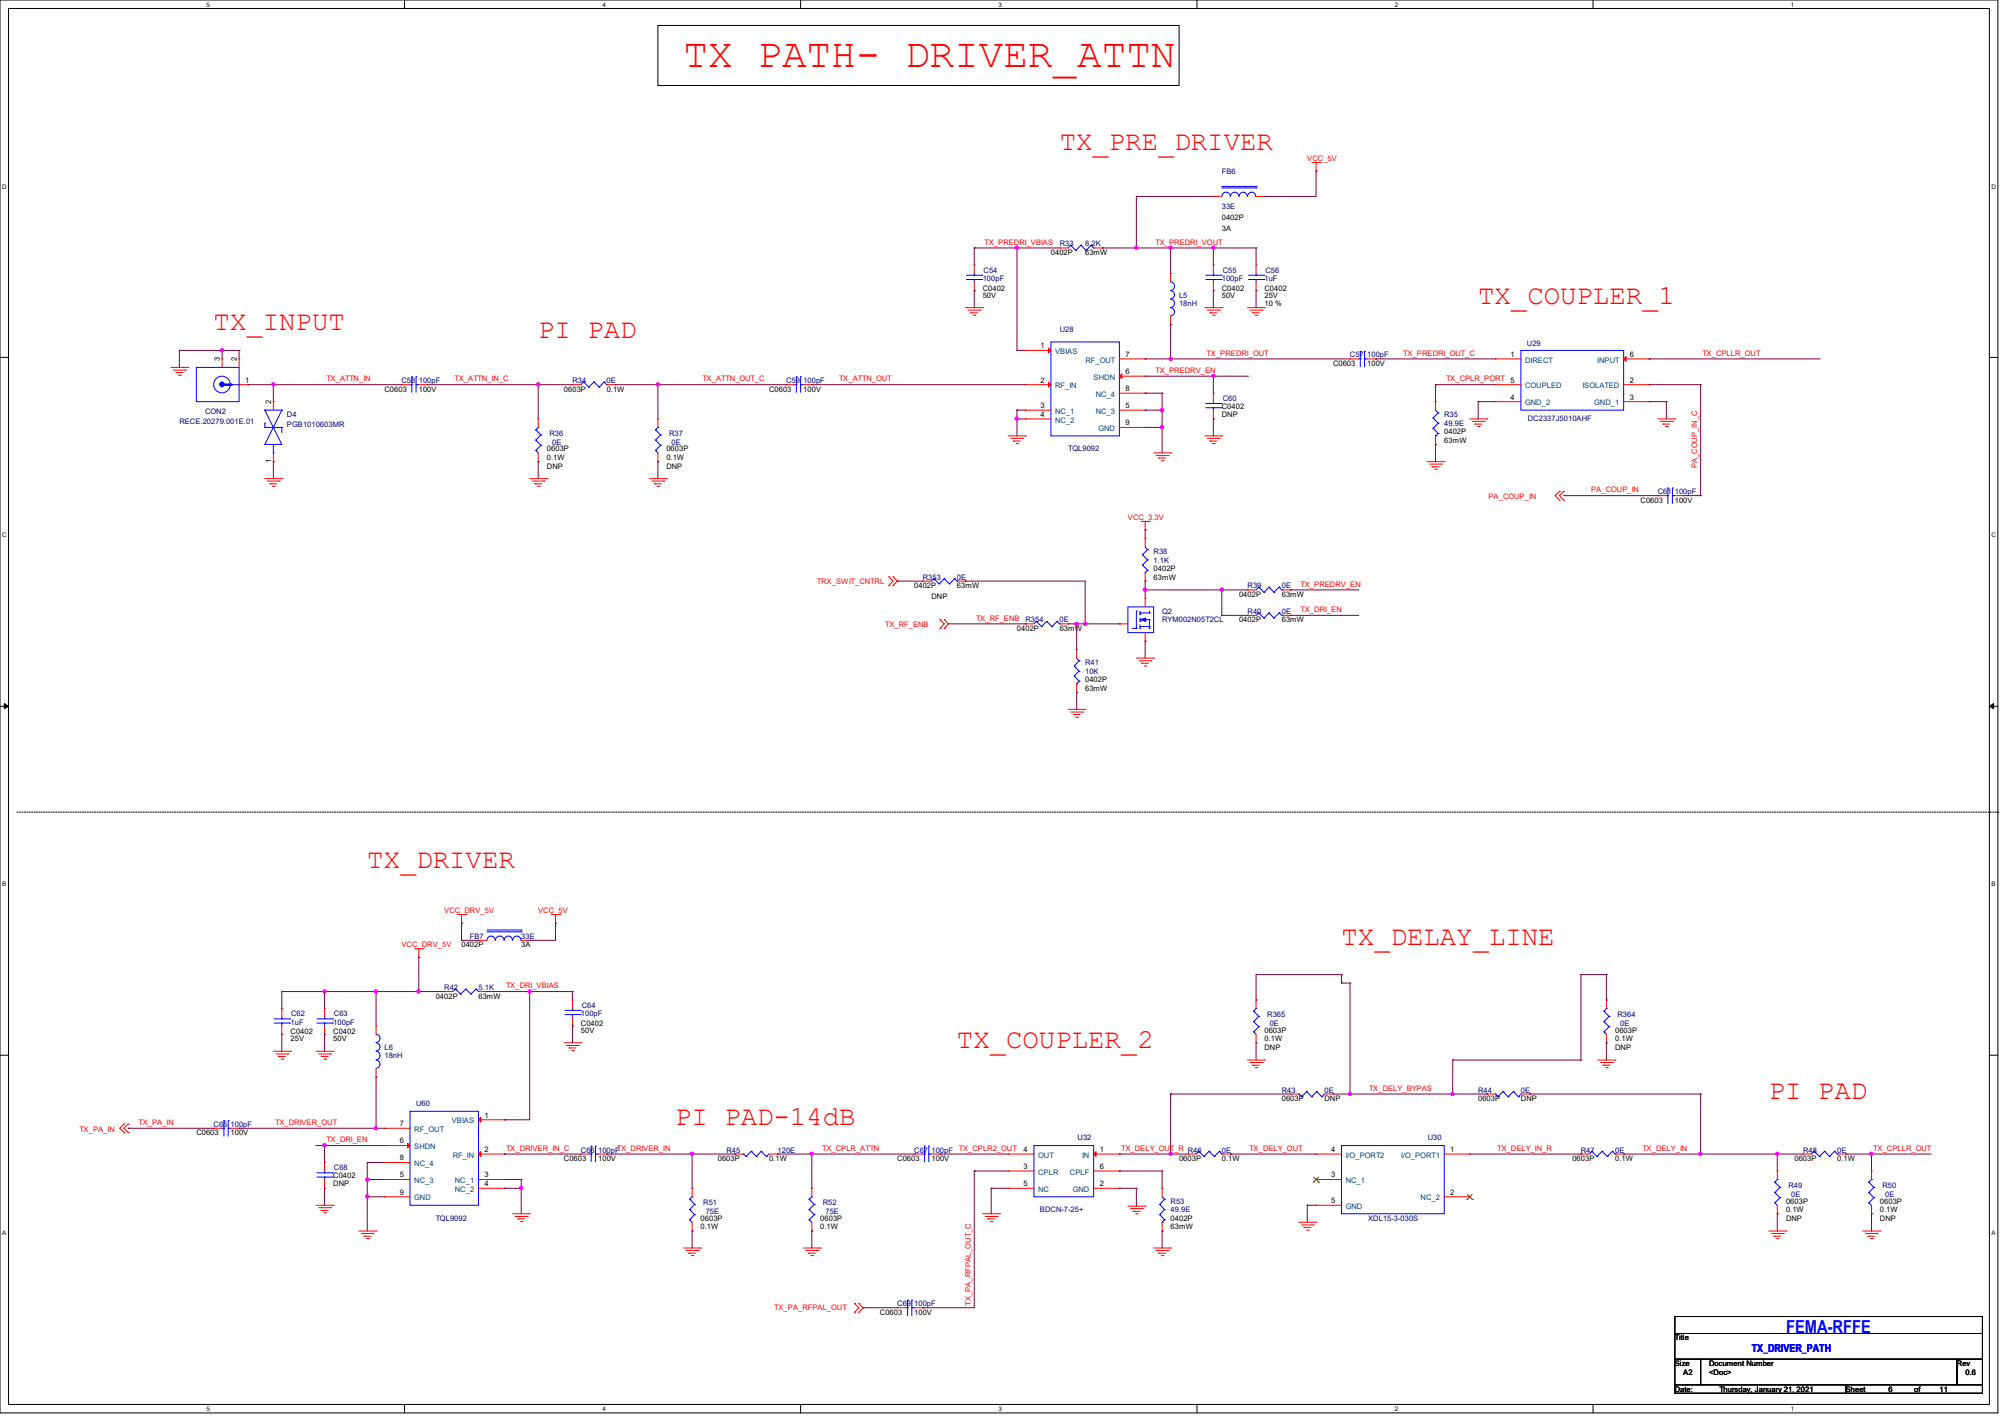
[picture p72: page 6]

# TX _PA

TX PATH- PA SECTION VDS_PA1 | VDS_PA1

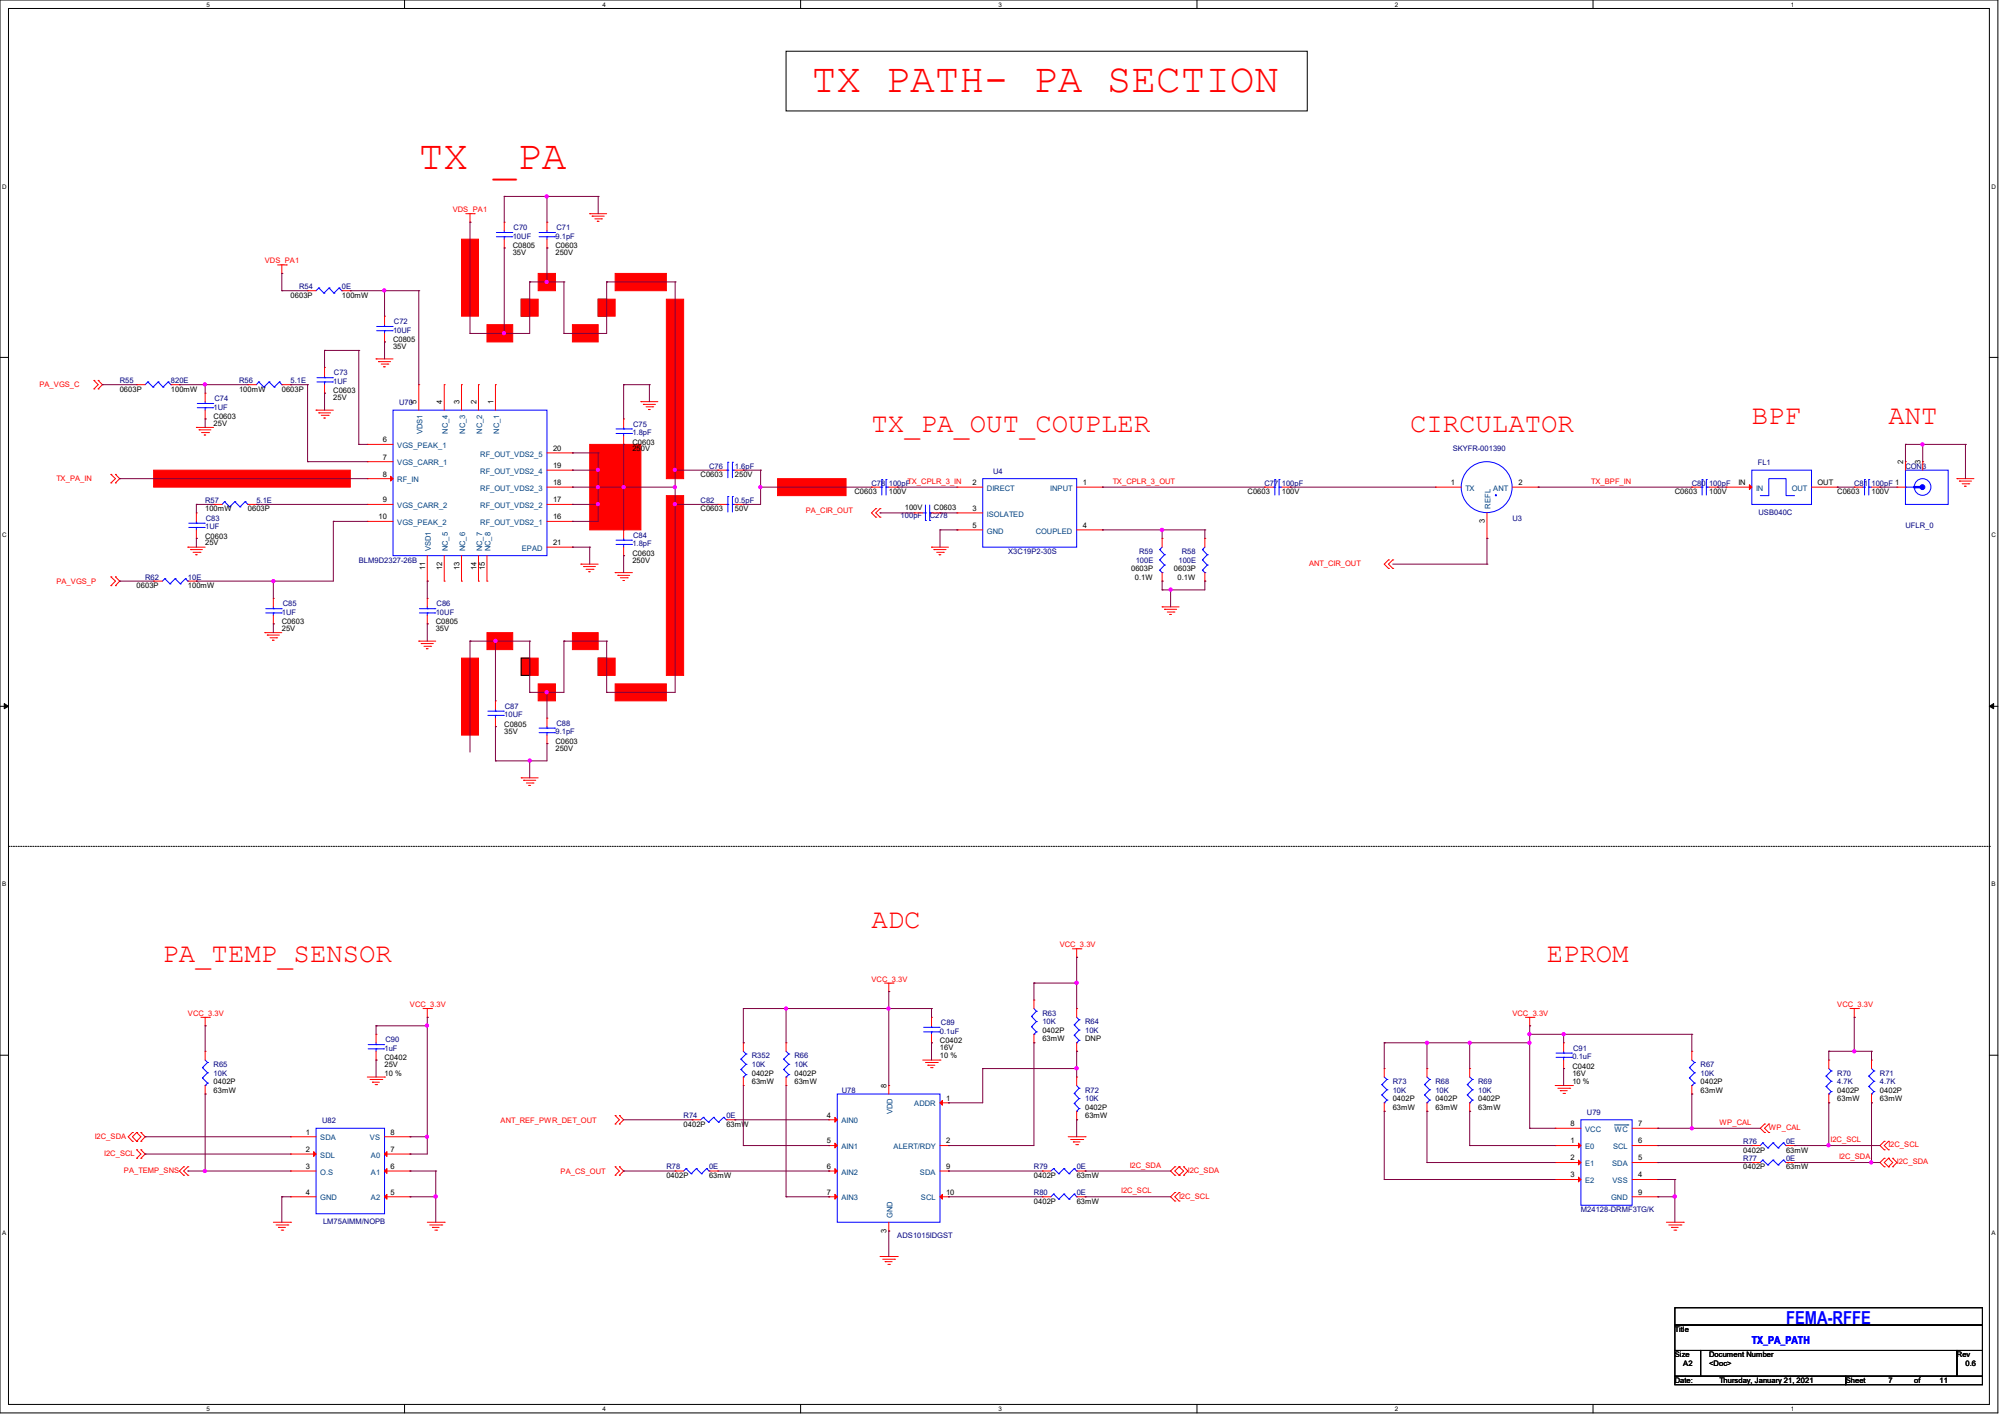
[picture p73: page 7]

# TRX_SWITCH

# PI_PAD

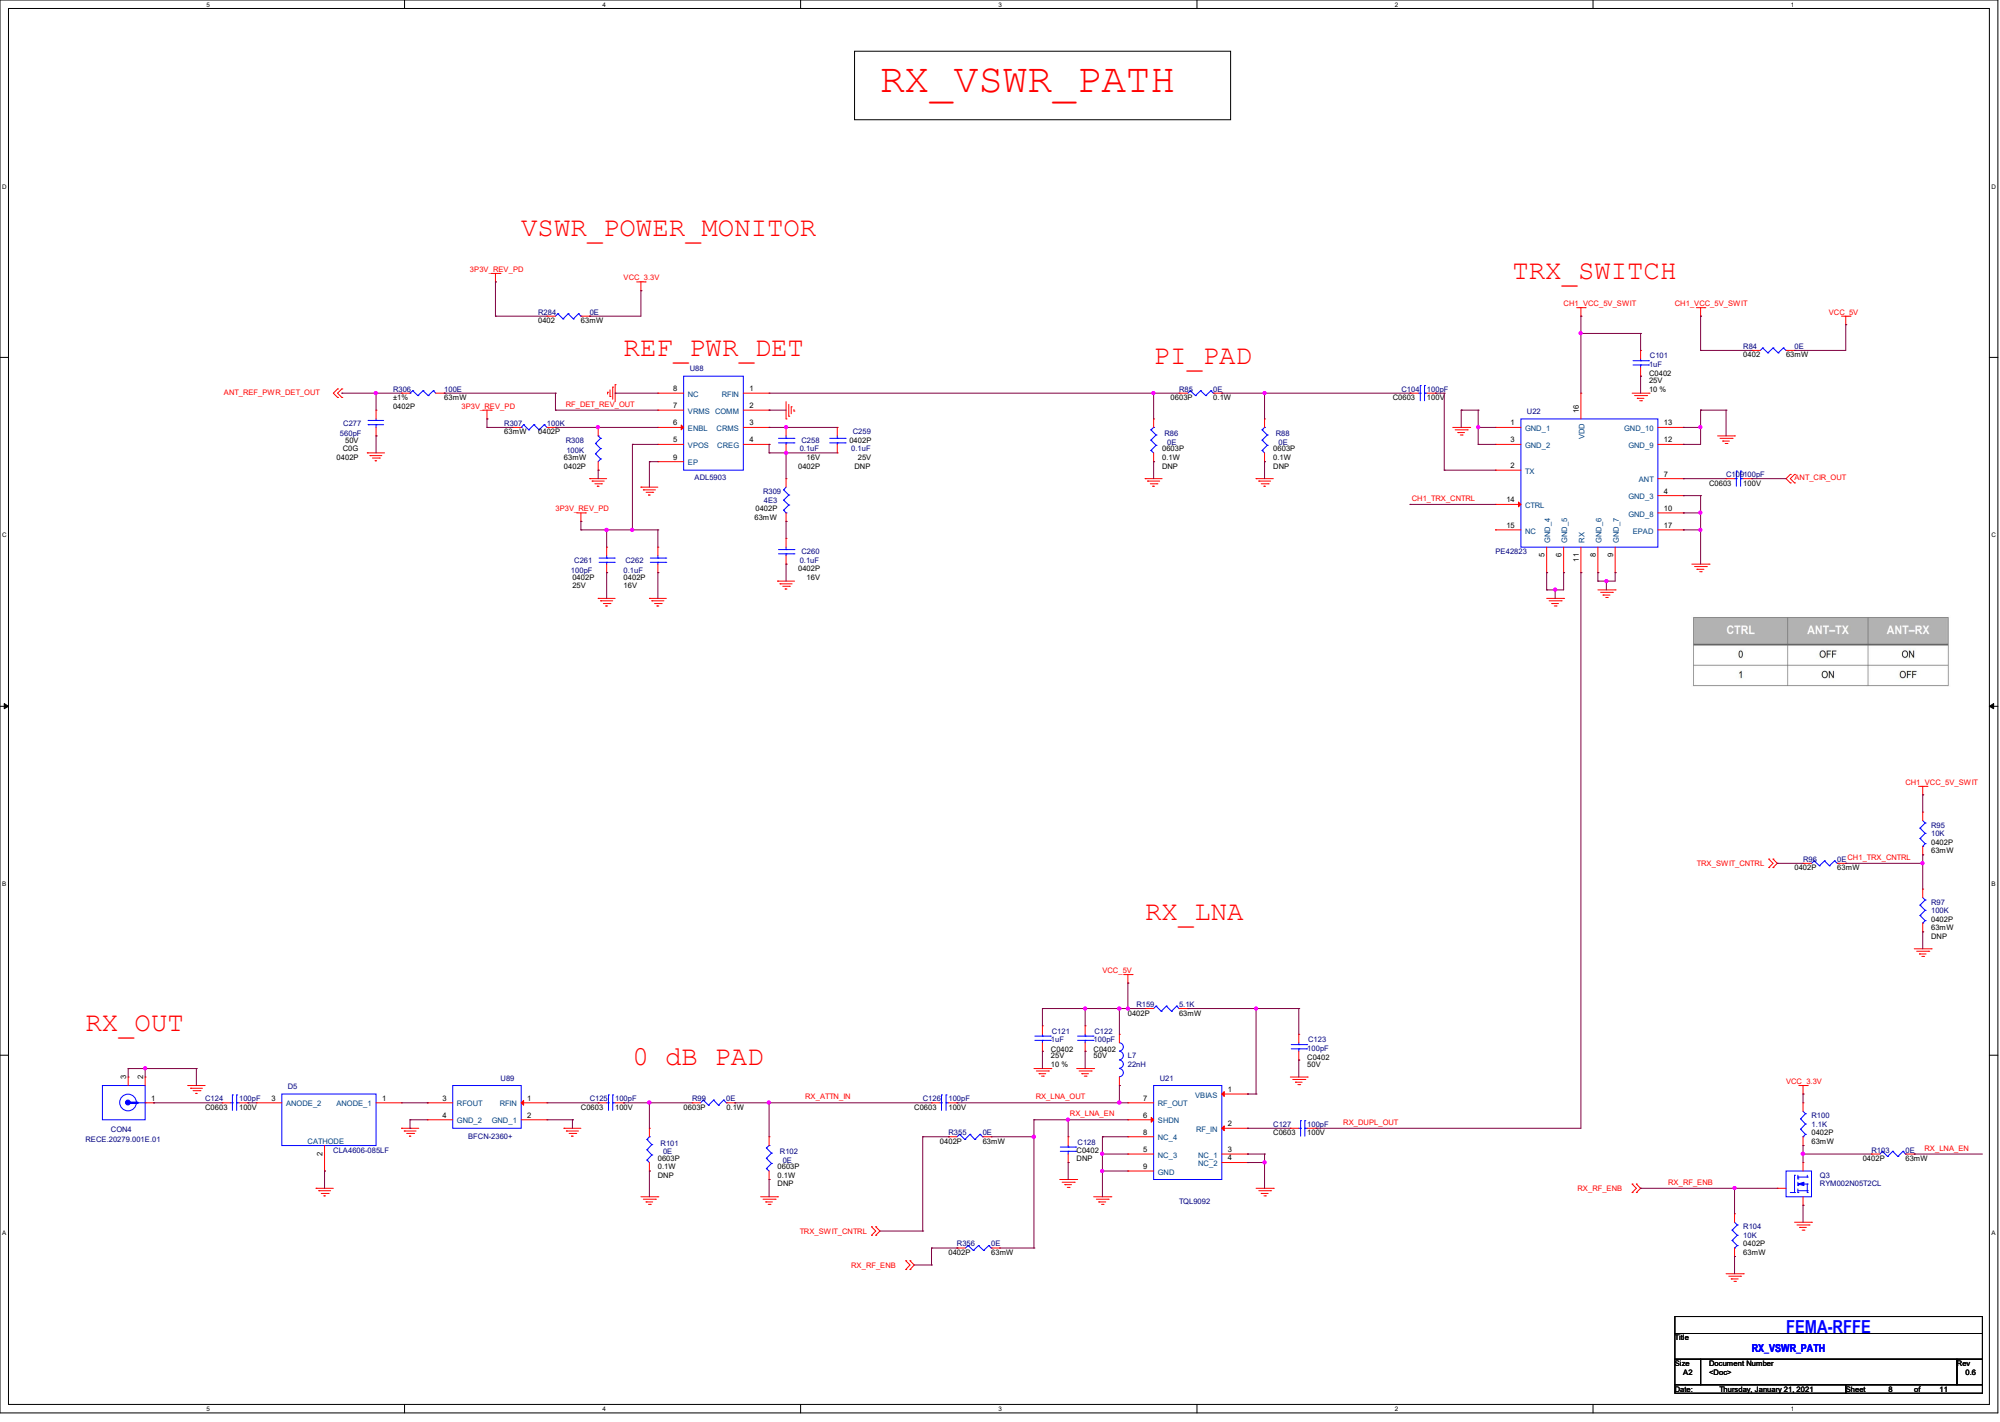
[picture p74: page 8]

# TX PATH-PA_LIN_CIRCUIT

# TX_RFPAL_RF_CNTRL

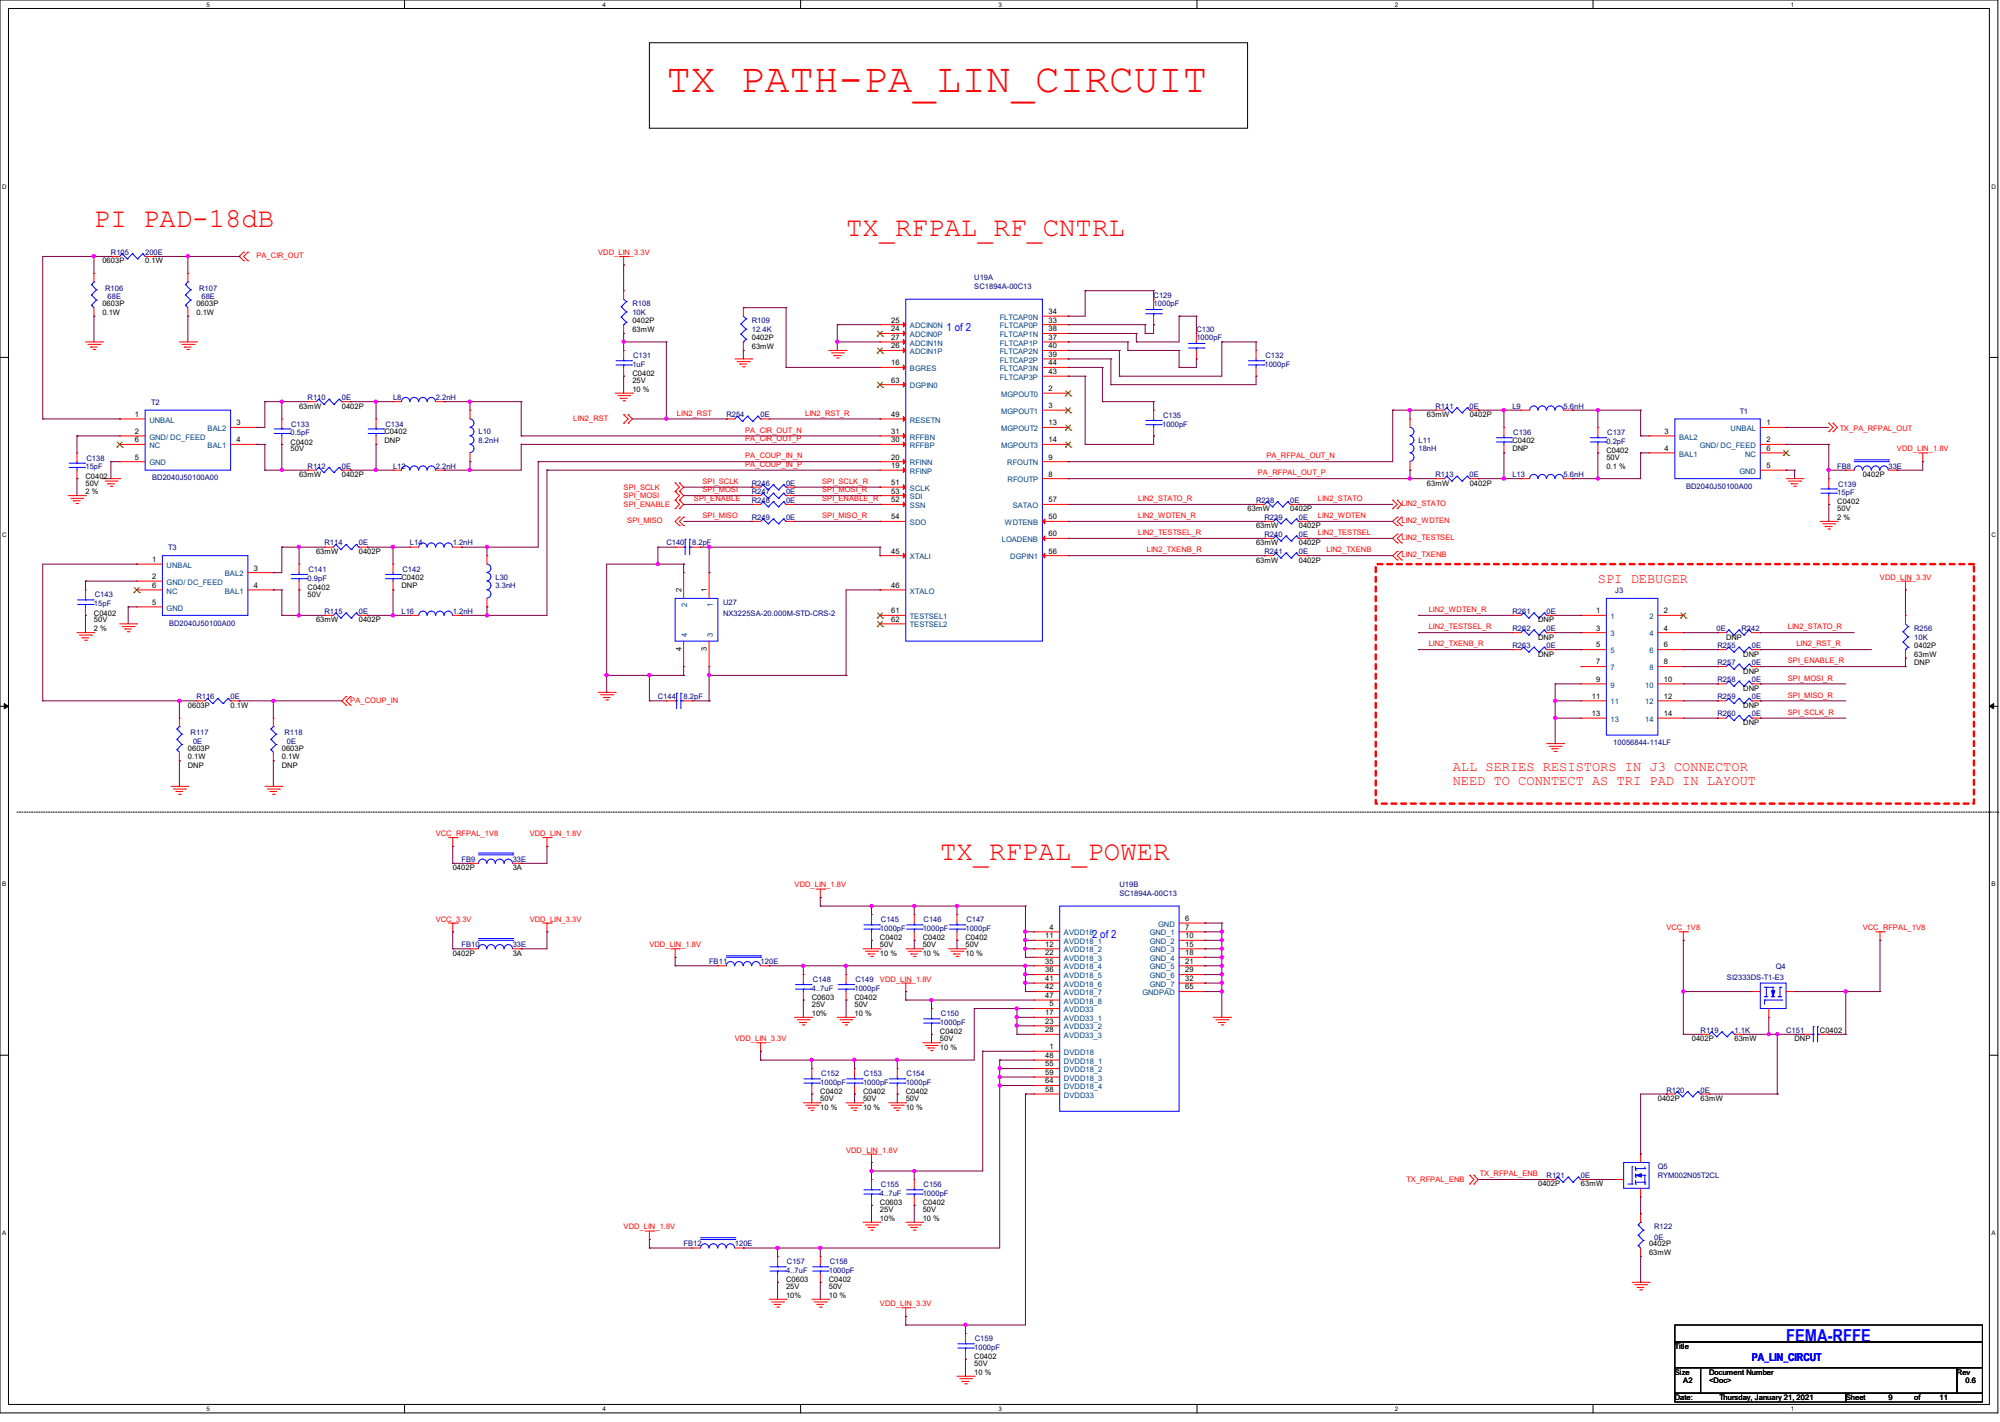
[picture p75: page 9]

ALL SERIES RESISTORS IN J3 CONNECTOR
NEED TO CONNTECT AS TRI PAD IN LAYOUT

# PA CONTROL SECTION

# PA_28V_POWER_SWITCH

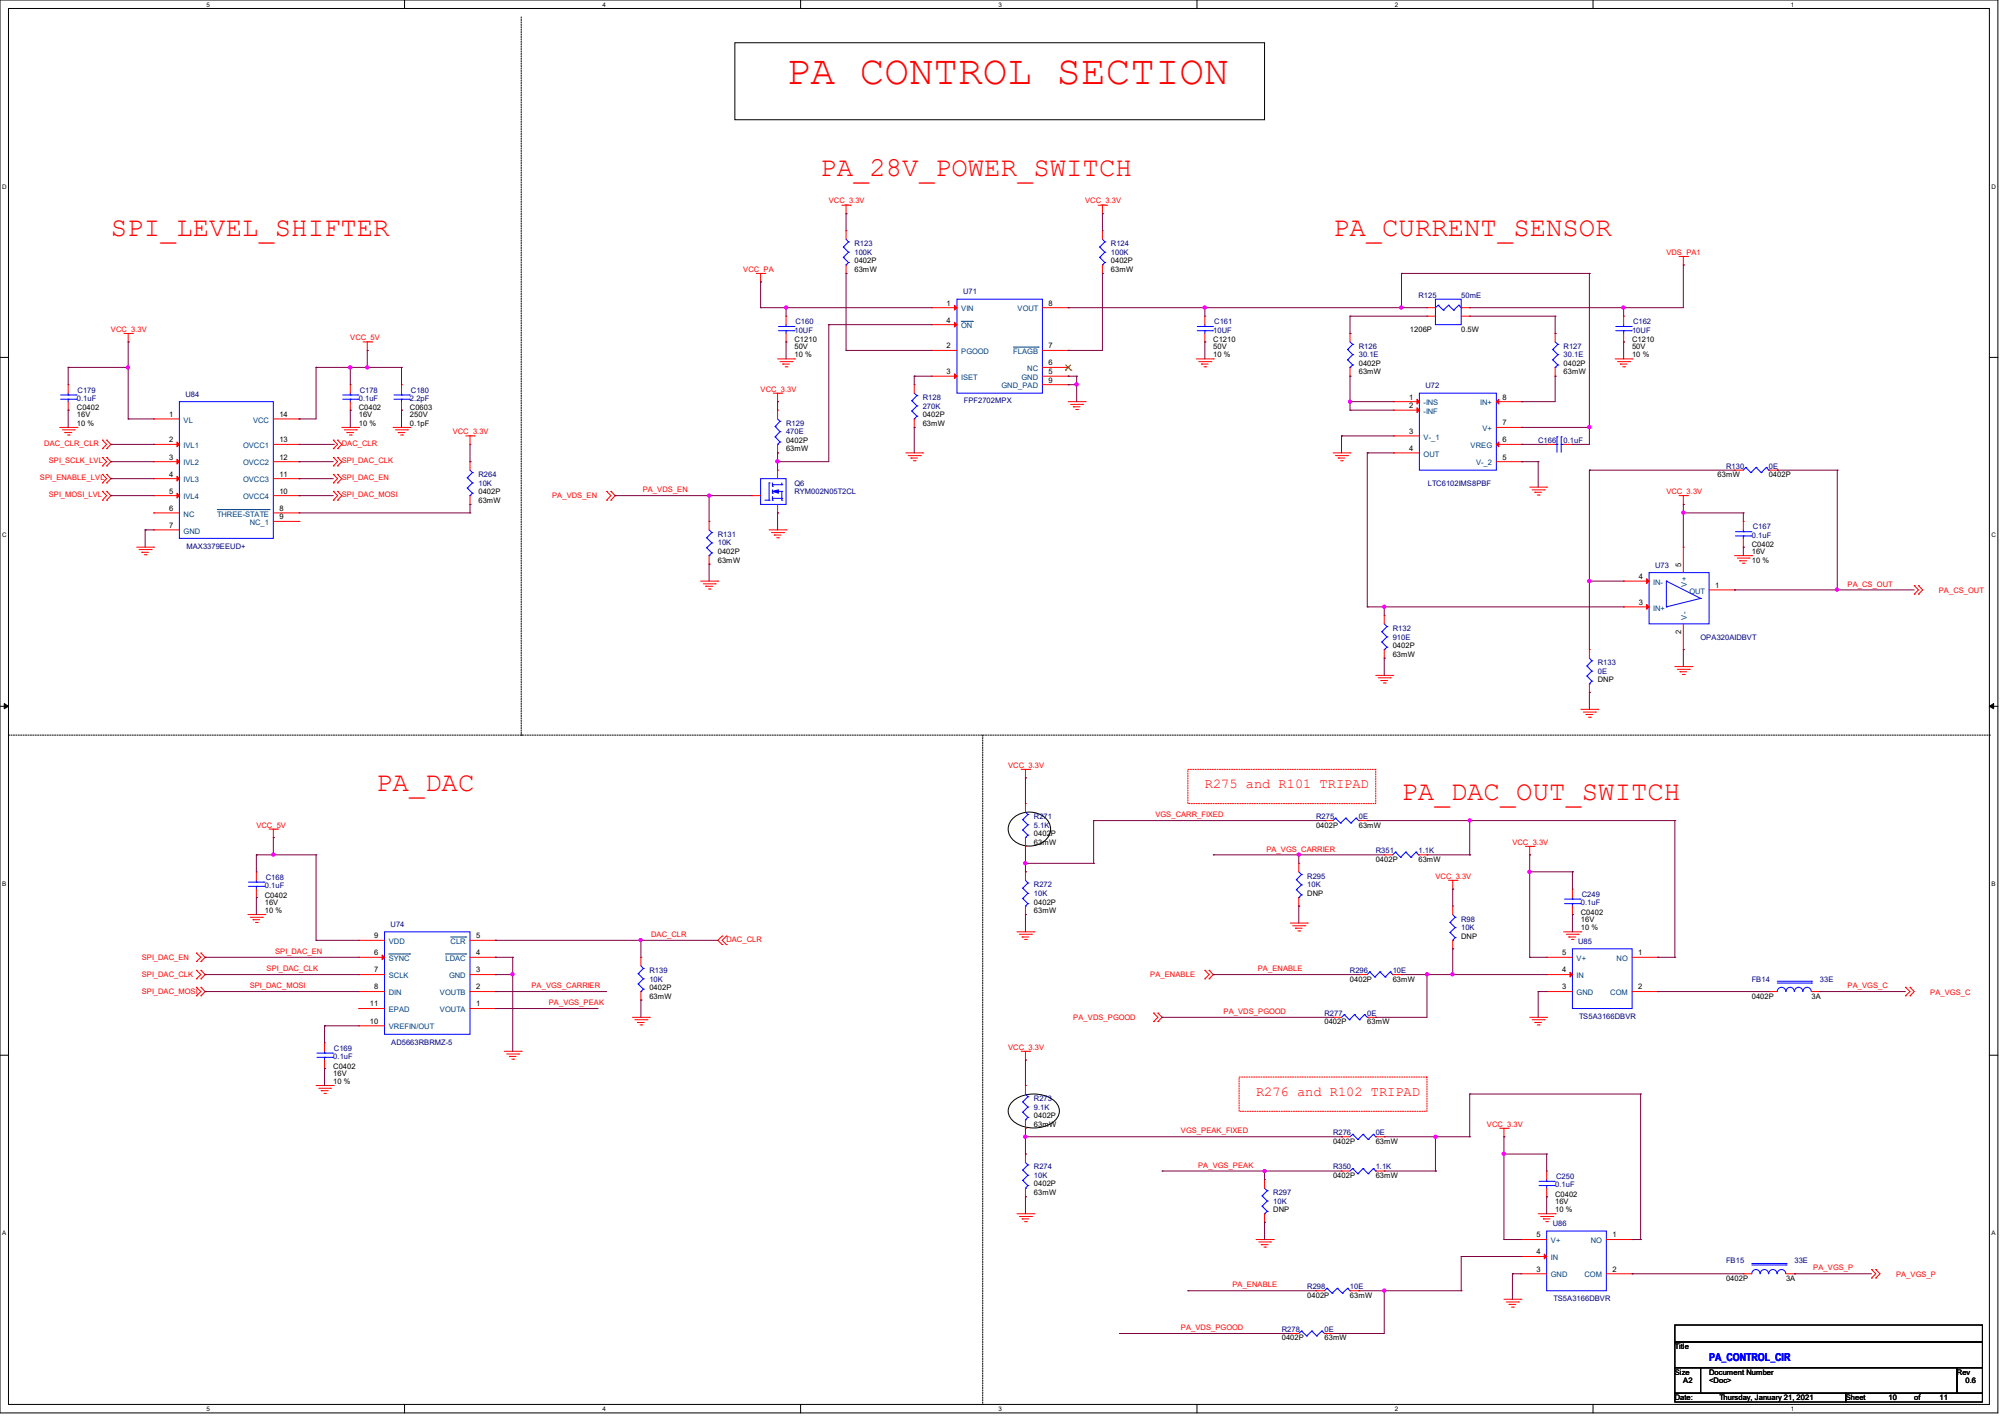
[picture p76: page 10]

# FEMA_BOARD_BOARD_CONNECTOR

TRI pad Options;

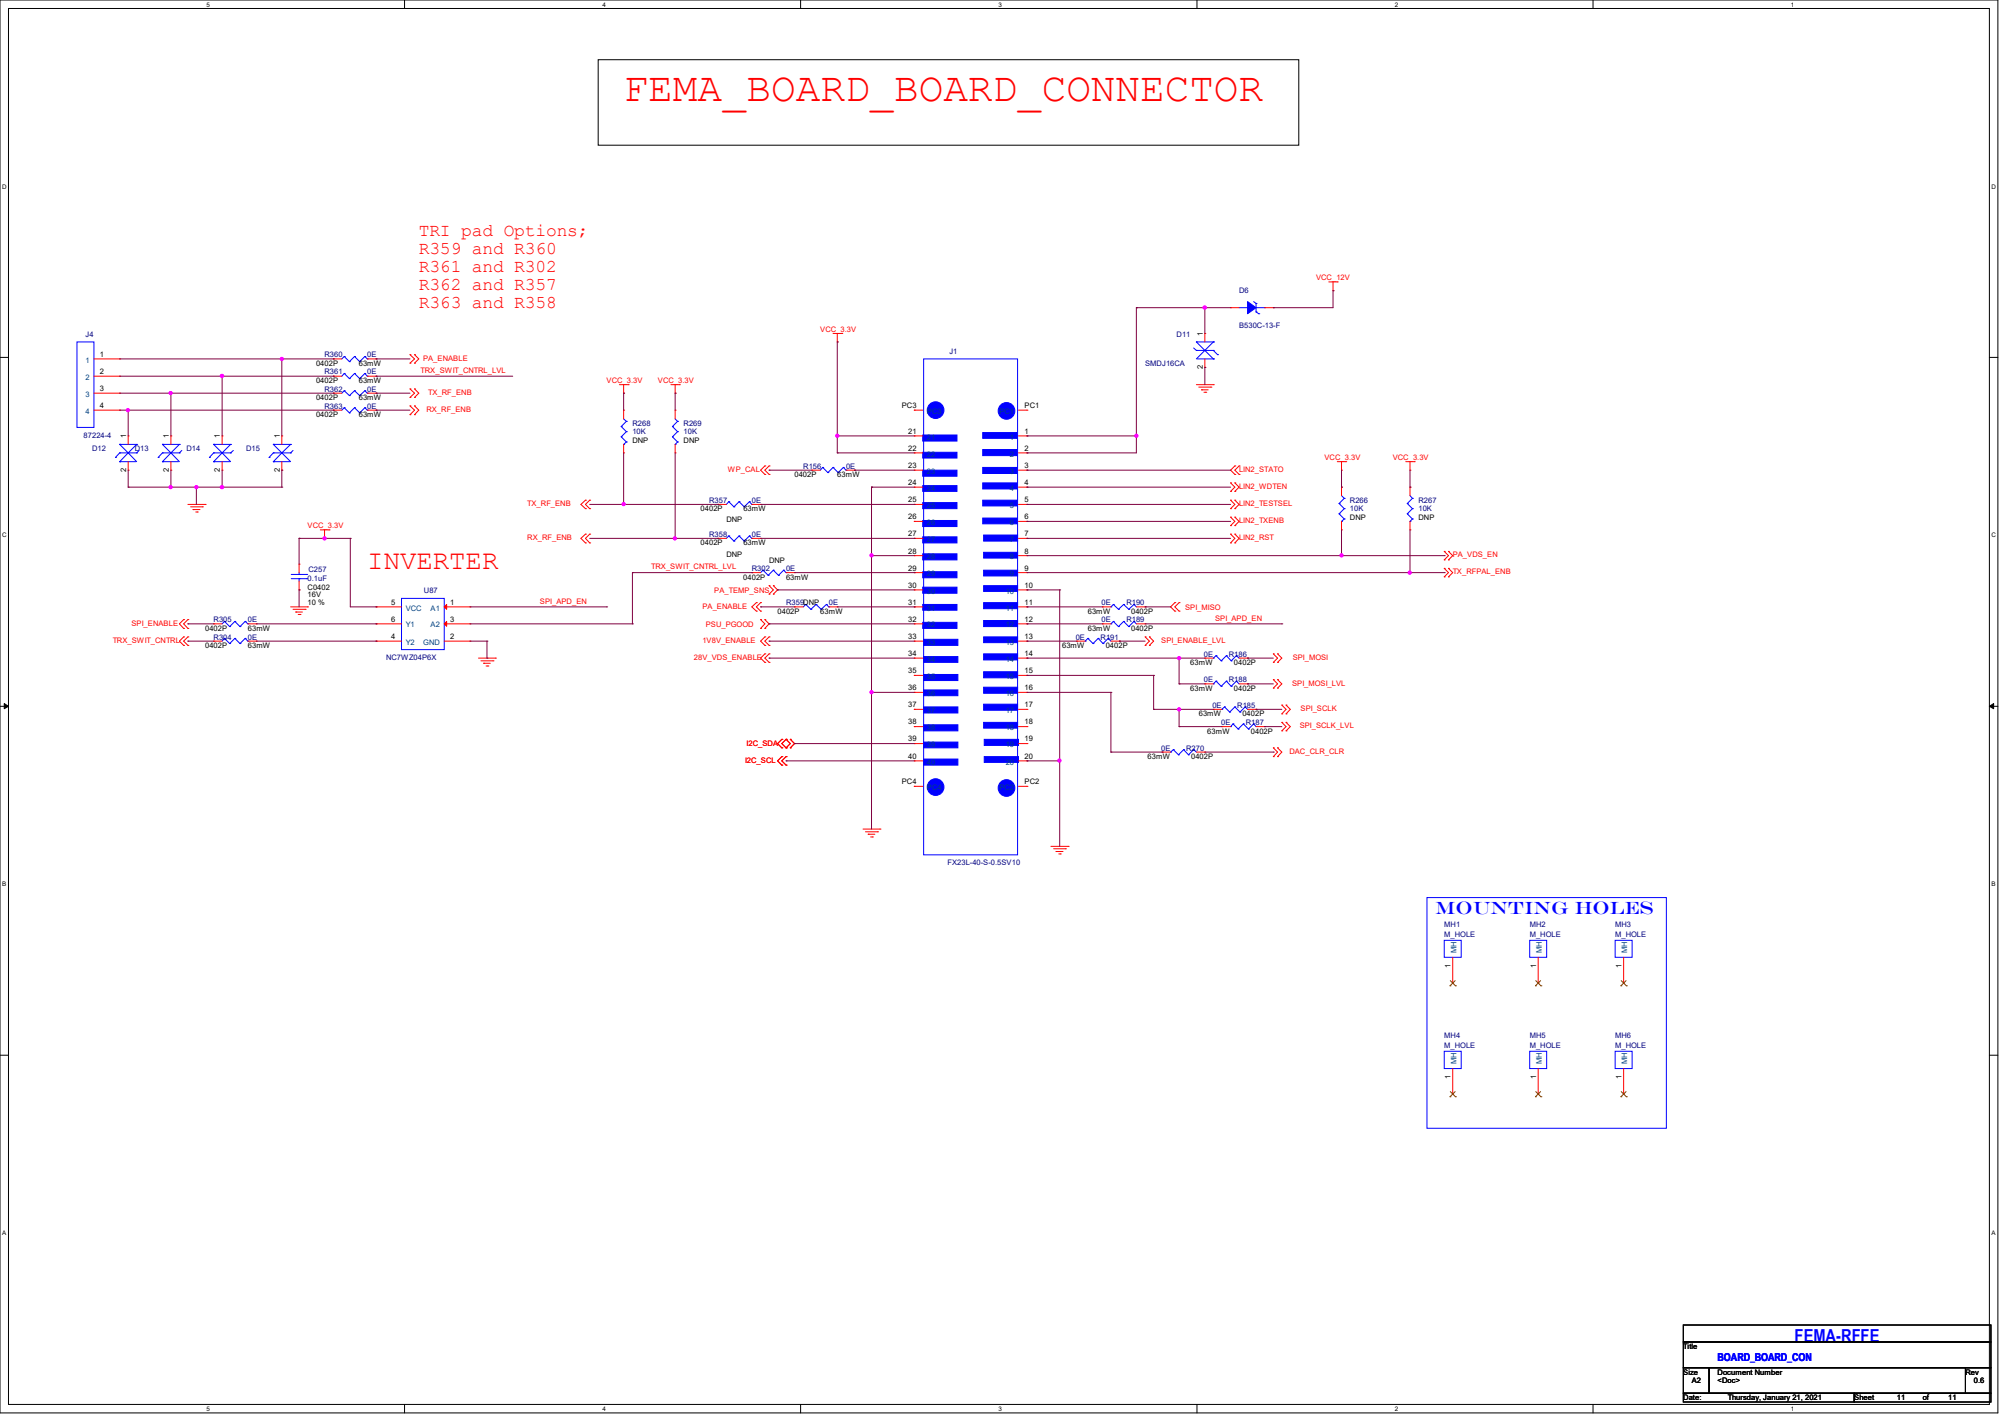
[picture p77: page 11]
