ukama/ukama-nodes/electronics/fe/30dBm/B48/schematics/FEMA_CBRS_1W_V0P6_02_JAN.pdf

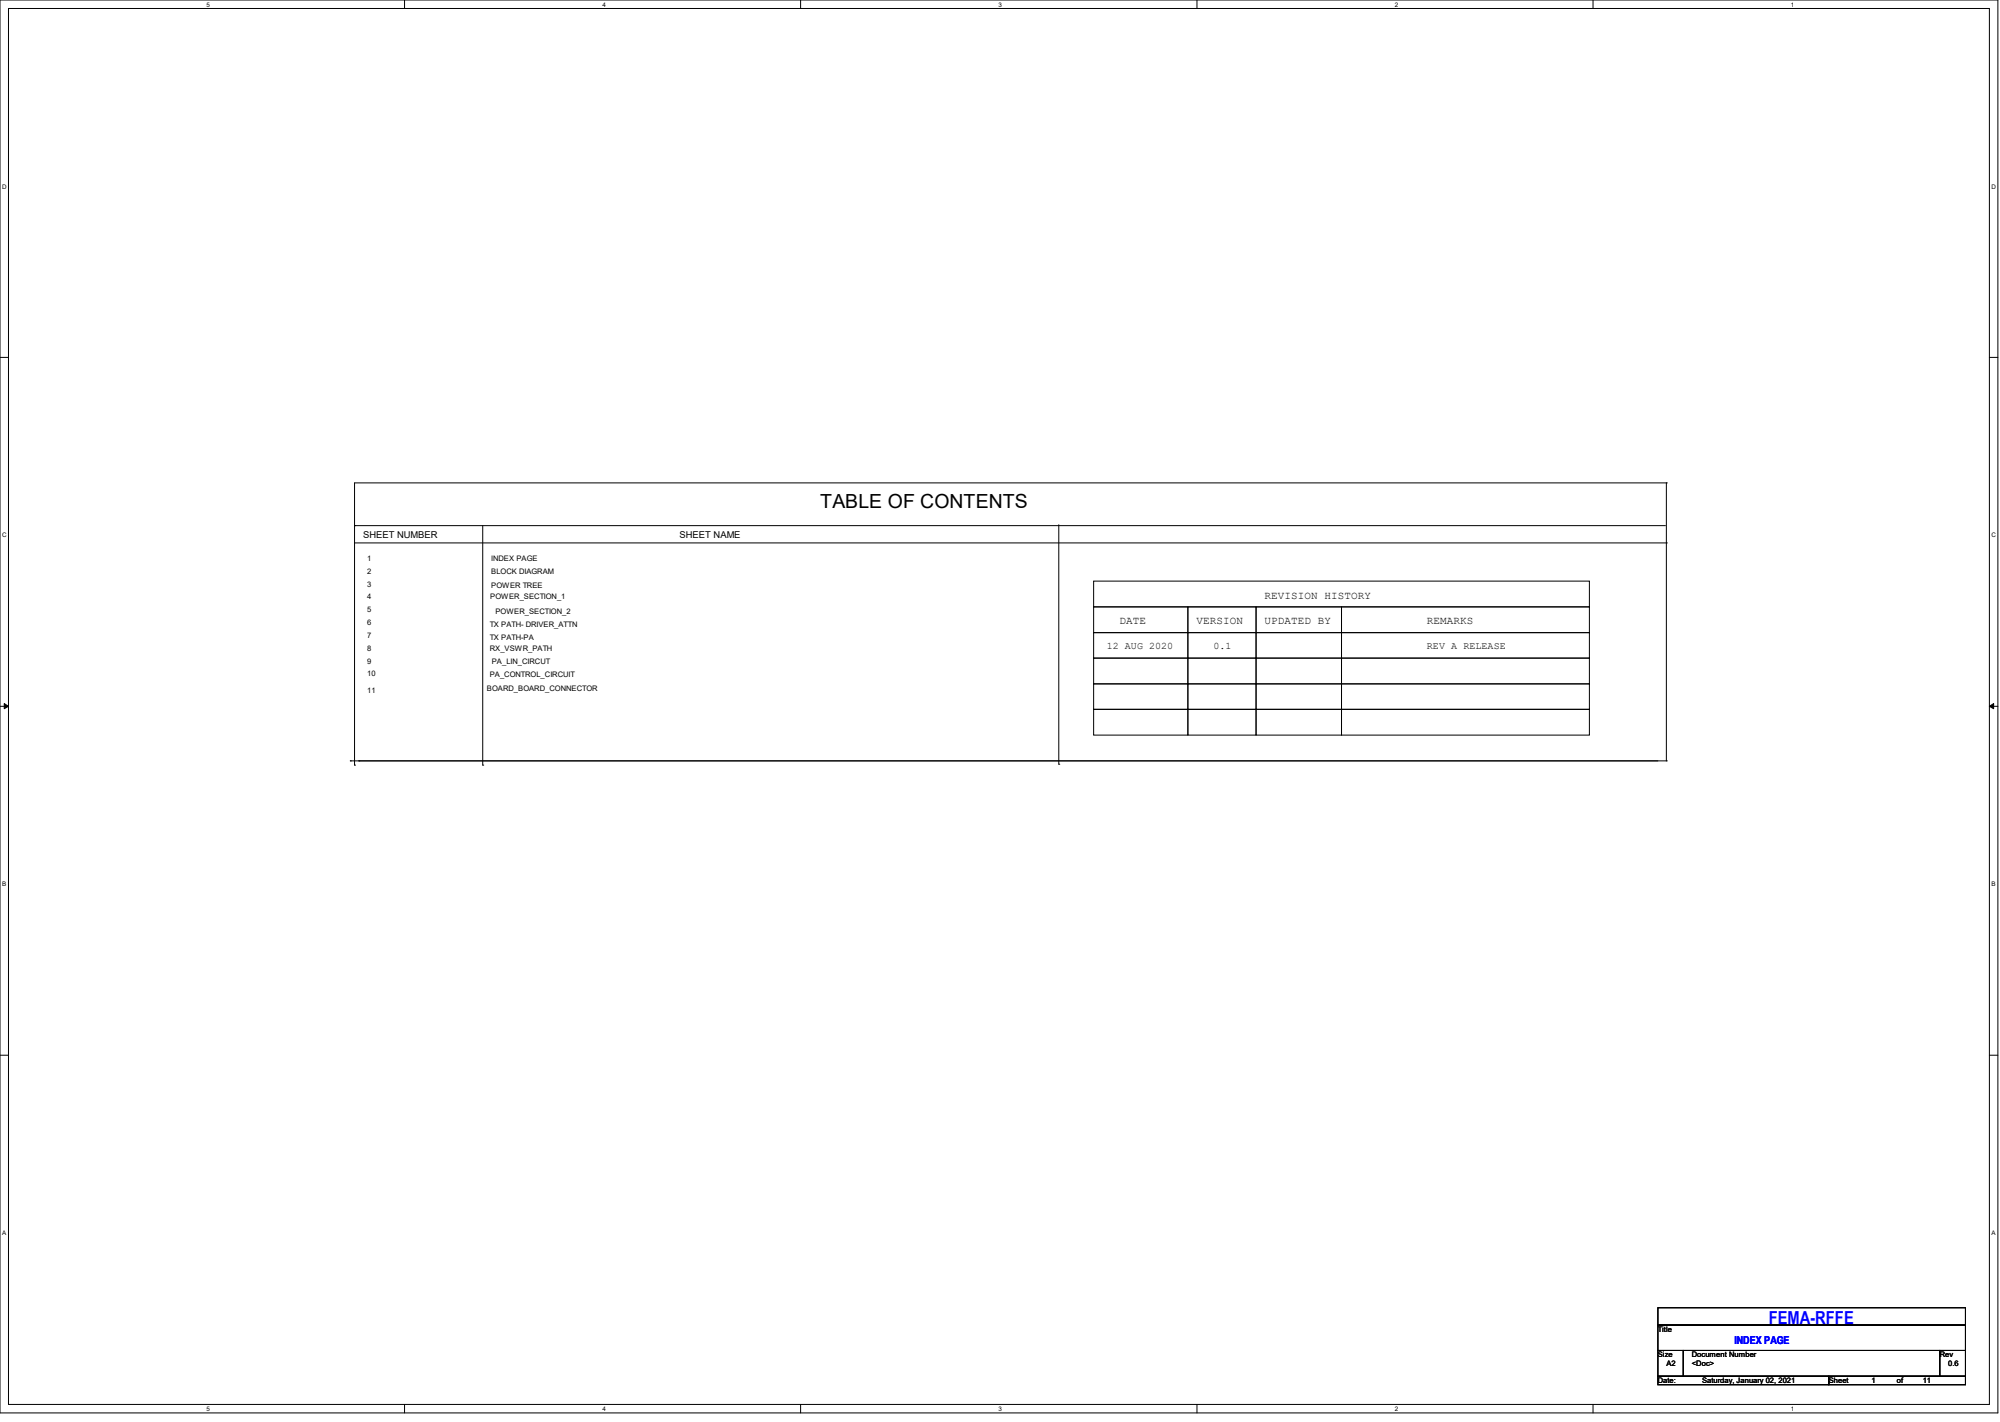
[picture p78: page 1]
12 AUG 2020; SHEET NUMBER; SHEET NAME; TX PATH- DRIVER_ATTN; REV A RELEASE; POWER TREE; PA_LIN_CIRCUT; BOARD_BOARD_CONNECTOR; RX_VSWR_PATH; INDEX PAGE BLOCK DIAGRAM; PA_CONTROL_CIRCUIT; TX PATH-PA; REVISION HISTORY; DATE; VERSION; UPDATED BY; REMARKS; POWER_SECTION_1; FEMA-RFFE; POWER_SECTION_2; Title Size; Document Number; Rev Date:; Sheet; of <Doc>; INDEX PAGE A2; Saturday, January 02, 2021; 11 Title Size

TABLE OF CONTENTS

# BLOCK_DIAGRAMNEED TO UPDATE

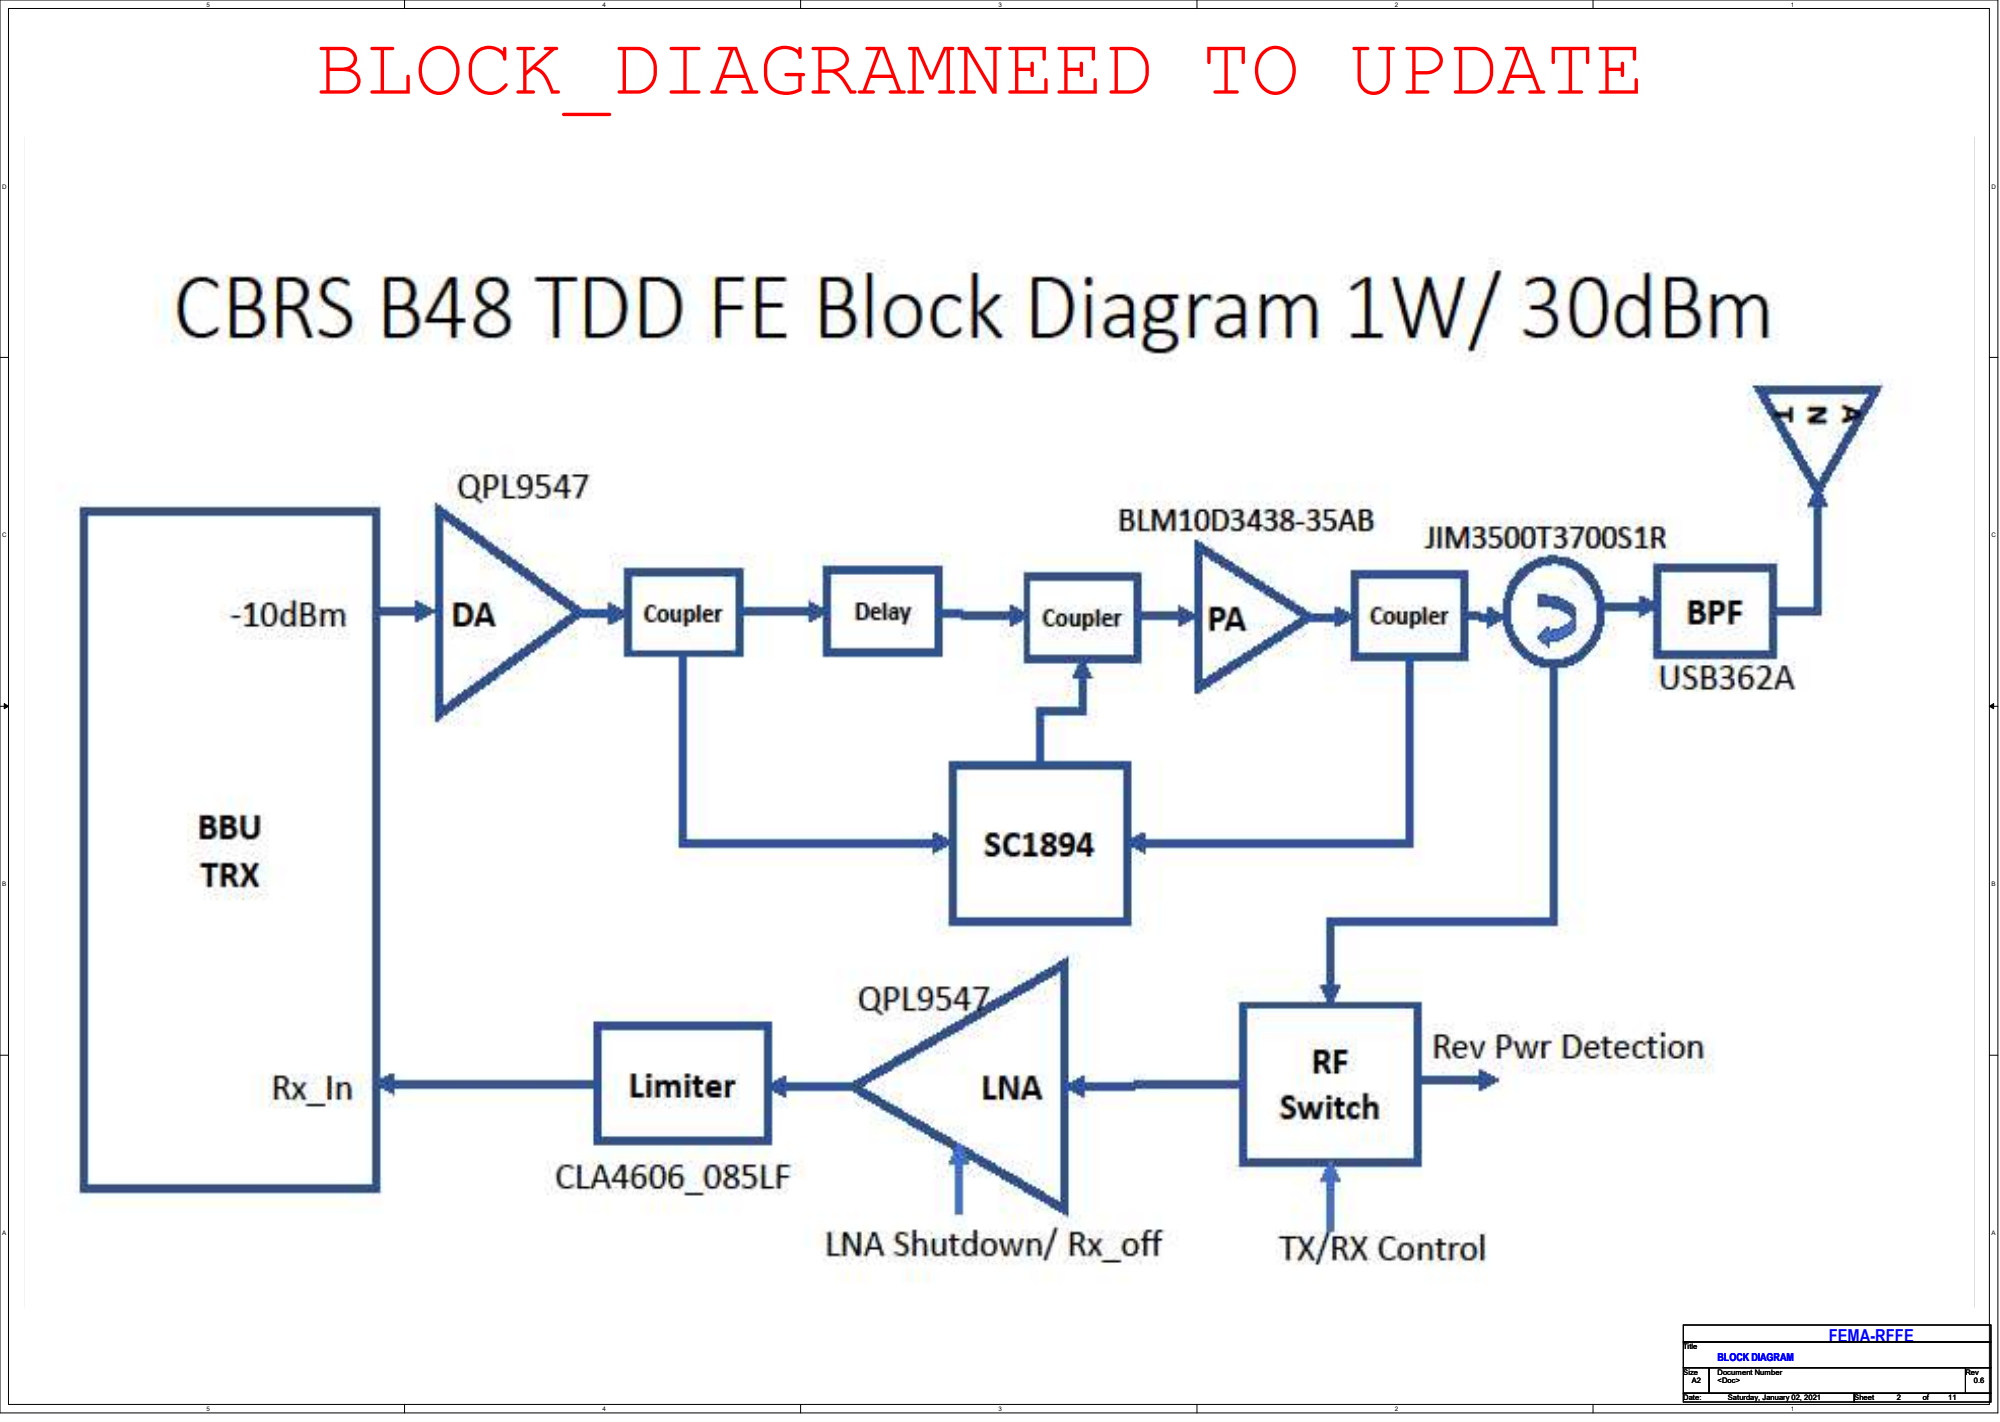
[picture p79: page 2]
FEMA-RFFE; Title Size; Document Number; Rev Date:; Sheet; of <Doc>; BLOCK DIAGRAM A2; Saturday, January 02, 2021; 11 Title Size

Power Connector | Common Mode Filter

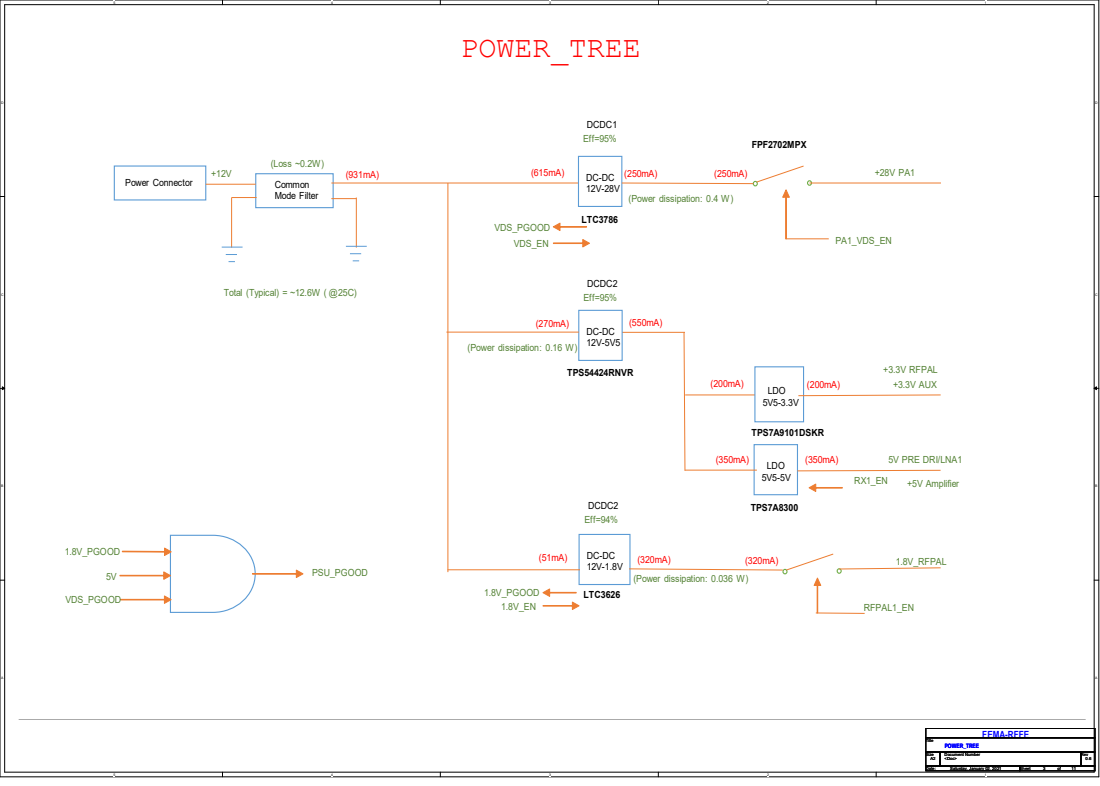
[picture p80: page 3]
Total (Typical) = ~12.6W ( @25C); (Loss ~0.2W); DCDC1 Eff=95%; FPF2702MPX; LTC3786; PA1_VDS_EN; VDS_PGOOD VDS_EN; DCDC2 Eff=95%; TPS54424RNVR; +5V Amplifier; LDO 5V5-3.3V; TPS7A9101DSKR; LDO 5V5-5V; TPS7A8300; +3.3V RFPAL +3.3V AUX; 5V PRE DRI/LNA1; DCDC2 Eff=94%; LTC3626; 1.8V_PGOOD 1.8V_EN; 1.8V_RFPAL; RFPAL1_EN; 1.8V_PGOOD; VDS_PGOOD; PSU_PGOOD; (Power dissipation: 0.4 W); (Power dissipation: 0.16 W); (Power dissipation: 0.036 W); FEMA-RFFE; POWER_TREE; Title Size; Document Number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

# 12V_5p5V_DCDC 5V5_3V3_LDO

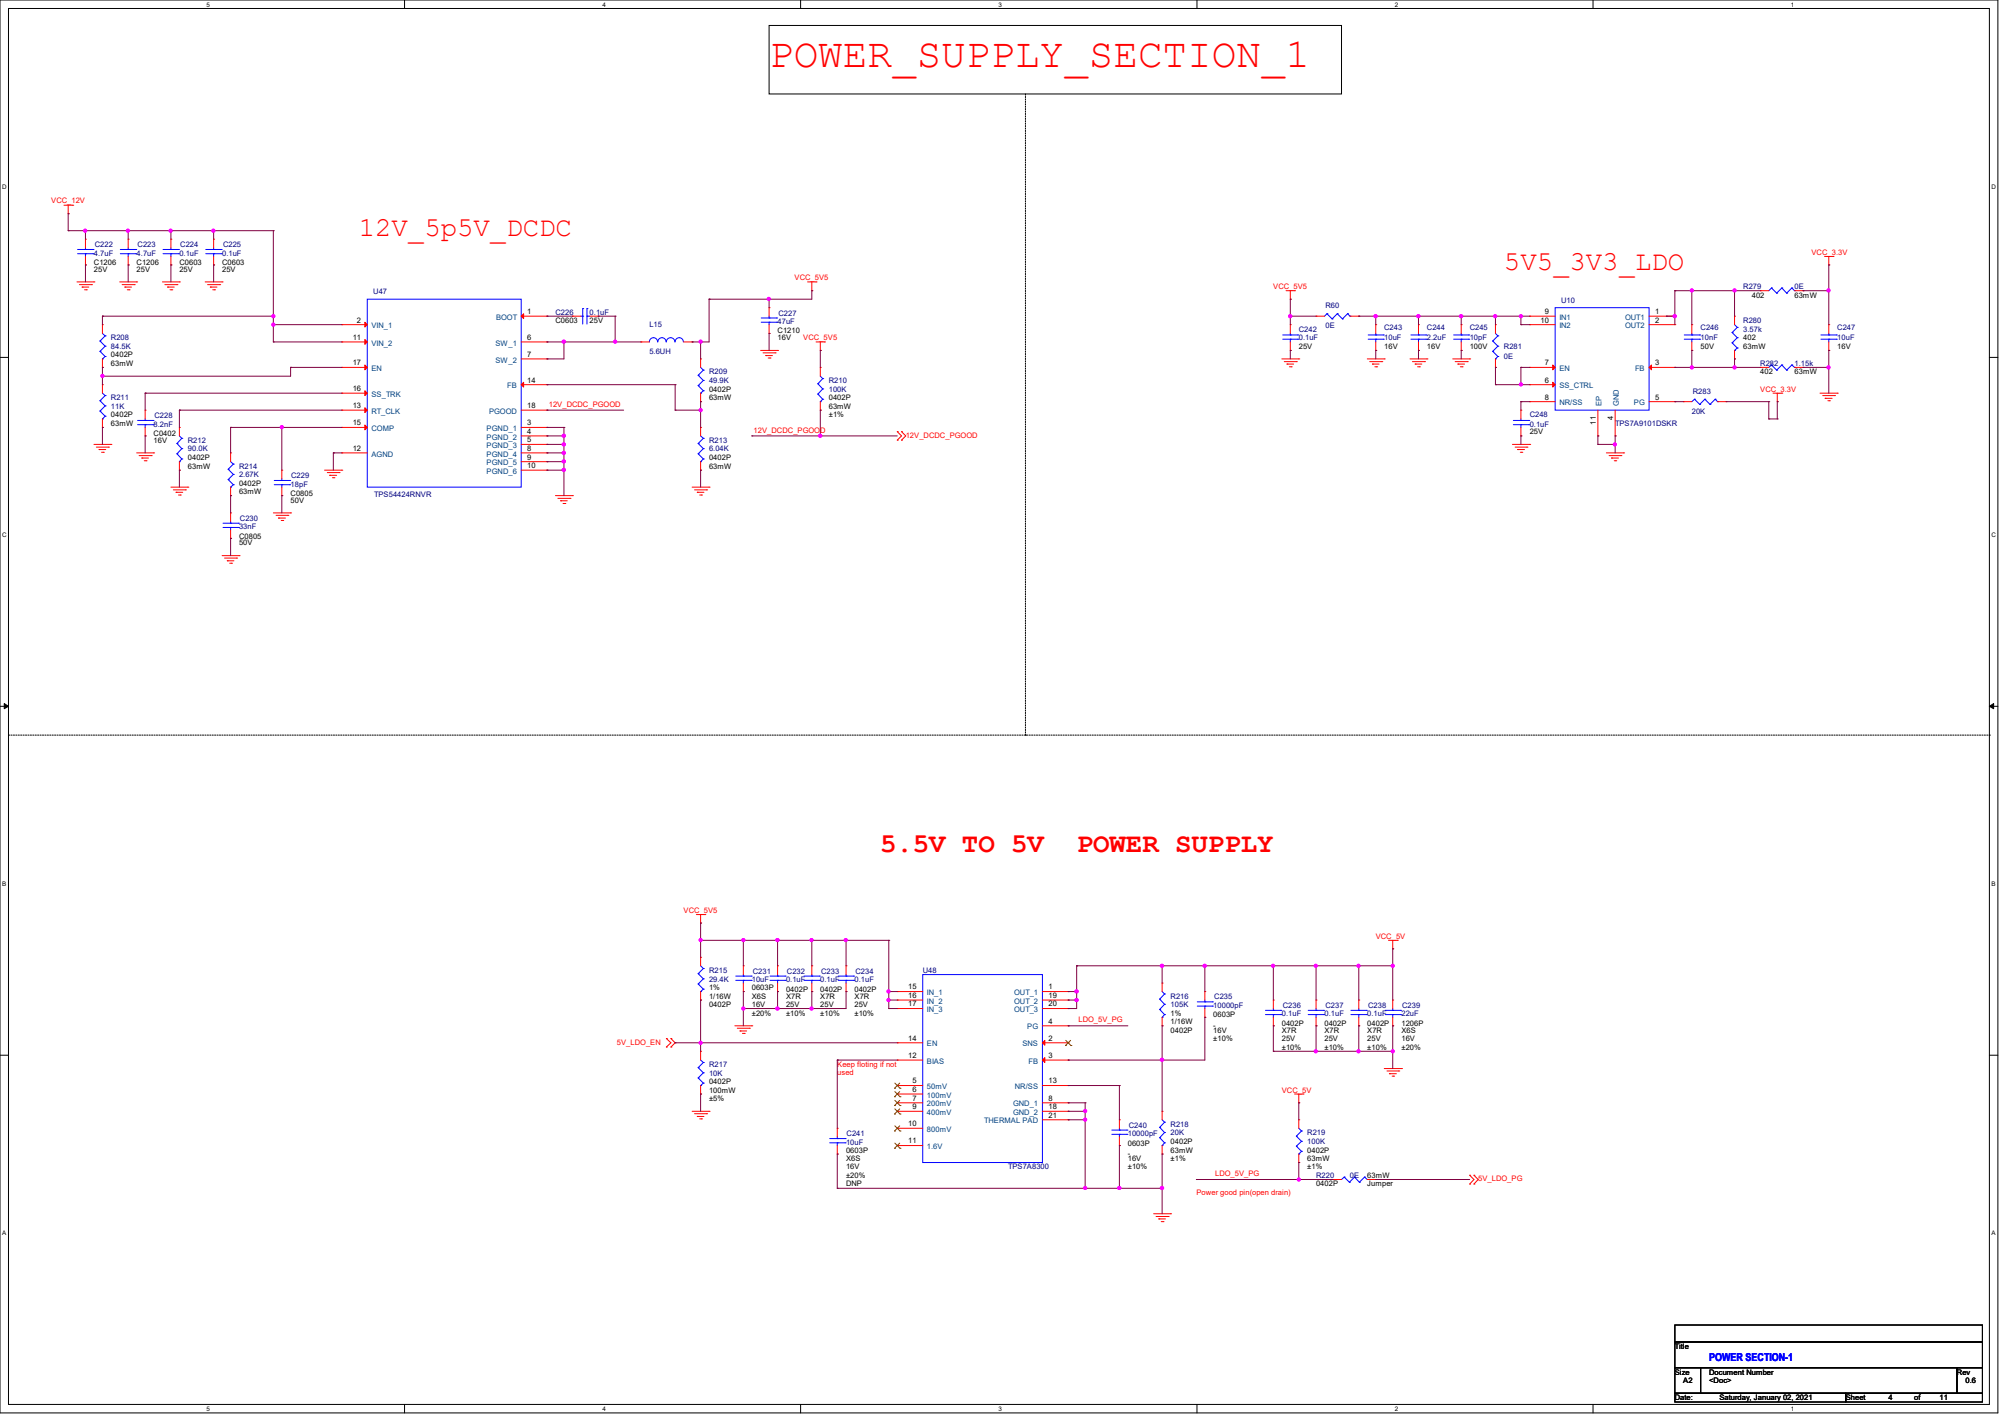
[picture p81: page 4]

Keep floting if not
used

Power good pin(open drain)

# 12V_1V8_DCDC

# POWER_SUPPLY_SECTION_2

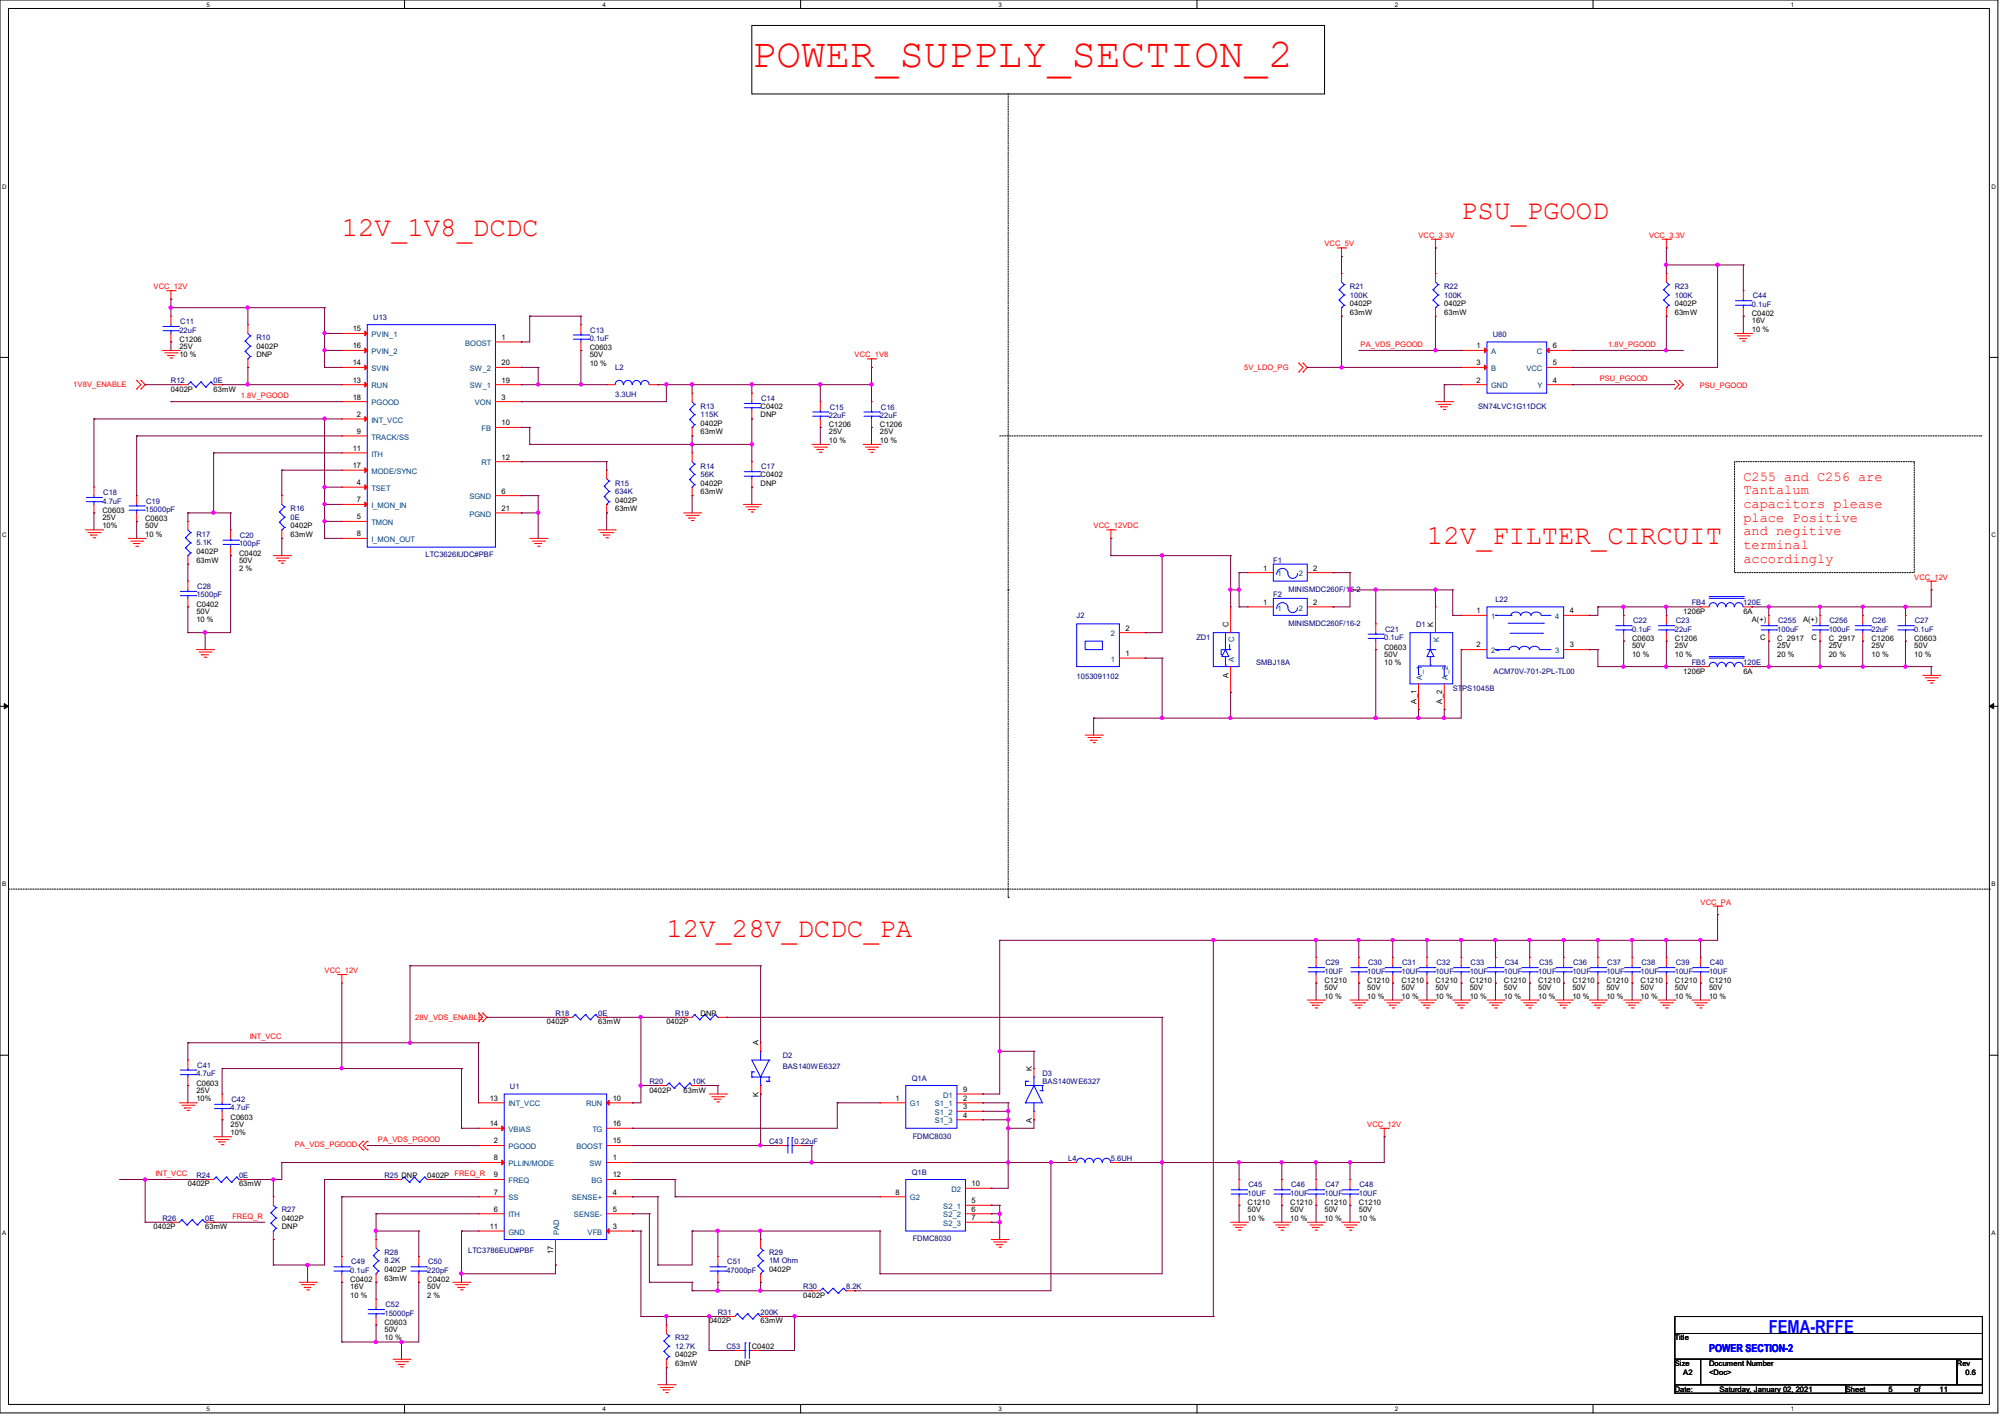
[picture p82: page 5]

# TX_INPUT

# TX PATH- DRIVER_ATTN

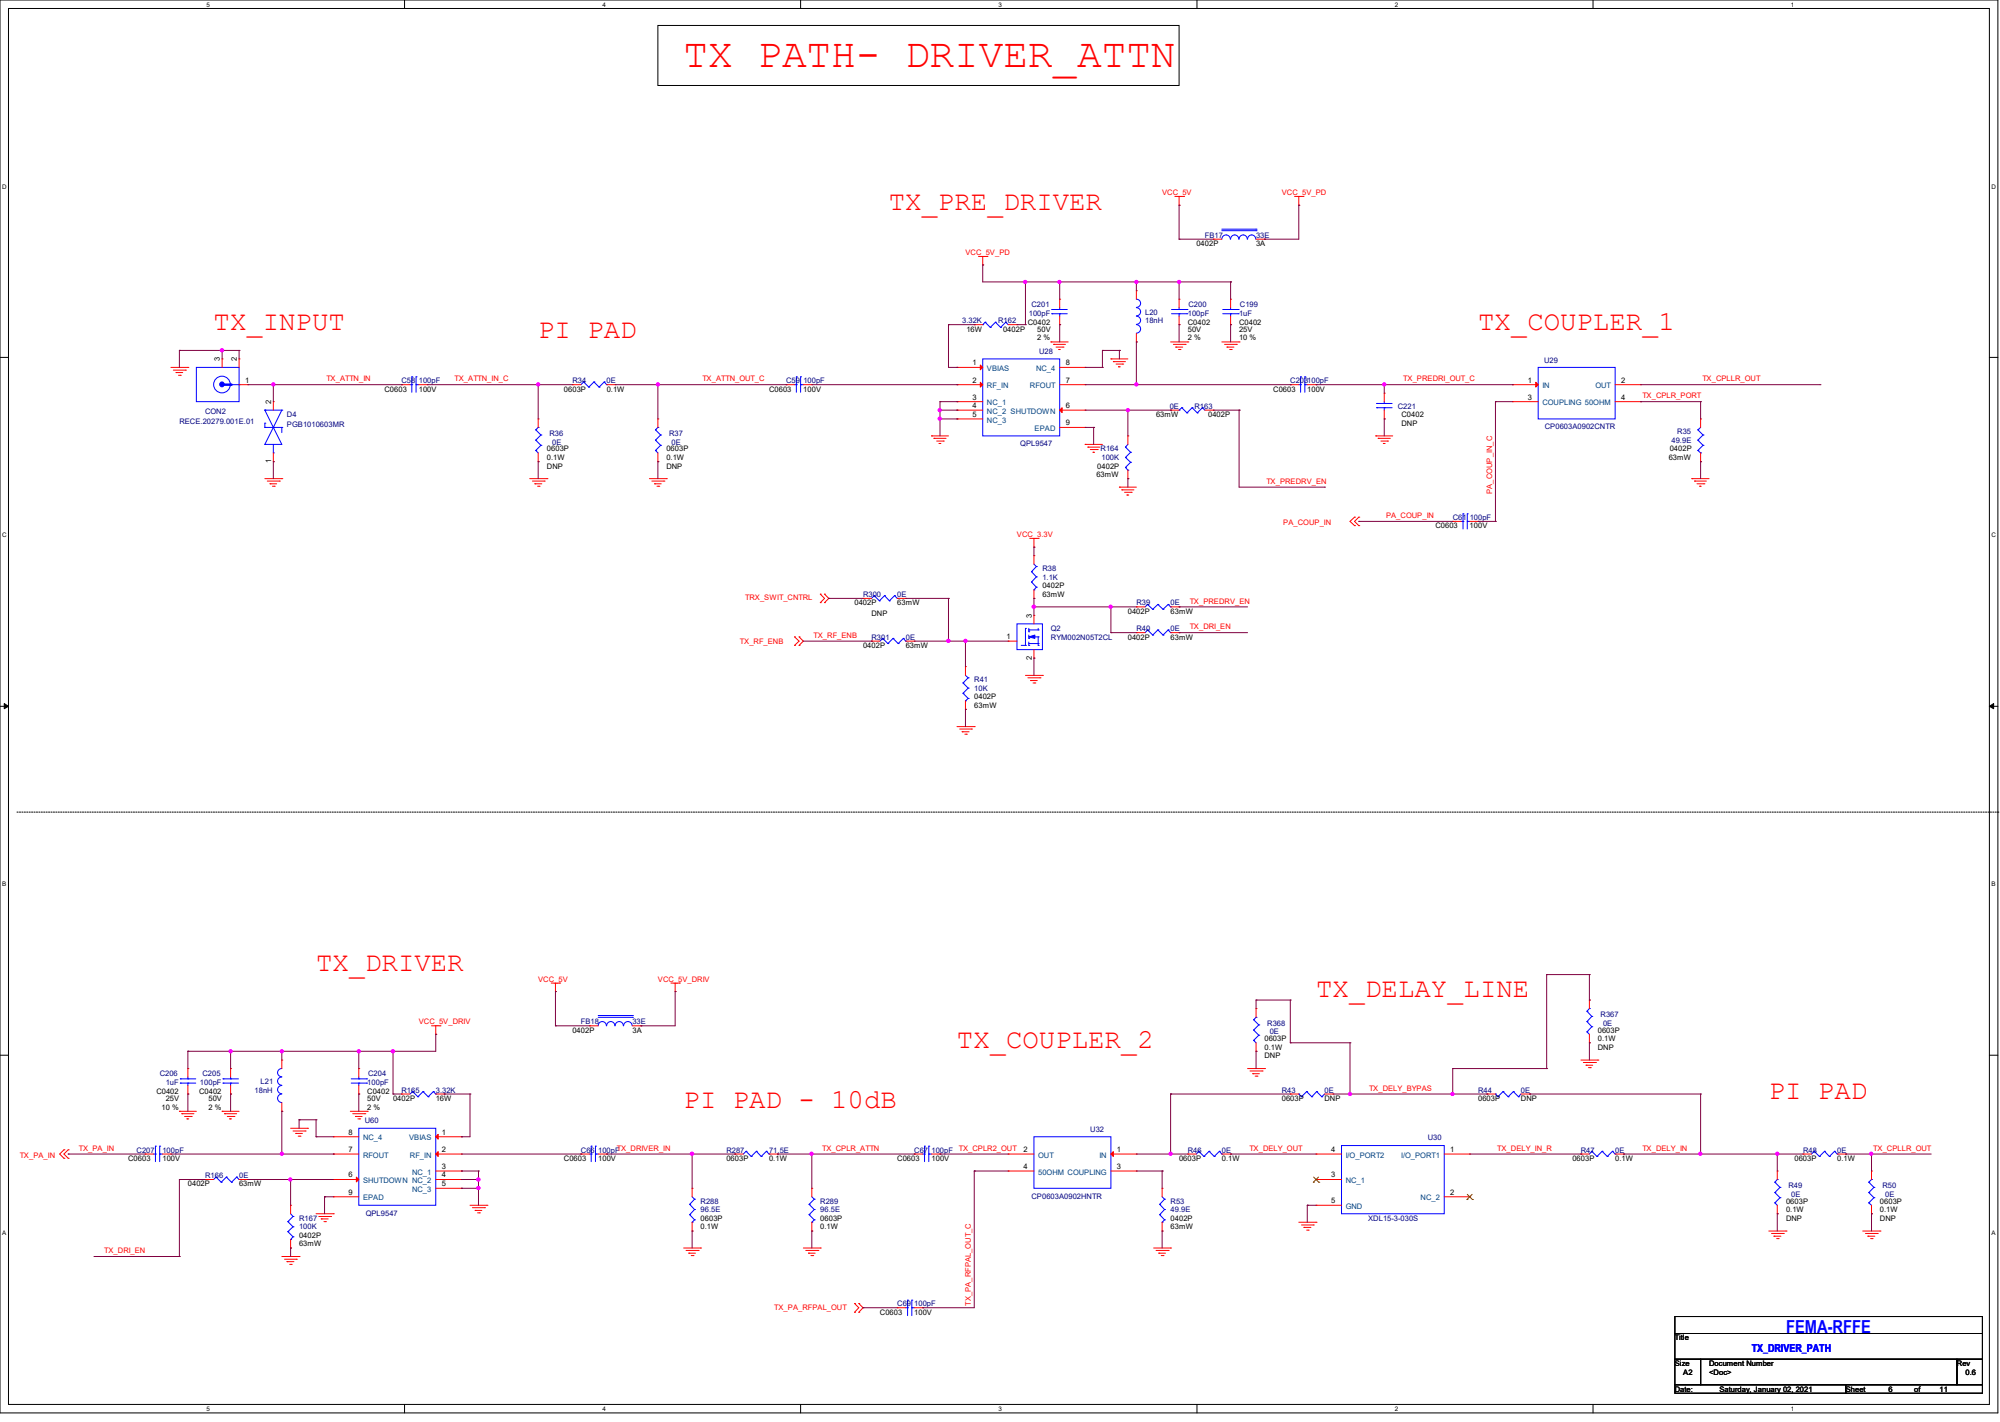
[picture p83: page 6]

# TX _PA

# TX PATH- PA SECTION

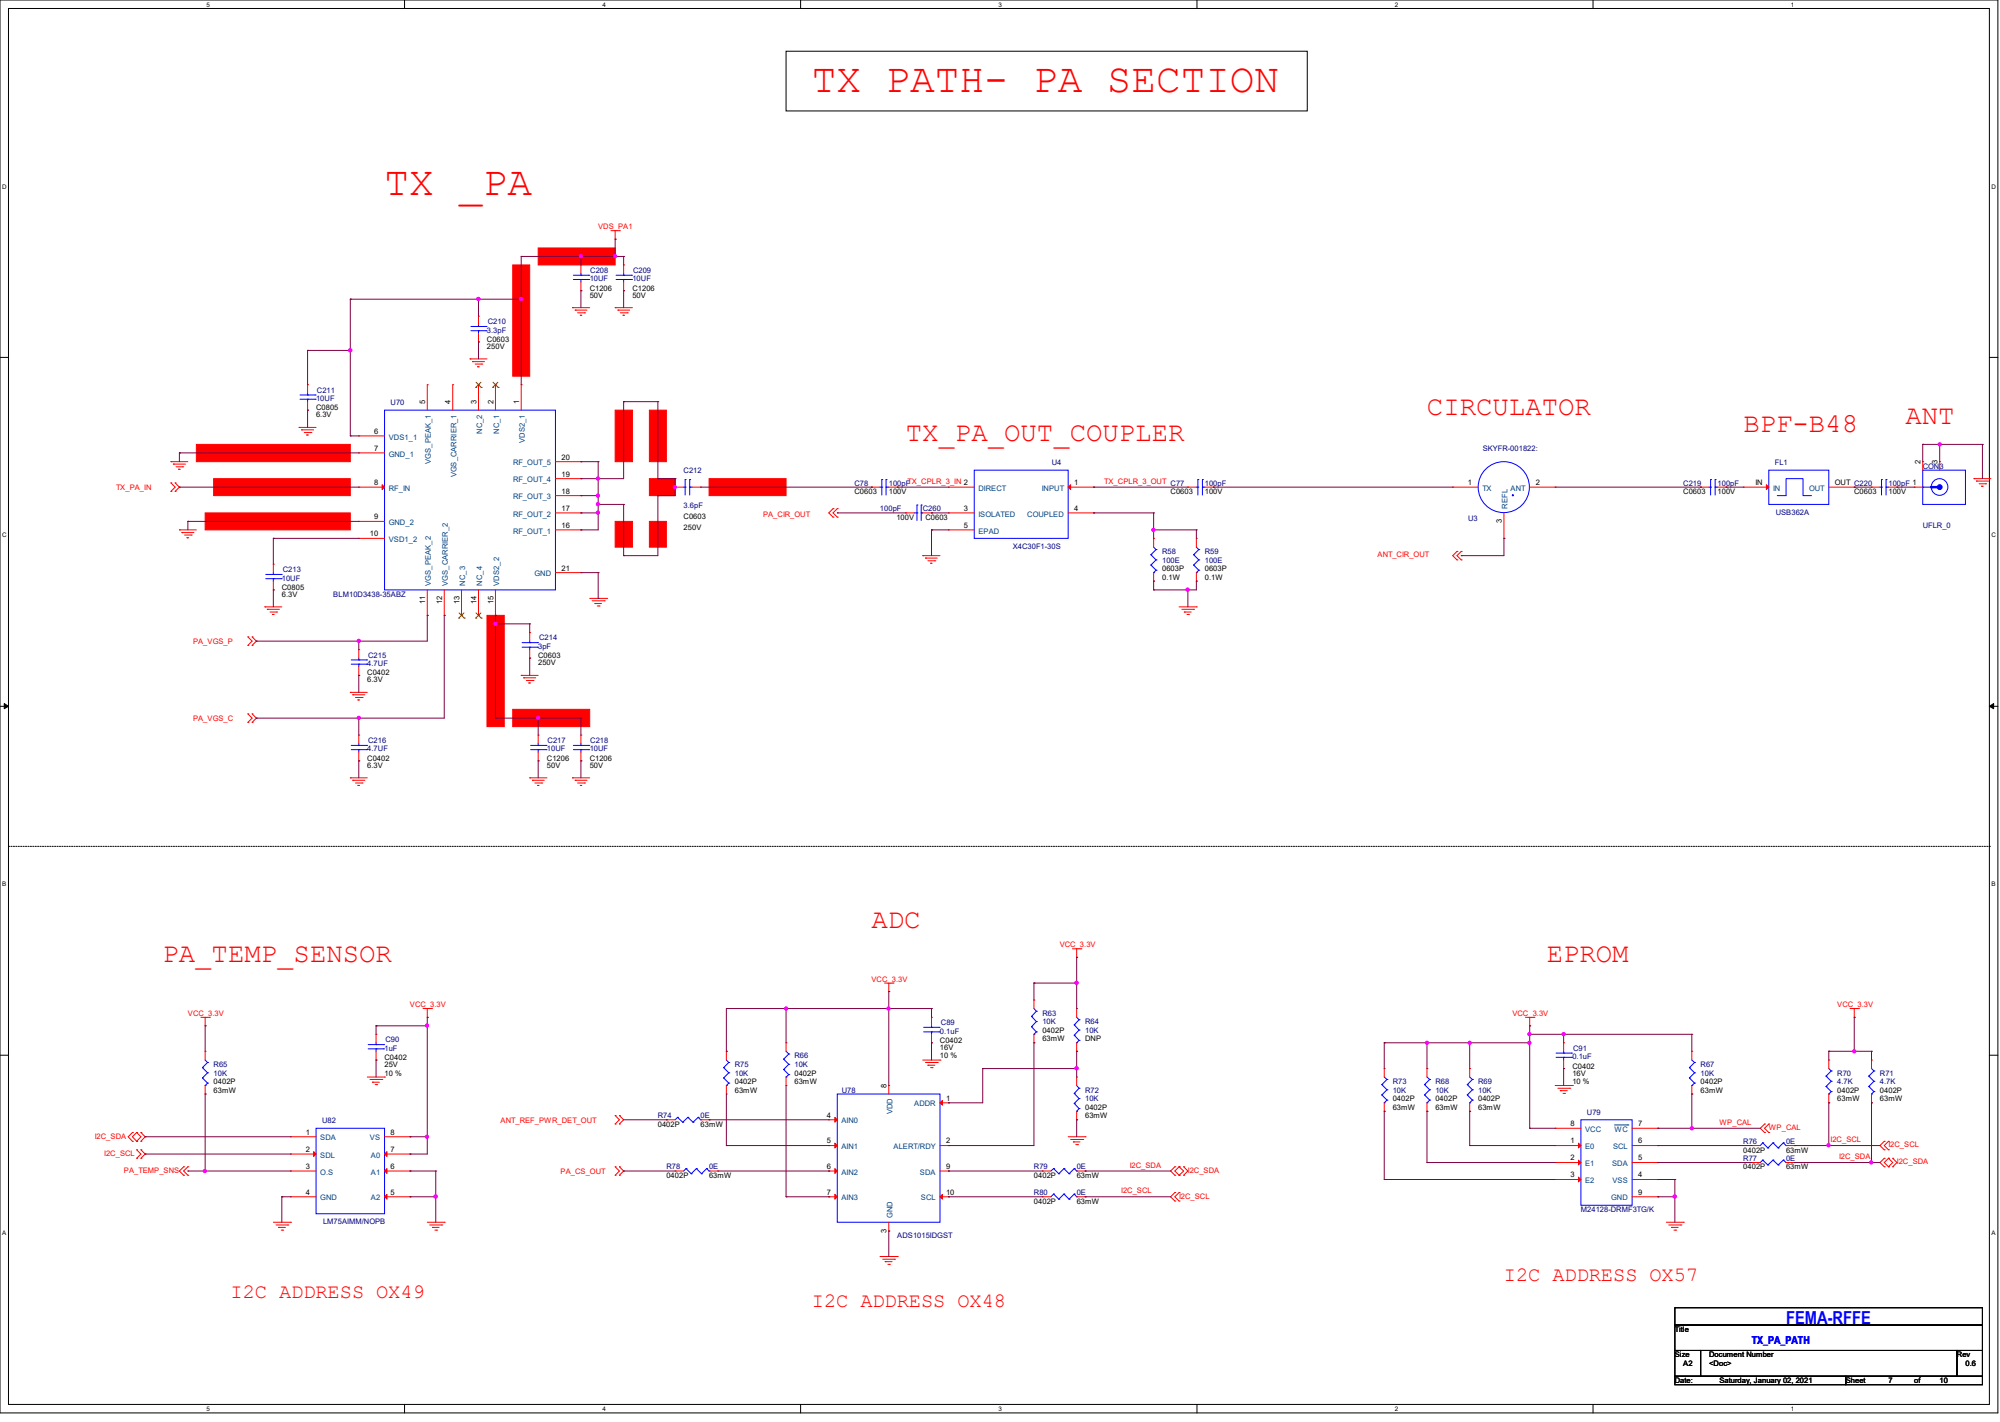
[picture p84: page 7]

# TRX_SWITCH

# PI_PAD

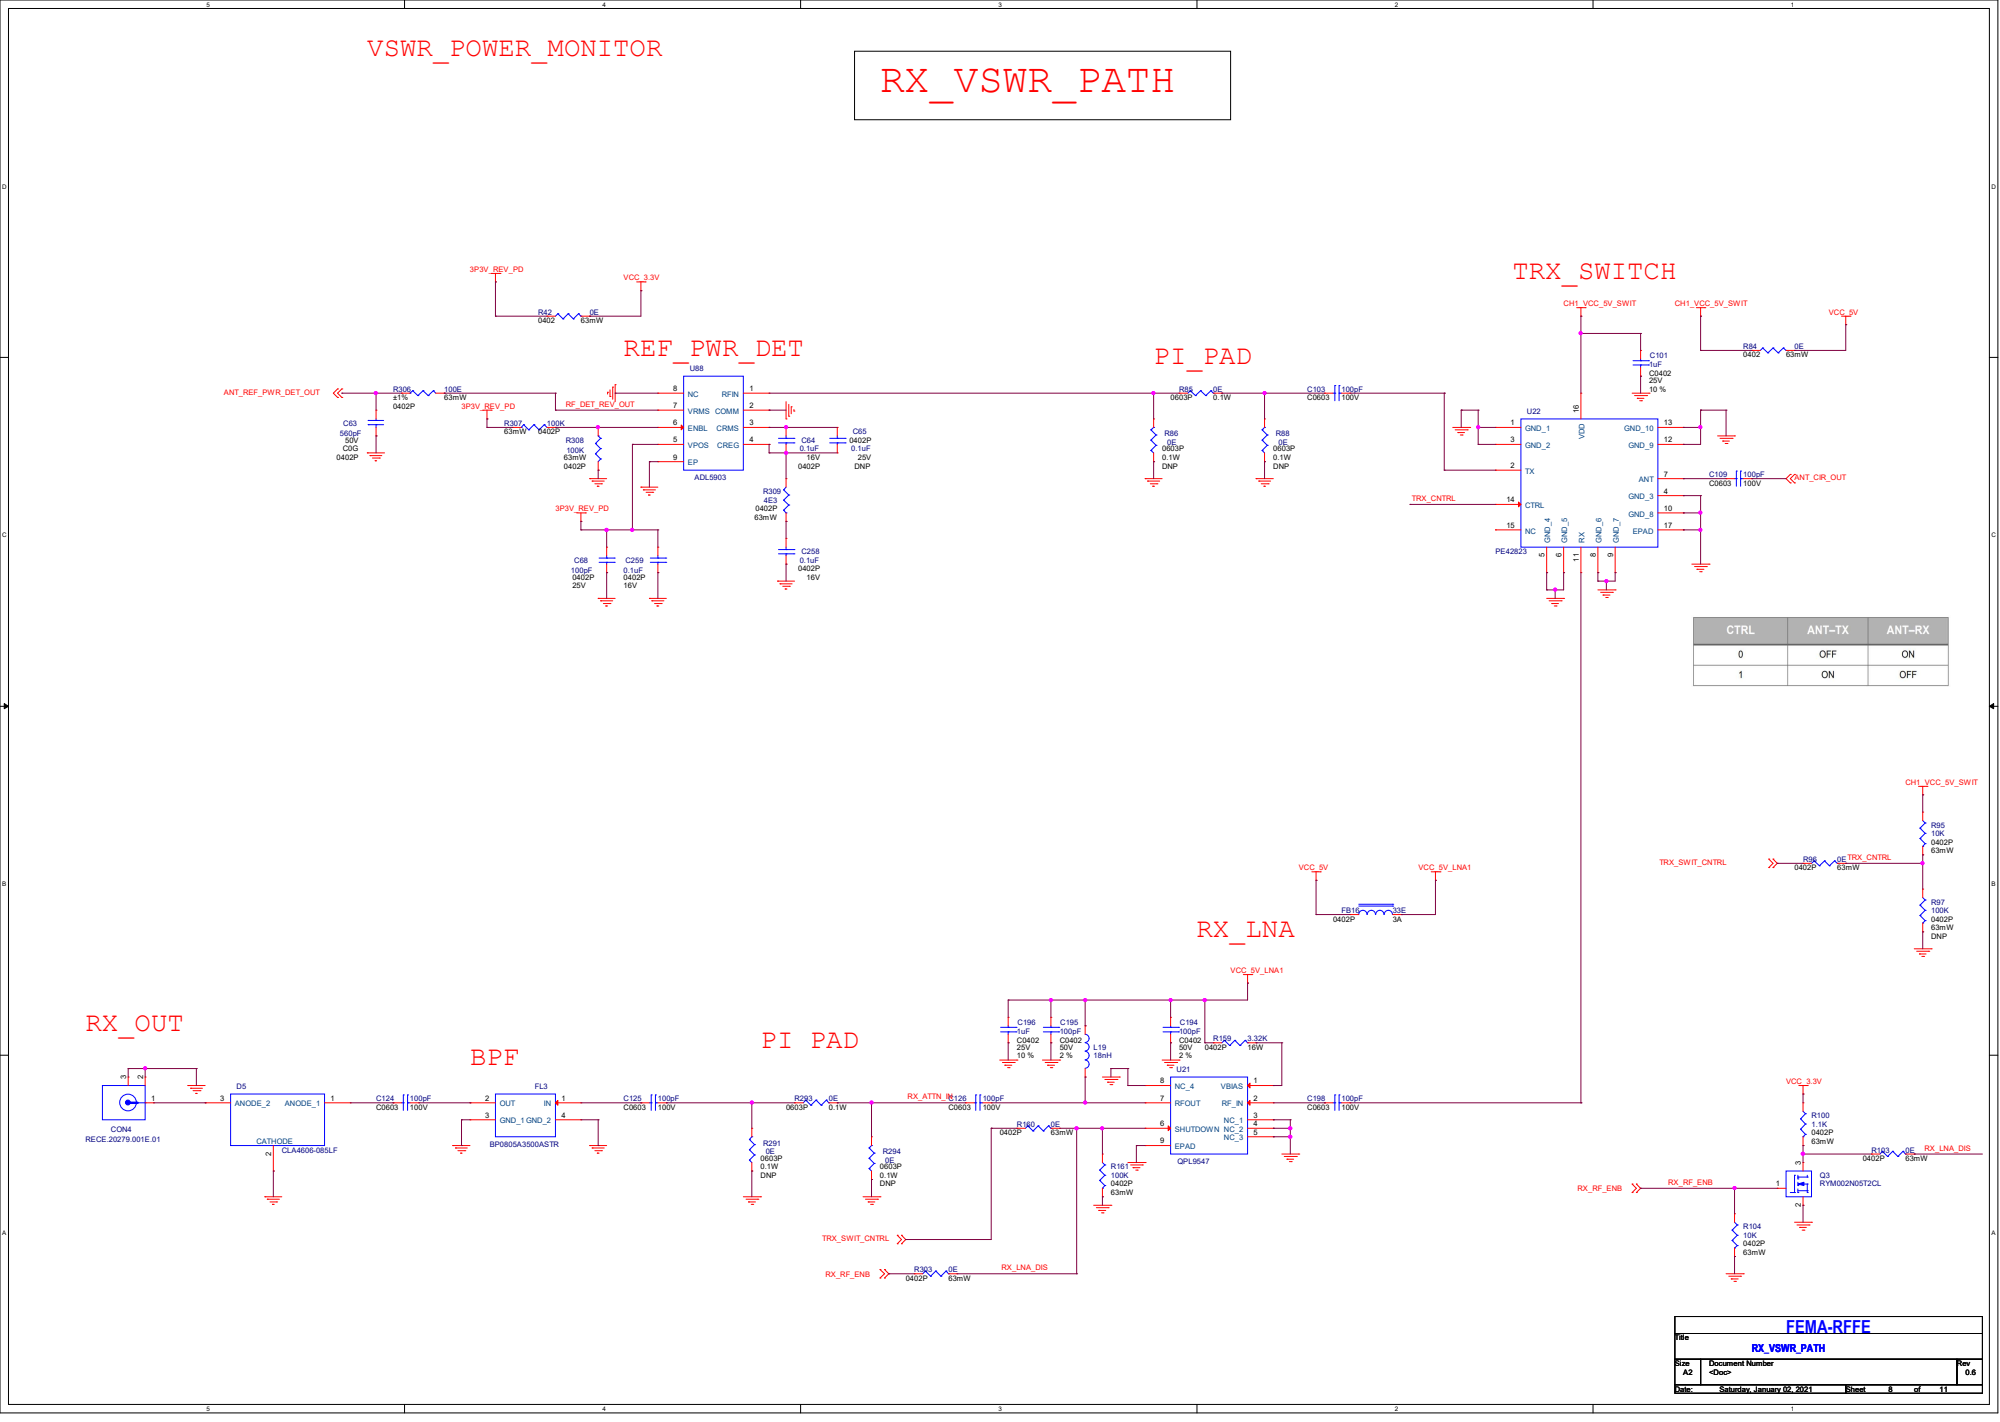
[picture p85: page 8]

# TX PATH-PA_LIN_CIRCUIT

# TX_RFPAL_RF_CNTRL

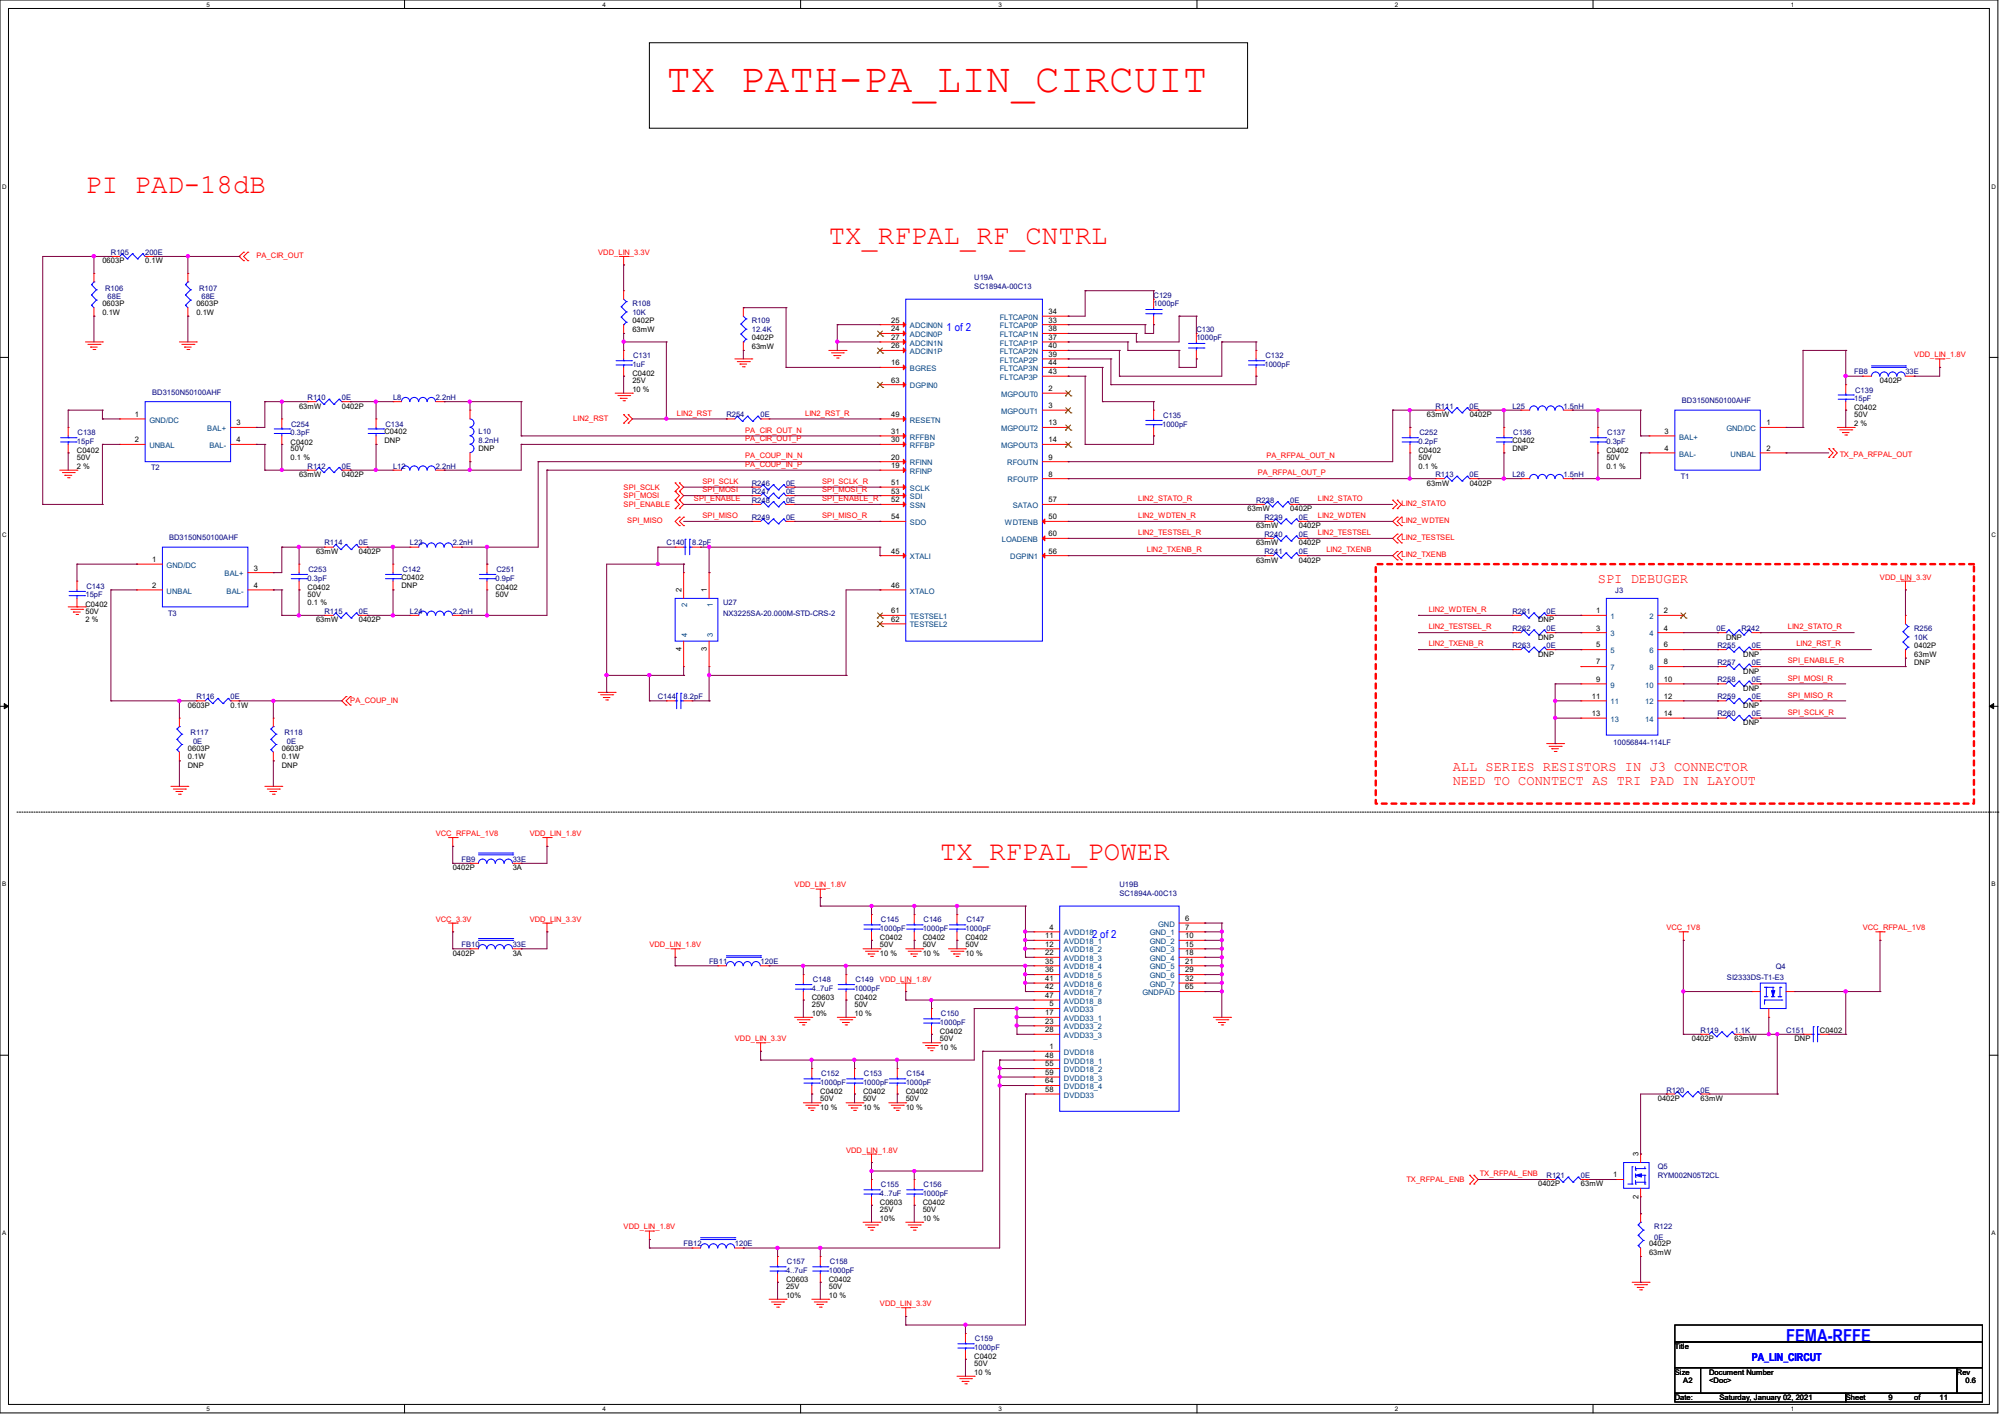
[picture p86: page 9]

ALL SERIES RESISTORS IN J3 CONNECTOR
NEED TO CONNTECT AS TRI PAD IN LAYOUT

# PA CONTROL SECTION

# PA_28V_POWER_SWITCH

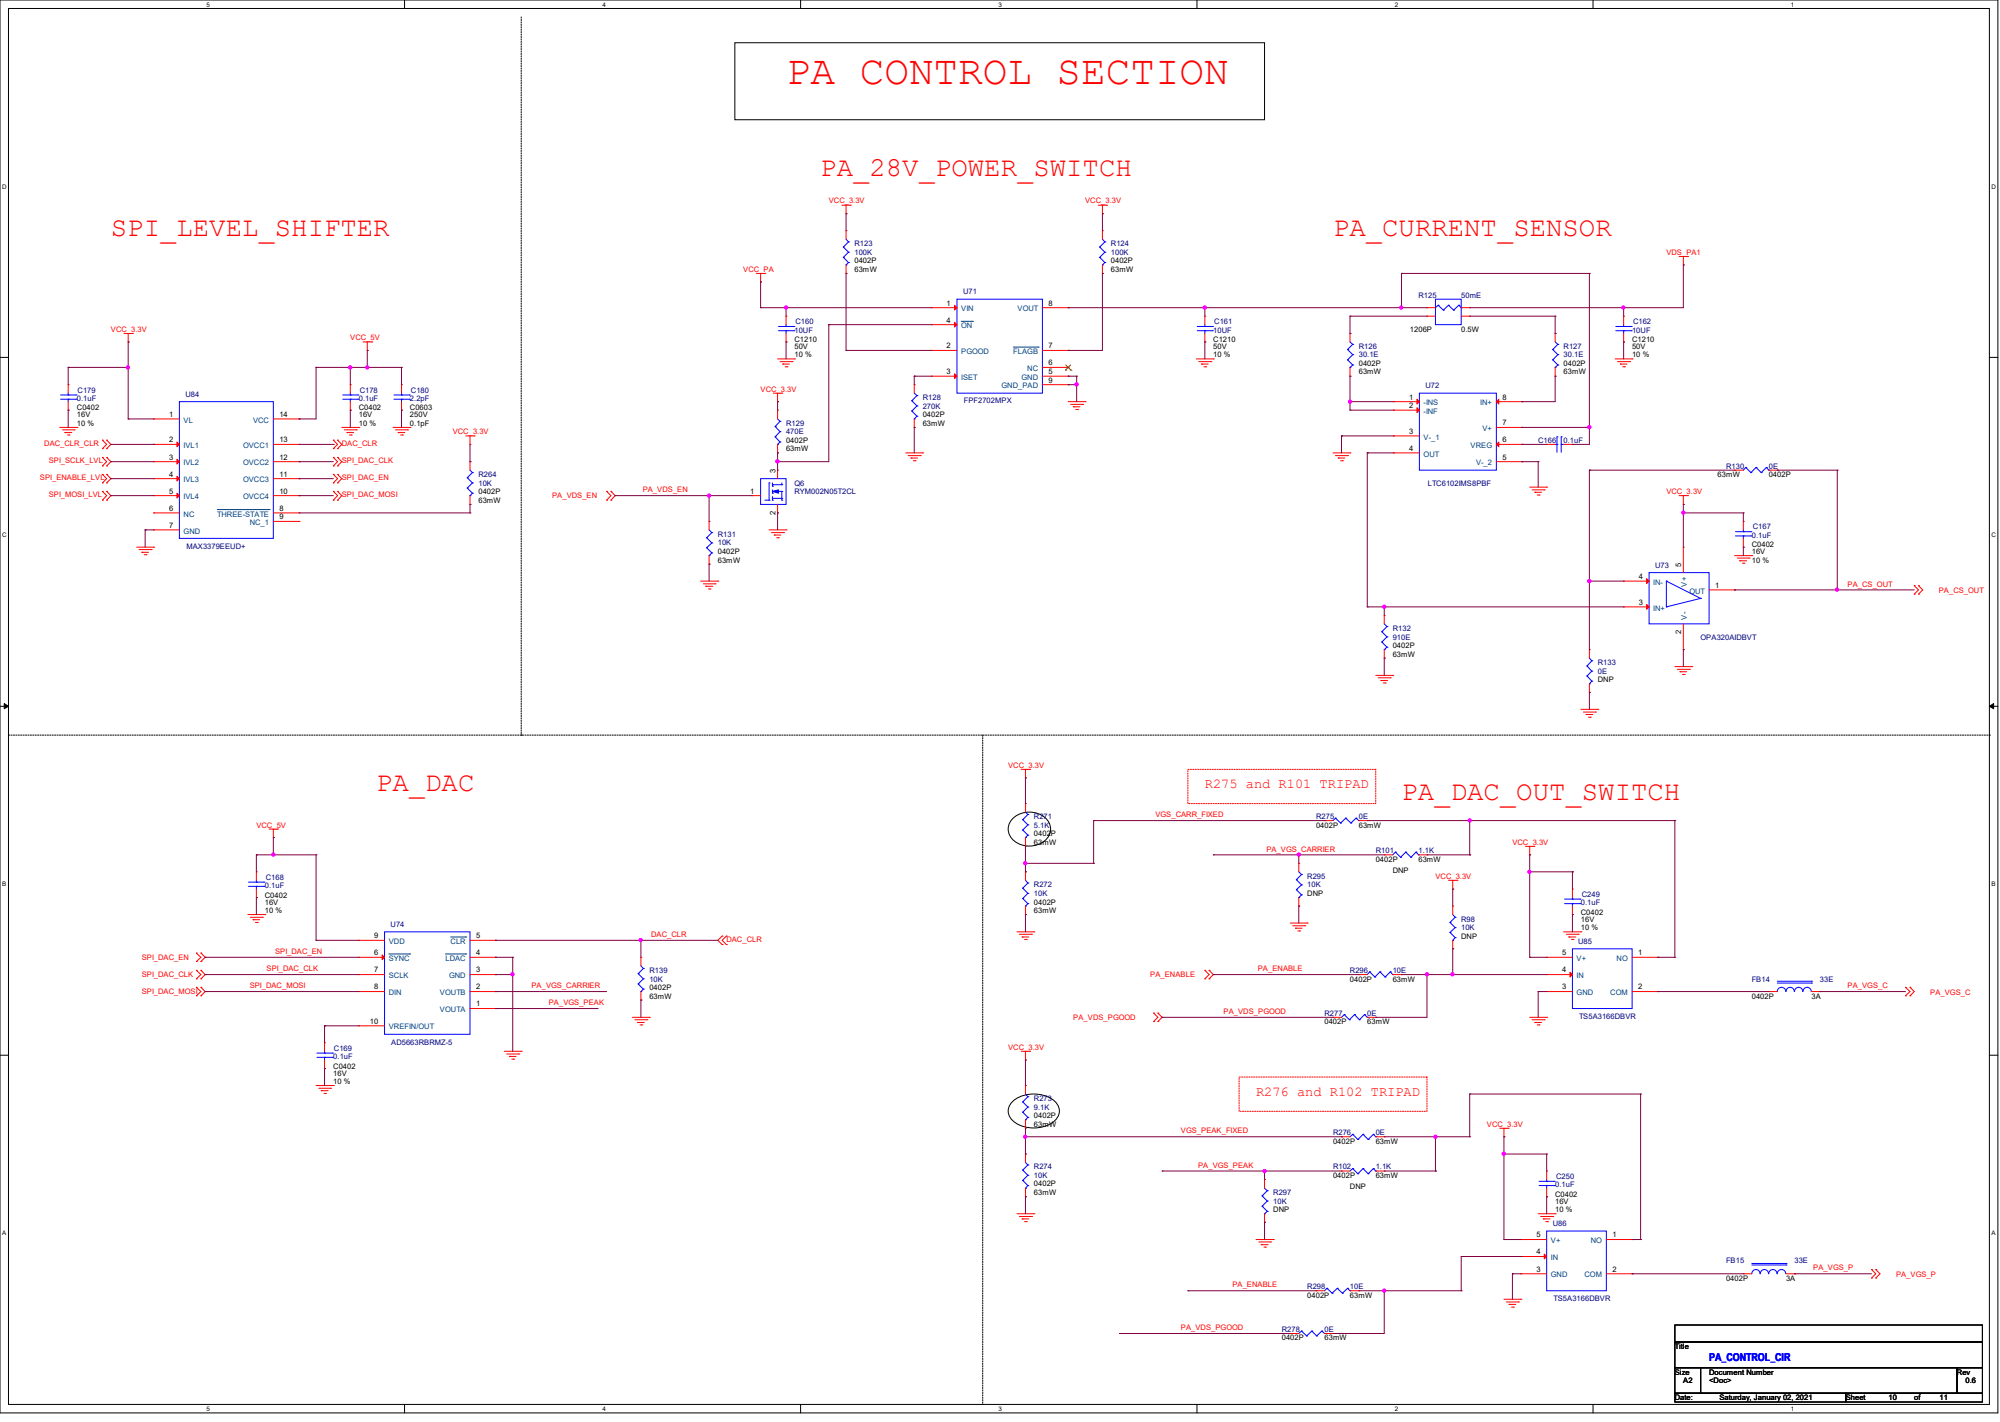
[picture p87: page 10]

# FEMA_BOARD_BOARD_CONNECTOR

TRI pad Options;

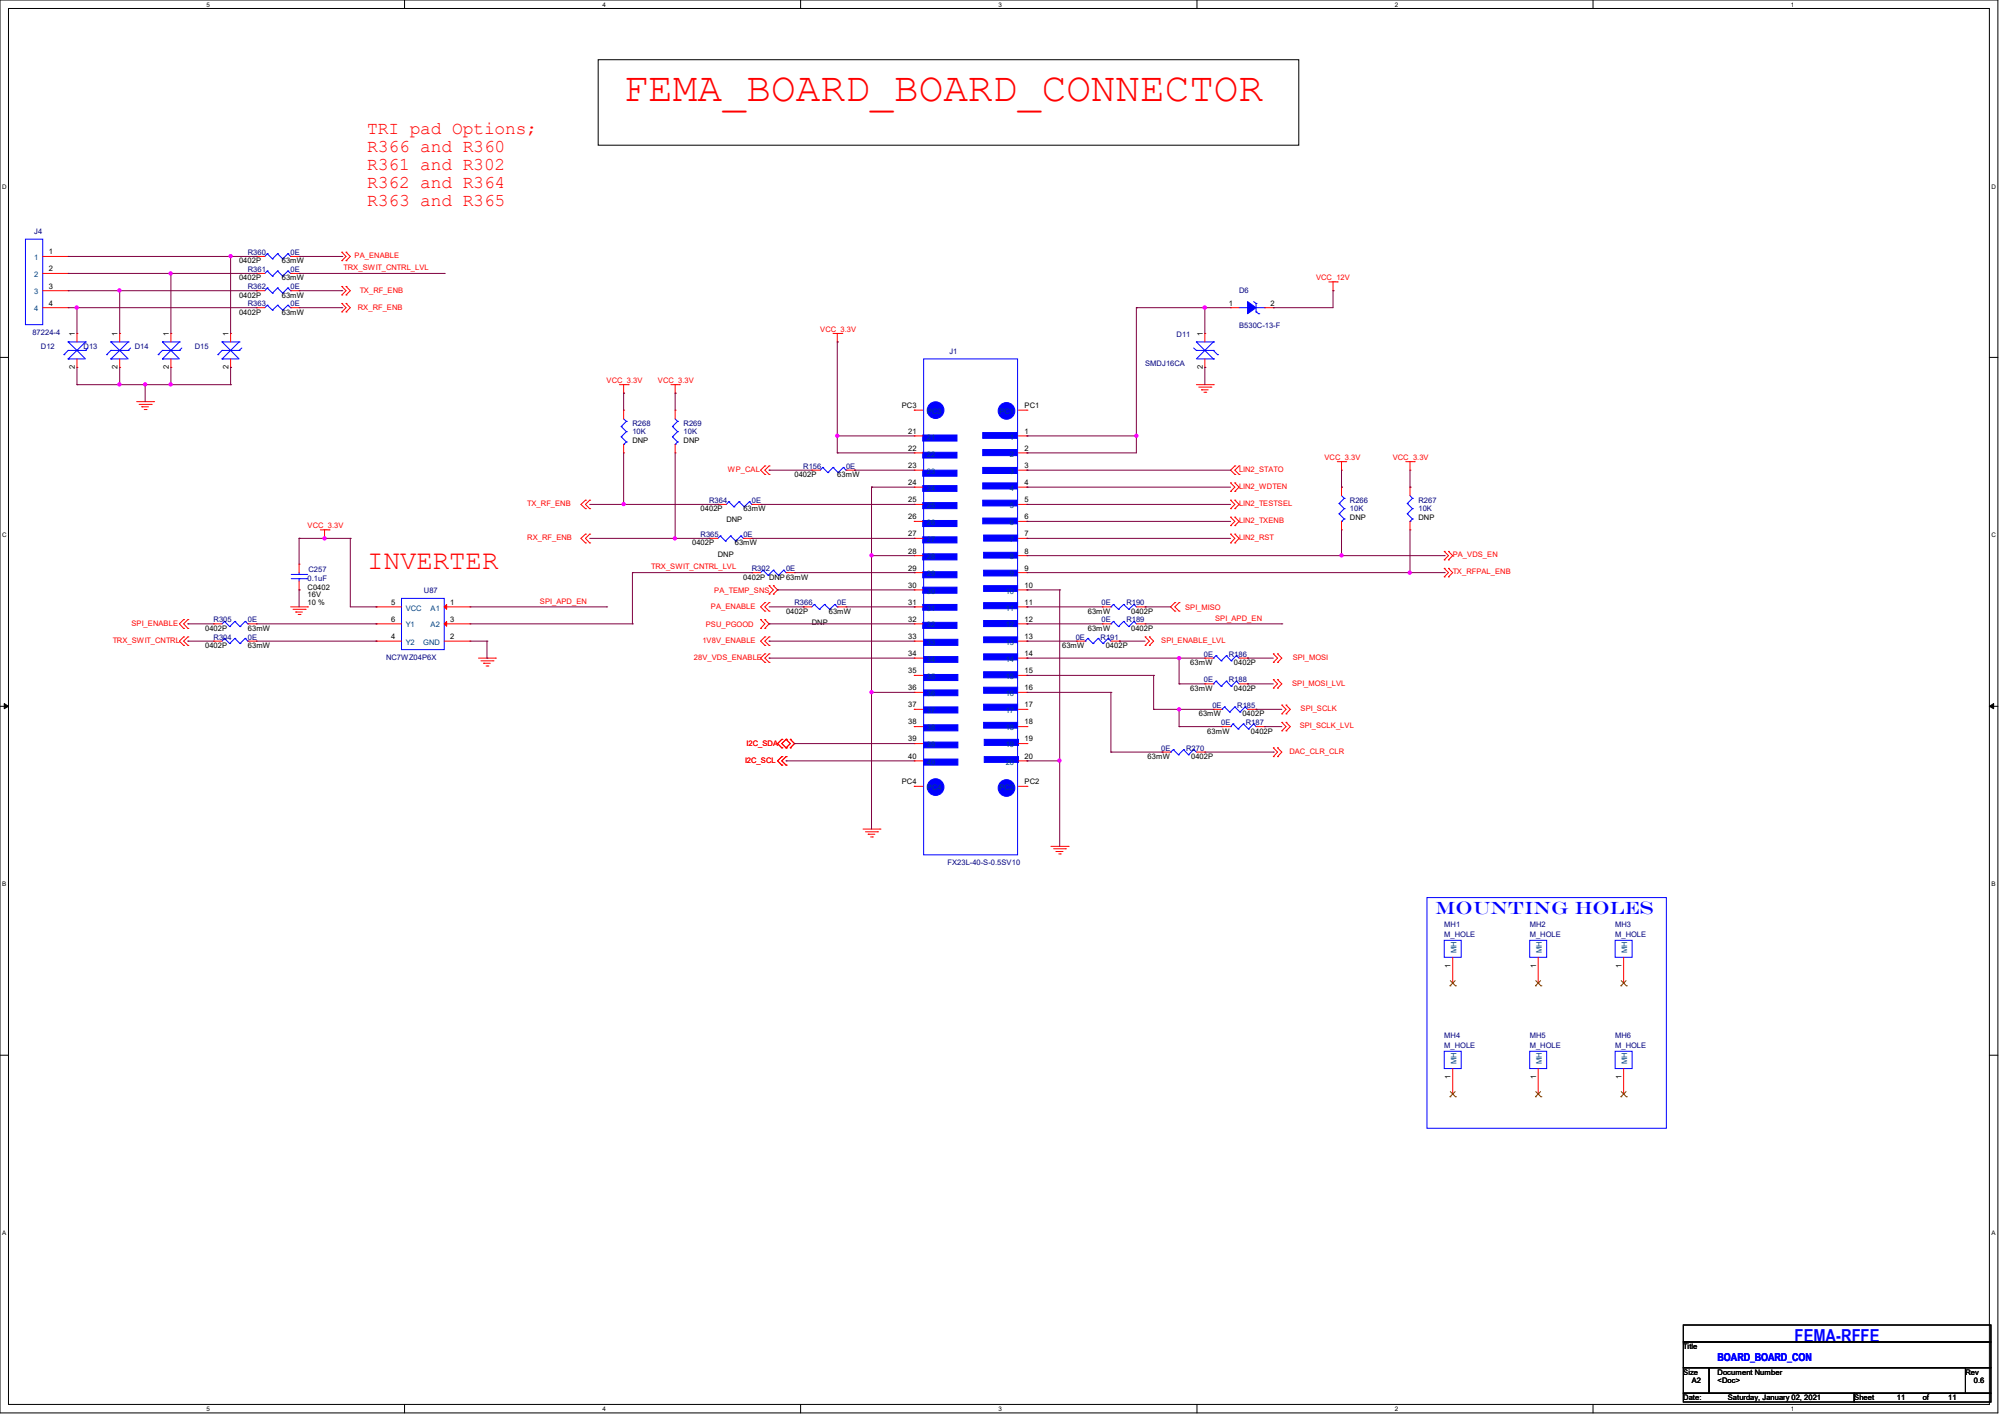
[picture p88: page 11]
