ukama/ukama-nodes/products/units/amplifier/artworks/bottom_cover_amplifier_node.pdf

1

2

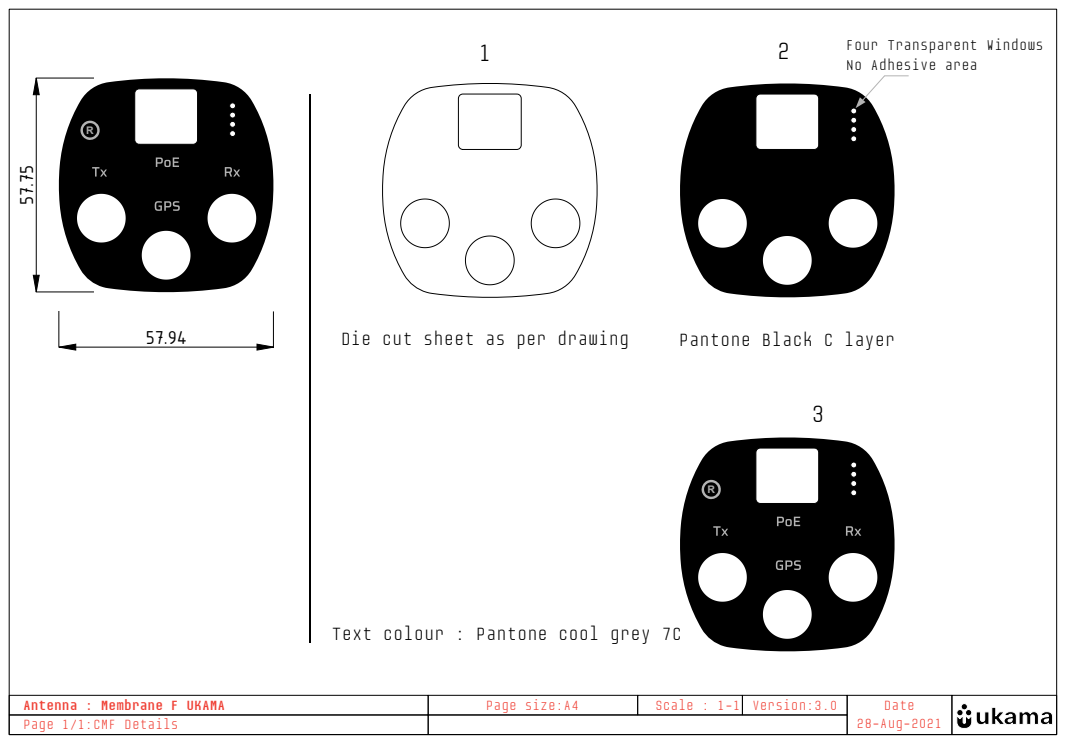
[picture p89: page 1]
Scale : 1-1; Page size:A4; Version:3.0; 28-Aug-2021; Antenna : Membrane F UKAMA; Date ⁵⁷.75

Four Transparent Windows
No Adhesive area

Die cut sheet as per drawing

Pantone Black C layer

Text colour : Pantone cool grey 7C

Page 1/1:CMF Details
