ukama/ukama-nodes/products/nodes/tower/artworks/membrane_tower_node.pdf

## Die cut as per drawing

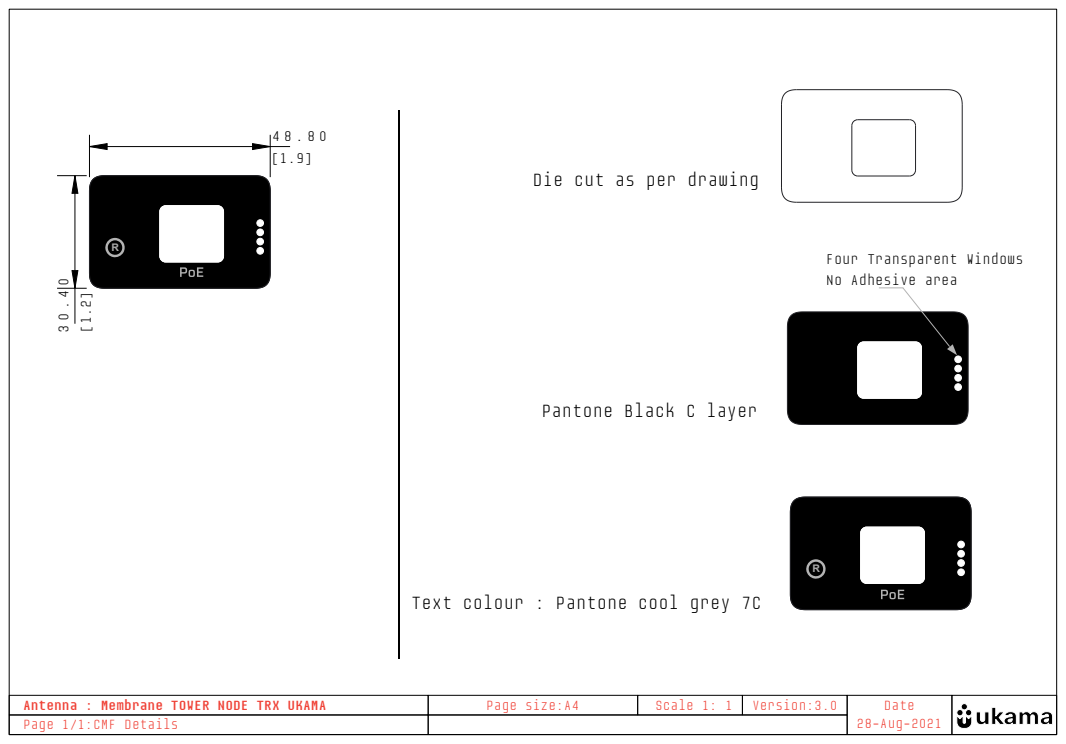
[picture p90: page 1]
Scale 1: 1; Antenna : Membrane TOWER NODE TRX UKAMA; Page size:A4; Version:3.0; 28-Aug-2021; Date

Four Transparent Windows
No Adhesive area

Pantone Black C layer

Text colour : Pantone cool grey 7C

Page 1/1:CMF Details
