ukama/ukama-nodes/electronics/mini_trx/stencil/mini_trx_pmt.pdf

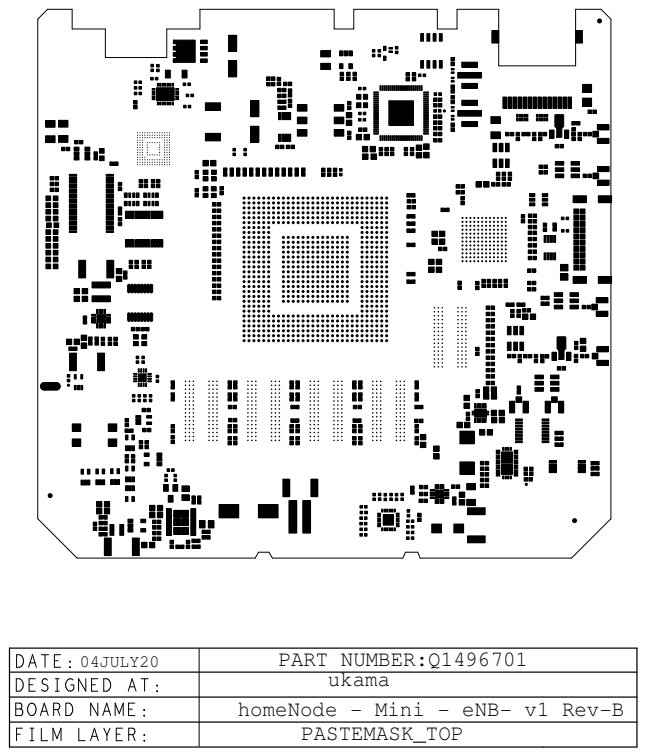
[picture p98: page 1]
04JULY20

PART NUMBER:Q1496701
ukama

homeNode - Mini - eNB- v1 Rev-B

PASTEMASK_TOP
