ukama/ukama-nodes/electronics/mask/assembly/mask_asb.pdf

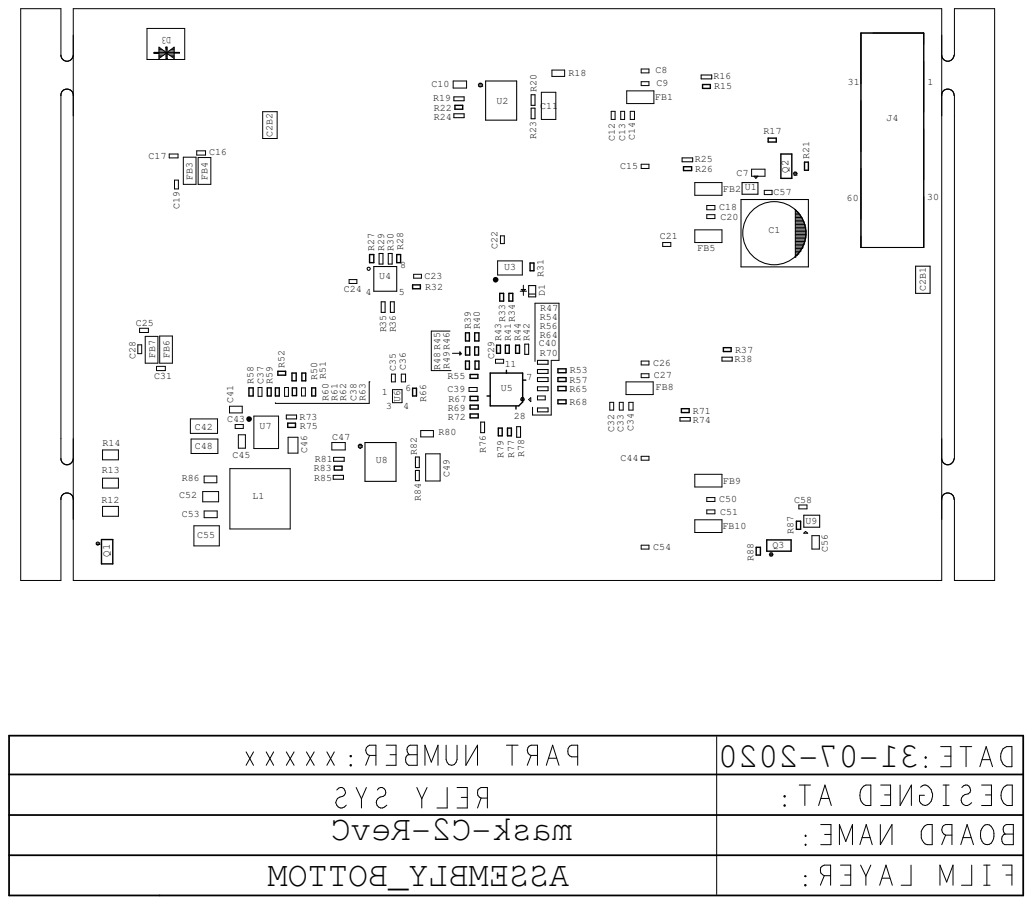
[picture p99: page 1]
