ukama/ukama-nodes/electronics/mask/placement/mask_placement_bot.pdf

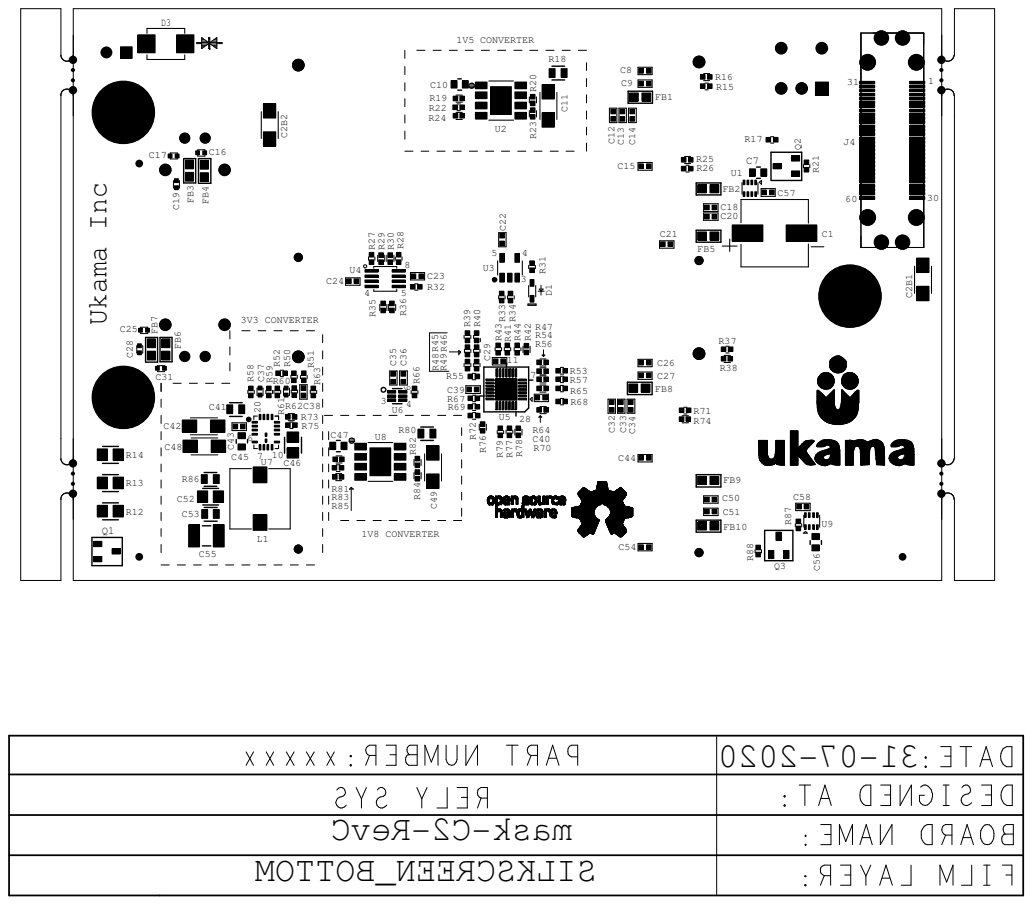
[picture p100: page 1]
