ukama/ukama-nodes/electronics/mask/stencil/mask_stencil_pmb.pdf

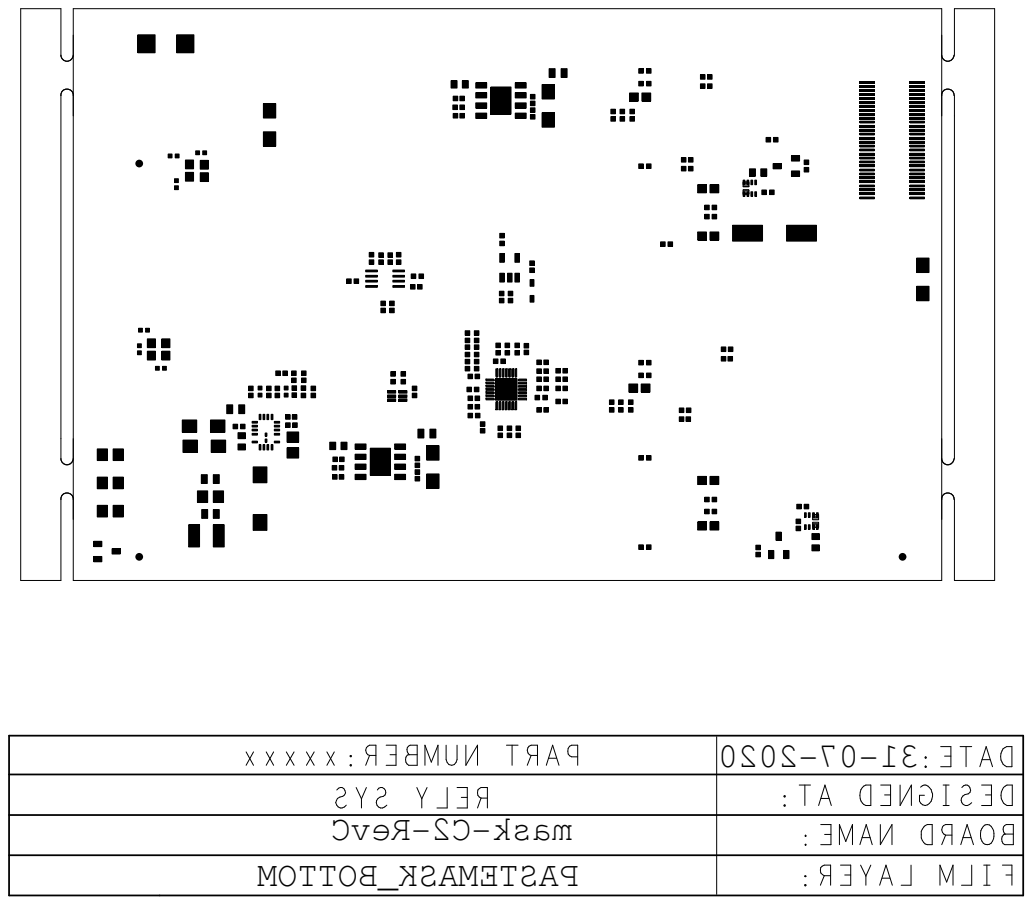
[picture p101: page 1]
mask-C2-RevC; PASTEMASK_BOTTOM
