ukama/ukama-nodes/electronics/mask/stencil/mask_stencil_pmt.pdf

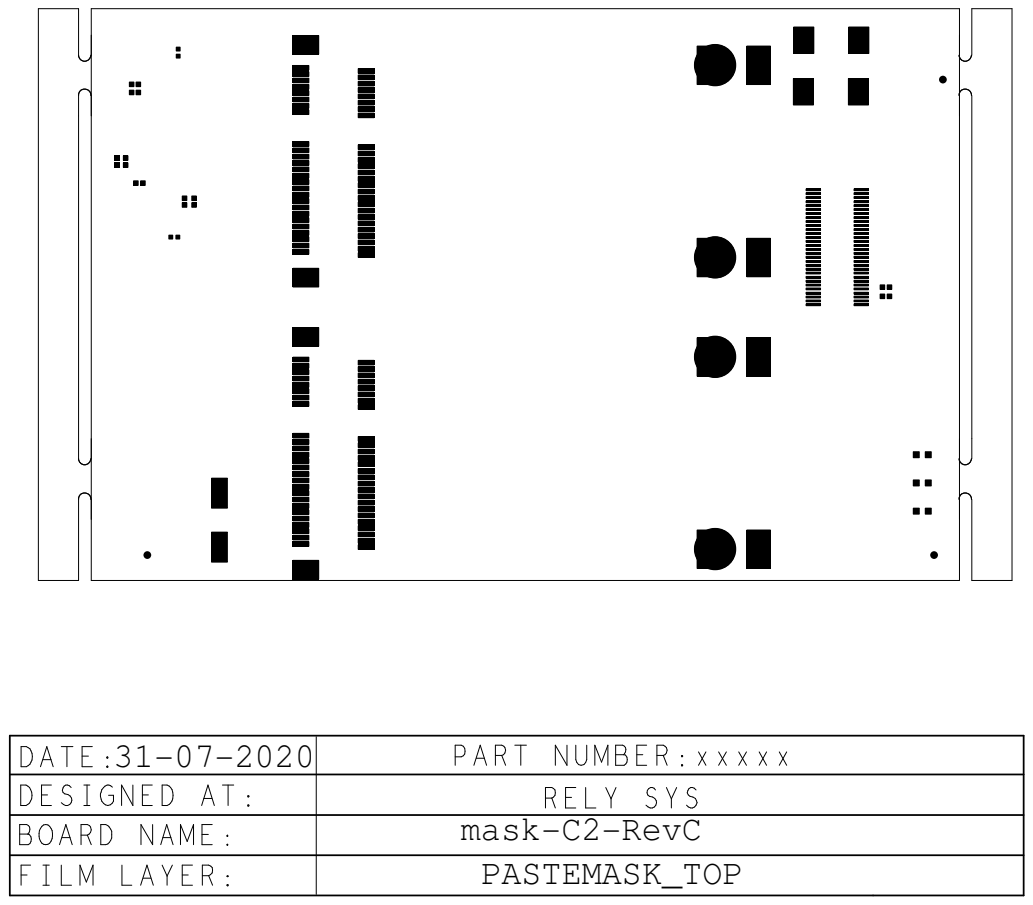
[picture p102: page 1]
mask-C2-RevC

mask-C2-RevC
PASTEMASK_TOP
