ukama/ukama-nodes/electronics/com/assembly/com_asb.pdf

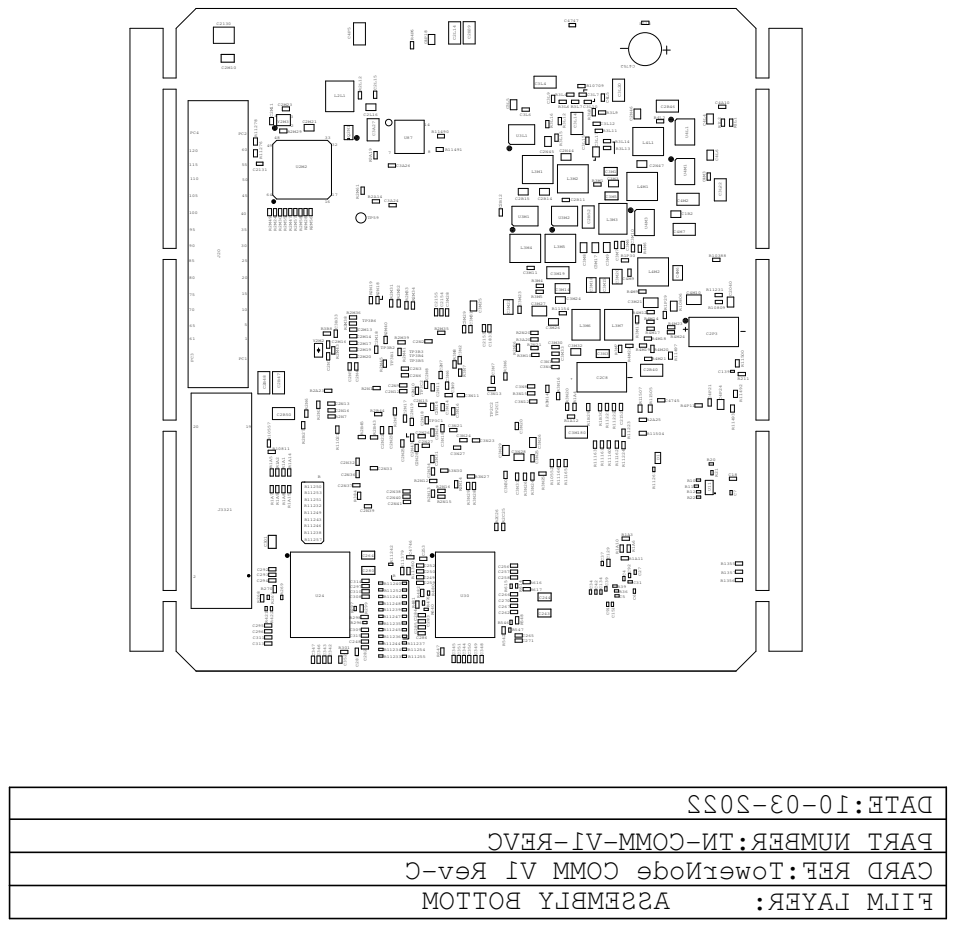
[picture p103: page 1]
