ukama/ukama-nodes/electronics/com/assembly/com_ast.pdf

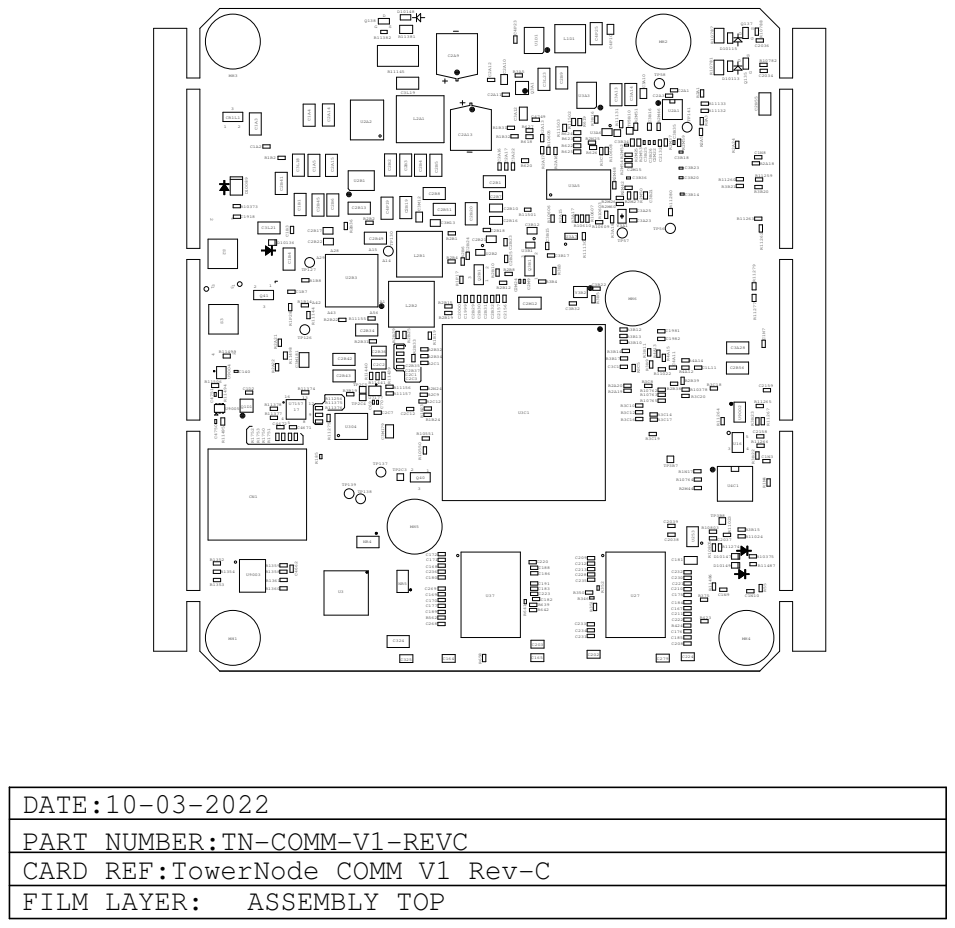
[picture p104: page 1]

DATE:10-03-2022
PART NUMBER:TN-COMM-V1-REVC
CARD REF:TowerNode COMM V1 Rev-C
FILM LAYER:
