ukama/ukama-nodes/electronics/com/placement/com_placement_bot.pdf

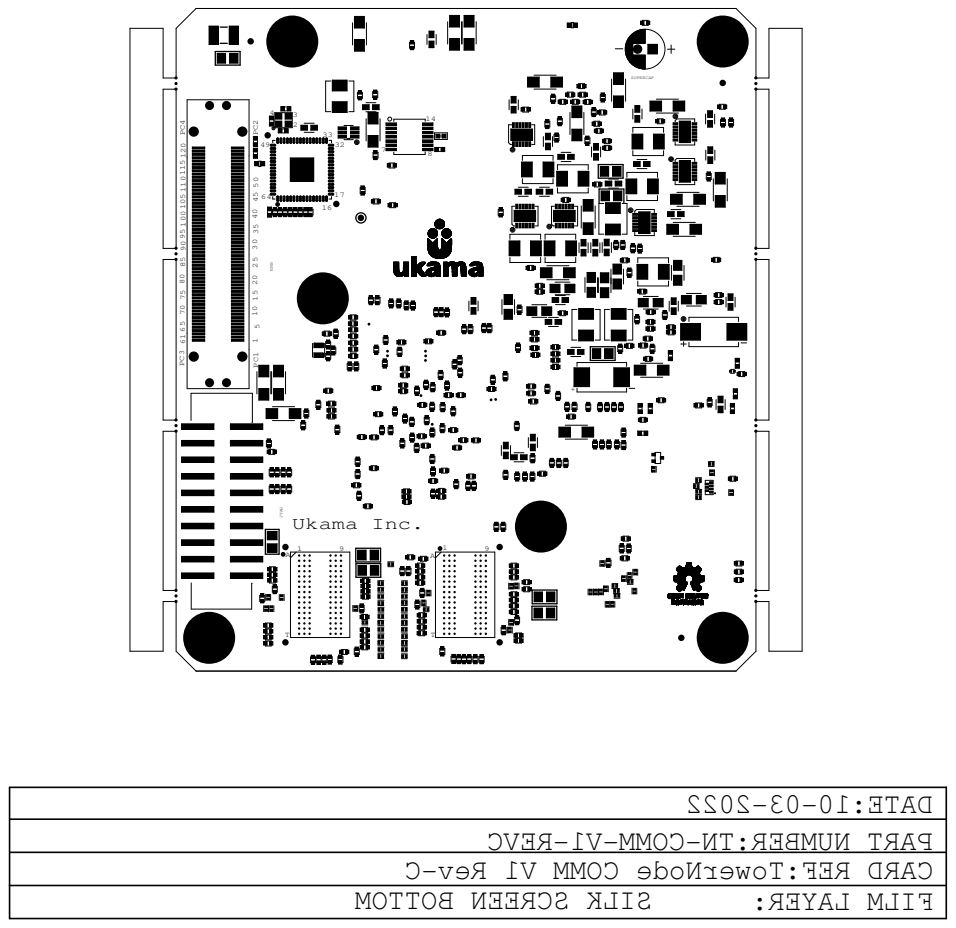
[picture p105: page 1]
ENB; JTAG; Ukama Inc.; SUPERCAP
