ukama/ukama-nodes/electronics/com/stencil/com_pmb.pdf

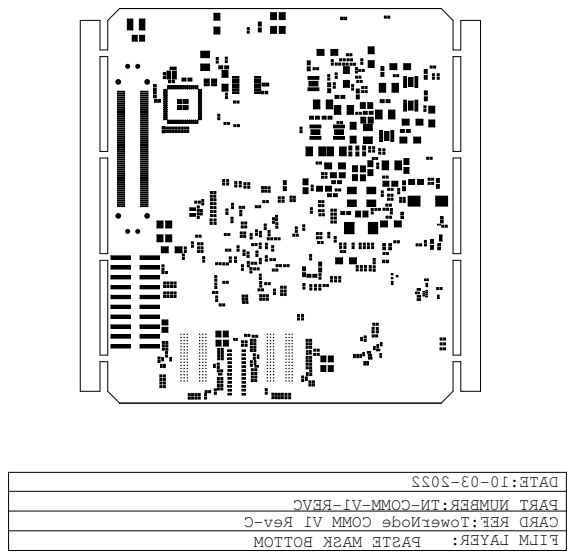
[picture p106: page 1]
FILM LAYER:; DATE:10-03-2022

PART NUMBER:TN-COMM-V1-REVC

CARD REF:TowerNode COMM V1 Rev-C

PASTE MASK BOTTOM
