ukama/ukama-nodes/electronics/trx/assembly/trx_asb.pdf

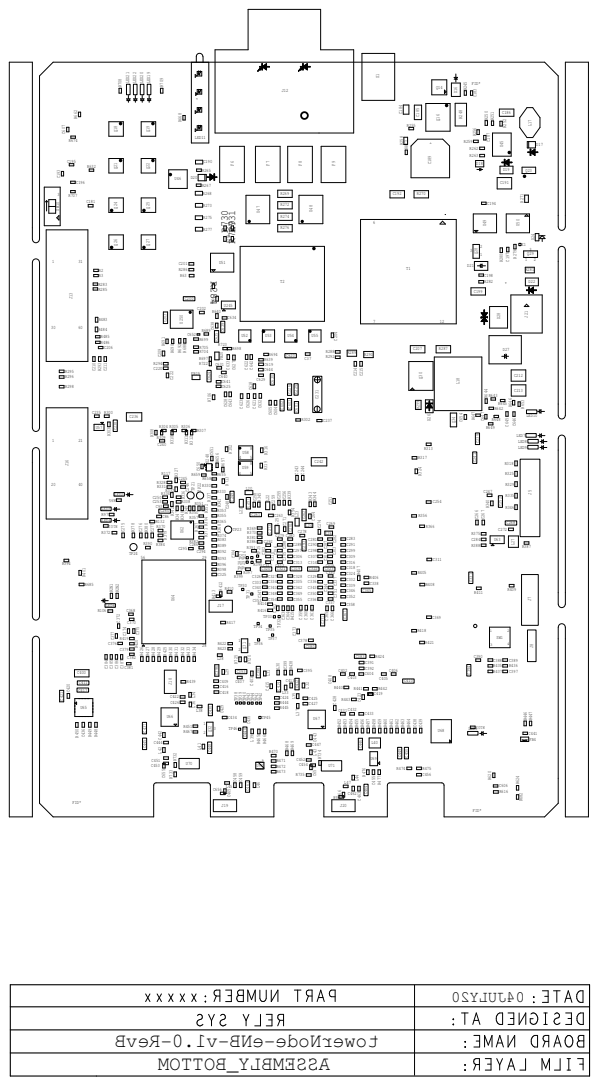
[picture p107: page 1]
