ukama/ukama-nodes/electronics/trx/stencil/trx_pmb.pdf

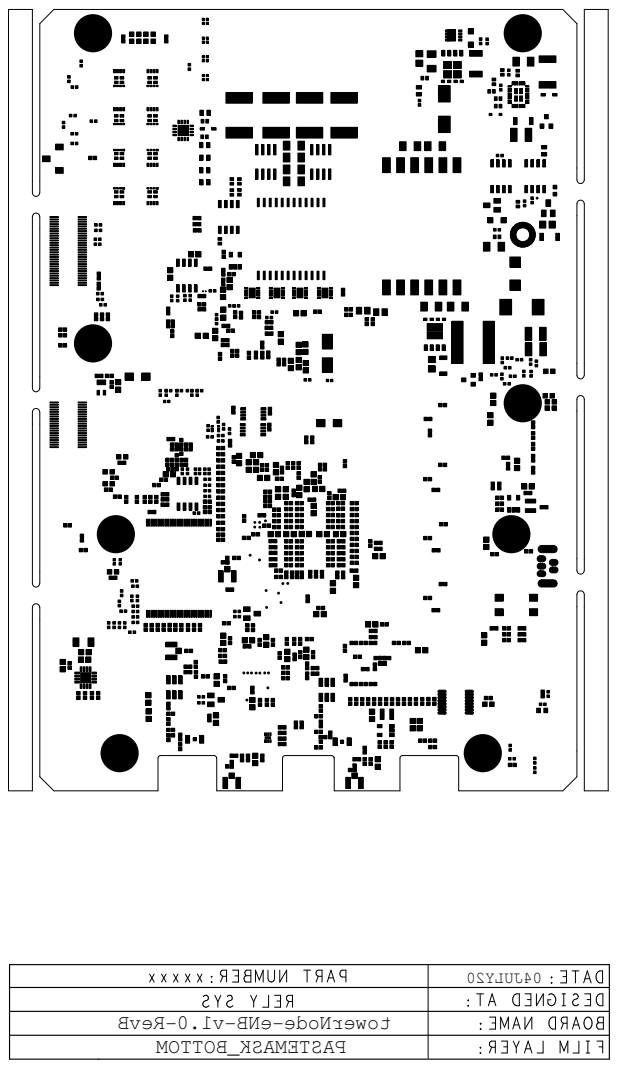
[picture p108: page 1]
04JULY20; PASTEMASK_BOTTOM

towerNode-eNB-v1.0-RevB
