ukama/ukama-nodes/electronics/trx/stencil/trx_pmt.pdf

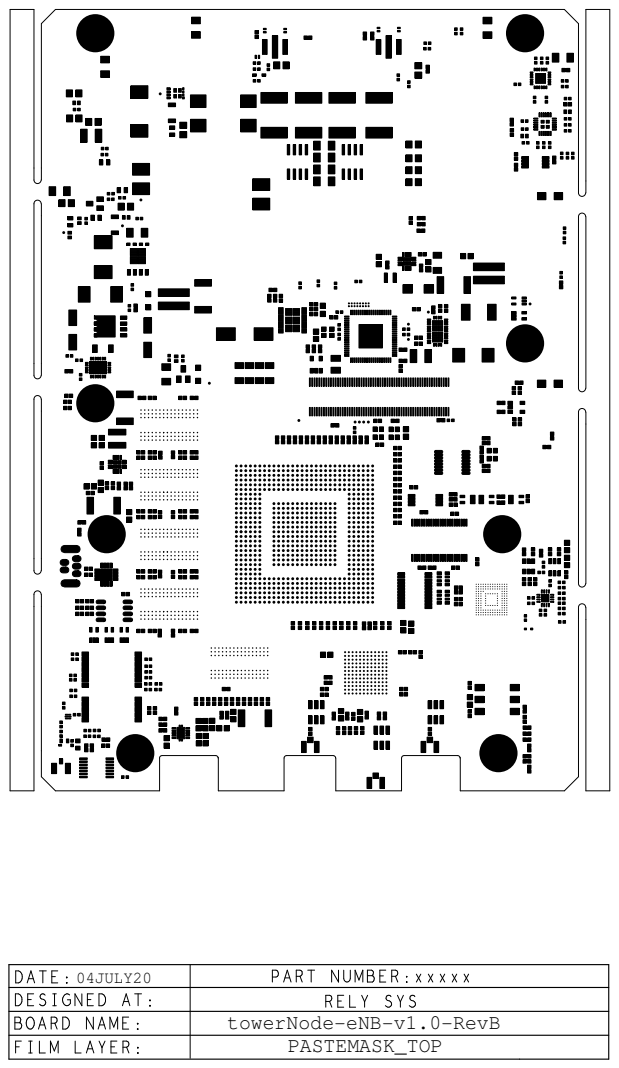
[picture p109: page 1]
04JULY20

towerNode-eNB-v1.0-RevB

PASTEMASK_TOP
