ukama/ukama-nodes/mechanics/nodes/tower/heatsinks/spreader_1.pdf

8 | 7 | 6 | 5 | 4 | 3 | 2 | 1

E

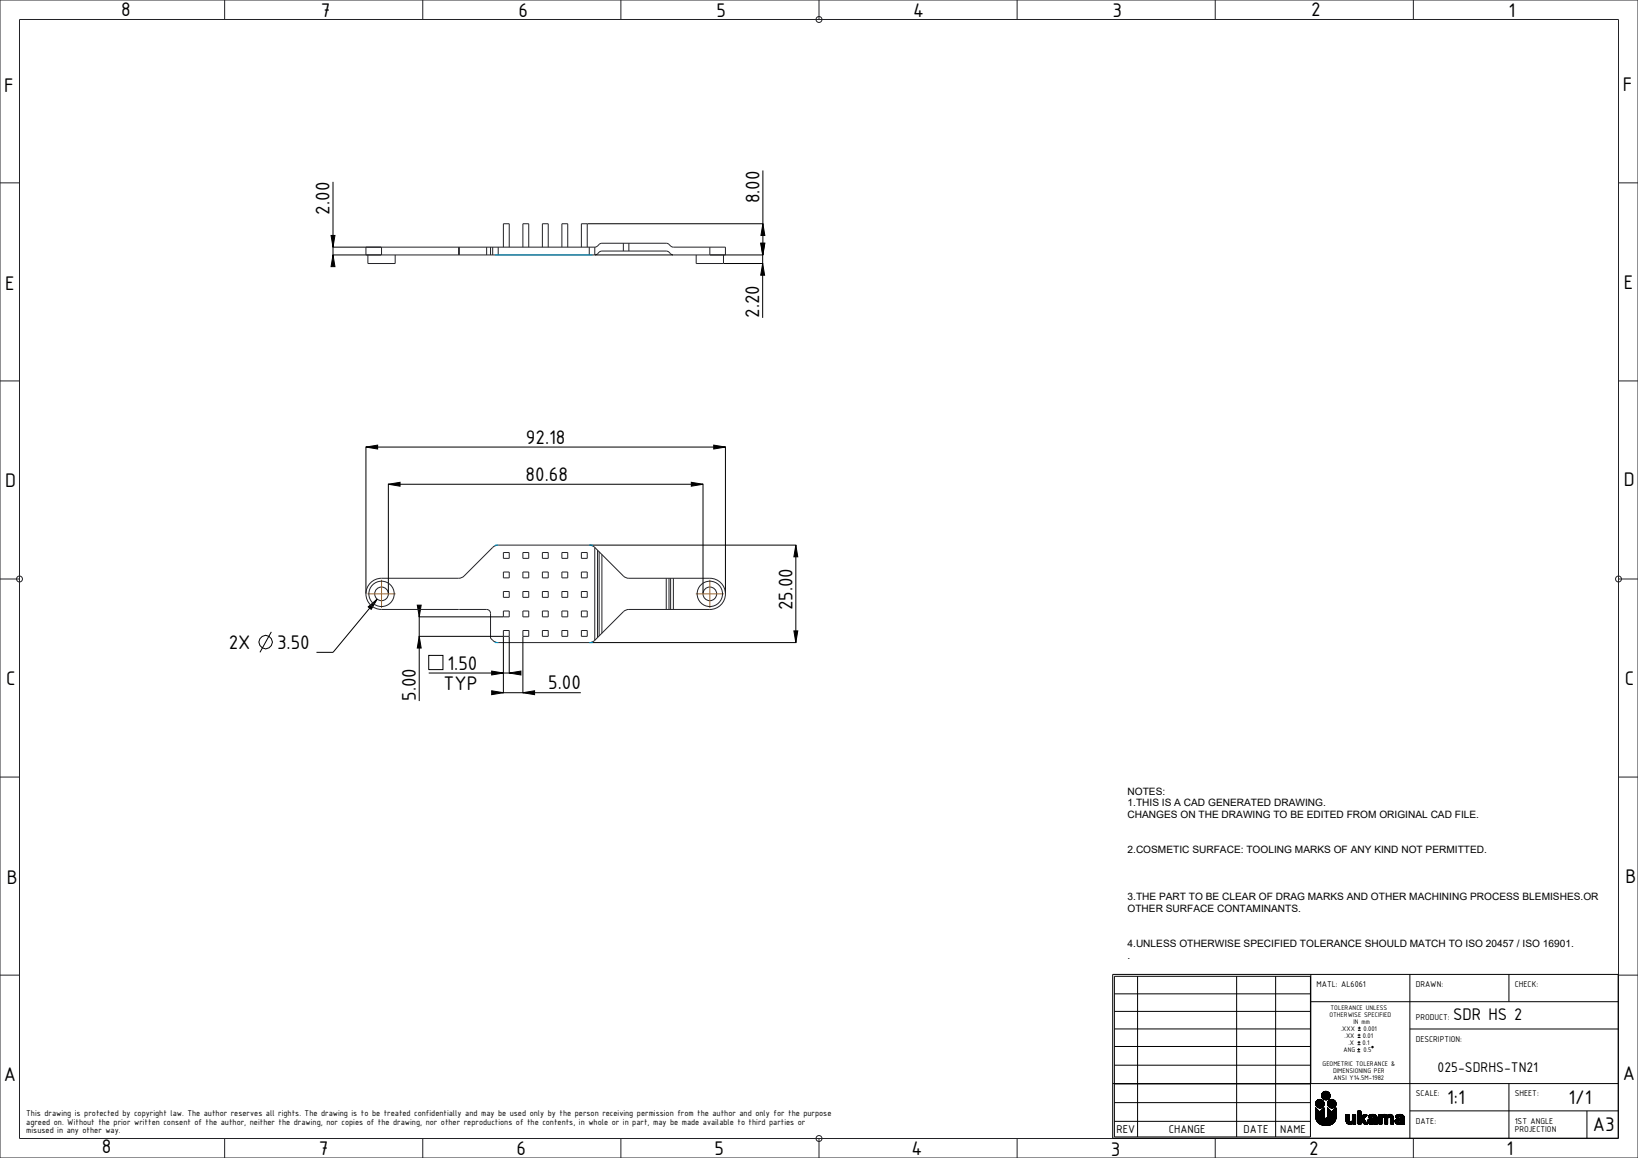
[picture p110: page 1]
025-SDRHS-TN21; TYP; MATL: AL6061; DRAWN:; CHECK:; .XX 0.01 .X 0.1 ANG 0.5; GEOMETRIC TOLERANCE & DIMENSIONING PER; ANSI Y14.5M-1982; DESCRIPTION:; SCALE:; SHEET:; DATE:; 1ST ANGLE; REV; CHANGE; DATE NAME; PROJECTION

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

2.COSMETIC SURFACE: TOOLING MARKS OF ANY KIND NOT PERMITTED.

3.THE PART TO BE CLEAR OF DRAG MARKS AND OTHER MACHINING PROCESS BLEMISHES.OR
OTHER SURFACE CONTAMINANTS.

4.UNLESS OTHERWISE SPECIFIED TOLERANCE SHOULD MATCH TO ISO 20457 / ISO 16901.

TOLERANCE UNLESS
OTHERWISE SPECIFIED IN mm .XXX 0.001

PRODUCT: SDR HS 2

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
