ukama/ukama-nodes/products/units/amplifier/artworks/IO_connector_label_amplifier_node.pdf

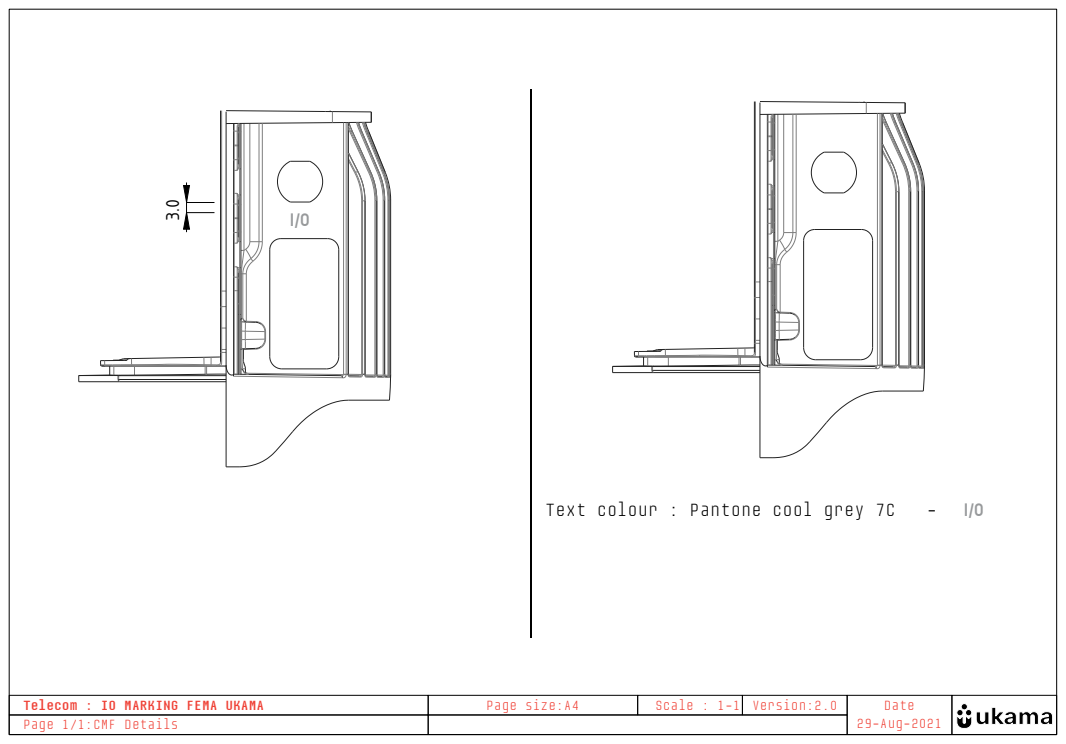
[picture p111: page 1]
Scale : 1-1; Telecom : IO MARKING FEMA UKAMA; Page size:A4; Version:2.0; 29-Aug-2021; Date; Text colour : Pantone cool grey 7C

Page 1/1:CMF Details
