ukama/ukama-nodes/products/nodes/tower/artworks/bottom_cover_tower_node.pdf

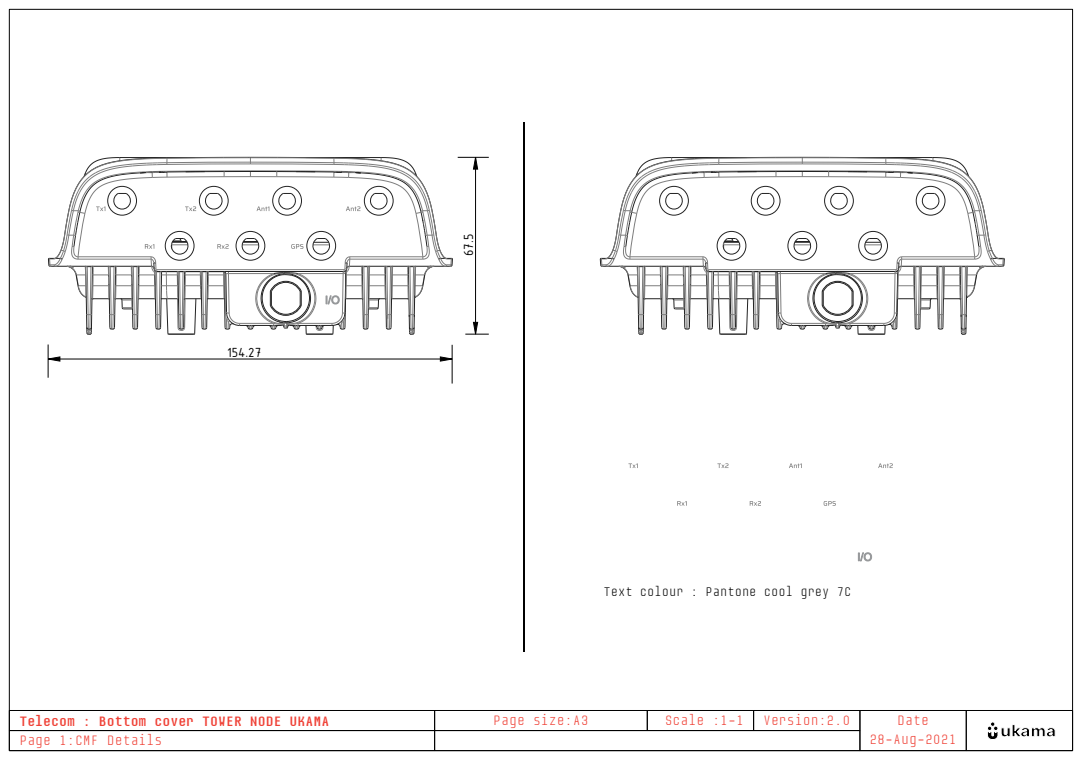
[picture p112: page 1]
Scale :1-1; Date 28-Aug-2021; Telecom : Bottom cover TOWER NODE UKAMA; Page size:A3; Version:2.0

Text colour : Pantone cool grey 7C

Page 1:CMF Details
